qurihara/ai-fue/related_work_survey/NOVELTY_RECHECK.md

# 残った新規性の再点検　絞りすぎていないかを1件ずつ確かめる

2026年8月8日。栗原さんの指摘「サーベイにより残った新規性を絞りすぎているように見える。
論文がいびつになっている」を受けて、縮小をもたらした関連研究を1件ずつ再点検した。

## 結論を先に

**譲歩そのものは、6件中5件が正しい。撤回すべき譲歩は無い。**
一次資料に当たった判断はどれも妥当であり、ここを取り戻そうとすると論文が嘘になる。

**しかし、絞りすぎは確かに起きている。原因は譲歩の中身ではなく、譲歩の書き方である。**
3つの型に分かれ、**いちばん重いのは事実が古くなっていることである。**

| 型 | 何が起きたか | 重さ |
| --- | --- | --- |
| **1. 事実が古い** | スプール49本・128ビットの復号は2026年8月6日に**実機で通っている**のに、論文は「未実施」「設計上の値」と書き、表1の実証容量を**約13.8ビット**のままにしている | **最大** |
| **2. 自己反駁の持ち込み** | サーベイが自分の誤りを正した文を、そのまま論文の地の文にした。論文が主張していないことを論文自身が否定している | 大 |
| **3. 圧縮で生き残った主張だけが落ちた** | 投稿版を6ページに削る過程で、未反証の差分が3つ消え、自己反駁は太字で残った | 大 |

型2と型3が重なった結果、**投稿版は「我々は劣っている」とは書くが「ここは誰も埋めていない」
とは書かない文書になっている。** これが栗原さんの感じたいびつさの正体である。

---

## 第1部　縮小をもたらした関連研究を1件ずつ

### 1. AirCode / InfraredTags　（隠しながら読めること）

**元の主張**　隠蔽と可読性の両立は光学符号には原理的に得られない。

**一次資料の事実**　AirCodeは表面下1〜3mmの空気ポケット、InfraredTagsは厚さ1.08〜1.32mmの
殻の内側に符号を埋め、**どちらも外部に開口をいっさい持たない。** InfraredTagsは単一フレーム
から6〜14ミリ秒で復号し、最大250cmから読める。

**譲歩は正しいか　正しい。** 原理的不可能性の主張は成立しない。外部への露出という点では
窓と吸込口を要する本手法のほうが多く、読み出しの速さでも負ける。

**改めるべき主張**　「外観に符号が現れない」ではなく
**「符号の担い手が形状であるため、担体の材料と色を選ばない」。**
AirCodeは均質で半透明な材料を要求し、論文自身が熱溶解積層方式では均質にならず不透明な
塗装では失敗すると認めている。InfraredTagsは特定の黒い赤外透過フィラメントで**物体全体**を
印刷することを要求し、他の色は今後の課題、スプールごとの再較正まで勧めている。
**これは反証されない、はっきりした差である。**

**いま論文はどうなっているか　ここが型2の典型である。** 投稿版は
「**隠しながら読めること自体は既に実現されている**」を太字で書き、続けて
「外部への露出という点では本手法のほうが多い」と自分を下げている。
ところが**論文は原理的不可能性をどこにも主張していない。** 主張していないことを
否定するために、6ページのうちの数行を使っている。しかも交換で得られるはずの
「任意の家庭用フィラメントで作れる」は投稿版から**落ちている**（長尺版には有る）。

---

### 2. Smith と Senturia（1995）　（基準体による共通モード除去）

**元の主張**　既知の基準体を同居させて比で読む構成に前例がない。

**一次資料の事実**　検出用と基準用の2つの共鳴器を置いて比を取る構成を、
自分たちの新規性としてではなく前提となる **"conventional sensing setup"** として
記述している。2014年に表面弾性波共鳴器での実装例、2021年と2022年の総説でも既知の手法。

**譲歩は正しいか　正しい。** 一般的な形で「前例がない」とは書けない。

**改めるべき主張**　サーベイ自身が「否定されなかった点」を3つ挙げている。そのうち
**論文がまだ使っていないものが1つある。**
基準笛は**読み手に絶対音感を要求せず、復号に使う楽器が特定の調律である必要もなくす。**
センサの文献に対応物は無い（センサを耳で読む人間はいない）。
すなわち残る差分は「比を取ること」ではなく、**比を取ることが人間の読み出しを成立させる**
という一点である。

**いま論文はどうなっているか**　貢献の第三として「構成を受動的な共鳴管と離散符号の復号へ
移した」とだけ書いている。**移植は貢献として弱い。** 上の言い方に替えると、
第2と第3の経路（楽器・コーム）の存在理由と直結する。

---

### 3. DNA-of-things（Koch ら 2020）　（容量と日用品への偽装）

**一次資料の事実**　老眼鏡のアクリルレンズに1.4MB（約1120万ビット）を電源も電子部品も
なしに埋め、**著者自身が抄録で "to hide data in everyday objects (steganography)" と
書いている。**

**譲歩は正しいか　正しい。しかもこれが最も重い。** 容量という土俵では主張は残らない。

**改めるべき主張**　読み出しの経済がまったく違う。DNA-of-thingsの読み出しは
**物体から小片を切り出す破壊的な操作**を要し、次世代シーケンサと分子生物学の工程を要し、
一度読めばその部分は失われる。したがって
**「開けずに、専門の設備なしで、持ち主自身がその場で、繰り返し読み出せる」という条件を
保ったまま到達できる容量の上限**という形なら、どの反例とも矛盾しない。

**いま論文はどうなっているか　型3である。** この枠は長尺版にはあるが、
**投稿版からは完全に落ちている。** 落ちた結果、表1で本研究は
「容量が小さい方式」としてだけ並ぶことになった。

---

### 4. Whoosh の FluteCase（2016）　（半音格子の受動多管構造）

**一次資料の事実**　管長を $L = 14.956 \times 2^{i/12}$ と定め、
「8本の管は8つの異なる周波数で共鳴するよう設計されており、これにより特定の領域への
吹奏を見分けられる」と同じ節に書いている。**semitone という語は無いが、概念はある。**

**譲歩は正しいか　正しい。** 「半音格子で受動的な多管構造を作る」こと自体は先行例がある。

**改めるべき主張**　残るのは格子そのものではなく**格子の使い方**である。
第一に**情報の向き**。Whooshの管長は論文中の公開定数で、すべての複製が同一形状である。
情報は形状ではなく「どの穴を吹いたか」という利用者の選択に載る。
CipherFluteは格子上のどの位置に管を置くかが個体ごとに違い、**その違いが値である。**
第二に**読み方**。FluteCaseはメル周波数ケプストラム係数とサポートベクターマシンによる
利用者ごとの指紋照合であって音の高さを推定せず、**事前に知らない管長は読めない。**
CipherFluteは絶対的な音高を推定して格子上に量子化するので、**事前に知らない値を読める。**

**いま論文はどうなっているか**　2章で差分としては書けている。**ただし貢献には入っていない。**
「事前に知らない値を読める」は未反証の差分であり、貢献に上げてよい。

---

### 5. Lamello / Acoustic Barcodes　（離散周波数を字母とする符号化）

**一次資料の事実**　Lamelloは離散した基本周波数の集合をド・ブラン列の字母として扱う。
ただし格子は等差であり（本文が "linearly increasing tine lengths"、隣接間隔は306.6〜549.5
セントへ単調に広がる）、考察で「最適な周波数の配り方は今後の課題」と明言している。
Acoustic Barcodesは誤り訂正を実装しているが、実効データ量は12ビットにとどまる。

**譲歩は正しいか　正しい。** 記号の列を符号語として扱う設計自体には先行例がある。

**改めるべき主張**　Lamelloのド・ブラン列は**位置と向きを決めるためのもの**であって、
外部から与えた値を運ぶものではない。したがって
**「受動的な音響タグに、外部から与えた任意の値を、誤り訂正符号語として載せた例は、
今回調べた範囲では見当たらない」**は残る。

**いま論文はどうなっているか　型3である。** 長尺版の2.2節末尾にはあるが、
**投稿版からは落ちている。** 表1に「誤り訂正」の欄があるのに、本文がその欄の意味を
語らない状態になっている。

---

### 6. codex32　（機械を要しない復号）

**一次資料の事実**　GF(32)上のBCH符号と、対照表と紙の回転円板により、
Shamirの秘密分散の分割と復元を人手で実行できる。**復号に電子機器をいっさい要しない。**

**譲歩は正しいか　正しい。** 「機械が要らない」の徹底度では本研究より上である。

**改めるべき主張**　codex32の担体は**印刷された文字列**であり、日用品への偽装を扱わない。
2軸で置くと空白が見える。

| | 日用品に偽装できる | 符号として見えている |
| --- | --- | --- |
| **機械なしで人が読める** | **CipherFlute（空白）** | codex32、視覚暗号、SeedQRの手読み |
| **機械が必須** | AirCode、InfraredTags、DNA-of-things、Acoustic Barcodes | — |

**いま論文はどうなっているか**　貢献の第一として書けている。**ここは絞りすぎていない。**

---

## 第2部　いちばん重い問題　事実が古い

**論文はこう書いている。**

> 49本を通した復号は未実施であり，表1の128bitは設計上の値である。

**しかし2026年8月6日に、スプール49本・128ビットの復号は実機の録音から通っている。**
cosenseの記録によれば、5通りすべてで `CipherFlute-demo`（16バイト＝128ビット）が復元できた。

- 連結版　訂正0・消失0（設計49本と全一致）
- 2本ずつの組み合わせ4通り　うち2通りは訂正0・消失0、2通りは**1本が鳴らずパリティが訂正**

**したがって表1の実証容量「約13.8ビット」は、いま事実ではない。** 128ビットである。
この1つの数字が、codex32の128ビットやAirCodeの約500ビットと並ぶ表の中で、
本研究を9分の1に見せている。**査読者がまず比べるのはこの列である。**

画像タイルの2-of-9も実機で復号が通っている。

**これは修辞の問題ではなく、原稿が実測に追いついていないという事実の問題である。**
絞りすぎの最大の要因はここにある。

---

## 第3部　復活させるべき主張

未反証でありながら、投稿版に無いか、貢献に上がっていないもの。

1. **符号の担い手が形状なので、担体の材料と色を選ばない。**
   任意の家庭用フィラメントで作れる。AirCodeとInfraredTagsは材料を強く縛る。（投稿版から落ちている）
2. **「開けずに、専門の設備なしで、持ち主自身がその場で、繰り返し読み出せる」条件下での
   容量の上限を押し上げた。**（投稿版から落ちている）
3. **受動的な音響タグに、外部から与えた任意の値を誤り訂正符号語として載せた。**（投稿版から落ちている）
4. **事前に知らない値を読める。**（2章にはあるが貢献に無い）
5. **基準笛により、読み手に絶対音感も、楽器の特定の調律も要らない。**（3.3節にはあるが貢献に無い）

## 第4部　削るべき自己反駁

論文が主張していないことを否定している文。**削っても正直さは1ミリも減らない。**

- 「隠しながら読めること自体は既に実現されている」（太字）
- 「したがって光学的な符号は表面に露出していなければ読めないという主張は成り立たず、
  読み出しの速さでも本手法が優位に立つわけではない」
- 「外部への露出という点では、窓と吸込口を必要とする本手法のほうがむしろ多い」

**関連研究の節は、先行研究が何をしたかと、本研究がどこで違うかを書く場所である。**
自分が過去に考えて捨てた主張の墓碑を建てる場所ではない。

## 第5部　提案する貢献の並び

現状の4点を、未反証の差分だけで組み直す。

1. **読み出しに機械を要しない秘密の記録媒体。** 日用品に偽装できて、なお鍵盤楽器ひとつ、
   あるいは3Dプリントしたコーム1本で人間が読める。この2つを同時に満たすものは
   今回調べた範囲で見当たらなかった。（codex32は後者だけ、AirCodeらは前者だけ）
2. **事前に知らない値を、音の高さの格子から読む。** 先行する多管構造（FluteCase）は
   管長が公開定数で全複製が同一形状であり、情報は形状ではなく利用者の選択に載る。
3. **担体の材料と色を選ばない。** 符号の担い手が形状だからである。
4. **受動的な音響タグに誤り訂正符号語を載せ、実機で128ビットの往復を通した。**
5. どの層が秘密を守り、どの層は守らないのかを明示した。

**5番目は、栗原さんの別の指摘（脅威モデルという枠組みが要るのか）と関わる。**
「脅威モデルを提唱する」のではなく「この性質があるのでこう使えるが、この脅威は
想定しない」と6章で述べる形にすれば、貢献の1つではなく**限界の記述**になる。
そのほうが自然であり、章も1つ減る。

---

# 決定事項（2026年8月9日、栗原さんと1件ずつ確認して確定）

## 確定した貢献は4件

1. **日用品に偽装できて、なお機械を要さず人が読める。** 基準笛により、読み手に絶対音感も、
   復号に使う楽器が特定の調律であることも要らない。codex32は後者だけ、AirCodeらは前者だけ。
2. **事前に知らない値を、音の高さの推定と格子への量子化で読む。**
   FluteCase・Lamello・Blowhole・SoundOffは、いずれも識別先の集合が復号器に既知である。
3. **担体の材料と色を選ばない。** これは工作の都合ではなく**隠し先の自由**である。
   光学方式は担体を「均質で半透明な材料」または「特定の黒い赤外透過フィラメントで
   全体を印刷したもの」に限定するので、木の本立てにも白い枡箱にも仕込めない。
4. **受動音響タグで実効12bitの系譜を超え、実機で128bitを通した。**

**移植の主張も、立場の主張も、原理的不可能性の主張も、1つも残っていない。
すべて実物か一次資料で判定できる能力の主張である。**

## 件ごとの決定

| 件 | 決定 |
| --- | --- |
| 1 AirCode/InfraredTags（可読性） | (2)の軸では差を主張しない。2章の自己反駁の1文を削除する。**1章の文はスコープが限定されていて真なので直さない** |
| 1-b 同（発見のしにくさ） | 「担体の材料と色を選ばずに隠せる」＝隠し先の自由 |
| 1-c 同（読み出しの軸） | 「近接と、吹くという能動的な行為を要する」を新設。ただし透過撮影では読めるので「読めない」とは書かない |
| 2 同（材料） | 主張は維持し、根拠と結びつけて言い切る |
| 3 Smith と Senturia(1995) | **貢献から外す。**よく知られた手法として引用し、淡々と活用する立場で書く |
| 4 AirCode（既知セルの正規化） | 投稿版では触れない。3を貢献から外したので論じる相手がいなくなる |
| 5 DNA-of-things | 容量では主張しない。「開けずに、専門の設備なしで、持ち主自身がその場で、繰り返し読み出せる条件を保った上限」へ |
| 6・7・8 FluteCase / Lamello | **3件まとめて1つの段落に畳む**（下記） |
| 9 Acoustic Barcodes | 実効12bitの系譜を超え、実機で128bitを通した |
| 10・12・13・14 | 既に正しく書けている。変更なし |

## 6・7・8 の確定文

**議論の経過**　当初「先行研究は入力装置であり、物体の側に取り出すべき情報がない」と
書こうとしたが、**これは誤りである。** 栗原さんの指摘のとおり、Lamelloのド・ブラン列は
設計者が計算して歯の長さとして刻んだものであり、並びを変えれば復号結果が変わる。
**形状に情報が載っている。** FluteCaseも、どの管がどの周波数かという対応は幾何に載る。

**差は「情報が載っているか」ではなく、載っている情報の性質にある。**

| | FluteCase・Lamello | CipherFlute |
| --- | --- | --- |
| 何が載っているか | 位置やコマンドを指す**索引** | 運ぶべき**値そのもの** |
| 誰が決めるか | 部品の設計時、**全複製で同一** | 作るとき、**個体ごとに違う** |
| 復号器は知っているか | 対応を**事前に知っている** | **知らない。測って求める** |

情報量の差（実効2bitと128bit）はこの性質から出る。**索引は場所の数だけあれば足りる。**

**確定した文。**

> FluteCase\cite{whoosh} や Lamello\cite{lamello} のように、受動的な音響部品を吹いたり
> 弾いたりして読む先行研究とは物理機構を共有し、**形状に情報を載せる点も共通する**。
> ただしそこに載っているのは**位置やコマンドを指す索引**であり、部品の設計時に決まって
> 全複製で同一で、**復号器はその対応を事前に知っている**。本研究では**載っているのが
> 運ぶべき値そのもの**であって個体ごとに異なり、**読み取り側は事前にそれを知らない**。
> 音の高さを推定して格子上に量子化するので、知らない値が読める。

**副産物**　格子について何も主張しなくなるので、「半音の格子には先行例がある」という
譲歩の文が丸ごと消える。半音を選んだ理由（平均律の楽器が対照表になる）は3.2節に残る。

## この作業で分かった、書き方の原則

**譲歩を書くのではなく、主張しないことで解決する。** 主張しなければ、先行例を挙げて
反論する必要がなくなり、段落ごと消える。紙面も増える。**論文が自分を弱く見せる文は、
たいてい「主張していないことへの反論」である。**

---

# 議論の経緯（2026年8月9日）

**この節は、結論そのものより価値がある。** 同じ作業を将来もう一度やるとき、
**どこで間違えたか**を知っていることが効くからである。以下は時系列である。

## 進め方

栗原さんの指示は「**関連研究を一つずつ挙げ、我々のこの主張はこの関連研究とこのように
被っているので、このような主張にあらためなければいけない、という書式で**」であった。
そして「**サーベイに対する君の結論を疑っているので、一つずつ私とやっていく**」と続いた。

この2つの指示が効いた。**一括で判断していたら、下の誤り3件はどれも見つからなかった。**

## AIが犯した誤りと、栗原さんによる訂正

### 誤り1　「点検」ではなく「追認」をしていた

最初の報告でAIは「サーベイの譲歩は6件中5件が正しい」と要約した。**これは一次資料に
当たり直した点検ではなく、サーベイの結論をそのまま繰り返しただけであった。**
栗原さんに「一つずつやっていく」と言われて初めて、件ごとの検証が始まった。

### 誤り2　投稿版から落ちた主張の診断が不正確だった

AIは「材料と色を選ばないという主張が投稿版から落ちている」と報告した。実際には
**貢献の第二として残っており**、落ちていたのは「任意の家庭用フィラメントで作れる」という
具体の一句だけであった。正しい診断は「**根拠と切り離されたまま8文字で置かれている**」で
ある。数えれば分かることを、確かめずに報告していた。

### 誤り3　過剰な直しを提案した（自分が診断した病を自分でやった）

AIは「1章の問題設定（日用品に隠そうとすると読めなくなる）を、否定されない形に立て直す」
と提案した。**栗原さんはこれを保留した。** 読み直すと、1章の文は主語が
「紙・金属板・二次元コード」に限定されており、**光学符号一般については何も言っていない。
つまりそのままで真である。** 直すべきは2章の「隠しながら読めること自体は既に実現されて
いる」という1文だけであった。

**AIは「主張していないことへの反論を書くな」と診断しておきながら、提案の側で同じことを
していた。** 過剰な自己修正は、指摘したあとにも再発する。

### 誤り4　事実に反する切り分けを書こうとした（これが最も重い）

FluteCaseとLamelloとの差を、AIは当初こう書こうとした。

> 先行研究は入力装置であり、**物体の側に取り出すべき情報がない**。

**栗原さんの反論。** 「FluteCaseやLamelloは、複数の場所に低情報量のデータが埋め込まれて
おり、それを人間が意識的に選択することでデータを識別可能な音として発生させ、マイクが
拾ってデコードする。**情報が積載されているという点では同じ**ではないか」。

**これは正しい。** とくにLamelloのド・ブラン列は、設計者が計算して歯の長さとして刻んだ
ものであり、並びを変えれば復号結果が変わる。**形状に情報が載っているとしか言いようがない。**

差は「情報が載っているか」ではなく、**載っている情報の性質**にある。

| | FluteCase・Lamello | CipherFlute |
| --- | --- | --- |
| 何が載っているか | 位置やコマンドを指す**索引** | 運ぶべき**値そのもの** |
| 誰が決めるか | 部品の設計時、**全複製で同一** | 作るとき、**個体ごとに違う** |
| 復号器は知っているか | 対応を**事前に知っている** | **知らない。測って求める** |

情報量の差（実効2bitと128bit）はこの性質から出る。**索引は場所の数だけあれば足りる。**

## 栗原さんが持ち込んだ枠組み（サーベイには無かったもの）

### 2つの軸を分ける

> (1) 秘密がある場所を見つけやすいか
> (2) 場所を知っているとき、情報が見えるかどうか

**論文はこの2つを混ぜていた。** 分けると、AirCode/InfraredTagsとの関係が正確に書ける。
AIはここに第3の軸（読み出しに要するもの）を足した。InfraredTagsは**最大250cmから
単一フレームで受動的に読める**のに対し、CipherFluteは吹かなければ鳴らない。

| | (1) 場所の見つけにくさ | (2) 見えるか | (3) 読み出しに要するもの |
| --- | --- | --- | --- |
| 紙・二次元コード・金属板 | 低い（金庫が要り、金庫が秘密を告げる） | 見える | 目 |
| AirCode / InfraredTags | 高い。**ただし担体の材料が縛られる** | 見えない | 専用装置。非接触・遠隔・受動 |
| **CipherFlute** | 高い。**担体の材料も色も自由** | 見えない | **吹く行為と近接。装置は不要** |

### 細かすぎる分割を1文に畳む

AIは格子（6）と読み方（7）と符号化の枠組み（8）を別々に論じようとした。
栗原さんの指示は「**細かすぎる。1文で済ませられる**」であった。畳んだ結果、
**格子について何も主張しなくなり、「半音の格子には先行例がある」という譲歩の文が
段落ごと消えた。**

### 「原理は共通」と書いてはならない

栗原さんの草案には「笛による音響情報に**データを埋め込んで**吹くことによる復号を行う
**原理は共通している**」とあった。AIはここを押し戻した。**FluteCaseはデータを埋め込んで
いない**（管長は公開定数で全複製が同一）。共通しているのは
「受動的な多管構造を吹き、生じた音をマイクで読む」という物理機構までである。
**ここを譲ると、我々だけが持っているものを相手に渡すことになる。**

## この作業で得た原則

**譲歩を書くのではなく、主張しないことで解決する。** 主張しなければ、先行例を挙げて
反論する必要がなくなり、段落ごと消えて紙面も増える。基準笛（3・4）でも、格子（6）でも、
符号化の枠組み（8）でも、同じ解き方が効いた。

**論文が自分を弱く見せている文は、たいてい「主張していないことへの反論」である。**

**そして絞りすぎの最大の要因は、修辞ではなく事実が古いことであった。** スプール49本の
128bit復号は2026年8月6日に実機で通っていたのに、原稿は「未実施」「設計上の値」と書き、
表1の実証容量を約13.8bitのままにしていた。**査読者が最初に比べる列が、9分の1の値で
放置されていた。**
