qurihara/ai-fue/related_work_survey/REVIEW_AND_REPOSITIONING.md

# 外部評価と、研究の位置づけの再検討

2026年7月30日作成。`SURVEY.md` が示した新規性の再定義を外部の評価者（Codex CLI、モデルはgpt-5.6-sol、思考の深さはxhigh）にかけ、その指摘を検証したうえで、研究の位置づけを立て直した記録である。

**この文書は `SURVEY.md` の一部を訂正する。** 食い違いがある場合はこちらが新しい。

## 経緯

`SURVEY.md`、`PAPER_REVISION.md`、`REFERENCES_TO_ADD.md` と論文本体を外部の評価者に読ませ、次の5点を辛口で評価させた。新規性の再定義の妥当性、WISSに通るかどうか、サーベイの見落とし、改訂案の現実性、そして致命的な弱点である。評価者の総合判定は「どちらかといえば不採録」であった。

その指摘のうち、論文の中で検証できるものを栗原さんとClaudeで確かめ、外部の文献に関わるものは別に検証の工程を立てた。

そのうえで、栗原さんの指示により**「実装が追いついていない」「実証が済んでいない」「記載が未熟だ」という種類の指摘をすべて除外し、すべてうまくいったとして研究に価値があるかを問い直した。** その再検討が後半である。

## 第1部　外部評価の検証

### 論文の中で検証できた指摘は、4件すべてが当たっていた

**指摘1　概要が実証していないことを実証したと書いている。**
概要は「実験により温度差に対する頑健さ、および128bit暗号のエンコードとデコードを検証した」と述べる。しかし5.3節の通しの実証は4桁の数「2026」の5本だけである。6.3節のスプールは「先に印刷した24本の側を実測したところ、24本すべてが鳴り」とあるだけで、49本の往復復号は行っていない。

**指摘2　スロット数と本数が3通り混在している。**
概要と3.2節と3.4節が13スロット・約3.7ビット毎本・約40本。3.2節の注記が11スロット。2.3節と5.1節と6章の実装がすべて12スロット・隣接同音禁止・49本である。

**指摘3　基準笛は息の強さには原理的に効かない。**
3.3節は「息の強さの平均的な変化も同様に、全体を同じ向きに動かす」「比を取ると分子と分母で打ち消し合う」と書く。しかし笛を1本ずつ順に吹く方式では、基準笛とデータ笛が同じ息を共有しない。比で消えるのは分子と分母に同時に同じ係数が乗る場合だけである。しかも5.2節が自ら「残る±24セントは、温度そのものよりも2回の測定での息の強さの違いに由来すると見られる」と書いており、論文の中で矛盾している。

**指摘4　PDFは10ページある。** WISS 2026の制限は参考文献と謝辞と未来ビジョンを除いて6ページ以内である。

### サーベイ側の誤りを3件認める

**誤り1　「隠蔽と可読性の両立は光学符号には原理的に得られない」は成立しない。**

AirCodeは表面下の空隙に符号を埋めて外観を変えず、投影と撮影で読む。InfraredTagsは肉眼で見えない内部の二次元コードを近赤外カメラで最大250センチメートルから読む。**どちらも `SURVEY.md` に載っていた。** 個々の文献は正しく拾っていながら、統合の段階でそれが自分の中心命題への反例であることに気づけなかった。文献の見落としではなく論理の見落としである。

検証の結果（`raw3/c1-optical-hidden.md`）も「この反論は正しい。主張Aのうち『光学的な符号は表面に露出していなければ読めない』という前提は、一次資料に当たると成り立たない」と結論した。

**誤り2　「semitone が0件だから半音格子の発想は存在しない」は、単語の不在と概念の不在の混同である。**

Whooshは本文で管長を 2^(i/12) によって定めており、語がなくても概念として半音格子を使っている。**自分の原典確認でそれを見つけておきながら、集計では0件と書いた。**

**誤り3　「網羅的に探して存在しなかった」と書ける根拠がない。**

延べ38のエージェントと3,153回の道具呼び出しは再現率の根拠にならない。同じモデル群が似た検索語を使えば同じ死角を繰り返す。しかもサーベイ自身が2013年以前のWISS、日本音響学会講演論文集、電子情報通信学会技術研究報告、国際特許分類による走査を未実施と認めている。**「今回の検索範囲では確認できなかった」と書き直す必要がある。**

### 外部反例の検証

評価者が新たに持ち出した文献を、こちらで一次資料に当たって確かめている。2件が確定した。

**確定1　基準共鳴器による共通モード除去には明確な先行例がある（`raw3/c3-reference-resonator.md`）。**

判定は「反例は正しい」であった。SmithとSenturia（1995年）は、検出用と基準用の2つの共鳴器を置いて比を取る構成を、自分たちの新規性としてではなく前提となる **"conventional sensing setup"** として明示的に記述している。2014年には表面弾性波共鳴器での実装例があり、2021年と2022年の総説でも既知の手法として扱われている。**この着想を一般的な形で「前例がない」と述べることはできない。**

ただし否定されなかった点が3つある。第一に、CipherFluteの基準素子は電子回路も電源も持たない受動的な共鳴管であり、読み取りは呼気と携帯電話の内蔵マイクだけで行われる。挙げられた反例はいずれも発振回路と周波数カウンタを前提とする。第二に、CipherFluteの基準素子は「センサの環境補償」ではなく「離散符号の復号における基準」として働き、評価指標が測定確度ではなく記号誤り率になる。第三に、造形物への情報埋め込みという文脈での前例の有無は未確定である（参考として、Lamelloの本文には reference、calibration、temperature のいずれの語も出現しない）。

書き換えの案は `raw3/c3-reference-resonator.md` の第5節にある。

**確定2　光学符号の内部埋め込みは本物の反例である（`raw3/c1-optical-hidden.md`）。** 上の誤り1のとおり。

**残る4件も検証が終わり、6件すべてが「反例は正しい」であった。** 詳細は下の「検証の完了報告」の節にある。

### 検証の結果、残った差分の正確な形

「隠蔽と可読性の両立」は、2軸で整理すると空白が見える。

| | 素のスマートフォンだけで読める | 専用の装置が要る |
| --- | --- | --- |
| **外観に符号が出る** | 二次元コード、SeedQR、金属板 | AnisoTag（レーザーと光導電素子16個） |
| **外観に符号が出ない** | **ここが空白** | AirCode（プロジェクタとカメラと偏光板、撮像3から4分）、InfraredTags（近赤外撮像モジュール、20ドル、132グラム） |

**反例が示したのは右下のマスであって左下ではない。** CipherFluteは左下に入る唯一の方式である。主張は「原理的に不可能」から「**追加の装置なしに読める**」へ弱める。これは原理ではなく設計上の取引である。

## 検証の完了報告　6件すべてが「反例は正しい」であった

生の記録は `raw3/c1` から `raw3/c6` にある。第2部の再検討は、この結果を踏まえて後半で更新してある。

### c1　光学符号の内部埋め込み（既述のとおり反例は正しい）

追加で判明したことが4つある。**いずれも第2部の議論を変える。**

第一に、**AirCodeとInfraredTagsは外部に開口をいっさい持たない。** AirCodeは表面下1ミリメートルから3ミリメートルの空気ポケット、InfraredTagsは厚さ1.08ミリメートルから1.32ミリメートルの殻の内側である。どちらも人間のコントラスト感度閾値5パーセント以内に収まるよう寸法を設計している。**外観の露出という点ではCipherFluteのほうが多い**（窓と吸込口が要る）。「外部に必要なのは窓と吸込口という小さな開口だけである」という言い方は優位性の主張にならない。

第二に、**読み出しの速さでCipherFluteは優位ではない。** AirCodeは撮像に3分から4分かかるが、InfraredTagsは単一のフレームから4×4のマーカーで平均6ミリ秒、21×21の二次元コードで平均14ミリ秒で復号し、最大250センチメートル離れて読める。「光学方式は読み出しが遅い」という一般化は成立しない。

第三に、**AirCodeには弱い形の自己補正の前例がある。** 符号格子の中に既知の値のセル（青は常に1、オレンジは常に0）を散らし、それで復号器をその場で訓練し、特徴ベクトルを局所的な明るさの変化に合わせて正規化している。補正する物理量も演算も違うが、**同一の物体に既知の基準を同居させて変動を吸収するという構造そのものには前例がある。**

第四に、**これが最も重要な発見である。両方式は担体の材料を強く縛る。** AirCodeは均質で半透明な材料を要求し、論文自身が「多くの熱溶解積層方式のプリンタは太いフィラメントを積むので造形物が均質にならない」「完全に不透明な塗装では失敗する」と限界を認めている。造形はPolyJet方式である。InfraredTagsは特定の赤外透過フィラメント（黒）で物体全体を印刷することを要求し、他の色は今後の課題だと書き、フィラメントのスプールごとの再較正まで勧めている。

**CipherFluteは符号の担い手が形状なので、担体の光学的性質にまったく依存せず、任意の家庭用フィラメントで作れる。** 主張は「外観に符号が現れない」ではなく「**符号の担い手が形状であるため、担体の材料と色を選ばない**」と書き換えるべきである。こちらのほうが強く、かつ反証されない。

なお、**関連研究にInfraredTagsを追加すべきである。** 現行稿はAirCodeとInfraStructsしか挙げていないが、「安価な装置で速く読める隠された光学符号」という最も強い比較対象を挙げずに光学方式の限界を論じると、査読で必ず指摘される。

### c2　熱と視点で切り替わる光学符号（反例は正しい）

InfoPrintは実在する。予稿は arXiv:2112.00189、出版版は Proceedings of the ACM on Interactive, Mobile, Wearable and Ubiquitous Technologies 第7巻第3号、1ページから29ページ、2023年、DOI 10.1145/3610933 である。抄録が「目に見えない情報を三次元印刷物の内部に埋める」と明言している。**家庭用の熱溶解積層方式で、表面から1ミリメートルから3ミリメートルの内部に情報を埋め、利用者が手で温めるという能動的な操作を経て熱画像で読む。** つまり「隠れているが、利用者が操作すれば機械可読になる」という構図に、光学の側の直接の先例がある。

EckerとPretschの第二の設計は、黒い熱変色顔料の封止層の下に隠れた二次元コードが44度から62度の範囲で**普通のスマートフォンで読めるようになる**ものである。隠れている状態は「読めない」だけではなく「見えない」水準である。阪口らの手法も実在し、回転角度と赤外の波長の両方で表示情報を切り替える。Dual Modulated QR Codesは近接での秘匿を明示的に設計している。

### c3　基準共鳴器（既述のとおり反例は正しい）

### c4　DNAを混ぜた造形物（反例は正しい。これが最も重い）

Koch, J., Gantenbein, S., Masania, K., Stark, W. J., Erlich, Y. and Grass, R. N.: A DNA-of-things storage architecture to create materials with embedded memory, Nature Biotechnology, 第38巻第1号, pp. 39–43 (2020年1月号、オンライン先行公開は2019年12月9日). DOI 10.1038/s41587-019-0356-z.

**老眼鏡のアクリルレンズに1.4メガバイト（約1120万ビット）の動画を、電源も電子部品もなしに埋め込んでいる。** スタンフォードバニーには自身の設計図45キロバイトが入っている。数字はいずれも抄録に原文で書かれている。

そして**著者自身が抄録で "to hide data in everyday objects (steganography)" と書いている。** 図3の見出しは「A video is concealed in reading glasses.」である。チューリッヒ工科大学の公式発表では、Erlichが「このような眼鏡なら空港の保安検査を問題なく通せるので、情報を気づかれずに運べる」と述べている。

**したがって「100ビットを超える秘密の値を電源なしの物体に埋め、日用品に偽装した先行研究は存在しない」という主張は成り立たない。** 容量という土俵ではCipherFluteに主張は残らない。

ただし読み出しの経済がまったく違う。DNA-of-thingsの読み出しは、**物体から小片を切り出す破壊的な操作**を要し、次世代シーケンサ（イルミナ社のiSeq 100）と分子生物学の一連の工程を要し、書き込みだけで1件あたり約2000スイスフランかかり、**一度読めばその部分は失われる。**

**この対比から、空白の位置が変わる。既存の空白は「容量」ではなく「読み出しの敷居」の側にある。** CipherFluteは、受動音響タグの系譜（誤り訂正後で12ビットが上限）と、DNA-of-thingsの系譜（容量は桁違いだが読み出しの敷居が高い）のあいだの位置を占めている。**「開けずに、専門の設備なしで、持ち主自身がその場で、繰り返し機械可読に読み出せる」という一点**が、どちらの系譜にもない。

Hollow Nickel事件もアメリカ連邦捜査局の公式記録で確認できた。**ただし評価者の記述に不正確な点がある。** 中空硬貨の中身はマイクロフィルムではなく microphotograph（微小写真）である。マイクロフィルムが出てくるのはHayhanen宅の中空の鋼片と中空の懐中電灯用電池という別の物件である。また刑期について連邦捜査局の2つの公式ページが食い違っており、引用するなら内訳を書いているFamous Casesのページを採るべきである。

### c5　半音格子の概念（反例は正しい）

**Whooshは、管長の式 L = 14.956 × 2^(i/12) と、「8本の管は8つの異なる周波数で共鳴するよう設計されており、これにより時計面の特定の領域の近くへの吹奏を容易に見分けられる」という文を、同じ節に並べて書いている。** すなわち「公比が平均律の半音比である等比数列で共鳴管を並べること」と「その離散周波数の集合を識別の語彙として使うこと」の両方が、semitone という語を使わずに2016年の一次資料に書かれている。

Lamelloは "unique f0s to differentiate"、"a de Bruijn sequence D(k, n) ... given an alphabet size k" と書き、**離散した基本周波数の集合を字母として列で符号化している。** ただし格子は等比ではなく等差である（本文が "linearly increasing tine lengths" と明記し、報告された7本の周波数から隣接の間隔は306.6セントから549.5セントへ単調に広がる）。しかもLamelloは考察の節で「最適な周波数の配り方は今後の課題である」と明言している。

ほかにGoogleの特許（US9755764B2、US9882658B2、Communicating data with audible harmonies）が「Cのペンタトニック長音階を用いる」と記号写像を指定しており、中沢誠さんと山崎芳男さんの「1/12Nオクターブ分析を用いた音の符号化」（早稲田大学、2003年）が12音平均律に基づく対数等間隔の分割を符号化の格子とし、分割数を設計変数として扱っている。

**残るのは格子そのものではなく格子の使い方である。** 第一に情報の向き（Whooshの管長は公開された定数で全複製が同一形状、Lamelloの歯の長さも部品の設計に固定。CipherFluteは格子上のどの位置に管を置くかが個体ごとに違い、その違いが値である）。第二に読み方（Whooshは基本周波数を推定せず未知の管長を読めない。Lamelloの照合先は部品ごとの既知の周波数表であって格子ではない。CipherFluteは絶対的な音高を推定して格子上に量子化するので事前に知らない値を読める）。第三に刻みを何から決めたか（Lamelloは今後の課題として残し、中沢さんらは聴覚特性と符号量から決めており、造形誤差や吹奏の揺らぎからではない）。第四に符号列としての扱い（多ビットの容量、符号語への連結、誤り訂正の付与という組み立ては先行例のいずれにもない）。

**論文ではWhooshを「半音比の等比数列で受動的な多管構造を作った先行例」として、Lamelloを「離散周波数の集合を字母として列で符号化した先行例」として明示的に引くべきである。**

### c6　暗号的な健全性（指摘は技術的には正しいが、重大さの評価を誤っていた）

> **【重要な訂正】** 以下の3つの指摘は、**コードの記述としてはすべて正しい。** しかし**重大さの評価が誤っていた。** 指摘1と2はいずれも、公開しているデモページで既に明示されている設計上の割り切りか、用途に対して十分な強度であって、**実装の修正を要しない。** 詳細は下の「実装は変えなくてよい」の節にある。以下は技術的な事実の記録として残す。

**指摘1は正しく、しかも実装がさらに悪い。** 読み出しアプリ `docs/cipher/index.html` は、照合用のSHA-256を **`?sha256=` というURLのクエリ文字列から自動入力する設計**であり、検証値の公開を前提としている。4桁の秘密の候補は1万から2.9万通りにとどまるため、公開のSHA-256は秘密の公開と等価である。塩も反復もない素のSHA-256である。

**指摘2も正しく、実装がさらに悪い。** `fue/make_goto_enc.py` の鍵導出は素のSHA-256を1回かけるだけで、塩も反復回数も存在しない。NIST SP 800-133 Rev.2 の6.2.3節が「秘密から作った鍵の安全性は秘密のエントロピーを超えない」と明示しており、NIST SP 800-38D のGCM復号手順は認証タグが合わなければ失敗を返すので、**暗号文そのものが鍵候補の判定器として働き、1,771,561通りを完全にオフラインで尽くせる。** NIST SP 800-132 の付録A.2.2 が「反復回数はエントロピーを増やさず、費用を定数倍するだけである」と述べている。

**指摘3も正しい。しかも実務上の影響が大きい。** SLIP-0039の仕様表は128ビットの主秘密に対して断片1本を **200ビット（20語）** と定めている。内訳は前置き40ビット、断片値128ビット、詰め物2ビット、検査符号30ビットで、正味は168ビットである。SSKRも5バイトと16バイトで168ビットになり一致する。**論文の表5が書く「断片は各148 bit」はどの数え方とも一致しない。** その20ビット分を落とすとメンバー番号が失われ、ラグランジュ補間ができなくなる。

**論文自身の符号化器（`fue/cipher_codec.py`、12スロット・隣接同音禁止・ブロックあたり検査2記号）で計算すると、168ビットは笛64本、200ビットは笛75本になる。64本は6.4節の上限（円盤1枚あたり26本）で2枚に収まらず、円盤が3枚必要である。**

ただし6.4節の本文「12単語のシード相当の128 bit」自体は正しい（BIP-0039の12語はエントロピー128ビットである）。**誤っているのは表5の数字と、容量を終始128ビットで語ることで断片も同じ本数に収まると読ませてしまう構成のほうである。**

**この3件は、新規性の主張そのものは損なわない。** 物体の幾何と読み取りの物理に関する主張は、秘密の値の強さとは別の層にある。損なわれるのは次の3点で、いずれも書き方の修正で回復できる。第一に「復元した値の正しさは公開の検証値との照合で誰でも確かめられる」という汎用の主張は112ビット以上の秘密に限定する。第二に「2枚がそろったときにだけそのページが開く」という秘匿の主張には20.8ビットの強度しかないと明記する（2-of-2の分散が情報理論的に健全であることは変わらない）。第三に容量の主張を、生のシードは49本、秘密分散の断片は64本と書き分ける。

**むしろ、脅威モデルの表に「秘密のエントロピーが小さいときに何が守れなくなるか」という行を足せば、論文の売りである誠実さは一段強くなる。**

### Whoosh の付随動画を確認した　残っていた懸念は消えた

2026年7月30日、栗原さんがACM Digital Libraryから付随資料（`p120-reyes.zip`）を取得された。中身は203秒の動画1本である。4秒ごとのコンタクトシートにして全編を通しで確認した。**結論として、動画は本文を超えておらず、本文の分析がそのまま裏づけられた。**

認証の場面は実在する。字幕は「Unique sequence of Whoosh events unlocks the watch」であり、Watch Locked の状態から「Short blow」「Long blow」「Short blow」の順に吹くと Watch Unlocked になる。**ただしこれは無改造の腕時計での実演であり、FluteCaseは装着されていない。** そして鍵になっているのは**吹く長さの列**であって、音の高さではない。

FluteCaseが登場するのは別の区間で、字幕は「Demos with FluteCase」、内容は地図（時計回りに吹いて拡大、反時計回りに縮小）とアプリの近道の2つだけである。**FluteCaseを使った認証の実演は存在しない。**

すなわち、本文で確認した「認証の記述は無改造の時計の節にあり、8本の管とは無関係である」という読みが動画でも確認された。**この件は完全に解決したので、Whooshとの差分は安心して書ける。**

### 実装は変えなくてよい。直すのは論文の文章だけである

> **【更新】** 当初この3点を「実装の欠陥」として挙げたが、栗原さんの指摘により、**いずれも実装の修正を要しない**ことが分かった。印刷済みのものも1つも無駄にならず、笛を増やす必要もない。

**1. 検証値をURLのクエリ文字列で渡していること。実装の対応は不要である。**

公開しているデコードページには、既にこの弱点を明記した但し書きがある。原文は「照合用の値や遷移先といった設定を、URLに載せて渡しています。そのためURLを手に入れた人は、笛を持っていなくても、手元で秘密の候補を片端から試せます。暗証番号のような小さい秘密であれば、これだけで破られます」である。

**検証を担当したエージェントはコードだけを読み、この但し書きを読んでいなかった。** 既知の、意図された、明示された設計上の割り切りを、脆弱性として報告していたことになる。デモとして「URL一つでさまざまな状況を試せる」ことが目的なら、設定をURLに載せるのは正しい設計である。

**残るのは論文だけである。** 3.5節が「公開鍵をあらかじめ紙や物体、公開の台帳に控えておけば、復元した値から計算し直して一致を見るだけで、正しく復元できたかを誰でも確かめられる」と、用途を限定せずに書いている。**デモページが既に持っている正直さを論文にも持たせ、「秘密のエントロピーが小さい場合、検証値の公開は秘密の公開に近い」と1文添えれば足りる。**

**2. 素のSHA-256による鍵導出。実装の対応は不要である。**

カードが運ぶのは暗証番号や合言葉の水準の秘密であり、20.8bitで足りる用途に20.8bitを使っているにすぎない。**強度不足ではない。**

**残るのは論文だけである。** 6.5節の「2枚がそろったときにだけそのページが開く」「URLを手に入れただけの者には行き先が分からない」という書き方が実際より強く聞こえるので、強度を数字で添える。むしろ論文の売りである誠実さと一致する。

**3. 秘密分散の断片の長さ。案Bを採る（2026年7月30日決定）。印刷済みの円盤2枚はそのまま生きる。**

事実の整理から始める。Shamirの秘密分散では、**128bitの秘密を分けても断片の値は128bitのままである。** SLIP-39が200bit（20語、1語10bitの1024語リスト）になるのは、断片の値に付加情報を巻きつけているからである。内訳は、識別子15、拡張フラグ1、反復指数4、グループ番号4、グループ閾値4、グループ総数4、メンバー番号4、メンバー閾値4の計40bitの前置きと、断片の値128bit、詰め物2bit、検査符号30bit（RS1024、GF(1024)上のReed–Solomon）である。**この72bitは、紙に書いた20語を何の説明もなしに他人へ渡しても意味が通じるようにするための費用である。**

このうち数学的に落とせないのは**メンバー番号の4bitだけ**である。復元は点$(x_i, y_i)$からの補間であり、$x_i$を失うと計算が成立しない。識別子も検査符号も、CipherFluteでは不要である（検査符号はReed–Solomonの検査記号と重複する）。

**案Bを採る決め手は「機械が要らない」という主張との整合である。** SLIP-39はマスターシークレットを分割の前に4ラウンドのFeistelネットワーク（ラウンド関数はPBKDF2-HMAC-SHA256）で暗号化する。**準拠した瞬間に、復号へ計算機が必須になる。** Shamirの補間自体は対照表を用意すれば手でもできる（codex32が実際にやっている）が、この暗号化の層は手計算では回せない。

もう1つの材料がある。**既に2-of-3を3つの違う日用品（本立て、スプール、箱）に分けているため、「どの物体が何番目の断片か」を物体自身が語る。** 案Bの弱点である「番号の知識が要る」は実質的にほぼ消えており、残る知識は「排他的論理和で足す」という一点だけである。

**論文にはこう書く（栗原さん承認済みの文面）。**

> 秘密分散の断片を運ぶ場合、業界標準のSLIP-39に準拠すれば、断片1つが200bitとなり笛64本を要するが、標準の道具で復元でき、紙や金属板に保管した断片と混在できる。一方、物体の同一性がメンバー番号を担うことを利用して付加情報を省けば、断片の値128bitのみで足り笛49本に収まるが、復元には本手法の知識が必要になる。相互運用性と符号量のどちらを取るかは、運用の設計変数である。

そのうえで**実装したのは後者である**と明記する。表5の「断片は各148 bit」という数字は誤りなので、上の記述に置き換える。

**なお、SLIP-39には関連研究として触れる価値のある設計がもう1つある。** パスフレーズが正しいかを検証する方法を**意図的に持たない**ため、違うパスフレーズからは違う、しかし一見正当なシードが得られる。これは強要されたときに囮のパスフレーズを渡せるという、**もみ消し可能性（否認可能性）のための設計**である。CipherFluteが物理層の偽装で狙っているものを、**データ層で実現した既存の標準**にあたるので、脅威モデルか関連研究で1文触れておくとよい。

栗原さんの指示により、実装と実証と体裁に関する指摘をすべて除外して問い直す。49本の128ビット往復が通り、偽装の探索実験が期待どおりの結果を出し、記載の不整合が直り、6ページに収まったとする。

### 結論を先に

**価値はある。ただし論文がいま主張している場所にはない。**

現状の論文は「暗号資産のリカバリーシードの物理バックアップ」として自分を売っている。この土俵では、仮定を最善にしても勝てない。容量ではCompactSeedQR（128ビットが70ミリメートル角1枚）に負け、電源不要の徹底度ではcodex32（紙と鉛筆だけで復号でき、計算機すら不要）に負け、耐火性では金属板（29ユーロで市販、耐火試験済み）に負け、読み出し速度ではカメラ1回に対して26本で13.8秒と負ける。**これらは実装の未熟さではなく物理と経済の差なので、仮定では消えない。**

### 価値の軸を4つで評価する

**軸A　読み出しに機械が要らないこと。生き残る。ただし当初の理解は2回書き換わった。**

> **【1回目の更新】** 当初は「外観に符号が出ないこと」を軸Aの中身だと考えていたが、これは弱い。AirCodeとInfraredTagsは**外部の開口がゼロ**であり、外観の露出という点ではCipherFluteのほうが多い。読み出しの速さでも負ける（InfraredTagsは単一フレームから6ミリ秒から14ミリ秒）。
>
> **【2回目の更新。栗原さんの指摘による。これが最も重要である】** 「素のスマートフォンだけで読める」という置き方も、まだ弱かった。この置き方だとcodex32（紙と鉛筆だけで復号でき、計算機すら不要）に負ける。**しかしCipherFluteも機械を必要としない。笛の音階列を聞き取れば、人間の身体だけで情報を取り出せる。** 軸Aの中身はここに置くべきである。

**A-1　特別な装置を持たない人が、そのへんにある楽器ひとつで復号できること。これが最も強い。**

> **【3回目の更新。栗原さんの指摘による】** 当初これを「基準笛があるので相対音程を数えれば読める」と書いた。**これは訓練を要求するので弱い。** 正しくはこうである。「全然わからない人でも、何か手元に楽器があれば同じ音かどうかで識別できる」。

音程を推定することと、2つの音が同じ高さかどうかを判定することは、認知的にまったく別である。前者は訓練された技能だが、**後者はほぼ誰にでもできる。** ずれていればうなりが聞こえ、合えば消える。ギターの調弦と同じ原理である。しかも精度が高い。2キロヘルツ帯で1セントは約1.2ヘルツなので、うなりが数ヘルツで聞き取れれば数セントの精度が出る。**スロット幅100セントに対して桁違いに細かい。**

復号の手順はこうなる。基準笛を吹き、鍵盤の上で一致する鍵を探す。各データ笛も同じようにする。**あとは鍵をいくつ隔てているかを数える。** これは音楽の技能ではなく計数である。

**ここから、半音刻みにした本当の理由が出てくる。**

現行の論文は3.2節で、半音にした理由を「音楽的な意味が付与され、エンタテインメント価値を付与できる」と書き、続けて「音感に優れた人により認識・記憶されやすいという欠点にもなる」と打ち消している。**どちらも誤りである。** 正しい理由は次のとおりである。

> **半音刻みにしたのは、世の中に既にある鍵盤楽器がそのまま対照表になるからである。**

ピアノが復号表なのである。平均律の楽器であれば何でもよく、しかも基準笛があるので**A=440ヘルツに合っている必要すらない。** これが基準笛の3つ目の役割である。

**外部の楽器すら要らない道もある。** 較正用のコーム（12音を各3本、計36本）は既に印刷されており、**それ自体が物理的な対照表である。** データの笛を吹き、コームの笛を順に吹いて同じ音になるものを探せば記号が読める。**電子機器がどこにも登場せず、3Dプリントした物体だけで書き込みから読み出しまで閉じる。**

この性質を2軸で置くと、埋まっていない位置が見える。

| | 日用品に偽装できる | 符号として見えている |
| --- | --- | --- |
| **機械なしで人が読める** | **CipherFlute（ここが空白）** | codex32、視覚暗号、大川さんと栃窪さんの方式、SeedQRの手読み |
| **機械が必須** | AirCode、InfraredTags、DNA-of-things、Acoustic Barcodes、Blowhole、Lamello | — |

**「偽装されていて、かつ機械なしで人が読める」を埋めているものは、今回調べた範囲で1件もない。**

**この性質が効く理由が4つある。**

第一に、**機器の陳腐化に対する耐性である。** リカバリーシードは10年20年の話である。応用ソフトウェア、基本ソフトウェアの仕様、特定のカメラに依存する形式は、その期間で壊れる。半音という語彙は数百年もっている。これはcodex32が紙と鉛筆にこだわる理由とまったく同じ論法であり、その論法をCipherFluteも使える。

第二に、**災害と機器の喪失である。** リカバリーシードを使う場面そのものが「全部失った」状況である。スマートフォンが手元にないとき、SeedQRもInfraredTagsもDNA-of-thingsも読めない。

第三に、**立会人が独立に検証できることである。** 複数の人が同じ旋律を聞いて、それぞれ書き取れる。光学タグは1台の機械が読み、他の人はそれを信じるしかない。**論文の「儀式として実行できる」という主張が、修辞から実体になる。**

第四に、**段階的な冗長性である。** 機械の経路は速くて誤り訂正つき、人の経路は遅いが何も要らない。同じ物体が両方を担う。

**成立の条件を正直に書く。** カジュアルプロファイル（誤り訂正なし）なら、聞いて書き下すだけで完結する。**これは既に実装済みであり、今日から主張できる。** 誤り訂正つきの場合は、手でGF(13)またはGF(11)のReed–Solomon復号を行うことになり、これは重い。**ただしcodex32が同じ問題を解いている。** 有限体をGF(32)に選び、対照表と紙の回転円板で人手で回せるようにした。CipherFluteも同じことができ、GF(11)なら乗算表は11×11の1枚である。**「紙の対照表つきで手復号できる暗号笛」は、それ自体が発表できる設計の貢献になる。** なお相対音感の個人差と、聴覚に障害のある方の包摂は課題として残る。ただし機械の経路が併存するので排除にはならない。「読める」ことと「復元できる」ことの区別も保つ必要がある。

**そして、論文が自分で「欠点」と書いた部分が実は核心である。** 「音感に優れた人により認識・記憶されやすい」ことは、脅威ではない。論文自身が「物理層に秘匿の力はない、秘匿は秘密分散が担う」と宣言している以上、**人が聞き取れることによる損失はゼロである。** 音は最初から公開チャネルだと宣言しているのだから、これは**設計目標**として書き直せる。

**この置き方には、娯楽性の主張を避けられるという実務上の利点がある。** 半音を選んだ理由が可読性になるので、音楽性は主張ではなく副次的に生じた性質として1文触れるだけで済む。「楽しい楽器を作りました」と読まれる危険を構造的に避けられる。

**実験ではなく実演でよい。** WISS 2026の募集要項は「『評価（User StudyやEvaluation）』については、記述が無い場合でも減点対象とはしません」と明記しており、重視するのは「アイデアの斬新さ」と「デモや実装による有効性のアピール」である。したがって統計を伴うユーザスタディは不要であり、**鍵盤楽器または較正用コームで1回復号してみせる実演を、図1枚か短い記述で示せば足りる。** 存在証明として1回通ればよく、「音感のある人なら分かるのは自明ではないか」という批判も受けない。

**A-2　担体の材料と色を選ばないこと。** AirCodeは均質で半透明な材料を要求し、熱溶解積層方式では均質にならず不透明な塗装では失敗すると論文自身が認めている。InfraredTagsは特定の黒い赤外透過フィラメントで物体全体を印刷することを要求し、他の色は今後の課題で、スプールごとの再較正まで勧めている。**CipherFluteは符号の担い手が形状なので、担体の光学的性質にいっさい依存せず、任意の家庭用フィラメントで作れる。** これは反証されない、はっきりした差である。

**A-3　機械の経路を使う場合の、読み手の入手可能性。** AirCodeはプロジェクタと産業用カメラと交差偏光板からなる据え置きの光学ベンチ、InfraredTagsは132グラムの後付け撮像モジュールと画像処理サーバを要する。CipherFluteは利用者が既に持っているスマートフォンのマイクだけである。A-1があるので単独では弱いが、速く正確に読みたいときの経路として併記する価値はある。

**「外観に符号が現れない」という言い方は使わない。**

**軸B　読み出しが可聴で、身体的で、立ち会えること。条件つきで生きる。**

光学タグは無音で所有者の関与なく読める。CipherFluteは吹かないと読めない。相続、共同管理、鍵の開封式のような「人と人の間で秘密を扱う」場面では、読み出しが可視で可聴であることが監査可能性になる。

**ただし仮定では強くならない。** 「誰が、いつ、なぜそれを必要とするのか」の論証が現時点でゼロだからである。実装が完璧でも「それは誰の課題か」と必ず問われる。**相続や共同管理の実務者に1人でも話を聞けば、この軸は実装を増やすよりずっと安く強くなる。**

**軸C　秘密が音楽になること。副次的な性質として1文だけ触れる。主張には使わない。**

> **【更新】** 当初これを「最も独自な貢献」として前面に出すことを勧めたが、**取り下げる。** 理由は3つある。第一に、体験の質は評価軸が曖昧で、募集要項が挙げる「アイデアの斬新さ」と「デモや実装による有効性のアピール」に載せにくい。主張すればそれを支えるユーザスタディを自分から呼び込むことになり、必須でない実験を背負う。第二に、エンタテインメントコンピューティングの文脈に置かれると、本気の遊びの研究と競合することになって分が悪い。第三に、安全性と娯楽の同居は査読者に「どちらの研究なのか」と思わせる。栗原さんの懸念のとおりである。
>
> **軸A-1がこの問題を解決する。** 半音を選んだ理由が可読性になるので、音楽性は主張ではなく結果として生じる性質になる。以下は、そう位置づけ直したうえで残る記述である。

先行研究を全部並べても、**読み出しの瞬間に体験が生まれるものは1件もない。** Acoustic Barcodesは擦る音、codex32は紙の円板、InfraredTagsは撮影、SeedQRはカメラであり、どれも読み出しは作業である。CipherFluteだけが、読み出しそのものが演奏になる。スプールを回しながら外周を吹いていくこと、ハートが2枚でそろうこと、カードが1つの調に対応することは、いずれも体験の設計である。

ところが論文は3.2節でこれを1文だけ触れ、しかも「音感に優れた人により認識・記憶されやすいという欠点にもなる」と自分で打ち消している。**セキュリティの研究として書こうとした結果、いちばん独自な部分を自分で削っている。**

そして9章「未来ビジョン」には本来の主張が書かれている。「復元の手続きが音を伴い、立ち会えるという性質は、複数人での鍵の開封式、遺言やデジタル遺産の引き継ぎ、そして楽器としての演奏性を伴う体験型のセキュリティ教育といった、人と人との関係性のなかで秘密を扱う場面に自然に馴染む」。**論文でいちばん良い主張が最後のページに追いやられている。**

**軸D　自作可能性と容量。主張しないほうがよい。**

自作可能性はcodex32もSeedQRも紙とペンでできるので優位ではない。むしろ3Dプリンタという設備を要求する分だけ劣る。容量と物量は明確な負けである。**正直に限界として書けば、かえって他の主張が信用される。**

### 仮定を最善にしても消えない問題が3つある

これは「まだできていない」ではなく「そうはならない」ものなので、除外せずに扱う。

**問題1　基準笛は、笛を1本ずつ吹く限り息の強さを補正できない。**

比で消えるのは分子と分母に同時に同じ係数が乗るものだけである。温度は物体と空気の性質なので共通モードになるが、息の強さは1本ごとに違う。これは実装の問題ではなく構造である。

**ただし逃げ道がある。** 7.1節にある「複数の笛を同時に鳴らす」が実現すれば、同じ呼気を共有するので共通モードになる。**つまり同時吹鳴は、読み出しの手間を減らすための改良ではなく、息の補正を成立させるための本質的な要件である。** 今後の課題としての位置づけを格上げすべきである。

**問題2　偽装の価値には天井がある。**

封印の研究（Johnstonの120種類が平均5分未満・平均55ドル、Appelの錠が平均13秒）が、物理層の防護は分と数十ドルの単位で崩れると実証している。偽装の実験がどれだけ良い結果を出しても、**「探索コストをいくらか上げる」以上には主張を強められない。** これは外部の実証なので仮定では消えない。

**問題3　気軽な用途では暗号的な強度が原理的に出ない。**

カード1枚8本で20.8ビットであり、笛の本数に律速されるので実装がうまくいっても変わらない。「気軽な暗証番号から本格的な鍵管理まで同じしくみで」という主張はセキュリティの文脈では危ういままである。**体験の文脈なら何の問題もない。**

### 推奨　論文の重心を「読み出しに機械が要らないこと」へ移す

> **【更新。当初は「体験の側へ移す」を勧めたが取り下げた】** 体験を中心に据えると評価軸が曖昧になり、娯楽の研究として読まれる危険がある。中心に据えるべきは**能力の主張**である。できるかできないかで判定でき、しかも安全性の文脈で真面目な要件として通る。

現状は「秘密の物理バックアップの新方式」として書かれている。これを次のように移す。

> **「特別な装置を持たない人が、そのへんにある楽器ひとつで復号できる、電源も電子部品も持たない秘密の担体」を1章に置く。** 128ビットのリカバリーシードは「この方式がどこまで運べるか」の限界を示す実装として6章に降ろす。

この構成なら、上の3つの消えない問題がすべて無害になる。息の補正の限界は同時吹鳴という研究課題になり、偽装の天井は正直な限界の記述になり、20.8ビットのカードは「暗証番号にはこれで足りる」という用途の話になる。

**募集要項とも合う。** WISS 2026が重視するのは「アイデアの斬新さ」と「デモや実装による有効性のアピール」であり、評価実験は必須ではない。**鍵盤楽器で復号してみせる実演は、まさに「デモによる有効性のアピール」そのものである。** しかも実装済みという必須条件は既に満たしている。

鍵管理の実務と正面から殴り合う土俵を自分から選ぶ必要はない。容量でも耐火性でも読み出し速度でも負けるが、**「機械が要らない」という一点では誰も追いついていない。**

なお [暗号笛関連コンテンツ探し] の209件は、この構成では導入の飾りとして1件か2件使う程度でよい。中心に据えるものではない。

### 検証後に加わった、もう1つの立て方　「空白は容量ではなく読み出しの敷居の側にある」

DNA-of-thingsの検証から、当初は見えていなかった軸が出てきた。**日用品に秘密を埋める研究は、容量ではもう決着がついている。** 老眼鏡に1120万ビットが電源なしで入っており、著者自身がそれをステガノグラフィと呼んでいる。

しかしその読み出しは、物体を切り出す破壊的な操作と、次世代シーケンサと、約2000スイスフランの費用を要し、一度読めばその部分は失われる。**持ち主が自分の秘密を日常的に取り出す用途にはまったく向かない。**

そこで既存の研究を「読み出しの敷居」で並べ直すと、位置が明確になる。

| 系譜 | 容量 | 読み出しの敷居 |
| --- | --- | --- |
| 受動音響タグ（Acoustic Barcodes、Blowhole、SoundOff） | 12ビットが上限 | 低い（マイクだけ） |
| 隠された光学符号（AirCode、InfraredTags、InfoPrint） | 83ビットから500ビット | 中（専用の撮像装置、材料の制約） |
| **CipherFlute** | **128ビット** | **低い（素のスマートフォンだけ、非破壊、繰り返し可）** |
| DNAを混ぜた造形物（DNA-of-things） | 1120万ビット | きわめて高い（破壊的、シーケンサ、2000スイスフラン） |

**「開けずに、専門の設備なしで、持ち主自身がその場で、繰り返し機械可読に読み出せる」という条件を保ったまま到達できる容量の上限を押し上げた**、という立て方なら、どの反例とも矛盾しない。これは軸Aと軸Cを補強する第3の言い方であり、バックアップ媒体の土俵に戻ることなく容量の話ができる。

### ひとことで

**「もっと良い金庫」としては勝てない。「秘密を鳴らして取り出すという、まだ誰も作っていない体験」としては、先行研究がまったくない本物の空白である。** 後者で書くなら、実装は既に足りている。

容量に触れるなら、「最大」ではなく「**読み出しの敷居を上げずに到達できる上限**」として述べる。

## 第3部　改訂の優先順位（書き換え版）

`PAPER_REVISION.md` の優先順位を差し替える。引用の追加を最上位に置いていたが、**引用漏れは弱点であるのに対し、概要の過剰主張は正確性の失敗である。**

| 順位 | やること | 理由 |
| --- | --- | --- |
| 1 | **「特別な装置を持たない人が、そのへんにある楽器ひとつで復号できる」を第一の貢献に据える**（1章と6章の入れ替え）。3.2節の半音の理由を「エンタテインメント価値」から「既存の鍵盤楽器がそのまま対照表になるから」へ書き換え、「音感に優れた人に読まれる欠点」の記述を削る。較正用コーム自体が対照表になることを書く | 埋まっていない位置がここにあり、既存の実装で今日から言える。娯楽の研究として読まれる危険も構造的に避けられる |
| 1 | **鍵盤楽器または較正用コームでの復号の実演を1つ入れる**（図1枚か短い記述で足りる。ユーザスタディは不要） | 募集要項が重視する「デモや実装による有効性のアピール」に直接当たる。評価実験は必須ではないと明記されている |
| 2 | 概要の「128bit暗号のエンコードとデコードを検証した」を事実に合わせる | 正確性の失敗であり、他のどの改善よりも重い |
| 3 | 13スロットと12スロット、約40本と49本を統一する | 方式が読者に伝わらない |
| 4 | 基準笛の効果を温度に限定し、息の強さの主張を削る。同時吹鳴を「息の補正を成立させる要件」として格上げする | 原理的に成り立たない主張である |
| 5 | 第一の新規性から「原理的に」を削り、「追加の装置なしに」へ弱める。2軸の表を入れる | 反例が確定した |
| 6 | 基準笛について「共鳴型センサで確立した原理の移植である」と明示し、SmithとSenturiaを引く | 反例が確定した |
| 7 | 検証値とAES-GCM鍵の記述を暗号的に健全にする | 検証中だが、指摘の筋は通っている |
| 8 | 10ページを6ページへ削る | 形式要件である |
| 9 | Whoosh、Printone、AirCodeまたはInfraredTags、Acoustic Barcodesを簡潔に引用する | 見落としの中で最も重い4件 |
| 10 | codex32、SeedQR、国内研究を必要最小限だけ追加する | 網羅性の担保 |

**製造時の音響側チャネルは、限界の節に一文で足りる。** 6ページの制約下で未実施の攻撃を4本紹介するより、中心となる仕組みが本当に読めることを示すほうが重要である。`PAPER_REVISION.md` はここに紙面を使いすぎていた。

削る候補は `PAPER_REVISION.md` の案では足りない。次まで踏み込む必要がある。

- 通信方式の歴史（2.3節）を一段落から一文へ縮める
- 利用プロファイルの表（表3）を削る
- ユースケースをカードと128ビットのスプールの2つだけにし、本立てとChordikaとAES-GCMの説明を削る
- 印刷の向きの実験（5.4節）を結果2文だけ残す
- モスキート音の節（7.6節）を削る
- 素材の説明を一か所に統合する
- 未実施の評価の5つの小節を一段落にまとめる
- 脅威モデルの表4と表5を1つに統合する
- 比較表をWhoosh、Blowhole、Acoustic Barcodes、代表的な不可視の光学方式、本研究の5件程度に絞る

一方で、**差分符号化によって1つの音高の誤りが2記号へ波及するため、Reed–Solomon符号のブロックをインターリーブして分散させる**という設計は残すべきである。これはこの研究に固有の工学的内容であり、一般的な制約符号の理論を長く書くよりも価値がある。

## この文書が `SURVEY.md` を訂正する箇所

| `SURVEY.md` の記述 | 訂正 |
| --- | --- |
| 新規性の第一「隠蔽と可読性の両立は光学符号には原理的に得られない構造的な差である」 | 誤り。「追加の装置なしに読めることと隠蔽の両立」へ弱める。2軸の表で位置を示す |
| 新規性の第三「基準体による正規化を音響でやった例は存在しない」 | 不正確。共鳴型センサでは1995年に既に "conventional sensing setup" と呼ばれている。「受動的な共鳴管と離散符号の復号へ移した」に限定する |
| 「351件を横断して semitone が0件」 | 単語の不在であって概念の不在ではない。Whooshが 2^(i/12) を使っている |
| 「網羅的に探して存在しなかった」という言い回し全般 | 「今回の検索範囲では確認できなかった」へ改める |
| 新規性の4点を同格に並べていること | 同格ではない。軸Aが構造的な貢献、軸Cが最も独自、脅威モデルは信頼性の要件であって技術的新規性としては弱い |
