qurihara/ai-fue/related_work_survey/SURVEY.md

# CipherFluteの関連研究サーベイ　統合報告

2026年7月30日作成。栗原一貴さんの依頼により、CipherFlute（WISS 2026投稿予定）の位置づけと新規性を定めるために行った関連研究調査の統合報告である。

> **【重要　この文書は一部訂正されている】**
> 本文書が提示した「新規性の再定義」のうち、第一の主張（隠蔽と可読性の両立は光学符号には原理的に得られない）と第三の主張（基準体による正規化に前例がない）は、外部評価と追加の検証によって**成立しないことが確定した**。また「網羅的に探して存在しなかった」という言い回しは根拠を持たない。
> 訂正の内容と、そのうえでの研究の位置づけの立て直しは `REVIEW_AND_REPOSITIONING.md` にある。**食い違う場合はそちらが新しい。** 本文書は調査の記録として残してある。

## この調査の規模と方法

2段階で行った。第1段階では14の切り口を立て、切り口ごとに探索の担当と検証の担当を別に置いて、合計28のエージェントを並行して走らせた。第2段階では、第1段階で危険と判定された文献を原典に当たって主張の真偽を確定させる担当4名と、第1段階で残った穴を埋める担当6名を走らせた。合計38のエージェントが3,153回の道具呼び出しを行い、確認できた文献と事例は延べ700件を超えた。

第2段階の検証は「前段の報告が本当にその論文に書いてあるか」を敵対的に確かめる役として設計した。この工程で前段の報告に重要な誤りが4件見つかっており、検証を挟まずに論文へ取り込んでいたら誤った引用を書くところであった。

生の記録は次の場所にある。

- `raw/01` から `raw/14` に、14の切り口ごとの探索と検証の記録がある。
- `raw2/v1` から `raw2/v4` に、最重要文献の原典確認の記録がある。
- `raw2/f1` から `raw2/f6` に、穴埋めの記録がある。
- `00-digest.md` に、第1段階の結果を機械的に集約したものがある。

## サーベイの深さを測る「テスト」の結果

栗原さんが事前に仕掛けた4項目について、エージェントには名前をいっさい与えず、切り口だけを与えて自然に浮かび上がるかを見た。4項目すべてが浮かび上がった。

| テスト項目 | 結果 | 最初に出てきた切り口 |
| --- | --- | --- |
| 鳴海紘也さんの研究 | 浮かび上がった | 日本のファブリケーション系のHCI、造形物への情報埋め込み |
| 高橋治輝さんと松村耕平さんの立命館大学の3Dプリンタ関係の研究 | 浮かび上がった | 日本のファブリケーション系のHCI |
| 加藤邦拓さんの研究 | 浮かび上がった | 音響センシング、日本のファブリケーション系のHCI |
| MakerWorldの印刷可能な笛 | 浮かび上がった | 3Dプリント笛の計算設計、およびモデル共有基盤の実物調査 |

第2段階の深掘りで、この4項目のうち加藤邦拓さんと鳴海紘也さんの業績から、第1段階では見えていなかった危険度の高い文献が新たに2件出た。SheetKey（Graphics Interface 2020）とDuoTouch（CHI 2026）である。いずれも「電源も電子部品も持たない印刷物や造形物が符号を保持し、市販の端末がそれを読む」という構図でCipherFluteと同型であり、必ず引用しなければならない。

なお所属に訂正がある。鳴海紘也さんの現所属は慶應義塾大学理工学部情報工学科であり、東京大学は旧所属である。片倉翔平さん（ProtoHoleの著者）の現所属はドイツのハッソ・プラットナー研究所であり、明治大学は学生時代の所属である。

## 分野の地図

CipherFluteは7つの独立した系譜の交点に立っている。それぞれの系譜がどこまで到達しているかを整理する。

### 系譜1　造形物への情報埋め込み（光学・電波・熱・磁気で読む）

2013年のInfraStructsから十年以上積み上がっており、「消費者向けの熱溶解積層方式プリンタで日用品に情報を仕込み、電子部品も電源も使わずに読み出す」という枠組み自体はまったく新しくない。到達点を数字で示すと、AirCodeが5センチメートル角に約500ビット、StructCodeがレーザーカットの大きなヒンジに228ビット、InfraredTagsが21×21のQRコードで83ビット、AnisoTagがクレジットカードと同寸の面に51ビットである。読み出しの物理はテラヘルツ波、可視光、近赤外線、熱、磁界、X線に及ぶ。

この系譜の共通の空白は3つある。第一に、脅威モデルを明示した研究がほとんど存在しない。第二に、読み出しに所有者の身体的な行為を要する設計が存在せず、撮影だけで所有者の関与なく読める。第三に、秘密分散や暗号鍵の保管を目的に設計されたものが存在しない。

国内にはこの系譜が3つ独立に存在する。神奈川工科大学の上平員丈さんと鳥井秀幸さんらは2014年から30件を超える発表を積み、造形物内部の空洞や近赤外蛍光染料や強磁性セルに数百ビットを入れて非破壊に読んでいる。大阪大学の佐藤宏介研究室（宮武大和さん、Parinya Punpongsanonさんら）は3Dプリント食品の内部に外観を変えずに情報を埋め込んでおり、UIST 2022のinteriqrに至っている。日本電信電話株式会社の久保勇貴さんらはスライサの充填パターンで外観が同一の造形物に固有の音響応答を与えている。

### 系譜2　受動的な音響タグ（音で読む無電源の物体）

CipherFluteの直系の系譜である。Acoustic Barcodes（2012年）が刻み目をなぞる音に符号を載せ、Lamello（2015年）が櫛歯の長さを音高の記号にし、Acoustic Voxels（2016年）が内部空洞の音響応答に4ビットを埋め、Blowhole（2018年）が3Dプリント物の空洞に息を吹き込んで最大9個のタグを識別し、SoundOff（2025年）が受動的な超音波タグで15個を区別している。

この系譜の実証容量は、誤り訂正後の実効値で見るとAcoustic Barcodesの12ビットが最大であり、Acoustic Voxelsが4ビット、Blowholeが2.6ビットから3.2ビット相当、Lamelloが2ビット相当、SoundOffが3.9ビット相当である。**100ビットを超える秘密の値を電源なしの可聴音のタグで運んだ例は、この系譜に存在しない。**

### 系譜3　3Dプリントされた笛と気鳴楽器の計算設計

Printone（SIGGRAPH Asia 2016、梅谷信行さんら）が到達点である。任意の自由形状を中空化し、境界要素法で共鳴周波数を予測しながらフィップル吹き口と指孔を配置し、家庭用のプリンタで印刷して演奏させている。指孔5個の作例では1つの物体から9音を出している。設計道具としてはdemakein（査読論文の裏づけを持たない）とopenwind（Inriaが開発し3件の査読論文を持つ）が実在する。音高の精度をセント単位で報告した査読文献はDabinら（NIME 2016）がほぼ唯一で、印刷したリコーダーで初版が+6から+34セント、手修正版が-13から+14セントである。

この系譜に情報を符号として載せるという発想は存在しない。Printoneの本文を機械検索した結果、bit、code、encode、decode、secret、message、identification、tag、watermark、steganography、cryptography、key、storage、capacity、symbol、alphabetのすべてが0件であった。

### 系譜4　秘密情報の物理的バックアップの実務と標準

codex32（Bitcoin Improvement Proposal 93、2023年）が最も近い。有限体GF(32)上のBCH符号による誤り訂正とShamirの秘密分散の分割と復元を、紙と鉛筆と回転円板だけで人手で実行する。SeedQRとCompactSeedQR（SeedSignerプロジェクト）はBIP-39の語を索引番号に写して二次元コードに収め、128ビットを21×21の格子に載せて金属板に打刻する。QR SafeShare（2025年9月公開）は秘密をShamirの秘密分散で分割して各断片を3Dプリントできる二次元コードとして書き出す。

**この系譜は例外なく「符号が見えるから読める、見えるから危ない」という一本の交換関係に縛られている。** QR SafeShareの錠つき覆いは覆えば読めないという交換関係を明示的に認めており、SeedQRの仕様書は自分の二次元コードを絶対に写真に撮るなと警告している。担体を日用品に偽装する設計は、標準にも論文にも製品にも見つからなかった。

### 系譜5　符号理論と低容量の物理媒体

CipherFluteの隣接同音禁止に最も近い先例は、8B/10B符号ではなく2つある。第一に、Goldmanらの合成DNAへのデータ保存（Nature 2013）が、各桁を「直前に使った塩基とは異なる三塩基のいずれか」へ写すことで同一記号の連続を構造的に排除している。記号数を4から実効3へ落とす数え方までCipherFluteと一致する。第二に、Acoustic Barcodes（2012年）が固定物理長方式で「0が2つ続く列」を禁じており、その動機を「区切りの信号を復元できるようにするため」と明記している。**受動音響タグの文脈に14年前から前例があった。**

一方で、この調査は設計の正当性を裏づける情報理論も確定させた。記号の種類がq個で隣り合う記号が同じにならない制約のもとでの1記号あたりの容量は log₂(q−1) ビットであり、CipherFluteの差分の写像はこれを有限の長さでもちょうど達成する。**すなわち13から実効12へ落とす扱いは最適であり、余分な冗長は一切ない。** さらに「隣接同音を禁じたq種類は制約のないq−1種類とまったく同じ量を運ぶ」という等式から、音域を半音1つ広げれば制約が容量の代償なしに手に入ることが言える。

### 系譜6　物理暗号と感覚器による復号

NaorとShamirの視覚暗号（EUROCRYPT '94、Lecture Notes in Computer Science 第950巻）が原型である。2枚を重ねるだけで計算をまったく行わずに人間の視覚系が復号し、1枚だけでは乱雑な模様と区別がつかない。著者自身が閾値2の場合を原型と明言している。Desmedtらは1998年に音響版と光学版を出し、**シェアを検閲者に怪しまれない見た目や音にすることを設計目標として明示している。偽装の動機の先例である。**

国内では水木敬明さんらのカードベース暗号が大きな系譜を作っており、菓子のディスペンサ、ダイヤル錠、15パズル、硬貨、ボールと袋という日用品を電源不要の暗号装置に変える系列がある。2026年には情報処理学会誌が「情報セキュリティ教育にも応用可能な身近な道具を利用した暗号技術」という副題で前後編の特集を組んでいる。3Dプリンタでカードベース暗号の実行装置を作る研究（伊藤優樹さん、四方隼人さん、水木敬明さん、菅沼拓夫さん、コンピュータセキュリティシンポジウム2023）もある。

**とりわけ注意すべき文献が1件ある。** 大川直也さんと栃窪孝也さんが、視覚復号型秘密分散法をパスワードの分散管理に応用した論文を、情報処理学会論文誌デジタルプラクティス第7巻第2号（2026年4月15日発行）に出している。パスワードを2-of-2で分散し、片方を紙に印刷し、もう片方をOHPシートやスマートフォンで保管して重ねて復元する。用途がほぼ同じで、日本語の査読誌であり、発行が2026年4月である。引用しないという選択は取れない。

### 系譜7　音でデータを送る通信方式

Schenkerの二群音声周波数符号（Bell System Technical Journal 1960年、のちのITU-T勧告Q.23）が周波数スロット符号の原型である。音の符号を物理媒体に固定して保管し再生して読み出す枠組みは、1975年のKansas City標準によるカセットテープへのデータ記録が半世紀前に大量実用化している。楽音そのものを送信機に使う研究も2002年に存在する（Dominguesら、IEEE Workshop on Multimedia Signal Processing）。周波数の集合を記号の語彙としてReed–Solomon符号を載せる構成は、ggwaveという実装がすでに採っている。

## 新規性を脅かす文献　危険度順

### 危険度が最も高いもの

**1. Whoosh の FluteCase（ISWC 2016）**

Gabriel Reyesら、Proceedings of the 2016 ACM International Symposium on Wearable Computers、pp.120-127、DOI 10.1145/2971763.2971765。

原典を全文取得して検証した結果、次が確定した。節見出しがそのまま「FLUTECASE: A PASSIVE 3D-PRINTED WATCH CASE」であり、8本の閉管を持ち、電源も電子部品も持たず、3Dプリントであり、管長は式(2)の L = 14.956 × 2^(i/12) すなわち平均律の半音比を公比とする等比数列である。「2キロヘルツから10キロヘルツ」という文言も本文に存在する。認証への言及も実在する。

**しかし前段の報告には3つの過大表現があった。**

第一に、FluteCaseは音の高さを測っていない。認識は26次元のメル周波数ケプストラム係数とその差分、主成分分析、三次多項式カーネルのサポートベクターマシンによるスペクトル指紋の照合であり、基本周波数の推定を行わない。第二に、「2キロヘルツから10キロヘルツ」は帯域の言明にすぎず、設計式から出る8本の周波数は約3827ヘルツから5733ヘルツ、広がりは半音7個分にとどまる。実測共鳴周波数の報告は一切ない。第三に、認証の記述はFluteCaseの応用ではなく「無改造の時計での応用」の節にあり、8本の管とは無関係である。security の出現は全文で1回だけであり、threat、adversary、cryptography、encrypt、secret、entropy はすべて0回である。

**そして決定的な差分が見つかった。** FluteCaseの管長は「For replicability」として論文に定数として公開されており、すべての複製が同一形状になることを意図している。情報は形状ではなく「どの穴を吹いたか」という利用者の選択に載る。すなわちFluteCaseは8鍵の鍵盤であって記憶媒体ではない。CipherFluteは逆に、管長が物体ごとに違い、その違いが運ぶべき値であり、読み取り側は事前にその値を知らない。これは程度の差ではなく種類の差である。bit（情報量として）は0回、embed、conceal、hidden、disguise、steganography、calibrate、temperature、humidity はすべて0回である。

被引用44件を確認した結果、FluteCaseの路線を継いだのはBlowhole 1件だけであり、Blowhole自身も FluteCase の語を使わず Whoosh [16] として引用している。

**判断。** 「電源も電子部品も持たない3Dプリントの笛を複数本融合し、吹いた音の高さで情報を読む」という言明の新規性は消える。しかし「形状が秘密を運ぶ記憶媒体である」という一点に絞れば中核は残る。この論文は必ず引用し、管長式が半音比であることを自分から指摘したうえで、「同じ格子を使うが、あちらは全複製が同一形状になることを目的とし、こちらは形状の違いが値である」と書くのが最も強い。引用を避けることによる利益は無く、損失だけがある。ISWCという主要会議でAbowdとStarnerが著者に入った論文を、笛の研究をしていて見落としたという言い分は通りにくい。

**2. Printone（SIGGRAPH Asia 2016）**

Nobuyuki Umetani, Athina Panotopoulou, Ryan Schmidt, Emily Whiting、ACM Transactions on Graphics 第35巻第6号 論文番号184、DOI 10.1145/2980179.2980250。

原典を全文取得して検証した結果、前段の報告に**重大な数値の誤り**が見つかった。「56個の目標周波数のうち53個が実測範囲に入った」という文言は短縮版（International Symposium on Musical Acoustics 2017）にしか存在せず、本体は同じ段落で「104個の目標周波数のうち、目標を出せなかったのは4例だけであった」というまったく違う数を挙げている。本体の全14ページに「56」は現れない。論文に書くなら本体の「104個中4個」を使うべきである。

さらに重要な発見がある。この「実測範囲」は音高精度ではまったくない。本体は「吹く速さを徐々に上げながら、明瞭に鳴った最低周波数と最高周波数を記録した」と定義しており、主張は「奏者が吹き方を選べば目標音に当てられる」ことである。**本体と短縮版のいずれにも cent および cents は0件である。** Printoneは「吹く速さの変化は10ヘルツの誤差を容易に補償できる」と述べ、造形誤差も相対評価で片づけている。

**つまりPrintoneは吹奏による音高の可変性を長所として扱い、CipherFluteはそれを打ち消すべき雑音として扱う。同じ物理現象に対して一方が可変性を資源とみなし、他方が敵とみなしている。要求が正反対である。** これがCipherFluteの土台であり、関連研究に書くべき差分でもある。

あわせて、Printoneは空洞を作るために模型を手作業で半分に切り、別々に印刷してサポート材を除去し、接着している。CipherFluteのサポート材なし一体平置き印刷は、この妥協を解消するものである。前段はこの差を見落としていた。一方で、指孔5個の作例が1つの物体から9音を出しているため、「1つの印刷物から複数の音高を出す」ことを新規性に数えることはできない。

**判断。** 管の長さと音の高さの対応式にもとづく設計を新規性として掲げてはならない。掲げれば直ちに反証される。主張できるのは「既知の管長と周波数の関係を、離散スロットからなる符号の語彙として再定義し、基準笛による正規化と誤り訂正と隣接制約を伴う読み出し系として組み立てた」という後半だけである。設計計算の新規性を明示的に放棄したほうが、査読者に対してかえって強い立場になる。

**3. codex32（Bitcoin Improvement Proposal 93、2023年2月13日）**

有限体GF(32)上のBCH符号を紙と鉛筆で計算し、Shamirの秘密分散の分割と復元を人手で行う。検査符号13文字の場合、8文字以内に影響する任意の誤りを必ず検出し、置換4文字まで、消失8文字まで、連続消失13文字までを訂正する。**「電源不要の物理媒体に誤り訂正符号付きで秘密を格納する」という一般的な主張はこれに先取りされており、しかも復号に電子機器を一切要しない点でCipherFluteより徹底している。**

ただし検証で3つの留保が見つかった。第一に、「紙の回転円板」はBIP-93の本文に一度も現れず、参照実装リポジトリと公式サイトの側にある。BIP-93は手計算の具体的手順を標準の範囲外と明記している。第二に、作者自身が「この方式に対応する財布は存在しないので本物の金銭に使うな」と警告しており、BIP-93の状態は今もDraftである。第三に、担体の偽装や隠蔽への言及は皆無である（hide、hidden、conceal、disguise、steganography、plausible、deniable がすべて0件）。

**4. QR SafeShare（2025年9月11日公開）**

作者はJurgen（GitHubのアカウント名はcmd1982）。秘密をShamirの秘密分散で分割し、各断片を3Dプリントできる二次元コードとして書き出す道具である。GitHubの最初のコミットが2025年9月11日であり、**CipherFluteに約1年先行する。**

脅威モデルの立て方は報告どおりであった。説明文に「決意した攻撃者ならこじ開けられるが、この覆いは素早い走査や気づかれない走査を防ぎ、許可の無い読み出しに必要な労力を上げる」という一文があり、安全性はすべて秘密分散に負わせ、単一の二次元コードは超級計算機でも将来の量子計算機でも無価値だと述べている。

**ただし2つの訂正がある。** 第一に、日用品への偽装は謳っていない。MakerWorld、Printables、GitHubのREADME、help.html、disclaimer.html、index.html、split.htmlの全文を読んでも、偽装や迷彩や目立たない物に仕込むという記述はどこにもない。物理層の対策は錠つき覆いという露骨な物理障壁の一点だけである。第二に、攻撃者の能力を列挙して守らない範囲を宣言するという学術的な節は存在しない。**宣言の厳密さではCipherFluteのほうが高い。** なお普及はごく小さく、MakerWorldはいいね1件でダウンロード0件である。

**5. SeedQR と CompactSeedQR（SeedSignerプロジェクト、2022年1月22日以降）**

BIP-39の語を索引番号に写して二次元コードに収める。CompactSeedQRは索引を11ビットで連結して検査ビットを落とし、128ビットを16バイト・21×21の格子に載せる。仕様書自身が金属板への打刻を前提にしており、CompactSeedQRなら手作業の穴あけが35から40パーセント減ると書いて、穴を開けた金属板の写真を掲載している。3Dプリント用のひな型も実在する。**現行論文の参考文献にSLIP-39とSSKRはあるがSeedQRが無いのは明白な抜けである。**

ただし訂正が2つある。仕様書自身はReed–Solomonという語を一度も使っておらず、誤り訂正を自前で設計せず二次元コード規格の機能に依存しているだけである。また秘密分散は持たない（Shamir、split、share が全文で0件）。

**6. 特許　複数音の笛と、音で識別する笛**

第1段階では14の切り口すべてで特許が未調査であった。第2段階で調べた結果、危険度の高い特許が4件見つかった。

- **US4821670A（Whistle、Fortron Inc.、1989年登録）** 請求項1が「単一のホイッスル本体の中に少なくとも3個のフィップル型ホイッスル要素を持ち、少なくとも2つの気柱の長さが異なり、3要素に共通の吹き口を持つ」と請求している。**CipherFluteの物理構造そのものである。** 従属請求項9は最長室と最短室の差を最短室長の約5から10パーセントとしており、半音（比で約5.95パーセント）刻みとほぼ重なる。目的は3音を同時に鳴らしてうなりを作ることであり、情報の符号化はない。
- **US5113784（Multi-tone whistle、1992年登録）** 請求項1が「複数の共鳴室が吹き口に接続され、孔が塞がれた室だけが鳴るように寸法づけられている」と請求している。**CipherFluteが解いている「融合した多管笛から1本だけを選んで鳴らす」という課題と同一である。**
- **US10147410B2（Toot suite whistle pack、2018年登録）** 請求項1が「2本以上のホイッスルの集合であって、各ホイッスルは互いに異なる信号特性の値を持ち、吹いたときに放射される」、請求項2が「その信号特性が受信され、吹かれたホイッスルを識別するために用いられる」、請求項7が「音の特性は音高、音質、音量、持続時間のうち1つ以上を含む」と請求している。**読み出しの一次的な仕組みがそのまま書かれている。**
- **US11151848B2（Kali Care, Inc.、2021年登録）** 請求項1と2が「元データを符号化して閉鎖材における降伏強度の逐次的な不均一さとして表し、閉鎖材が破断したときの音がその符号化データを担う」と請求している。**電源も電子部品も持たない物理構造に設計者が選んだデータを幾何として刻み、人が物体に働きかけたときに生じる音として復号するという枠組みが、請求項の水準で成立している。**

なお、US5251569A（Multiple tone whistle、1993年登録）の明細書の背景に「通常の場合、長さの異なる2つ以上の音室が共通の吹き口に接続され、人が吹くとそれぞれの音室の長さに比例した2つ以上の異なる音高が生成される」と書かれている。**管長と音高の対応を使って複数音を出す設計は、1991年の時点で「通常の場合」と書かれる程度に自明であった。**

日本国特許では、学校法人幾徳学園（神奈川工科大学）の特許第6537049号（公開番号JP2015077775A）が「所望の情報を示す形状が3次元造形物に秘密裡に付加されるように3次元形状データを加工する」と要約されており、CipherFluteを包含しうる広さを持つ。請求項の日本語原文は未確認であり、栗原さんご自身の判断のためにも確認する価値がある。丸井智敬さんの特許第5620594号は、2つを組み合わせて初めて解読できる符号を造形物の接合部に作り込むもので、ハートのカードと発想が重なる。

**7. SheetKey（Graphics Interface 2020）と DuoTouch（CHI 2026）**

SheetKeyは山中翔太さん、Tung D. Taさん、坪内孝太さん、奥屋文紀さん、津志尾憲二さん、加藤邦拓さん、川原圭博さんによる研究で、導電性インクで印刷したパターンをタッチスクリーンに当てるとタッチイベントの列が生成され、それを利用者の認証に使う。DuoTouchは池松香さんと加藤邦拓さんによる研究で、無電源の受動アタッチメントが二進符号列を生成し、改変していない端末の標準のタッチ応答インタフェースで復号される。復号可能性を動作速度と導線幅と端末の標本化率の上限式として論じ、ハンドストラップやリングホルダーという日用品の形に埋め込んでいる。

**無電源物体への符号の固定、市販端末での復号、物理パラメータによる可読性の議論、日用品への埋め込みという四点がCipherFluteとそのまま重なる。** しかもどちらも日本の研究者による仕事であり、DuoTouchは2026年のCHIである。

### 危険度が中程度で、必ず引用して差分を述べるべきもの

- **大川直也さんと栃窪孝也さん（情報処理学会論文誌デジタルプラクティス 7(2)、2026年4月）** 視覚復号型秘密分散法によるパスワードの分散管理。用途がほぼ同じで日本語の査読誌である。CipherFluteはハートのカードで2-of-2をやっているが、復号にスマートフォンという計算装置を要するため、装置も計算も不要なこちらの方式にこの軸では明確に劣っている。
- **久保勇貴さんらのFabAuth（WISS 2019登壇、CHI EA 2019、CHI EA 2020）** スライサの充填パターンで外観が同一の造形物に固有の音響応答を与え、8個を平均99.3パーセントで識別する。一文要約と引用集合の両方がCipherFluteと重なる。ただし8クラス（3ビット相当）の識別であってデータ搬送ではなく、圧電素子と事前学習を必須とする。
- **髙倉礼さんらの能動的音響計測に基づくスタイラスの把持状態識別（WISS 2021）** 充填率25、50、75パーセントで6つの把持状態を95パーセント程度で識別する。FabAuthと並ぶ国内の直系先行研究であり、第1段階では拾えていなかった。
- **林吉経さんらの棒の引っかきによる音波（WISS 2025）** オルゴールの櫛歯を加工した爪が3Dプリントの突起列を引っかき、「爪は長さに固有の周波数で振動する」と明記している。**寸法が音の高さを決めるというCipherFluteの核心とまったく同じ物理を使う。** 第1段階では中と判定していたが、本文を読んで高に上げるべきである。
- **上平員丈さんと鳥井秀幸さんらの一連の研究（2014年から、30件超）** 国内における造形物への情報埋め込みの最も体系的な先行研究群である。
- **Near-infrared Imaging（ACM Transactions on Graphics 42(1)、2022年）** 応用として「チップを使わない情報の埋め込み、物理的な秘密分散、3Dプリントの評価、ステガノグラフィ」を明示的に挙げている。**「造形物への情報埋め込みの分野で秘密分散への言及が皆無である」と書くと誤りになる。**
- **Tubes Among Us（USENIX Security 2023）** 人が管を通して話すだけで話者識別の機械学習模型に対して他人になりすませることを示した。Printoneを引用している。管の音響が安全性の系を欺くほど制御可能であることを認めた形で書く必要がある。
- **Print-and-Play（CHI EA 2020）** Blowholeの著者本人が博士研究全体を「組み立ても較正も要らない3Dプリント対話物体」と位置づけ直したものである。CipherFluteの枠組みが2020年に一人の研究者の博士研究の主題として明文化されていたことになる。
- **Passive underwater acoustic barcodes using Rayleigh wave resonance（Journal of Applied Physics 131(12)、2022年）** アクリル球の半径がRayleigh波共鳴の周波数を決めるため、半径を変えて固有の音響的署名を作る。寸法が共鳴周波数を決める物理を使い、寸法の異なる素子の組み合わせで語彙を作る設計が正面から同型である。上海交通大学は同趣旨の中国特許3件（CN113009408B、CN113359137B、CN113359138B）も持つ。
- **須賀祐治さんのVirtual Vaults（情報処理学会研究報告CSEC 2026年5月）** 暗号資産の鍵管理における物理的隔離と仮想的隔離を同一の操作体系で記述するモデルである。物理的隔離の媒体として挙げているのは金庫と紙媒体であり、笛はまさに紙媒体の代替物にあたる。2026年5月という直近の発行であり、国内の共通語彙になる。
- **中尾美月さんらの尺八のCT画像に基づく内径補正（情報処理学会研究報告SLP 2026年2月）** X線CTが笛の内径を実用的な精度で復元できることを実証している。**CipherFluteの脅威モデルにおける「CTスキャンによる無音の読み出し」という攻撃手段の根拠になる。** ただし内径の復元になお差が残ると報告しているので、精度の限界も併記するのが正確である。
- **吉川茂さんの正倉院尺八吹奏時の歌口端補正長さの推定（情報処理学会研究報告MUS 2011年）** f = A/(L+e) の e が音響学の確立した概念であり、国内の情報処理学会研究報告に一次文献があることを示せる。
- **藤川真樹さんらのマルチモーダル人工物メトリクス（産業応用工学会論文誌ほか）** 合成樹脂製品を対象とし、カード形という形状までCipherFluteのカード実装と一致する。「管長は設計図そのものであって偶発的な微視的乱れではないから物理複製困難関数ではない」と説明する相手として、松本勉さんらのナノ人工物メトリクスより具体的で近い。
- **Johnston（Science & Global Security 9、2001年）と Appel（ACM TISSEC 14(2)、2011年）** 封印120種類すべてが平均5分未満・平均55ドルで破られ、投票機の錠が平均13秒で開く。**物理層の防護は「分」と「数十ドル」の単位で測られる。** CipherFluteはこの数字を引いて主張の大きさを自ら抑えるべきである。
- **Wolfeらの出現率効果（Nature 435、2005年）** 標的の出現率が低いほど見落としが劇的に増え、訓練でも消えない。偽装の効果を支える最良の外部証拠である。
- **CrawfordとIriberri（American Economic Review 97(5)、2007年）** 隠す側の選択が体系的に予測されうる。反証側の証拠として併記するのが誠実である。
- **Printablesの Flat Pocket Whistle と MakerWorldの Whistle Pan flute** 厚さ3ミリメートルで財布に入る平板型フィップル笛（いいね12,926件、ダウンロード97,000件、実作報告2,965件）と、長さの異なるフィップル笛を一列に融合したサポート材なしのモデル（両基盤で約10万ダウンロード）である。**薄く小さくサポートなしで鳴る平板型フィップル笛という工作技術自体はまったく新規ではない。**

## 「無かったこと」の一覧　新規性の足場

網羅的に探して存在しなかったことを列挙する。これがCipherFluteの新規性の輪郭である。

**受動音響タグの容量について。** 100ビットを超える秘密の値を電源なしの可聴音のタグで運んだ例は存在しない。8件の主要先行研究の被引用460件（異なる論文351件）を横断した結果、Acoustic Voxelsが実証した4ビットという音響埋め込み容量を超える数字を報告した後続は50件の被引用のうち1件も存在せず、Blowholeを引く17件のうち9件が著者本人の自己引用であり、第三者による情報符号化方向の発展は存在しない。

**半音の格子について。** 351件の異なる論文を横断して、whistle が0件、fipple が0件、semitone が0件であった。半音刻みの格子を符号の語彙とする発想は、この系譜の後続に一切現れない。

**基準体による正規化について。** 既知の音高を持つ基準素子を同じ物体に同居させ、他の素子をその比で読むという較正の構造を、造形物への情報埋め込みの文脈で採った研究は存在しない。最も近いOwlet（MobiSys 2021）は基準を物体側ではなく読み取り装置側に置いている。国内では川崎祐太さんらが2020年と2021年に同じ問題（環境温度による音響特性のずれ）を扱っているが、解法は特徴量と学習の側にある。

**脅威モデルについて。** 主要な造形タグ13件の本文を機械的に走査した結果、threat model、adversary、attack model、security analysis がすべて0件であり、**脅威モデルを持つ論文は1件もなかった。** InfraStructsの「Safety and Privacy」節はテラヘルツ波の生体安全性であり、SoundOffのprivacyはカメラを使わないという設計目標であり、StructCodeは対応表を暗号化しうるという一文だけである。

**投稿先について。** WISSの2014年から2025年までの12年分、延べ1197件の全題名を走査した結果、次が判明した。暗号を題名に含む発表が12年間で1件もない。秘密、秘匿、秘密分散を含む発表が1件もない。ステガノグラフィ、電子透かしを含む発表が1件もない。ブロックチェーン、暗号資産、ウォレット、リカバリーシードを扱った発表が1件もない。誤り訂正符号を含む発表が1件もない。笛、フィップル、リコーダ、ホイッスルを含む発表が1件もない。

**国内について。** 情報処理学会電子図書館の221,341件を66通りの検索式で走査し、インタラクションの2015年から2026年までの12年分（重複を除き6,705行）を走査した結果、造形物を吹いて鳴らしその音の高さを符号として多数ビットの情報を読み出す研究は国内の情報処理学会の刊行物にまったく存在しなかった。日本音響学会誌には笛を題名に含む論文が1件もない。誤り訂正符号や隣接同値禁止の制約を物理造形物の符号設計に持ち込んだ国内研究も見つからなかった。暗号資産の復元用情報を物理的な人工物に格納する国内研究は、須賀祐治さんの運用モデル以外に存在しない。

**国内の研究者について。** 近接する11名（高橋治輝さん、松村耕平さん、加藤邦拓さん、鳴海紘也さん、久保勇貴さん、上平員丈さん、鳥井秀幸さん、渡邊恵太さん、片倉翔平さん、伊藤雄一さん、水木敬明さん）の業績622件と1123件を走査した結果、3Dプリンタで笛や管楽器そのものを造形した研究は1件も存在しなかった。水木敬明さんの142件のレコードに secret sharing は0件であり、鍵共有の系列はすべてカードのランダム配布による鍵合意であって閾値秘密分散ではない。**日本において物理暗号の側とデジタルファブリケーションの側は接触していない。**

**特許について。** CipherFluteの構成、すなわち「複数の異なる長さの笛を1つの物体に融合し、吹いて生じる音の高さの列を符号語として少量の秘密情報を復号する」ことを請求している特許は1件も見つからなかった。基準となる発音体を同居させて比で読む構成、誤り訂正符号を付けた音高の列を幾何に刻む構成、秘密分散したシードを吹いて音で読む構成、隣接する発音体の同音を禁じる構成、いずれも0件である。3Dプリント造形物への情報埋め込みはディズニー、ヒューレット・パッカード、マイクロソフト、アドビ、ゼロックス、韓国電子技術研究院が特許を持つ成熟した領域であるが、読み出しの物理は例外なく光学、電波、または破壊的な分解であり、音響で読むものは1件も見つからなかった。

**モデル共有基盤について。** 笛の音高を符号として情報を運ぶモデルは、MakerWorld、Printables、Thingiverse、Cults3Dの4基盤に1件もない。多音の笛はすべて同時発音による音量の最大化を狙ったものである。

## 新規性の再定義

以上を踏まえ、CipherFluteの新規性は次の4点に絞るのが正確である。物理機構でも計算設計でも符号層の個々の要素でもない。

**第一に、隠蔽と可読性を両立させたことである。これが最も強く、他に代えがたい。**

既存の物理バックアップはすべて「符号が見えるから読める、見えるから危ない」という一本の交換関係に縛られている。QR SafeShareの錠つき覆いは、覆えば読めない・読むには外すという交換関係を明示的に認めている。SeedQRの滑り蓋つき容器も同じ構造であり、仕様書自身が「自分の二次元コードを絶対に写真に撮るな」と警告している。光学符号は表面に露出していなければ読めないので、日用品に埋めると読めなくなる。

音響符号はこの交換関係を切る。共鳴管は物体の内部空洞として存在でき、外から必要なのは窓と吸込口という小さな開口だけである。**この性質は光学符号には原理的に得られない構造的な差であり、検証した先行研究のいずれも持っていない。**

**第二に、受動音響タグの容量を識別番号級から128ビット級へ引き上げたことである。**

一次資料で確定した数字で言うと、既存の最大はAcoustic Barcodesの誤り訂正後12ビットであり、Acoustic Voxelsが4ビット、Blowholeが2.6ビットから3.2ビット相当、SoundOffが3.9ビット相当、Lamelloが2ビット相当である。128ビットは1桁から2桁の差である。ただし光学符号との比較では劣位であり（StructCodeが228ビット、AirCodeが約500ビット）、比較の対象を音響に限定して書く必要がある。

**第三に、既知の音高を持つ基準笛を同じ物体に同居させ、比で読んで気温と息の強さの変動を構造的に打ち消したことである。**

LayerCodeが層厚の比で撮影倍率を打ち消すのと同じ狙いだが、音響でこれをやった例は存在しない。この主張には温度の実測（25.2度と41.0度で残差が±24セント以内）という裏づけがあり、独立して立つ。

**第四に、造形物への情報埋め込みという分野に、暗号学的に誠実な脅威モデルを持ち込み、秘匿の責任を秘密分散へ一元化したことである。**

主要な造形タグ13件のいずれも脅威モデルを持たない。ただしQR SafeShareが2025年9月に同じ立場を実物として公開していることと、造形物への情報埋め込みに明示的な攻撃者モデルを置いた研究がSecure Information Embedding in Forensic 3D Fingerprinting（2024年）に存在することは注記する必要がある。

## 書いてはならない主張の一覧

次を新規性として書くと、直ちに反証される。

| 書いてはならない主張 | 反証する文献 |
| --- | --- |
| 電源も電子部品も持たない3Dプリントの笛を複数本融合し、吹いた音の高さで情報を読む | Whoosh の FluteCase（ISWC 2016）、US4821670A、US5113784、US10147410B2 |
| 管の長さと音の高さの対応式にもとづいて笛を設計し実機で検証した | Printone（SIGGRAPH Asia 2016）、demakein、openwind、US5251569A の明細書背景 |
| 1つの印刷物から複数の音高を出す | Printone（指孔5個で9音）、US4821670A、Whistle Pan flute |
| 薄く小さくサポート材なしで鳴る平板型のフィップル笛を作った | Flat Pocket Whistle（Printables、ダウンロード97,000件） |
| 隣り合う記号が同じにならない制約を導入した | Goldmanら（Nature 2013）、Acoustic Barcodes（UIST 2012、0の連続禁止を明記） |
| 素数個の記号数を選んで有限体をそろえた | PDF417（929個の符号語）、Intelligent Mail Barcode、codex32（GF(32)） |
| Reed–Solomon符号を物理媒体に載せた | AirCode（冗長度40パーセント）、SeedQR（規格経由）、ggwave、codex32（BCH符号） |
| 電源不要の物理媒体に誤り訂正符号付きで秘密を格納した | codex32（BIP-93、しかも復号に電子機器を要しない） |
| 音の高さを記号として情報を運ぶ | Schenker（1960年、のちのITU-T勧告Q.23）、Dominguesら（2002年）、ggwave |
| 音の層に暗号学的な秘匿を求めない立場を打ち出した | HaleviとSaxena（CCS 2010）、Acoustic Integrity Codes（WiSec 2020） |
| 2枚そろって初めて意味を持つ物理媒体を作った | NaorとShamirの視覚暗号（EUROCRYPT '94）、大川直也さんと栃窪孝也さん（2026年） |
| 造形物に情報を埋め込む分野で秘密分散に言及したのは初めてである | Near-infrared Imaging（ACM TOG 2022、応用に明記） |
| 3Dプリント造形物への情報埋め込みで脅威モデルを持つのは初めてである | Secure Information Embedding in Forensic 3D Fingerprinting（2024年） |
| 日用品を暗号鍵にする | US9912477B2（IBM、ただし機構は正反対なので区別を明示すればよい） |

一方で、次は情報理論の等式として主張してよい。**隣接同音禁止のもとで13スロットから実効12通りへ落とす扱いは最適であり、余分な冗長は一切ない。** 1本あたり約0.115ビット（率で3.12パーセント）の減りは符号化の下手さではなく制約そのものの値段である。「隣接同音を禁じたq種類は制約のないq−1種類とまったく同じ量を運ぶ」という等式から、音域を半音1つ広げれば制約が容量の代償なしに手に入ることも言える。

## 脅威モデルに書き足すべきこと

現行の脅威モデルには2つの穴がある。

**穴1　「ネットワークから切り離して印刷する」という推奨は放射の経路に効かない。**

Chhetriらは造形機の音だけから工具経路と形状を復元し、軸の推定精度86パーセント、長さの推定誤差11.11パーセントを報告した（ICCPS 2016、拡張版はACM Transactions on Cyber-Physical Systems 2(1)、2018）。Jamaraniらは2024年に、離れた場所の市販の携帯電話の音響と磁界から軸方向の平均精度98.80パーセント、平均傾向誤差4.47パーセントに到達した。**CipherFluteは半音1段で実効長が約5パーセント変わるので、この誤差はスロットの粒度に並びつつある。** さらに攻撃者が復元した音列の誤りを、CipherFlute自身のReed–Solomon符号で訂正できてしまう危険もある。

Yocamらは2026年6月に、**CipherFluteが実際に使っているBambu Lab社の造形機2台を対象に**能動的なモータ騒音打ち消し機構を評価し、音響は無作為の基準値と区別が付かない水準まで潰れるが振動は残り、時系列モデルで約61パーセントの分類精度が出ると結論している。

Chhetriらの「Tool of Spies」（IEEE Transactions on Dependable and Secure Computing 18、2021）は、スライサを密かに書き換えるだけで側チャネルからの復元成功率が最大39パーセント上がると示す。CipherFluteはBambu Studio系のスライサと自作スクリプトを通しているため、**切り離すだけでは足りず、スライサとファームウェアの真正性を確かめるまで推奨に含める必要がある。**

Gatlinらの論文は表題が「Encryption is Futile（暗号化は無意味である）」であり、消費電力の波形から造形物の形状を復元している（RAID 2021）。データ経路を守っても物理量が漏れると述べており、査読者が必ず思い出す種類の論文である。

**穴2　X線CTによる無音の読み出しには国内の一次文献がある。**

中尾美月さんら（情報処理学会研究報告SLP、2026年2月）は、X線CTで尺八の3次元モデルを作り、輝度値ヒストグラムによる二値化と閉領域抽出で管の内径を補正して3Dプリンタで復元している。**笛の内径がCTで実用的な精度で復元できることの実証であり、CipherFluteの「計測・CT・透過撮影での無音読み取り」という記述の根拠になる。** ただし内径の復元になお差が残ると報告しているので、半音1段（管長でおよそ2ミリメートル台）を確実に分離できるとまでは書けない。

**あわせて書き足すべきこと。** 正規の読み出しと盗聴が同じ物理量を共有するため、利用者が吹いた音を録音されれば秘密が漏れる。この攻撃面は、鍵の挿入音から刻みを推定するSpiKey（HotMobile 2020）とKeynergy（USENIX Security 2021）が先に定式化している。Keynergyは75本の鍵で音響だけで候補を平均約75パーセント削減している。

## 数値で正確に言えること　比較表の新版

一次資料で確定した数値である。すべて本文または著者公開版で確認した。

| 研究 | 年 | 読み出しに要する装置 | 動作 | 実証容量 | 誤り訂正 | 脅威モデル |
| --- | --- | --- | --- | --- | --- | --- |
| InfraStructs | 2013 | テラヘルツ時間領域分光装置（約2分） | 受動（走査） | 27ビット | 無し | 無し |
| Acoustic Voxels | 2016 | スマートフォン1台 | 白色雑音を当てる／叩く | 4ビット | 無し | 無し |
| AirCode | 2017 | プロジェクタと単色カメラと偏光板（撮像3から4分） | 受動（撮影） | 約106ビット（2センチメートル角）、約500ビット（5センチメートル角） | 有り（リードソロモン、冗長度40パーセント） | 無し |
| LayerCode | 2019 | 一般的なカメラ | 受動（撮影） | 24ビット（近赤外の変種は12ビット） | 無し（あえて付けないと明記） | 無し |
| G-ID | 2020 | スマートフォンのカメラと小型光源 | 受動（撮影） | 7.672ビット（204通り）、14.065ビット（17,136通り） | 訂正無し（36通りのうち2通りを誤り検査に予約） | 無し |
| Acoustic Barcodes | 2012 | 圧電接触マイクロホン | 刻み目をなぞる | 誤り訂正後12ビット（4096通り）。生の符号長は最大24ビット | 有り（拡張ゴレイ、短縮BCH、短縮ハミング） | 無し |
| Lamello | 2015 | 接触マイクロホン | 櫛歯を弾く | 2.0ビット相当（櫛歯4枚で適合率93パーセント） | 無し | 無し |
| Blowhole | 2018 | ノートパソコンの内蔵マイクロホン | 息を吹き込む | 2.585ビット相当（6個を98パーセント）、上限9個で3.170ビット相当 | 無し | 無し |
| Seedmarkers | 2021 | 一般的なカメラ | 受動（撮影） | 23.437ビット（11,358,880通り） | 無し（著者自身が欠点と明記） | 無し |
| InfraredTags | 2022 | 自作の近赤外撮像モジュール（20ドル） | 受動（撮影） | 83.05ビット相当（21×21のQRコード） | QRコード規格の機能に依拠 | 無し |
| AnisoTag | 2023 | 自作の検出装置（レーザーと光導電素子16個、約10ドル） | タグを滑らせる | 51ビット（クレジットカードと同寸）、画像処理併用で160ビット | 記述無し | 無し |
| StructCode | 2023 | 一般的なカラーカメラ | 受動（撮影） | 76.08ビット、133.14ビット、228.23ビット | 無し（対応表の暗号化に一言だけ言及） | 無し |
| SoundOff | 2025 | 超音波マイクロホン（384キロヘルツ） | 日用品を普通に動かす | 3.907ビット相当（15個を93.75パーセント） | 無し | 無し |
| Whoosh の FluteCase | 2016 | スマートウォッチのマイクロホン | 吹く | 情報量の概念が無い（8鍵の選択） | 無し | 無し |
| **CipherFlute** | 2026 | スマートフォンのマイクロホン | 吹く | 3.7ビット／本、128ビット（40本から49本）、カード1枚で20.8ビット | 有り（リードソロモン、検査0本から4本以上を選択） | 有り |

この表を書くときの注意が2点ある。

第一に、**AnisoTagが自ら三者比較を本文に書いている。** 「同寸のタグで AnisoTag は51ビット、LayerCode は25ビット、acoustic barcode は40ビットを符号化する」である。クレジットカードと同寸の面での比較になるので、CipherFluteのカード実装（8本で20.8ビット）はこの3つの数字と直接並べられる。査読者はまずこの一文を持ち出すと考えられるので、先に自分から書いて「カード1枚あたりの密度では劣り、その代わりに符号が外観に現れない」と述べるのが正しい。

第二に、Blowholeの予稿集のファイル名は `gi2018-18.pdf` である。`gi2018-16.pdf` はFittsの法則に関する無関係な論文であり、番号を誤ると存在しない引用になる。

## 残る穴と、投稿前にやるべきこと

**優先度が高いもの。**

1. Whoosh の論文に付随する動画を確認する。本文に安全性の分析が皆無であることは確定したが、動画で認証の実演が本文より踏み込んでいる可能性は排除できていない。
2. 学校法人幾徳学園の特許第6537049号と、丸井智敬さんの特許第5620594号の請求項の日本語原文を確認する。J-PlatPatはJavaScriptで動くため機械的に取得できず、人が操作して読む必要がある。前者は「所望の情報を示す形状を秘密裡に付加する」という広い書き方であるため、栗原さんご自身の判断のためにも価値がある。
3. 国際特許分類による網羅的な走査を行う。とくにG10K5/00（気流で駆動される発音装置）、G06K19/06（記録担体の標識の種類）、B33Y80/00（付加製造による製品）、H04L9/08（鍵の管理）である。今回はキーワード検索のみであり、請求項の言い回しが想定と違う特許は原理的に取りこぼしている。
4. 上海交通大学の水中音響バーコード3件の請求項の中国語原文を確認する。「幾何が共鳴位置を決め、位置の並びが二進符号になる」という点で原理的に最も近い。

**優先度が中程度のもの。**

5. WISSの2013年以前を走査する。トップページに2000年から2013年の予稿集へのリンクが並んでいる。綾塚祐二さんと暦本純一さんの「Active CyberCode」（WISS 2005）と、加藤邦拓さんと宮下芳明さんの「紙窓」（WISS 2013）は、物理的な符号設計という観点で近い可能性がある。
6. WISSの2016年と2018年の関連候補13件の本文を読む。この2年は高橋治輝さんと宮下芳明さんによる造形挙動の研究が集中しており、CipherFluteの造形上の主張を支える国内先行研究が埋もれている可能性がある。
7. 日本音響学会の研究発表会講演論文集（春季・秋季）と音楽音響研究会の資料を走査する。J-STAGEにも情報処理学会電子図書館にも収録されておらず、笛の音響と3Dプリントを扱う発表が最も出やすい場所のひとつである。
8. 電子情報通信学会の技術研究報告を走査する。今回はCiNii Research経由のみで、抄録に該当語を持つ発表を取りこぼしている可能性がある。今井政敬さんと茂出木敏雄さんらのX線CTによる造形物内部の二次元コード検出（2013年11月）は本文に到達できていない。
9. 音響の秘密分散の国内の系譜3件（野口洲さんら2019年、藤田倫弘さんら2004年）の本文を確認する。とくに「ステガノグラフィック音響秘密分散法」はCipherFluteの偽装の主張と重なる可能性がある。
10. 新たに見つかった4件（Near-infrared Imaging、Tubes Among Us、Keynergy、Break-Resilient Codes）の被引用をたどる。いずれも新規性の核心に触れる。
11. 「音響で認証する」系譜の3名（雨坂宇宙さんと志築文太郎さん、村尾和哉さん、渡邉拓貴さん）を深掘りする。第2段階の途中で浮かんだが着手できていない。

**方法上の知見として記録しておくべきこと。**

情報処理学会電子図書館は、検索画面の裏にあるWEKO3のREST API（`https://ipsj.ixsq.nii.ac.jp/api/records/?q=キーワード&size=100`）が認証なしでJSONを返すため、機械的に走査できる。収録件数は221,341件で、題名だけでなく抄録も検索の対象になる。第1段階の複数の担当が「JavaScriptで動くため走査できない」と報告していたが、これは誤りであった。

インタラクションの予稿集は `http://www.interaction-ipsj.org/proceedings/年/` の形式で年を直接URLに入れる必要がある。トップページは最新年の開催ページへ転送するだけで過去の年へのリンクを持たない。

WISSの予稿集は `https://www.wiss.org/WISS年Proceedings/` の統一形式で2014年から2025年まですべて取得できる。
