qurihara/ai-fue/related_work_survey/raw4/check-claims.md

# 草稿の過大主張の検証

対象は `/paper/cipherflute_wiss2026_v2_draft.md`（2026年7月30日の白紙書き直し版）である。
検証日は2026年7月30日である。
根拠として `related_work_survey/PAPER_REVISION.md`、`REVIEW_AND_REPOSITIONING.md`、`raw2/`、`raw3/`、
および `fue/` の実装コードを使った。行番号は草稿のものである。

## 総合の判定

論旨の重心を「読み出しに機械が要らないこと」へ移した書き直しは成功しており、
先行研究に対する態度も旧版より格段に正直になった。とくに2.1節でAirCodeとInfraredTagsの
外部開口ゼロを自分から書き、2.3節で管長と音高の設計に新規性がないと明言し、
2.5節でcodex32を「明確な先例」と認めたところは、査読で崩れない書き方である。

ただし**投稿前に必ず直すべき箇所が9件残っている**。内訳は次のとおりである。
第一に、`PAPER_REVISION.md` の「書いてはならないこと」の第1行にあたる文が、
2.5節にそのままの形で残っている。第二に、2.2節の締めくくりの一文が、
草稿自身の表1と正面から食い違っている。第三に、本稿の中心主張である
「鍵盤楽器とコームで読める」ことの実証が5.4節で空欄のまま「実機で確かめた」と
断言されている。第四に、128ビットについて未実施だと5.3節が書いているのに、
概要と表1と2.1節が実証済みと読める書き方をしている。第五に、
旧稿で否定された「息の強さは基準笛との比で打ち消される」という主張が
3.2節と6.1節に生き残っており、3.3節・5.2節・6.3節と矛盾している。

---

## 第1部　「書いてはならないこと」13件の逐一の点検

`PAPER_REVISION.md` の112行目から130行目の表にある13行を、1件ずつ草稿に当てた。

### 1　「隠蔽と可読性の両立は光学符号には原理的に得られない」　→　**抵触している**

2.1節（73行目）では正しく撤回できている。

> AirCodeもInfraredTagsも**外部に開口をいっさい持たない**。したがって「光学的な符号は表面に露出していなければ読めない」という主張は成り立たず、読み出しの速さでも本手法が優位に立つわけではない。

ところが2.5節（123行目）で、同じ文が肯定形で復活している。

> **そしてこれらに共通する制約が、本研究の位置づけを定める。** 光学的な符号は表面に露出していなければ読めない。

これは `PAPER_REVISION.md` 118行目の禁止事項そのものである。
`raw3/c1-optical-hidden.md` の294行目から298行目が「反論は正しい。主張Aは成立しない」と結論し、
`raw3/c2-thermal-and-viewangle.md` の252行目も「『光学的な符号は表面に露出していなければ読めない』——誤りである。
InfoPrintとAirCodeが反証している」と書いている。
2.1節と2.5節が同じ論文の中で正反対のことを言っているので、査読者は必ずここを突く。

**直し方。** 2.5節の当該文の主語を、秘密の物理保管に使われている担体に限定する。
たとえば「秘密の物理保管に使われてきた担体では、符号が表面に露出していなければ読めない」と書き、
続けて「ただし2.1節で述べたとおり、造形物への情報埋め込みの分野では、
外部に開口を持たないまま読める光学的な符号が実現している」と一文を足す。

### 2　「光学方式は読み出しが遅い」　→　抵触していない

2.1節（73行目、75行目）が、AirCodeの3分から4分を装置の性質として書き分け、
InfraredTagsの6ミリ秒から14ミリ秒を明記し、
「読み出しの速さでも本手法が優位に立つわけではない」と自分から書いている。
6.3節（351行目）でも読み出しの速さで劣ると認めている。問題はない。

### 3　「基準体との比による正規化に前例がない」　→　抵触していない（ただし穴が1つある）

1.3節の第三の貢献（61行目）と3.3節（175行目）が、
`raw3/c3-reference-resonator.md` の156行目が示した書き換え案とほぼ同じ文になっている。
共鳴型センサの分野で確立した原理の移植であると明示できている。

ただし `raw3/c1-optical-hidden.md` の304行目から314行目が見つけた反例、すなわち
**AirCodeが符号格子の中に既知の値のセルを散らして復号器をその場で訓練し、
特徴ベクトルを局所的な明るさに合わせて正規化している**ことに、草稿は一言も触れていない。
これは草稿の第三の貢献の言い方（同じ物体に既知の基準を同居させ、離散した記号の復号に使う）に、
共鳴型センサの反例よりもはるかに近い。同じ造形物への情報埋め込みの分野の中にある反例である。
`raw3/c1` の383行目も「基準笛の自己補正について『前例がない』とは書かない。
AirCodeが既知ビットによる現場訓練という形で同種の仕組みを持っている」と指示している。
草稿は「前例がない」とは書いていないので禁止事項には抵触しないが、
最も近い反例を挙げないまま貢献を主張しているので、査読で持ち出されると弱い。

**直し方。** 3.3節に「造形物への情報埋め込みでも、AirCodeが符号格子に既知の値のセルを混ぜて
復号器をその場で較正している。本研究が違うのは、補正する物理量が担体の外にある気温であり、
演算が学習ではなく周波数の比である点である」という趣旨の2文を足す。

### 4　「100ビットを超える秘密を電源なしの日用品に埋めた先行研究がない」　→　抵触していない

2.1節（81行目）がDNA-of-thingsを挙げ、老眼鏡のレンズに1.4メガバイトを電源なしで埋めたこと、
著者自身が用途としてステガノグラフィを挙げていることを書いている。
`raw3/c4-dna-of-things.md` の47行目から57行目の抄録原文と一致する。問題はない。

### 5　「半音格子を符号語彙にした例がない」　→　抵触していない

2.2節（89行目）が「半音の格子で受動的な多管構造を作るという設計は、2016年に既に示されている」と
自分から書き、管長の式 L = 14.956 × 2^(i/12) を引用している。
`raw2/v1-whoosh-flutecase.md` の97行目の原文と一致する。問題はない。

### 6　「電源も電子部品も持たない3Dプリントの笛を複数本融合し吹いて読む」　→　抵触していない

2.2節がFluteCaseを最も近い物理機構として明示し、差分を「情報の向き」に絞っている。
`raw2/v1` の190行目の判断と一致する。問題はない。

### 7　「管長と音高の対応式にもとづいて設計し実機で検証した」　→　抵触していない

2.3節（103行目）と3.1節（161行目）の両方で、対応式も端の補正も本研究の寄与ではないと明記している。
`raw2/v2-printone.md` の263行目の指示と一致する。問題はない。

### 8　「1つの印刷物から複数の音高を出す」　→　抵触していない

2.3節（101行目）がPrintoneの指孔5個で9音の作例を挙げている。
`raw2/v2` の89行目のDOUGHNUTの記述と一致する。問題はない。

### 9　「薄くサポート材なしで鳴る平板型のフィップル笛を作った」　→　抵触していない（むしろ弱めすぎている）

2.3節（107行目）が「平板型のフィップル笛を融合するという造形上の工夫も、本研究の新規性ではない」と
書いている。禁止事項には抵触していない。ただしこれは第3部で述べるとおり弱めすぎである。

### 10　「隣り合う記号が同じにならない制約を導入した」　→　抵触していない

3.4節（183行目）がAcoustic BarcodesとDNA保存の両方を先例として挙げ、
「記号数を4から実効3へ落とす数え方まで一致する」と書いている。
`raw2/f6-key-numbers.md` の381行目から385行目の指摘と一致する。問題はない。
そのうえで最適性を主張しているが、これは `raw2/v4-constraint-codes-visual-crypto.md` の
58行目と131行目が一次資料で確定した内容であり、`PAPER_REVISION.md` 84行目も許している。
log₂12 − log₂11 = 0.1255 という数値も自分で計算して確かめた。

### 11　「電源不要の物理媒体に誤り訂正符号付きで秘密を格納した」　→　抵触していない

2.5節（119行目）が「明確な先例がある」と書き、codex32の検査符号の能力まで正確に引いている。
`raw2/v3-codex32-seedqr.md` の54行目から66行目の表と一致する。
「復号に電子機器をいっさい要しない点で、本研究より徹底している」と自分から書いているのは強い。問題はない。

### 12　「この分野で脅威モデルを持つのは初めてである」　→　**実質的に抵触する恐れがある**

1.3節の第四の貢献（63行目）は次のとおりである。

> 造形物への情報埋め込みの分野で、攻撃者の能力を列挙して守れない範囲を宣言した研究は数少ない。

「初めて」とは書いていないので字面では禁止事項を避けている。
しかし `PAPER_REVISION.md` 110行目は、
**Secure Information Embedding in Forensic 3D Fingerprinting（2024年）が明示的な攻撃者モデルを置いていることを注記せよ**と
指示しており、草稿はこの文献を本文でも参考文献でも一度も挙げていない。
2.5節でQR SafeShareの立場に触れているのは良いが、それだけでは指示を満たしていない。
「数少ない」と書いたうえで例外を1件も示さないと、査読者は「調べていない」と読む。

**直し方。** 4章の冒頭か1.3節の第四の貢献に、
「明示的な攻撃者モデルを置いた先例としてSecure Information Embedding in Forensic 3D Fingerprintingがあり、
物理層の役割を労力の引き上げに限定する立場はQR SafeShareが先に公開している」と1文で書く。

### 13　「網羅的に探して存在しなかった」　→　**部分的に抵触している**

1.3節（57行目）は正しく「この2つの性質を同時に満たす担体は、今回の調査の範囲では見つからなかった」と
書けている。ここは合格である。

しかし次の3か所は、範囲を限定しないまま断定している。

- 2.2節（97行目）の「**これらのいずれも、記号の列を符号語として読む設計、誤り訂正、
  基準となる音による正規化、秘密情報を扱う議論を持たない。**」（第2部で詳述する。事実としても誤りである）
- 2.1節（83行目）の「本研究は、**開けずに、専門の設備なしで、持ち主自身がその場で、
  繰り返し読み出せるという条件を保ったまま**、128ビットに到達する位置にある。」（第2部で詳述する）
- 1.3節（57行目）の前段「日用品に隠せる既存の担体はいずれも専用の読み取り装置を要し、
  機械なしで人が読める既存の担体はいずれも符号が見えている」（「いずれも」という全称）

---

## 第2部　投稿前に必ず直すべきもの

### A　2.2節の締めくくりが、草稿自身の表1と矛盾している（97行目）

> **これらのいずれも、記号の列を符号語として読む設計、誤り訂正、基準となる音による正規化、秘密情報を扱う議論を持たない。**

2.2節はAcoustic Barcodes、Lamello、Acoustruments、Acoustic Voxels、SoundOff、FluteCase、Blowholeを
列挙した節であるから、「これらのいずれも」はこの7件を指すと読まれる。
ところが**Acoustic Barcodesは誤り訂正を実際に実装している**。
草稿自身が87行目で「6ビットから24ビットの符号長に対して拡張ゴレイ符号や短縮BCH符号を掛け」と書き、
表1（142行目）でも誤り訂正の欄に「拡張Golay等」と書いている。
`raw2/f6-key-numbers.md` の354行目も「24ビットに拡張ゴレイ符号、12ビットに短縮(15,7)BCH符号、
6ビットに短縮(7,4)ハミング符号」と一次資料で確定している。
さらにLamelloは、草稿自身が87行目で書いているとおり
「離散した基本周波数の集合をド・ブラン列の字母として扱う」ので、
「記号の列を符号語として読む設計」を持っている。

同じ節の中で数行前に書いたことを、締めの一文で否定している。ここは最も安く突かれる誤りである。

**直し方。** この一文を次のように書き分ける。
「これらのうち誤り訂正を実装しているのはAcoustic Barcodesだけであり、
その実効データ量は12ビットにとどまる。記号の列を符号語として扱う設計はLamelloのド・ブラン列にあるが、
これは位置と向きを決めるためのものであって、外部から与えた値を運ぶものではない。
基準となる音による正規化と、秘密情報を扱う議論は、いずれの研究にも見当たらなかった。」

### B　中心主張の実証が空欄のまま「実機で確かめた」と書いてある（305行目から307行目）

5.4節は次のように始まる。

> **3.5節で述べた経路2と経路3を実機で確かめた。**
>
> 【要記入：ここに実演の記述を入れる。（後略）】

断言の文が先に置かれ、中身が【要記入】である。
本稿は1.2節（43行目から45行目）で「本質は、鍵盤楽器がひとつあれば人間が読めることにある」と宣言し、
1.3節の第一の貢献も、3.5節も、6.2節も、7章も、8章も、すべてこの一点に乗っている。
その唯一の証拠となる節が空である。
リポジトリの `git log` を40件さかのぼって確認したが、
鍵盤楽器または較正用コームによる復号の実演を行った記録は見つからなかった。

なお6.4節（369行目）は「本稿では実演を1回示すにとどめた」と書いており、
実演が済んでいることを前提にしている。ここも同時に直す必要がある。

**直し方。** 実演を実際に1回行って書くのが本筋である。
`REVIEW_AND_REPOSITIONING.md` の252行目が述べるとおり、
WISS 2026は統計を伴う評価を求めていないので、図1枚と短い記述で足りる。
どうしても間に合わない場合は、5.4節の見出しごと削り、
1.3節の第一の貢献と3.5節の経路2と経路3を「設計上そうなる」という記述に落とし、
6.4節に未実施であると書く。断言だけを残して中身を空にすることだけは避ける。

### C　128ビットについて、5.3節と概要・表1・2.1節が食い違っている

5.3節（301行目）は正直に書けている。

> **128ビットの構成については、片側24本の発音と、仮の基準に対する相対の位置が設計どおりであることを確認した段階である。49本を通した復号は未実施である。**

ところが次の3か所が、実証済みと読める。

- 概要（19行目）「フィラメントのスプール2枚に49本で128ビットを**載せた**」
- 表1（149行目）本研究の行の「**実証容量**」の欄に「3.5 bit/本、**計128 bit**」
  （表の見出しは133行目で「実証容量は原典の記載による」と定義されている）
- 2.1節（83行目）「本研究は、（中略）**128ビットに到達する位置にある**」

`PAPER_REVISION.md` の28行目が「実証していないことを実証したと書くのは、
引用漏れよりも重い正確性の失敗である」と書いているとおりで、
これは旧稿で指摘された過ちの再発である。とくに表1は、
先行研究の欄をすべて一次資料の実証値でそろえておきながら、
本研究の欄にだけ未実証の値を入れているので、表の定義に反している。

**直し方。** 表1の本研究の欄を「3.5 bit/本、実証は5本（誤り訂正なし）。
49本で128ビットを載せた物体は製造済みで、49本を通した復号は未実施」と書く。
概要は「載せた」を「載せた物体を製造した」に変え、
「49本を通した復号は未実施である」と1文を足す。
2.1節の位置づけの文は「128ビットを載せられる位置にある」と、能力の記述に変える。

### D　2.1節の位置づけが、草稿自身の表1にあるStructCodeに反証される（83行目）

> 本研究は、**開けずに、専門の設備なしで、持ち主自身がその場で、繰り返し読み出せるという条件を保ったまま**、128ビットに到達する位置にある。

草稿の表1（141行目）は、StructCodeの読出装置を「カメラ」、動作を「受動」、
実証容量を「最大228 bit」と書いている。
`raw2/f6-key-numbers.md` の360行目も「一般的なカラーカメラ（Pixel 2 の1220万画素、45センチメートル離して撮影）」
「リビングヒンジで21文字＝133.14ビット、大きなヒンジで36文字＝228.23ビット」と一次資料で確定している。
StructCodeは開けずに読め、専門の設備を要さず、持ち主がその場で繰り返し読め、
しかも228ビットに到達している。したがってこの4条件だけでは本研究の位置は空かない。

**直し方。** 条件に「符号を外観に現さないまま」を加える。すなわち
「符号を外観に現さないまま、開けずに、専門の設備なしで、持ち主自身がその場で、
繰り返し読み出せるという条件を同時に満たす範囲では、今回調べたかぎり本研究が最も大きい」と書く。
ただしこの書き方をすると、窓と吸込口が露出することとの整合を問われるので、
2.1節の73行目で既に書いてある「外観の露出という点では本手法のほうが多い」との関係を1文で結んでおく。

### E　「息の強さは基準笛との比で打ち消される」が3.2節に残っている（167行目）

> 印刷のばらつき（実測でおよそ11セント）、**息の強さによる音の動き（基準笛との比でほとんど打ち消される）**、測定自体の誤差がある。

これは `REVIEW_AND_REPOSITIONING.md` の25行目の指摘3、および
`PAPER_REVISION.md` の優先順位4（349行目）が「原理的に成り立たない主張である」として
削除を求めた記述そのものである。
しかも草稿は3.3節（179行目）で「**したがって息の強さの違いは、比を取っても消えない**」と、
5.2節（293行目）で「残る±24セントは、温度そのものよりも2回の測定での息の強さの違いに由来する」と、
6.3節（355行目）で「笛を1本ずつ吹く方式では、息の強さの違いを補正できない」と、
3回にわたって正反対のことを書いている。旧稿の内部矛盾がそのまま持ち越されている。

**直し方。** 括弧の中を「（比では消えないため、そのまま誤差に残る。3.3節を参照）」に変える。
そのうえで、刻み幅の設計の目安を残る誤差から計算し直す。
5.2節が実測した±24セントを使うと、100セントは4倍にわずかに届かないので、
「およそ4倍」という書き方も「残る誤差のおよそ4倍を目安とすると、
実測の±24セントに対して100セントはその境目にある」といった正確な記述に改める。

### F　6.1節の「速く吹いても音の高さは変わらない」も同じ矛盾である（339行目）

> 情報が音の高さに載っているため、こする速さや動かす速さに依存する方式よりも人間の操作のばらつきに強い。**音の高さは、ゆっくり吹いても速く吹いても変わらない。**

「速く吹く」は息の速さとも、笛から笛へ移る速さとも読める。
息の速さと読むと、`raw2/v2-printone.md` の68行目が引用したPrintoneの原文
「the sound is influenced by the speed of blowing (higher speed produces higher frequencies)」に反し、
草稿自身の2.3節（105行目）・3.3節・5.2節にも反する。

**直し方。** 「音の高さは、読み取る速さ、すなわち笛から笛へ移る速さには依存しない。
息の強さには依存するが、その量は3.3節と5.2節で扱う」と書き分ける。

### G　秘密分散の断片の本数が実装と合わない（221行目）

> 業界標準のSLIP-39 [12] に準拠すれば、断片1つが200ビットとなり**笛64本**を要するが（後略）

この文は `PAPER_REVISION.md` 187行目の承認済み文面をそのまま写したものだが、
その文面の数字自体が誤っている。
`REVIEW_AND_REPOSITIONING.md` の139行目は
「168ビットは笛64本、200ビットは笛75本になる」と書いており、200ビットに対応するのは75本である。
実装で確かめた。`fue/cipher_codec.py` を12スロット・隣接同音禁止・ブロックあたり検査2記号で回すと、
64ビットで26本、128ビットで49本、**168ビットで64本、200ビットで75本**になる。
128ビットで49本という草稿の数字は実装と一致するので、200ビットの64本だけが誤りである。

あわせて、`REVIEW_AND_REPOSITIONING.md` の139行目が指摘した
「円盤1枚あたり26本という上限に対して2枚に収まらず、円盤が3枚必要である」という帰結も、
草稿は書いていない。5.6節（323行目）が1枚26本の上限を書いているので、
読者は自分で割り算をして食い違いに気づく。

**直し方。** 「断片1つが200ビットとなり笛75本を要し、5.6節の円盤1枚26本の上限では
円盤が3枚必要になるが、標準の道具で復元でき（後略）」と書き換える。

### H　4.3節の側チャネルの数値が、量として結びついていない（255行目）

> 2024年には離れた場所の市販の携帯電話の音響と磁界から**軸方向の平均精度98.80パーセント**に達している [61]。本手法では半音1段が実効長の約5パーセントに対応するため、**この精度はスロットの粒度に迫っている。**

98.80パーセントは軸方向を当てる分類の正解率であり、寸法を何ミリメートルの誤差で復元できるかという量ではない。
分類の正解率と寸法の復元精度は次元が違うので、
「この精度はスロットの粒度に迫っている」という結論は導けない。
なお半音1段が実効長の約5パーセントという数字自体は正しい（2^(1/12) − 1 = 5.95パーセント）。

**直し方。** 「この水準の復元が管の長さの推定にまで及ぶかどうかは、本稿では確かめていない。
ただし半音1段が実効長の約6パーセントにすぎないため、脅威として見積もっておく必要がある」と、
未確認であることを明示した書き方にする。

### I　1.3節の第一の貢献の前半が全称になっている（57行目）

> 日用品に隠せる既存の担体は**いずれも**専用の読み取り装置を要し、機械なしで人が読める既存の担体は**いずれも**符号が見えている。

直後に「今回の調査の範囲では見つからなかった」と書いてあるので、
著者の意図としては調査範囲に限った主張だと分かる。
しかし2つの「いずれも」は範囲を限定していないので、字面としては
`PAPER_REVISION.md` 130行目の禁止事項に触れる。
`REVIEW_AND_REPOSITIONING.md` の44行目が
「延べ38のエージェントと3,153回の道具呼び出しは再現率の根拠にならない」と書いているとおり、
ここは形式的にも直しておくべきである。

**直し方。** 「今回調べた範囲では、日用品に隠せる担体はどれも専用の読み取り装置を要しており、
機械なしで人が読める担体はどれも符号が見えていた」と、範囲を先に置く。

---

## 第3部　過度に弱めて取りこぼしているもの

第2部とは逆に、一次資料の裏づけがあるのに書いていない、あるいは自分から否定してしまっている主張がある。
WISSは「デモや実装による有効性のアピール」を重視するので、
実装上の前進を捨てるのはもったいない。

### 1　Blowholeが捨てた道を復活させたことを書いていない

`raw2/v1-whoosh-flutecase.md` の234行目から238行目が、Blowholeの本文を引用している。

> 単純な管（たとえばWhoosh[16]で使われているもの）はどの向きでもよく印刷できたが、周波数の範囲を確保しようとするとすぐに、より小さな物体に埋め込むには大きすぎるものになった。

Blowholeはこの理由で直管を捨て、ヘルムホルツ共鳴の球状空洞に移った。
本研究の厚さ4ミリメートル・幅7ミリメートルという半割り断面は、
まさにこの問題への別の答えである。
`raw2/v1` の284行目も「数字で示せる工学的な前進である」と評価している。
草稿の3.1節は断面の寸法を書いているだけで、この対比をどこにも書いていない。

### 2　Printoneが分割と接着を要したことを書いていない

`raw2/v2-printone.md` の127行目が、Printoneの原文を引用している。
Printoneは空洞を作るために模型を手作業で半分に割り、別々に印刷し、
内部のサポート材を取り除いてから接着している。
本研究はサポート材なしの平置き一体印刷である。
`raw2/v2` の131行目が「Printoneが明示的に妥協した点をまさに解消するものであり、
CipherFluteの実装上の貢献としてはっきり主張できる」と書いている。
草稿の2.3節はPrintoneを引きながらこの差に触れていない。

### 3　フィップル笛を情報の担体に使った先例が見つかっていないことを書いていない

`raw/02-passive-acoustic-tags.md` の287行目は、
受動音響タグの励起方式を列挙したうえで
「フィップル笛は音量が大きく音高が安定するという利点があるが、
これを識別タグに使った先行研究は見つからなかった」と書いている。
草稿の2.3節（107行目）は「平板型のフィップル笛を融合するという造形上の工夫も、本研究の新規性ではない」と、
造形と用途を区別せずに全部を否定している。
造形としての新規性がないことは正しいが、
「情報の担体としての採用」までは否定されていない。

### 4　100セント刻みを外から裏づける数値を使っていない

`raw2/v2-printone.md` の166行目が、Ritzらの短報の一文を確定している。
既存の数理モデルによる指孔位置の解は、目標周波数に対して通常30セント程度の精度である。
これは本研究が100セント刻みを選んだ判断を、他人の言葉で裏づける材料になる。
`raw2/v2` の265行目も「100セント刻みという粗い量子化は妥協ではなく必然として読める」と書いている。
草稿の3.2節は自分の実測だけで刻み幅を正当化している。

### 5　Whooshの利用者依存性との対比を書いていない

草稿の2.2節（91行目）は、FluteCaseが利用者非依存で79.7パーセントに落ちることを書いている。
その原因が、周波数を測らずにメル周波数ケプストラム係数とサポートベクターマシンで
利用者ごとのスペクトル指紋を照合していることにある、という因果を書いていない。
`raw2/v1` の278行目が「Whooshはこの問題を利用者ごとの学習で回避しており、
物理で閉じる設計は前例が見つからない」と書いている。
基準笛を「機械学習ではなく物理で閉じる手段」として位置づけると、
第三の貢献が一段はっきりする。

### 6　音から管の内径を復元できることを、脅威モデルに結びつけていない

草稿の2.3節（101行目）は「測定した音響応答から内径の分布を復元する逆問題も解かれている」と書いている。
4.1節（235行目）は「吹かなければ読めない」を主張しない根拠として
尺八の計算機トモグラフィの研究だけを挙げている。
`raw2/v2-printone.md` の212行目が
「音を録るだけでも管の形状が推定できる技術が公開ライブラリとして存在するのだから、
『音を録られたら読まれる』という前提は誇張ではなく実在の技術に裏づけられている」と書いている。
2.3節と4.1節を結ぶ1文を足せば、脅威モデルの誠実さが具体的な技術に接地する。

### 7　隣接同音禁止が記号3種類以上でしか成立しないことを書いていない

`raw2/v4-constraint-codes-visual-crypto.md` の52行目は、
二進では隣接する記号を必ず変えると記号列が交互に並ぶだけになって容量が0になるので、
この制約が実用になるのは記号の種類が3以上のときだけであり、
音高を語彙にして種類を広げているからこそ払える代償だと書いている。
そして「この点は論文で述べる価値がある」と明記している。
草稿の3.4節は上限の式と最適性を書いているが、この観点を落としている。

---

## 第4部　WISSの査読者として最初に攻める3点

### 攻める点1　中心主張に証拠が1つもない

**攻め方。** 「本稿は概要と1章で、読み出しに特別な装置が要らないこと、
とくに鍵盤楽器ひとつで人間が読めることを唯一の中心主張として掲げている。
ところが5.4節はその実演の記述が空欄であり、本文のどこにも実演の結果がない。
中心主張が未検証のまま提出されている。
しかも著者自身が5.5節で、窓が真上を向かない向きでは音がやや濁り、
第3のピークが50セントから70セント高い側へずれると報告している。
うなりによる同音判定は基音どうしの干渉に依存するので、
倍音が濁る条件でこの判定が成立するかは自明ではない。
機械の経路では基音だけを見ればよいと著者は書いているが、
人間の耳は基音だけを取り出して聴くわけではない。
1回の実演すら示せないのであれば、第一の貢献は取り下げるべきである。」

**なぜ効くか。** 著者は「1回通ればよい」と自分で設計方針に書いているのに、
その1回が示されていない。反論の余地が最も小さい。

### 攻める点2　実証していない容量を、実証容量の表に書いている

**攻め方。** 「表1の見出しは『実証容量は原典の記載による』と定義されている。
先行研究13件はすべて一次資料の実証値で埋まっているのに、
本研究の行だけ『計128 bit』となっている。
一方で5.3節は『49本を通した復号は未実施である』と明記している。
同じ論文の中で、表と本文が違うことを言っている。
概要の『128ビットを載せた』も、2.1節の『128ビットに到達する位置にある』も同じである。
実証したのは4桁の数を5本の笛で往復させたところまでであり、
その構成には誤り訂正が付いていない（3.6節の表2によれば128ビット級はブロックあたり2記号の検査を要する）。
すなわち本稿は、49本という規模で誤り訂正付きの符号語が実際に読み切れるかを、
一度も示していない。
しかも著者は6.3節で、笛を1本ずつ吹く方式では息の強さを補正できないと構造的な限界として認めており、
5.2節の実測でも±24セントの残差が出ている。
半音の境界は±50セントであるから、49本のうち1本でも境界を越えれば記号の誤りになる。
本数が増えるほど、少なくとも1本が誤る確率は上がる。
その確率とパリティ2記号の訂正能力との収支が示されていない。」

**なぜ効くか。** 数字の突き合わせだけで成立し、著者の善意と無関係に指摘できる。
しかも「規模が上がると誤り率がどうなるか」という問いは、
この方式にとって本質的でありながら本稿がまったく答えていない。

### 攻める点3　空白のセルが、比較軸の選び方に依存している

**攻め方。** 「本稿の位置づけは『日用品に偽装でき、かつ機械なしで人が読める』という
2軸の空白セルに立っている。しかしこの空白は軸の選び方で作られている。
第一に、著者自身の表1にあるStructCodeは、普通のカメラだけで最大228ビットを読み、
開けることも専門の設備も要らない。本研究の128ビットを上回っている。
第二に、SeedQRは仕様書に手で転写するための印刷用ひな型を24点そろえており、
人間が桝目を数えて読むことができる。金属板に打刻して日用品と一緒に保管することもできる。
第三に、本研究は窓と吸込口という2つの開口を外気に露出させる必要があり、
AirCodeとInfraredTagsが開口ゼロであることを著者自身が2.1節で認めている。
したがって『日用品に偽装できる』の側でも本研究は最も優れているわけではない。
残るのは『符号が外観に現れず、かつ読み出しに電子機器が要らない』という、
2つの条件を同時に課したときの空白だけである。
その空白がなぜ研究として価値があるのかは、
機器の陳腐化に対する耐性という論拠に依存しているが、
本稿はその耐性を示す証拠を何も持っていない。」

**なぜ効くか。** 位置づけの表は本稿の骨格であり、
そこを崩されると貢献の4点が同時に弱くなる。
また `REVIEW_AND_REPOSITIONING.md` の264行目が
「『誰が、いつ、なぜそれを必要とするのか』の論証が現時点でゼロだからである」と
自認しているとおり、著者側に用意がない論点でもある。

---

## 第5部　確かめて問題がなかったこと

以下は根拠に当たって確かめ、誤りが見つからなかった箇所である。

**物理と数値の計算。** 自分で計算して一致を確認した。
気温が10度変わったときの音速の変化は1.69パーセント、セントに直すと29セントであり、
草稿3.3節の「約1.7パーセント、半音の約3割」と一致した。
5.2節の25.2度から41.0度への予測値は44.7セントであり、草稿の「約45セント」と一致した。
半音1段の管長の比は5.95パーセントであり、4.3節の「約5パーセント」とおおむね一致した。
log₂11 = 3.459、log₂12 − log₂11 = 0.1255 であり、
3.6節の「3.46ビット」と3.4節の「約0.13ビット」に一致した。
2キロヘルツ帯で1セントが約1.2ヘルツであることも計算で確かめた。

**符号化の本数。** `fue/cipher_codec.py` を12スロット・隣接同音禁止・ブロックあたり検査2記号で実行し、
128ビットが基準笛込みで49本になることを確認した。
本立ての64ビットは、`fue/bookstand_flutes.py` の既定である検査4記号で計算すると36本になり、
5.6節の記述と一致した。
カードの20.8ビットは、`fue/cipher_cardpair.py` の21行目から24行目にある
「パリティ1 … 記号6個・20.8ビット」と一致し、6 × log₂11 = 20.76 も計算で確かめた。

**較正定数。** 3.1節の A = 91891.5、e = 14.23 は、
`fue/cipher_codec.py` の34行目と35行目の既定値と一致した。
厚壁ヘッドの A = 86718、e = −11.81 も `PAPER_REVISION.md` 178行目と一致した。
草稿が【要確認】を付けているのは適切である。

**スロット体系の食い違いの注記。** 3.2節の【要確認】が指摘する
「復号ページの既定はG#6からF#7の11スロット」は、
`docs/cipher/cipher_config.json` の内容（`lo_note: G#6`、`hi_note: F#7`、`ecc_parity: 0`）と一致した。
符号化側の12スロットは `fue/cipher_card.py` の31行目、`fue/spool_128bit.py` の41行目、
`fue/bookstand_flutes.py` の49行目のいずれも `SLOT12 = dict(lo_note="G#6", hi_note="G7")` であり、
草稿の記述と一致した。注記の内容は正確である。

**先行研究の数値。** 表1の各行を `raw2/f6-key-numbers.md` の347行目からの一覧表と突き合わせ、
InfraStructsの27ビット、AirCodeの約500ビット（5センチメートル角）、LayerCodeの24ビット、
InfraredTagsの約83ビット、StructCodeの最大228ビット、Acoustic Barcodesの訂正後12ビット、
Acoustic Voxelsの4ビット、Blowholeの約2.6ビット相当、SoundOffの約3.9ビット相当が
すべて一致することを確認した。
Lamelloの「約2ビット相当」も同記録の355行目と一致した。
AnisoTagの三者比較（51ビット、25ビット、40ビット）も同記録の227行目と一致した。
SoundOffの「1277通りの候補から選んだ15個」も同記録の242行目から250行目と一致した。
Blowholeの予稿集のファイル名が `gi2018-18.pdf` であることも、
`PAPER_REVISION.md` 157行目の警告どおりに正しく書かれている。

**国内研究の記述。** 久保らの「8個を平均99.3パーセント」は
`REFERENCES_TO_ADD.md` の101行目と一致した。
上平らの「2014年から」は、`raw2/f4-jp-researchers-deep.md` の324行目にある
2014年6月と2014年9月の和文発表と一致した。
「数百ビット」も `SURVEY.md` 47行目と一致した。
宮武らの記述も `SURVEY.md` 47行目と一致した。
大川と栃窪の書誌（情報処理学会論文誌デジタルプラクティス第7巻第2号、2026年）は
`REFERENCES_TO_ADD.md` の180行目と一致した。

**codex32の記述。** 2.5節の「13文字の検査符号は8文字以内に影響する任意の誤りを検出し、
置換4文字までと消失8文字までを訂正する」は、
`raw2/v3-codex32-seedqr.md` の58行目からの表と一致した。
「作者自身が、対応する財布が存在しないので本物の金銭に使わないよう警告している」も
同記録の46行目と一致した。

**QR SafeShareの記述。** 2.5節の引用「素早い走査や気づかれない走査を防ぎ、
許可の無い読み出しに必要な労力を上げる」は、
`raw2/v3` の167行目にある原文の訳と一致した。
「日用品への偽装は謳っておらず、物理層の対策は錠つきの覆いという露骨な障壁の一点である」も
同記録の195行目と一致した。

**Whooshの記述。** 2.2節の管長の式、利用者非依存の79.7パーセント、
管長が定数として公開され全複製が同一形状になることは、
`raw2/v1-whoosh-flutecase.md` の97行目、163行目、190行目とそれぞれ一致した。
また `REVIEW_AND_REPOSITIONING.md` の147行目から155行目が、
付随動画を全編確認して「FluteCaseを使った認証の実演は存在しない」と結論しているので、
草稿がFluteCaseを記憶媒体ではなく鍵盤だと位置づけていることに問題はない。

**隣接同音禁止の最適性。** 3.4節の log₂(q−1) という上限と、
差分の写像が有限長でもこれを達成するという主張は、
`raw2/v4-constraint-codes-visual-crypto.md` の58行目と131行目が
一次資料で確定した内容と一致した。
「音域を半音1つ広げれば容量の代償なしに手に入る」も、
13スロットで log₂12 = 3.585 となって12スロットの無制約の容量に等しくなることを計算で確かめた。

**脅威モデルの4つの「主張しないこと」。** 4.1節の4項目は、
いずれも `SURVEY.md` と `REVIEW_AND_REPOSITIONING.md` の記述より弱い形で書かれており、
過大主張は見当たらなかった。
とくに尺八の計算機トモグラフィについて
「内径の復元になお差が残ると報告しているため、半音1段の差を確実に分離できるとまでは言えない」と
括弧書きで留保しているのは、この草稿で最も誠実な記述の1つである。
偽装について「探索コストをいくらか引き上げる」までに限定し、
反証側の証拠（隠す側の選択が体系的に予測されうるという実験）まで自分から挙げているのも良い。

**4.2節のエントロピーの議論。** 20.8ビットの秘密を鍵にしても強度は20.8ビットのままであること、
鍵導出関数の強化は費用を定数倍するだけであることは、
`REVIEW_AND_REPOSITIONING.md` の135行目にあるNIST SP 800-132 付録A.2.2 の記述と一致した。
SLIP-39が検証手段を意図的に持たないことによる否認可能性の記述も、同191行目と一致した。

---

## 第6部　致命的ではないが直したほうがよいもの

1. **2.1節（73行目）のInfraredTagsの250センチメートル。**
   `raw3/c1-optical-hidden.md` の240行目から247行目によれば、
   250センチメートルは4×4のArUcoマーカーについて幅10ミリメートルから80ミリメートルまで振って
   測った最大値であり、21×21の二次元コードの復号精度は15センチメートルから80センチメートルの範囲で
   79.03パーセントである。草稿はこれを二次元コードの数値のように書いている。
   先行研究を実際より強く書いているので、本研究の主張を弱める向きの不正確さだが、直しておくとよい。

2. **2.1節（77行目）のInfoPrintの材料。**
   `raw3/c2-thermal-and-viewangle.md` の47行目によれば、
   InfoPrintは2ヘッドの熱溶解積層機を使い、情報の層に白いポリ乳酸、
   母材に黒または青のポリ乳酸を使い分けている。
   充填率20パーセント以下、深さ1ミリメートルまで、平らな面に限るという制約もある。
   「一般的なフィラメントだけで」という書き方は、1.3節の第二の貢献
   （担体の材料と色を選ばない）と衝突しかねないので、制約を1つ添えるとよい。

3. **1.1節（35行目）の「既存の担体には共通の制約がある」。**
   概要（13行目）では紙、金属板、二次元コードの3つに限定できているが、
   1.1節では範囲が示されていない。「秘密の保管に使われてきた担体には」と限定を足すとよい。

4. **4.2節の112ビットという境目。**
   根拠が示されていない。安全性強度の慣行に由来する数字であれば出典を添える。

5. **3.2節の「印刷のばらつき（実測でおよそ11セント）」。**
   5.1節（283行目）の本文は、同じ音の3本の散らばりが11.0セント、
   同じ笛を繰り返し吹いたときのばらつきが15.2セントであり、
   「造形そのもののばらつきは多くとも11セント程度」と上限として書いている。
   3.2節はこの上限を推定値のように使っている。安全側なので害はないが、
   「多くとも11セント」と書き方をそろえるとよい。

6. **5.5節の印刷の向きの結果に、層の厚さの条件が書かれていない。**
   本文は0度から±135度までが鳴ると書いているが、
   この結果が層の厚さに依存しないのかどうかが示されていない。
   実験に使った層の厚さを1文で添えるとよい。

7. **5.6節のハート形のカードの乱数。**
   `fue/cipher_cardpair.py` の162行目は `rnd = (7 ** n) % span` であり、
   コメントに「記録のため決め打ちのデモ値」と書かれている。
   すなわち印刷済みの2枚組では、乱数ではなく固定値が使われている。
   リポジトリは公開なので、この2枚組は片方だけで秘密が求まる。
   草稿の「片方だけでは一様な乱数にしか見えず、秘密については何も分からない」は
   方式の説明としては正しいが、実物には当てはまらない。
   「実装のデモでは再現のために固定値を使っている」と1文添えるか、
   方式の説明であることを明示するとよい。

8. **5.6節のカードの容量。**
   20.8ビットは検査1記号のときの値である。
   2-of-3で使う `fue/cipher_card.py` の既定は検査2記号なので、
   そのカードは5記号すなわち17.3ビットになる。
   どちらの設定の話かを明示するとよい。

9. **8章（391行目）の「1台の機械が読んで他の人はそれを信じるしかない」。**
   二次元コードは、立ち会う人がそれぞれ自分の端末で独立に読める。
   したがって独立検証の可否そのものは差にならない。
   差は「装置を持たない人も検証に加われる」という点にあるので、そう書き直すとよい。

10. **6.1節の「マイクはすべてのスマートフォンに載っており」。**
    全称の断定である。「ほぼすべての」にとどめるとよい。

11. **参考文献[48]の書誌が未確定である。**
    `raw3/c3-reference-resonator.md` の15行目から18行目に完全な書誌がある。
    James H. Smith と Stephen D. Senturia、
    "Self-Consistent Temperature Compensation for Resonant Sensors with Application to
    Quartz Bulk Acoustic Wave Chemical Sensors"、TRANSDUCERS '95、724ページから727ページ、
    DOI 10.1109/SENSOR.1995.721934 である。

12. **5.6節の本立ての寸法と印刷実績（105×70×163.5ミリメートル、13時間09分、117グラム）。**
    リポジトリの中にこれらを裏づける記録を見つけられなかった。
    誤りだと判断する根拠はないので、疑いがあるという水準の指摘にとどめる。
    著者の手元の記録で確認していただきたい。

13. **3.4節の隣接同音禁止の動機。**
    `raw2/v4` の48行目は、Goldmanらが同一塩基の連続を避ける動機は誤り率の低減であり、
    本研究の動機は区切りの検出であって違うと指摘し、
    「機構はDNA保存の側、目的は自己同期の側」と書き分けるよう勧めている。
    草稿は動機の違いに触れていない。1文で足りる。
