qurihara/ai-fue/related_work_survey/raw4/check-completeness.md

# 草稿 v2 の充足性検査（WISS 2026 の査読者の立場から）

2026年7月30日作成。対象は `paper/cipherflute_wiss2026_v2_draft.md` である。行番号はこのファイルのものを指す。

## 検査の方法

草稿を全文読んだうえで、次を突き合わせた。`related_work_survey/` の4つの方針文書（`SURVEY.md`、`REVIEW_AND_REPOSITIONING.md`、`PAPER_REVISION.md`、`REFERENCES_TO_ADD.md`）と、生の調査記録（`raw/`、`raw2/`、`raw3/`）と、実装のコード（`fue/cipher_codec.py`、`fue/mini10.py`、`fue/cipher_card.py`、`fue/cipher_cardpair.py`、`fue/spool_128bit.py`、`fue/bookstand_flutes.py`、`fue/threshold.py`）と、設定（`docs/cipher/cipher_config.json`）と、復号ページ（`docs/cipher/index.html`）と、**実測の生記録（`out/` 以下の測定ファイル）** と、旧版（`paper/cipherflute_wiss2026_v1.2.docx` を展開したもの、および `paper/v11_text_dump.txt`）である。数値は手で検算した。

## 全体の判定

論の立て方は良い。旧版が抱えていた過大主張（実証していないことを実証したと書く、前例のある着想を前例がないと書く）は、ほぼすべて解消されている。`PAPER_REVISION.md` の「書いてはならないこと」13項目を本文と突き合わせたが、いずれも書かれていない。関連研究は旧版の3小節から6小節へ厚くなり、先行例を自分から認める書き方になっている。この点は査読者として高く評価する。

しかし現状では採録を推せない。理由は3つある。第一に、**論文が中心に据えた主張（読み出しに特別な装置が要らないこと）を支える実証が、1件も存在しない**。5.4節（303行目から307行目）が【要記入】のまま空いており、そこが論文の中心そのものである。第二に、**実機で起きた失敗と歩留まりが1つも書かれていない**。36本のコームのうち6本が鳴らず、26本のスプールは実機で復号に失敗している。誠実さを売りにする論文がこれを伏せるのは一貫しない。第三に、**国内の直系先行研究、とりわけWISSの直近の発表が複数落ちている**。

以下、依頼の5点に沿って述べる。

---

# 第一　中心の主張がどこまで裏づけられているか、5.4節に何を書くか

## 1-1　現状の裏づけの度合い

草稿は「読み出しに特別な装置が要らない」を中心に置き（43行目）、その本質を「鍵盤楽器がひとつあれば人間が読める」ことに置いている（45行目）。貢献の第一（57行目）も「読み出しに機械を必要としない秘密の担体を示した」である。

これを支える実証は、現状では**ゼロ**である。

- 5.3節の通し実証（297行目）は、スマートフォンの復号ページで読んだ記録であり、経路1の実証である。
- 5.4節（305行目から307行目）は【要記入】であり、経路2と経路3の記録は無い。
- 5.6節の担体（319行目から327行目）も、読み出しはすべて機械の経路である。ハート2枚の確認（325行目）も復号ページを使っている。

つまり、論文の中心の主張を支えるものは、いまのところ**理屈だけ**である。しかも305行目は「3.5節で述べた経路2と経路3を実機で確かめた。」と断定形で書いてあり、その直後が空欄である。この1文は、実演を行わない限り削らなければならない。書いたまま出すと虚偽の記述になる。

一方で、**材料はすべて揃っている**。12音（G#6からG7）の較正コームは既に印刷済みである（`out/calib_comb36_report_2026-07-28.txt`）。カード、本立て、スプール2枚、ハート2枚も印刷済みである。使う音域 G#6 から G7 は MIDI番号で92から103、周波数で1661ヘルツから3136ヘルツであり、88鍵のピアノ（最高音は C8 の4186ヘルツ）の上端の1オクターブに収まる。したがって実演は1日でできる。

## 1-2　5.4節に書くべきこと（具体案）

### 何を読ませるか

**カード1枚（笛8本）を使う。** 128ビットのスプールは使わない。6.2節（343行目）が自分で「128ビット級では人手のリードソロモン復号は現実的でない」と書いているので、そこで実演すると論旨がねじれる。カードは誤り訂正を1記号しか使わず、記号列がほぼそのまま秘密になるので、人の経路だけで完結する。

### 経路2（鍵盤楽器）に書く手順

1. 使った楽器の**機種と種別**を書く。電子鍵盤なのか、調律済みのアコースティックピアノなのかで話がまったく変わる（理由は1-3に述べる）。
2. 基準笛を吹き、鍵盤の C7（MIDI 96、平均律で2093ヘルツ）と重ねて、同じ高さになることを確認する。
3. 各データ笛について、隣り合う2つの鍵と順に重ね、どちらのうなりが遅いかで近い方を選ぶ。選んだ鍵を記録する。
4. 基準笛の鍵からの隔たりを符号つきの整数として数える。C7を基準にすると、G#6 から G7 までは −4 から +7 の範囲になる。
5. **隣接同音禁止の符号化を使っているので、この整数の列は記号の列そのものではない。** 直前の音を引き、さらに1を引いて11で割った余りを取るという逆写像を、1本ごとに行う必要がある（`fue/cipher_codec.py` の差分写像の逆である）。草稿の3.5節197行目は「得られた数の列がそのまま記号の列である」と書いているが、実装した担体（カード、本立て、スプール）はすべて `no_repeat=True` なので、この記述は正しくない。**5.4節では、この引き算1回を含めて手順を書く。** 引き算1回は誰にでもできるので、主張は弱まらない。
6. 得られた記号列を、あらかじめ控えた値と突き合わせて一致を示す。
7. **所要時間を1つ書く。** 8本を何分で読み終えたかである。

### 経路3（較正コーム）に書く手順

1. データ笛を1本吹き、コームを端から順に吹いて、うなりが消える位置を探す。
2. コーム上の位置がそのままスロット番号になる。基準笛の位置を0として数える。あとは経路2と同じである。
3. **注意点がある。** 既に印刷済みの較正コーム36本は、36本中6本が造形不良で鳴っていない（`out/calib_comb36_report_2026-07-28.txt` 68行目から69行目、鳴らなかったのは1番の G#6、2番の A6、3番の A#6、34番の C#7、35番の D7、36番の D#7）。実演にそのまま使うと、対照表に穴がある状態になる。**12音が1本ずつ並び、12本すべてが鳴ることを確認した「対照表コーム」を1本だけ刷り直してから実演するのが安全である。** これは半日でできる。
4. この経路の要点は「電子機器がどこにも登場しない」ことなので、写真にスマートフォンや計算機を写さない。

### 正直に書くべき制約（書かないと突かれる）

- **精度の根拠を、自分の実測に合わせる。** 1.2節49行目と3.5節199行目は「うなりが数ヘルツで聞き取れれば数セントの精度が出る」と書く。しかし5.1節283行目が報告する同じ笛を吹き直したときのばらつきは15.2セントであり、2キロヘルツ帯では約18ヘルツにあたる（`out/calib_comb36_report_2026-07-28.txt` 72行目）。**うなりの分解能ではなく吹奏の安定性が精度を決める。** 「数セント」は自分の測定と矛盾する。「同じ笛を吹き直したときのばらつきが15セント程度であり、スロットの刻み100セントに対して十分に小さい」と書き換えれば、実測に裏づけられたうえで主張の強さは変わらない。
- **ピアノは上の音域で厳密な平均律ではない。** 実用の調律では高音域が伸ばされるので、G#6 から G7 という最上部では数セントから十数セントのずれが乗る。基準笛からの隔たりが大きい音ほど差が開く。電子鍵盤ならこのずれは無い。**どちらを使ったかを書き、ピアノを使う場合は伸張の分を誤差の収支に足す。**
- **人が読めるのは記号列までである。** 誤り訂正の復号は含まない。これは6.2節に既にあるので、5.4節では繰り返さずに参照する。
- **耳と測定は食い違うことがある。** 旧版が印刷の向きの実験で「耳では高い音がよく鳴り低い音はかすれて聞こえたが、測定では低い音の方が安定していた。復号器が読むのは基音ひとつであるから、鳴っているかどうかを聴感で判断してはならない」と書いていた（`paper/v11_text_dump.txt` の縦置きの段落、v1.2 では5.4節の末尾）。**耳で読むことを中心に据えた新稿こそ、この観測を落としてはならない。** 5.4節の但し書きか6.3節の限界に置く。

### 図に何を写すか

1枚の図を3つの区画に分けるのが最も効率がよい。

- **左の区画。** 鍵盤の上にカードを置き、片手で鍵を押さえ、もう片方の手でカードを口へ運んでいる写真である。押さえている鍵に印を付け、基準笛が一致した鍵と、いま読んでいる笛が一致した鍵を色分けする。楽器の機種が分かる角度にする。
- **中の区画。** 較正コームとデータカードを並べた写真である。コームの何番目の笛と一致したかを、番号の対応で示す。**机の上に電子機器を1つも置かない。** これがこの区画の唯一の要点である。
- **右の区画。** 4行の表を置く。1行目に一致した鍵（またはコームの位置）の列、2行目に基準からの隔たりの列、3行目に逆写像を掛けた記号の列、4行目に控えてあった秘密の値を書く。音から数字が出て、それが秘密と一致したことが1枚で読み取れる。
- **図の説明文**に、使った楽器の名前、部屋の温度、8本を読み終えるまでの時間を書く。

### 実演を1回で足りるものにするための最小の補強

募集要項が評価実験を求めていないので統計は不要である。ただし著者1人だけだと「著者だから読めた」という疑いが残る。**著者以外の1人に同じ手順を行ってもらい、同じ記号列が出たと1文だけ書けば、この疑いは消える。** これ以上は不要である。

---

# 第二　査読者が当然あると期待するのに草稿に無いもの

## 2-1　実機の失敗と歩留まりが1件も書かれていない（最も重い）

**36本のコームのうち6本が鳴らなかった。** `out/calib_comb36_report_2026-07-28.txt` の68行目から69行目に「6本／36本」と記録されている。草稿の5.1節（283行目）は、この事実に一言も触れずにばらつきの数字だけを書いている。笛49本の担体を主張する論文が、16.7パーセントの不発率を伏せるのは通らない。

**26本のスプールは実機で復号に失敗している。** `out/spool_pass26_measured_2026-07-28.txt` の7行目に「消失1つと誤り1つは、パリティ2本では訂正できない（2\*1+1=3 > 2）。実際に復号は失敗した。」とある。原因は、10本目が鳴らなかったこと（消失1つ）と、G#6 のボアが設計より1.57ミリメートル短く1スロット高く読まれたこと（誤り1つ）である。同じ原因は `fue/mini10.py` の109行目から110行目にも記録されている。草稿の5.3節（301行目）は「49本を通した復号は未実施である」とだけ書き、**26本で実際に試して失敗した事実を書いていない。**

この2つを書かないことは、査読者が本文と公開リポジトリを突き合わせたときに最も心証を悪くする種類の欠落である。**逆に書けば強くなる。** 失敗から原因を2つ特定し、外形に余白を足して最低音のボアを設計どおりにする対策（5.1節285行目に既に書いてある内容がこれである）を打ち、対策後の再測で24本すべてが鳴って相対スロットまで一致した（`out/spool128_plate2_measured_2026-07-29.txt`）という流れは、そのまま工学の物語になる。あわせて、パリティ2記号では消失1と誤り1に耐えられないという設計上の教訓（3.4節187行目の「検査用の笛の本数は求める確実さに応じて調整できる」に実測の裏づけを与える）も書ける。

## 2-2　図と写真がほとんど無い

本文が触れる図は図1（39行目）、図2（159行目）、図3（173行目）の3枚だけである。**実装した4つの担体（カード、本立て、スプール2枚、ハート2枚）の写真が1枚も無い。** 復号ページの画面も無い（旧版には図4としてあった）。募集要項が重視するのは「デモや実装による有効性のアピール」であるから、物と画面が見えないのは致命的である。`paper/figs/` にあるのは旧版の図（`fig1_overview.png` から `fig5_decoder.png`）であり、新しい担体の写真ではない。

## 2-3　復号ソフトの説明が薄く、しかも1点は実装と食い違う

3.5節の経路1（195行目）は5行しかない。次が書かれていない。

- 音高推定の方式。実装は pitchy（McLeod法）である（`docs/cipher/index.html` 267行目）。
- 区切りの3方式。拍に合わせる方式、無音で切る方式、音が変わったところで切る方式がある（`docs/cipher/index.html` 110行目から137行目）。**このうち「音が変わったところで切る」方式は、3.4節183行目の隣接同音禁止と直結した実装であり、設計と実装が噛み合っていることを示す良い材料である。**
- 公開しているURL。
- 1本あたり、あるいは全体の所要時間。6.3節（351行目）は「読み出しにも時間がかかる」と書くだけで、数字が無い。

**そして「ネットワークがなくても動作する」（195行目）は、現在の実装と食い違う。** `docs/cipher/index.html` の267行目は pitchy を `https://esm.sh/pitchy@4` から読み込んでおり、`docs/cipher/` に vendor ディレクトリは存在しない。初回の読み込みにはネットワークが要る。一方 `docs/dapp/` は同じライブラリを vendor に同梱している。復号ページも同梱するか、本文の記述を弱めるかのどちらかが要る。1.1節33行目が「担体そのものが無傷でも、それを読む道具が失われれば、秘密は失われたのと同じである」と書いている論文なので、ここは実装で直すのが筋である。

## 2-4　較正定数の記述が実装と合っていない

3.1節（161行目）は「日用品への埋め込みに用いた外形統一版では A = 91891.5、e = 14.23 である」と書き、根拠として `fue/cipher_codec.py` の既定値を挙げている。しかし**外形統一版の較正は `out/cipher_mini10_calib.txt` にあり、A = 87985.1、e = −10.010 である**（同ファイルは「旧: A=88811.7 e=−8.612」とも注記している）。`fue/cipher_codec.py` の34行目から35行目の 91891.5 と 14.23 は別の笛の定数であり、`fue/compact.py` 30行目、`fue/fold.py` 26行目、`fue/plenum.py` 128行目が同じ値を共有している。

【要確認】の書き方が「挙げた2つのうちどちらを代表にするか」になっているが、**実際には挙げた2つのどちらも現行の外形統一版の値ではない。** 3つ目の値が正しい。

## 2-5　スロット体系の食い違いが2か所に残っている

- 3.2節（165行目）は12スロット（G#6 から G7）と書き、復号ページの既定が11スロットだと注記する。`docs/cipher/cipher_config.json` は `lo_note` が G#6、`hi_note` が F#7 なので、確かに11スロットである。設定をURLで渡しているので実害は無いという注記のとおりだが、**投稿版に【要確認】は残せない。** 既定をそろえるのが安全である。
- **より重いのは5.3節である。** 通し実証で使った5本は C7、G#6、F#6、G#6、C7 である（`out/cipher_roundtrip_demo_info.txt`）。F#6 は G#6 より低いので、**12スロット体系の外にある。** つまり唯一の通し実証は、3.2節が説明した体系ではなく13スロット体系（F#6 から F#7、`fue/mini10.py` 214行目の `CALIB13`）で行われている。このまま出すと、査読者が「実証したのは提案した符号ではない」と読む。対処は2つある。12スロットの担体（カードやハート2枚）で実証を取り直すか、5.3節に「これは13スロット体系で行った初期の実証である」と明記して、12スロットの実証はハート2枚（325行目）が担うと整理するかである。**後者なら追加の実験は要らない。**

## 2-6　秘密分散の記述と実装が合っていない

3.7節（221行目から223行目）は「断片の値128ビットのみで足り笛49本に収まる」と書いたうえで、「本研究の実装は後者である。2-of-3を3つの異なる日用品に分けている」と続ける。読者は128ビットの断片を3つの日用品に載せたと受け取る。しかし実装は次のとおりである。

- 2-of-3 の実装は `out/threshold_2of3_carriers.txt` にあり、秘密は124816（11進5桁、およそ17ビット）で、箱とカードと本立てに笛8本ずつ載せている。しかも復元の確認は同ファイル末尾のとおり「理想周波数で往復」、すなわち計算機上の模擬である。**実機で3つの担体から復元した記録は無い。**
- 128ビットのスプール2枚は秘密分散ではなく、1つの符号語を2枚に割ったものである（`fue/spool_128bit.py` の3行目から5行目）。
- `fue/threshold.py` の18行目は「断片1つは秘密と同じ大きさ」と書いており、17ビットの秘密の断片は17ビットである。

この3つを混ぜずに書き分ける必要がある。現状の書き方は、旧版で指摘されたのと同じ種類の過大主張になっている。

## 2-7　脅威モデルから攻撃者が2つ消えた

旧版の表4には「復元の場の盗聴者：録音1回で断片を複製」と「所有者への強要：守れない」があった（`paper/v11_text_dump.txt` の表3、v1.2 では表4）。**新稿の4章にはどちらも無い。**

新稿は「人間が耳で読める」ことを中心に据えたのだから、その裏返しとして「聞こえた人も、録音した人も読める」ことは、査読者が最初に思いつく反論である。しかも**公開している復号ページ自身が「吹いた音は聞こえるので、その場にいる人や録音した人には秘密が伝わります」と明記している**（`docs/cipher/index.html` 88行目）。4.4節の主張4（264行目）は同じ性質を長所としてだけ述べており、片面しか書いていない。1文で両面を書けば、むしろ論文の誠実さが増す。

## 2-8　偽装の主張と、実際に刷った素材が食い違う

5.6節（321行目）は本立てを「透明グレーのPETGで印刷して」と書き、5.3節（299行目）も透明なPETGを挙げる。透明なら内部の管の長さが外から見えるので、1.2節39行目と6.3節351行目が置いている「符号が外観に現れない」という前提が崩れる。**旧版はこれを自覚しており、「透明な素材は印刷品質の確認には便利だが、管が透けて見えるため偽装の観点では不利である」と書いていた**（`paper/v11_text_dump.txt` の3.6節）。新稿はこの1文を落としたまま透明の実装を並べている。1文で戻す。

## 2-9　聴覚に関する包摂の議論が無い

中心の主張を「人間が耳で読める」に移した以上、聴覚に障害のある利用者にとってその経路が使えないことを1文で述べ、機械の経路が併存するので排除にはならないと書く必要がある。`REVIEW_AND_REPOSITIONING.md` の246行目が同じことを指摘している。6.4節（363行目から373行目）の今後の課題にも無い。

## 2-10　参考文献が完成していない

本文は [1] から [62] まで番号を使うが、末尾の一覧（399行目から426行目）は約25件しかなく、しかも【整理中】と明記されている。投稿版では全件が解決している必要がある。とくに**[48] は「Smith, J. and Senturia, S.:（基準共鳴器との比による共通モード除去、1995年）」という書誌未確定の形である**（423行目）。貢献の第三（61行目）と3.3節（175行目）がこの1件に全面的に依存しているので、書誌が確定しないと貢献の記述が宙に浮く。正しい書誌は `raw3/c3-reference-resonator.md` の15行目から18行目にある。Smith, J. H. and Senturia, S. D.、Proceedings of TRANSDUCERS '95、724ページから727ページ、IEEE、1995年、DOI は 10.1109/SENSOR.1995.721934 である。なお同記録の88行目は「この論文が取っているのは周波数の比ではなく差である」と注意しており、草稿175行目の「比で読む」という書き方は「比あるいは差で読む」に直すほうが正確である。

## 2-11　書誌の細かい誤り

- 2.5節121行目は「SeedQR [40] は……128ビットを21×21の格子に載せて金属板に打刻する仕様である」と書く。**21×21で128ビットになるのは CompactSeedQR であり、標準の SeedQR は4桁零詰めの48桁で25×25である**（`REFERENCES_TO_ADD.md` 43行目）。
- 6.3節351行目の「二次元コードを使う仕様なら70ミリメートル角の板1枚に収まり」という数字は、`REFERENCES_TO_ADD.md` にも `raw2/v3-codex32-seedqr.md` にも一次資料での確認記録が見当たらない。**出典を示せないなら寸法を落とす。**（疑いがあると明記する。取得できた資料の範囲で確認できなかったという意味である。）
- 2.2節87行目は本文で Acoustruments を [9] として挙げるが、末尾の一覧に [9] が無い。番号を振り直すときに拾う。

## 2-12　形式

本文6ページ以内という制限に対し、現状は明らかに超える。2.1節から2.5節までで1ページ半以上を使い、4.3節（251行目から255行目）は未実施の攻撃を3件紹介するために1段落を使っている。`REVIEW_AND_REPOSITIONING.md` の357行目が「限界の節に一文で足りる」と書いているとおりである。また、冒頭の「この原稿について」（7行目）と、本文中の【要確認】【要記入】は投稿版から消す。

---

# 第三　関連研究として当然引かれるべきなのに草稿に無いもの

`SURVEY.md`、`raw/`、`raw2/` を読んで確かめた。**国内について、とくに重い落としが複数ある。**

## 3-1　国内（WISSの読者が最初に想起するもの）

| 落としているもの | 根拠 | なぜ重いか |
| --- | --- | --- |
| **SheetKey（Graphics Interface 2020）と DuoTouch（CHI 2026）** | `SURVEY.md` 152行目から156行目 | サーベイ自身が「無電源物体への符号の固定、市販端末での復号、物理パラメータによる可読性の議論、日用品への埋め込みという四点がCipherFluteとそのまま重なる」「必ず引用しなければならない」と書いている。**草稿に1件も出てこない。** どちらも加藤邦拓さんが著者に入り、DuoTouch は2026年のCHIである |
| **林吉経ら「棒の引っかきによる音波を用いたインタラクション取得手法の検討」（WISS 2025）** | `raw2/f1-wiss-nenji.md` 424行目から428行目、495行目 | 爪の長さが固有振動周波数を決める受動発音体を使う。**寸法が音高を決めるという核心の物理が同一であり、直前のWISSの発表である。** サーベイ自身が危険度を「中から高へ上げるべきである」と判定している |
| **髙倉礼ら「能動的音響計測に基づくスタイラスの把持状態識別手法の検討」（WISS 2021）** | `REFERENCES_TO_ADD.md` 105行目から108行目 | 久保らと並ぶ国内の直系である。草稿は久保ら [28] しか引いていない |
| **片倉翔平と渡邊恵太の ProtoHole（WISS 2017）、奥山瑞希らのM系列円筒バーコード（WISS 2017）** | `raw2/f1-wiss-nenji.md` 497行目から498行目 | 前者は中空造形物の共鳴で状態を読む研究である。後者は符号語彙を数学的性質で設計した国内の先例であり、3.4節の符号設計に1行で効く |
| **瀬崎夕陽ら「溝間隔の違いによる筆圧変化を活用したシート埋め込み型ID認識手法」（WISS 2025）** | `raw2/f1-wiss-nenji.md` 418行目、494行目 | 物理的な周期構造を識別番号に写す系統の直近例である |
| **WISS 2025 の金彩回路オカリナ** | `raw2/f1-wiss-nenji.md` 436行目 | 調査記録自身が「同じ会議の同じ年に『笛に電子回路を付ける研究』と『笛の音そのものを符号にする研究』が並ぶことになるので、引用して立場の違いを述べるとよい」と書いている。1行で効く対比である |
| **中沢誠と山崎芳男「1/12Nオクターブ分析を用いた音の符号化」（早稲田大学、2003年）** | `raw3/c5-semitone-concept.md` 209行目から215行目、271行目 | **12音平均律に基づく対数等間隔の分割を符号化の格子として使い、分割数を設計変数として扱っている。** 3.2節（163行目から169行目）が「半音刻みを選んだ理由」を論の中心に据える以上、日本語の直接の先行例を落とすのは危ない |
| **徳重佑樹ら「物理的復元が容易な音響秘密分散法」（電子情報通信学会技術研究報告、2015年）** | `REFERENCES_TO_ADD.md` 188行目から194行目 | 国内の音響秘密分散である。情報理論的な安全性を捨てて実空間での復元を得たという取引が、本研究とちょうど逆である。2.5節の視覚暗号の段落に1文で入る |
| **須賀祐治「Virtual Vaults」（情報処理学会研究報告CSEC、2026年5月）** | `REFERENCES_TO_ADD.md` 294行目 | 暗号資産の鍵管理における物理的隔離の国内の共通語彙を提供する直近の発表である |
| **藤川真樹らのマルチモーダル人工物メトリクス** | `REFERENCES_TO_ADD.md` 298行目から301行目 | 合成樹脂のカード形という形状まで一致する。「これは人工物メトリクスか」という当然の質問に、「管長は設計図そのものであって偶発的な微視的乱れではない」と1文で答えられる |
| **吉川茂「正倉院尺八吹奏時の歌口端補正長さの推定」（情報処理学会研究報告MUS、2011年）** | `REFERENCES_TO_ADD.md` 288行目 | 3.1節161行目が [47] として「管楽器の音響学で確立した知識」と書くが、末尾の一覧に [47] が無い。**国内の情報処理学会に一次文献があるので、ここを埋めるのが最も自然である** |
| **Picognizer（WISS 2017、栗原一貴ほか）** | `REFERENCES_TO_ADD.md` 344行目から346行目 | 自己引用である。復号ページがブラウザで音を読む設計はこの延長にある。WISSの読者に対して自分の系譜を示せる |

## 3-2　国際

| 落としているもの | 根拠 | なぜ重いか |
| --- | --- | --- |
| **Secure Information Embedding in Forensic 3D Fingerprinting（2024年）** | `PAPER_REVISION.md` 110行目、129行目、`REFERENCES_TO_ADD.md` 248行目から252行目 | 貢献の第四（63行目）が「攻撃者の能力を列挙して守れない範囲を宣言した研究は数少ない」と書いている。**方針文書が、この1件を注記しないとその書き方は成立しないと明記している。** 草稿に無い |
| **Jiang らの Near-infrared Imaging for Information Embedding and Extraction with Layered Structures（ACM Transactions on Graphics 42巻1号）** | `REFERENCES_TO_ADD.md` 241行目から244行目 | 造形物への情報埋め込みで**物理的な秘密分散に言及した唯一の例**である。草稿の [26] は同じ著者の別論文（InfoPrint）であって、これではない。3.7節と5.6節が秘密分散を扱う以上、1行引く価値がある |
| **Yocam ら（arXiv:2606.13952、2026年）** | `REFERENCES_TO_ADD.md` 79行目から83行目 | **本研究が実際に使っている Bambu Lab の造形機2台を対象とした側チャネル評価である。** 4.3節が側チャネルを論じるなら、最も近い1件である。ただし査読の有無が未確認なので、入れるかどうかは判断による |
| **特許 US4821670A と US10147410B2** | `SURVEY.md` 143行目から148行目 | 前者は「単一のホイッスル本体に3個以上のフィップル要素を持ち、少なくとも2つの気柱の長さが異なり、共通の吹き口を持つ」ことを請求している。後者は「吹かれたホイッスルを音高で識別する」ことを請求している。学術論文で特許を引く義務は無いが、2.3節が造形上の新規性を放棄する断りを置くなら、根拠として1行触れると強い。**入れるかどうかは判断による** |

---

# 第四　旧版から落としてしまったもののうち、残すべきだったもの

`paper/cipherflute_wiss2026_v1.2.docx` を展開して全文を突き合わせた。

1. **2枚のカードがそろったときだけ目的のページへ遷移する実演。** 旧版6.4節は「合成した秘密を鍵として遷移先URLをAES-GCMで暗号化しておくと、2枚がそろったときにだけそのページが開く。これも実機で確かめ、2枚を吹き終えた時点で目的のページへ遷移した」と書いていた。新稿の5.6節（325行目）はこの部分を落とし、記号を足し合わせて秘密が戻ったところで止めている。**物を吹いた結果が画面の遷移という目に見える形で終わるのは、募集要項が重視する「デモによる有効性のアピール」そのものである。** 4.2節247行目の「20.8ビットのままである」という但し書きを添えれば誠実さも保てる。落としたのは惜しい。
2. **復号ソフトの画面の図。** 旧版の図4である（`paper/figs/fig5_decoder.png`）。2-2および2-3と同じ理由である。
3. **印刷の向きの実験の方法と数値。** 旧版は、同一の土台の3面に同じ音の笛を1本ずつ付けた試験片を1回で印刷し、上面の1本を対照とするという切り分けの設計を書き、対照との差が −2.4セントと0セント、対照自身の吹鳴ばらつきが9.5セントであったと数値で示していた。新稿の5.5節（311行目から315行目）は結論だけを残して方法と数値を落としている。**この切り分けの設計は、結果を信じてよい理由そのものである。** 2文で戻る。
4. **縦置きの結果と、そこから得た教訓。** 1-2の末尾に書いたとおり、「鳴っているかどうかを聴感で判断してはならない」という観測は、耳で読むことを中心に据えた新稿でこそ必要である。
5. **素材の選択の理由。** 旧版は、吹き込み口が口に触れるので食品接触に適合する材料を標準にしたと書いていた。新稿の5.3節（297行目）は「食品接触に適合するフィラメント」とだけ書き、なぜそれが要るのかを落としている。1文で戻る。
6. **透明な素材が偽装に不利であるという記述。** 2-8のとおりである。
7. **脅威モデルの攻撃者2件（復元の場の盗聴者、所有者への強要）。** 2-7のとおりである。
8. **Chordika（1枚が1つの調に対応するカード）。** 旧版6.1節にあった。娯楽性を主張しない方針なので落としてよいが、**「8本を吹くと調が聞き分けられる」ことは、人間が耳で読めるという新しい中心の主張の傍証になる。** 5.4節か6.1節に1文だけ残す選択はありうる。

**なお、旧版にも新稿にも無いが、投稿までに使える材料が1つある。** 暗号笛ウォレット（`docs/dapp/`、コミット 38d7bc6、2026年7月29日）である。笛を吹いて得た秘密から鍵と口座アドレスを導き、残高まで表示する。コミットの記録には「カード2枚の音列から秘密260729、口座までブラウザ上で通した」とある。**「物を吹いたら口座が開く」という筋は、実装による有効性のアピールとして最も分かりやすい。** 1段落と図1枚で入る。ただし4.2節の20.8ビットの但し書きと、本物の資産に使わないという注意を必ず添える。

---

# 第五　採録のために、いま最も足りないもの1つ

**「読み出しに特別な装置が要らない」という中心の主張について、実際に装置を使わずに秘密を取り出して見せた記録である。**

5.4節が空欄のままであることが、そのまま論文の中心が空欄であることを意味している。募集要項が重視するのは「アイデアの斬新さ」と「デモや実装による有効性のアピール」であり、評価実験は求められていない。**したがって必要なのは統計ではなく、1回通った実演の記録と、その図1枚だけである。** 物も実装も既にあるので、対照表コームを1本刷り直したうえで、1日あれば埋まる。

埋めなければ、査読者は「中心の主張は言葉だけである」と判断する。関連研究の追加、実物の写真、歩留まりの開示は、いずれもこれより後でよい。

---

# 確かめて問題がなかったところ

「問題なし」と判断した箇所と、その確かめ方を記す。

- **数値の検算。** 1本あたり log₂11 = 3.459 ビット、12スロットから実効11へ落ちる減りが 3.585 − 3.459 = 0.126 ビット（草稿185行目の「約0.13ビット」と一致）、カード8本で 11⁶ = 1,771,561 通りすなわち20.8ビット（草稿319行目と一致）、2キロヘルツ帯で1セントが 2000 × (2^(1/1200) − 1) = 1.16ヘルツ（草稿49行目の「約1.2ヘルツ」と一致）、気温が10度上がると音速が √(303/293) = 1.0169 倍すなわち1.7パーセントで29セント（草稿173行目の「約1.7パーセント、半音の約3割」と一致）、25.2度から41.0度で √(314.15/298.35) から45セント（草稿289行目の予測値と一致）、半音1段が長さの 2^(1/12) − 1 = 5.6パーセント（草稿255行目の「約5パーセント」とおおむね一致）。**いずれも合っている。**
- **5.1節の較正コームの数値。** 吹鳴ばらつき15.2セント、同じ音の3本の散らばり11.0セント、実測長で再フィットした残差11.3セント、最高音 G7 の3本が±20セント以内という記述は、`out/calib_comb36_report_2026-07-28.txt` の72行目から78行目、および `out/cipher_mini10_calib.txt` の記載と一致する。**数値そのものは正しい。**（触れていない事実がある点は2-1に書いた。）
- **5.1節末尾の外形長の注意。** 「外形の長さを最長管ちょうどにしてはならない」という記述は、`fue/mini10.py` の105行目から110行目の `BODY_MARGIN` の注記と一致する。
- **5.5節の印刷の向きの結論。** 0度、±45度、±90度、±135度が鳴り、180度だけが鳴らないという結論は、旧版の記述と一致する。
- **2.2節の Whoosh の記述。** 管長式が半音比の等比数列であること、認識がメル周波数ケプストラム係数とサポートベクターマシンによる分類であること、利用者非依存で79.7パーセントに落ちること、管長が再現性のために定数として公開されていることは、`REFERENCES_TO_ADD.md` 16行目の確定事実とすべて一致する。**差分の書き方（情報の向きの違い）も、`raw3/c5-semitone-concept.md` 271行目から279行目の判断と整合している。**
- **2.3節の Printone の数値。** 「104個の目標周波数のうち、出せなかったのは4例だけ」は、`REFERENCES_TO_ADD.md` 25行目の注意（短縮版にしかない56個ではなく本体の104個を使う）に正しく従っている。
- **2.5節の codex32 の訂正能力。** 「8文字以内に影響する任意の誤りを検出し、置換4文字までと消失8文字までを訂正する」は `REFERENCES_TO_ADD.md` 36行目と一致する。
- **3.4節の符号理論。** 隣接同音禁止のもとでの1記号あたりの容量の上限が log₂(q−1) であり、差分写像が有限長でもこれを達成するという記述は、`REFERENCES_TO_ADD.md` 157行目の結論と一致する。
- **`PAPER_REVISION.md` の「書いてはならないこと」13項目（116行目から130行目）。** 全項目を本文と突き合わせたが、**いずれも書かれていない。** むしろ2.1節73行目の「隠しながら読めること自体は、既に実現されている」、2.3節103行目の「本研究の新規性はない」、2.3節107行目の「本研究の新規性ではない」のように、先行例を自分から認める書き方になっている。**この点は旧版からの明確な改善であり、査読者として評価する。**
- **4.2節（秘密のエントロピーが小さいときに守れなくなること）。** `REVIEW_AND_REPOSITIONING.md` 143行目の指示（112ビット以上に限定する、20.8ビットの強度を数字で明記する）どおりに書かれている。
- **貢献の書き方。** 4点（57行目から63行目）はいずれも「移した」「示した」という限定つきの表現になっており、`REVIEW_AND_REPOSITIONING.md` が求めた弱め方に従っている。第三の貢献だけは、参考文献 [48] の書誌が未確定であるという別の問題を抱えている（2-10に書いた）。
