qurihara/ai-fue/related_work_survey/raw4/check-numbers.md

# 草稿v2に現れるすべての数値の検算

対象は `paper/cipherflute_wiss2026_v2_draft.md`（2026年7月30日の白紙書き直し版）である。
本文に現れる数値を1つずつ洗い出し、先行研究の数値は `related_work_survey/PAPER_REVISION.md` の
「使う数値」の表と `raw2/f6-key-numbers.md` と `raw3/` に照らし、本研究自身の数値は
`fue/` の実装コードと `docs/cipher/cipher_config.json` と旧版 `paper/cipherflute_wiss2026_v1.2.docx`
に照らした。符号化器は実際に動かして本数とビット数を確かめた。

判定は「正しい」「誤り」「確認できない」の3つである。誤りには正しい値を書いた。

---

## 0. 結論

**投稿前に必ず直すべき誤りが7件ある。** うち3件は本研究自身の数値であり、
実装を読めば誰でも確かめられるものである。とくに較正定数（3.1節）は、
論文に書かれた値で管長を計算すると実際に印刷した笛より20ミリメートル以上短くなる。

一方、5章の実測値は15項目すべてが旧版と一致した。log₂11 ≈ 3.46ビット、
1本あたりの減り0.13ビット、カード8本20.8ビット、本立て36本64ビット、
スプール49本128ビットは、いずれも符号化器を実際に走らせて再現できた。
2キロヘルツ帯で1セント約1.2ヘルツも正しい。

---

## 1. 必ず直すべき誤り

### 誤り1（3.1節・161行目）　較正定数 A = 91891.5、e = 14.23 は外形統一版のものではない

草稿の記述は次のとおりである。

> 日用品への埋め込みに用いた外形統一版では *A* = 91891.5、*e* = 14.23 である
> 【要確認：`fue/cipher_codec.py` の既定値。…】

**判定は誤りである。** この値は外形統一版の較正ではない。

根拠は3つある。

第一に、実際に印刷する管の長さを決めているのは `fue/mini10.py` の `length_for_note` であり
（`fue/cipher_card.py` 61-62行目、`fue/spool_128bit.py` 96-97行目、`fue/cipher_cardpair.py` が
いずれもこれを呼ぶ）、その較正は `fue/mini10.py` 27-45行目の `_load_calib` が
`out/cipher_mini10_calib.txt` から読み込む。その中身は

```
A=87985.1
e=-10.010
```

であり、ファイル冒頭の注記に「CipherFlute mini10 外見統一版(uniform_flute)の較正。
2026-07-28 の較正コーム36本からフィット」「実測長で当てはめると12音すべてが1つの式に乗る
（残差 11.3 cent, 30本）」と書いてある。**これは草稿5.1節が述べている当てはめそのものである。**

第二に、`fue/cipher_codec.py` の `calib_k = 91891.5`、`calib_delta = 14.23`（34-35行目）は
`freq_to_length`（129行目）でしか使われず、その戻り値は `EncodeResult.lengths` として
表示に出るだけである。形状生成には一切使われていない。

第三に、91891.5 と 14.23 の出どころは `README.md` の83行目と108行目にある。
「2026/7/1にH2Dで管長40/70/100/130mmの…4本測定、RMS 0.28mm」と書かれており、
mini10ヘッドではなく初期の直管の較正である。同じ値は `fue/compact.py`、`fue/fold.py`、
`fue/revolver.py`、`fue/plenum.py` にも定数として散らばっている。

数字で確かめると差は決定的である。C7（2093.0ヘルツ）に対して、

| 式 | 得られる管長 |
| --- | --- |
| f = 91891.5/(L+14.23)（草稿の値） | 29.67 mm |
| f = 87985.1/(L−10.010)（実装が使う値） | 52.05 mm |

実際に `fue/mini10.py` で生成した笛のC7の外形長は52.05ミリメートルである
（trimeshで境界箱を測って確認した）。草稿の値では22ミリメートル短い。

**直し方。** 3.1節を「外形統一版では *A* = 87985.1、*e* = −10.010 である
（`out/cipher_mini10_calib.txt`。5.1節の当てはめで得た値である）」と書き換える。
式の向き（f = A/(L+e)）は実装と一致しているので変えなくてよい
（`freq_to_length` は L = A/f − e を返し、これは f = A/(L+e) と同値である）。
厚壁ヘッドの A = 86718、e = −11.81 は旧版5.1節の記述と一致しており、そのままでよい。

なお `PAPER_REVISION.md` の179行目が同じ誤りを含んでいるので、そちらも直したほうがよい。

### 誤り2（3.7節・221行目）　SLIP-39の200ビットは笛64本ではなく75本である

草稿の記述は次のとおりである。

> 業界標準のSLIP-39 [12] に準拠すれば、断片1つが200ビットとなり笛64本を要するが、…

**判定は誤りである。正しくは75本である。**

`REVIEW_AND_REPOSITIONING.md` の139行目は
「論文自身の符号化器で計算すると、**168ビットは笛64本、200ビットは笛75本**になる」と
書いている。すなわち64本に対応するのは正味の168ビット（前置き40ビット＋断片値128ビット＋
詰め物2ビットから検査符号30ビットを除いた分）であって、200ビットではない。
`PAPER_REVISION.md` の187行目にある「承認済みの文面」の時点でこの取り違えが混入しており、
草稿はそれをそのまま引き継いでいる。

符号化器で再計算して確かめた。12スロット・隣接同音禁止では素数体は GF(11) であり
（`fue/cipher_codec.py` 291-305行目の `_wire_params` が `p = _prime_below(m-1) = 11` を返す）、
ブロックあたりの検査2記号でブロック長は8記号である。

- 200ビット＝25バイト → データ58記号 → 8ブロック → 符号語74記号 → 基準笛込み**75本**
- 168ビット＝21バイト → データ49記号 → 7ブロック → 符号語63記号 → 基準笛込み**64本**

**直し方。** 「断片1つが200ビットとなり笛75本を要する」に直すか、
「正味168ビットで笛64本、検査符号まで含めた200ビットなら笛75本」と書き分ける。
どちらにしても円盤1枚26本の上限（5.6節）では2枚に収まらず3枚を要する点は変わらない。

### 誤り3（表1・149行目、および2.1節83行目）　本研究の128ビットを「実証容量」として並べている

表1の見出しは「先行研究との比較（実証容量は原典の記載による）」であり、
本研究の行に「**3.5 bit/本、計128 bit**」と書いてある。しかし5.3節（301行目）は
自ら次のように書いている。

> **128ビットの構成については、片側24本の発音と、仮の基準に対する相対の位置が
> 設計どおりであることを確認した段階である。49本を通した復号は未実施である。**

**同じ論文の中で矛盾している。** 2.1節の83行目「本研究は…128ビットに到達する位置にある」も
同じ問題を抱えている。`PAPER_REVISION.md` の28行目は
「実証していないことを実証したと書くのは、引用漏れよりも重い正確性の失敗である」と
明記しており、旧版で外部評価に指摘された当の失敗をそのまま繰り返す形になっている。

**直し方。** 表1の本研究の行を「3.5 bit/本。実証は20.8 bit（カード）、設計は128 bit（未通し）」の
ように書き分けるか、「実証容量」の列名を本研究の行だけ注で断る。
2.1節の「128ビットに到達する位置にある」も同様に弱める。

### 誤り4（表3・271行目、および3.7節223行目）　実装した2-of-3は各128ビットではない

表3は次のように書いている。

| 層 | 量 | 守る力 |
| --- | --- | --- |
| 秘密分散（2-of-3） | 断片は各128 bit | 128 bit |

3.7節（223行目）も「**本研究の実装は後者である。** 2-of-3を3つの異なる日用品に分けているため、
どの物体が何番目の断片であるかは物体自身が語る」と書いている。

**判定は誤りである。** 実際に作った2-of-3は `out/bookstand_v3_shares.txt` に記録されている。

```
# 秘密 260729（11進6桁 = 1,6,8,9,8,7）を、3台のうち2台で復元できるように分けた。
#   1台目 断片 10,8,1,6,10,7
# 台の番号は、正面の底板の左端に彫った数字（1/2/3）で見分ける。
```

すなわち、

1. 断片は記号6個＝**20.8ビット**であって128ビットではない（`fue/threshold.py` 107行目の
   既定も `--width 6`＝20.8ビットである）。
2. 担体は「3つの異なる日用品」ではなく、**同じ設計の本立て3台**である。
3. メンバー番号は物体の形ではなく、**底板に彫った数字**で見分けている。

3.7節の「日用品は互いに見た目が違うので、形そのものが番号を担える」という論証は、
実装した物が実際にやっていることと逆になっている。

**直し方。** 表3の「断片は各128 bit」を「断片は秘密と同じ大きさ（実装では20.8 bit）」に直す。
3.7節は「実装では2-of-3を本立て3台に分け、番号は刻印で示した。担体の見た目を変えれば
形そのものに番号を担わせられる」と、実装と将来の設計思想を分けて書く。

### 誤り5（3.4節・187行目）　「スロット数を素数にとれば」は12スロットの実装と合わない

草稿の記述は次のとおりである。

> 誤り訂正にはリードソロモン符号を用いる。**スロット数を素数にとれば**、その素数を位数とする
> 有限体の演算をそのまま組むことができ、笛1本が計算上の1記号に対応する。

**判定は誤りである。** 3.2節が述べる実装のスロット数は12であり、12は素数ではない。
隣接同音禁止のもとで記号として使えるのは差分値の個数 m−1 = 11 であり、
素数体の位数はこちらの11である（`fue/cipher_codec.py` 291-305行目、
`p = _prime_below(m - 1)`）。旧版は13スロット（素数）だったのでこの文は正しかったが、
12スロットへ移した時点で成り立たなくなっている。

**直し方。** 「隣接同音を禁じたときの記号数（スロット数から1を引いた値）を素数にとれば」と
書き換える。12スロットなら11が素数なので条件を満たす、と続けるのが実装どおりである。

### 誤り6（2.5節・121行目）　128ビットを21×21に載せるのはCompactSeedQRである

草稿の記述は次のとおりである。

> SeedQR [40] はBIP-39の語を索引番号に写して二次元コードに収め、128ビットを21×21の格子に
> 載せて金属板に打刻する仕様である。

**判定は誤りである。** `raw2/v3-codex32-seedqr.md` の94行目と96行目に一次資料の内容がある。

- 標準のSeedQR：索引を4桁の十進数に零詰めして連結し、数値モードで符号化する。
  12語では48桁になり、**21×21には入らず25×25に収まる**。
- CompactSeedQR：索引を11ビットで連結して検査ビットを落とし、バイナリモードで符号化する。
  12語では**128ビット＝16バイトで21×21に収まる**。

草稿は前半（索引番号に写す）を標準SeedQRから、後半（128ビット・21×21）を
CompactSeedQRから取って1文にまとめてしまっている。

**直し方。** 「SeedQRは索引番号を十進で写して25×25に収め、その圧縮版であるCompactSeedQRは
索引を11ビットで連結して128ビットを21×21に収める」と分けて書く。
6.3節（351行目）の「70ミリメートル角の板1枚」もCompactSeedQRの数字なので、
そこでも版を明示したほうがよい（`raw2/v3` 218行目、`REVIEW_AND_REPOSITIONING.md` 199行目）。

### 誤り7（4.3節・255行目）　98.80パーセントと「実効長の約5パーセント」は比べられない

草稿の記述は次のとおりである。

> 2024年には離れた場所の市販の携帯電話の音響と磁界から軸方向の平均精度98.80パーセントに
> 達している [61]。本手法では半音1段が実効長の約5パーセントに対応するため、
> **この精度はスロットの粒度に迫っている。**

**判定は誤りである。** 98.80パーセントは「軸方向の移動・ステッピングモータの動作・
ノズル速度・ロータ速度の推定」の分類精度であって、長さの推定誤差ではない
（`REFERENCES_TO_ADD.md` 75行目、`raw/14-fab-security-privacy.md` 33行目）。
分類精度のパーセントと長さのパーセントを並べても比較にならない。

比較すべき数値は同じ調査記録の中にある。

- 2024年のJamaraniら：**平面的な設計で平均傾向誤差4.47パーセント**
- 2018年のChhetriら：軸推定精度86パーセントと並んで、**平均の長さ推定誤差11.11パーセント**

`raw/14-fab-security-privacy.md` の7行目は、まさにこの4.47パーセントを引いて
「CipherFluteは半音1段ごとに管の実効長を5パーセントから6パーセント変えるので、
この誤差は半音1段の差にほぼ並ぶ水準まで来ている」と書いている。

**直し方。** 「軸方向の平均精度98.80パーセント」を残すのはよいが、粒度の比較には
「平面的な設計で平均傾向誤差4.47パーセント」を使う。2018年の側は
「軸の推定精度86パーセント、長さの推定誤差11.11パーセント」と両方書くのが正確である。

---

## 2. 直したほうがよいが致命的でない点

### 2.1　「半音1段が実効長の約5パーセント」（4.3節・255行目）は5.6パーセントである

「実効長」を音響的な実効長（L + e）と読むなら、半音1段の比は 1 − 2^(−1/12) = **5.61パーセント**で
あり、較正定数によらず一定である。調査記録も「5パーセントから6パーセント」と書いている
（`raw/14-fab-security-privacy.md` 7行目）。

一方、側チャネルが実際に測るのは印刷される物理的な管長のほうである。実装の較正
（A = 87985.1、e = −10.010）で12スロット分を計算すると、隣り合う音の管長差は
1.67ミリメートルから2.97ミリメートル、割合では**4.2パーセントから4.7パーセント**である。

どちらに読んでも桁は合っているが、「約5パーセント」より「5から6パーセント」と書くか、
物理長で言うなら「半音1段で管長が約2ミリメートル、割合で約4.5パーセント」と書くほうが正確である。
`REFERENCES_TO_ADD.md` 141行目の「半音1段（管長でおよそ2ミリメートル台）」とも整合する。

### 2.2　「音域を半音1つ広げれば代償なしに手に入る」（3.4節・185行目）は現実装では成り立たない

符号理論としては正しい（13スロットで隣接同音を禁じた容量 log₂12 は、12スロットの
制約なしの容量と等しい）。しかし現在の実装は素数体を使うため、
`p = _prime_below(m − 1)` で m = 13 なら `_prime_below(12) = 11` となり、
1本あたりは log₂11 のままで増えない（`fue/cipher_codec.py` 291-305行目）。

**直し方。** 「符号理論の上ではそうなる。ただし本実装は素数体を使うため、
実際に代償ゼロにするには記号数が素数になる音域幅を選ぶ必要がある」と1文添える。

### 2.3　「記号数で割った余りを取る」（3.4節・185行目）は「スロット数で割った余り」である

`_diff_encode`（`fue/cipher_codec.py` 308-316行目）は `prev = (prev + 1 + d) % m` であり、
法は記号数 11 ではなくスロット数 m = 12 である。差分値 d の範囲が 0 から m−2 なので
記号数が11になる、という関係である。1語の直しで足りる。

### 2.4　Dabinらの数値の組み合わせ（2.3節・103行目）が原典の対応と違う

草稿は「印刷したリコーダーの**初版**が目標に対して+6から+34セント、
**やすりで手修正した版**が−13から+14セントであった」と書いており、
同じ楽器の改良前後のように読める。

原典の表1（`raw2/v2-printone.md` 139-155行目）では、+6から+34セントは**リコーダー1**、
−13から+14セントは**リコーダー2を手修正した版**であり、そのリコーダー2の手修正前は
−40から+1セントである。別々の楽器の数値を前後のように並べている。

**直し方。** 「印刷した2本のリコーダーが目標に対して+6から+34セントおよび−40から+1セントで
あり、指孔をやすりで手修正した版が−13から+14セントであった」と書く。

### 2.5　FluteCaseの79.7パーセント（2.2節・91行目）の帰属に注意が要る

79.7パーセントは原典に実在する数値である（`raw2/v1-whoosh-flutecase.md` 163行目）。
ただし原文は「8人の参加者と**14イベント**にわたる、一人を除いて学習する予備的な解析」であり、
この14イベントがFluteCaseの8本の管を含むかどうかは調査記録からは確定できていない
（記録自身は204行目でFluteCaseに帰属させているが、原文の根拠は示していない）。

**直し方。** 「Whooshの認識系は…利用者非依存では14イベントの精度が79.7パーセントに落ちる」と、
Whoosh全体の数値として書けば安全である。

### 2.6　「印刷のばらつき（実測でおよそ11セント）」（3.2節・167行目）は上界であって実測値ではない

5.1節（283行目）自身が「後者は吹き方のばらつきだけで説明がつく大きさであり、
造形そのもののばらつきは**多くとも**11セント程度と言える」と書いている。
3.2節で「実測で」と書くと、造形のばらつきを直接測ったように読める。
「多くとも11セント程度」と揃えるのがよい。

なお旧版3.2節は「標準偏差およそ10セント」であった。値を11に更新したこと自体は
5.1節と整合しており問題ない。

### 2.7　「刻み幅を残る誤差のおよそ4倍」（3.2節・167行目）の根拠が示されていない

旧版から引き継いだ設計の目安であるが、出典が本文にも調査記録にもない。
**確認できない。** 「設計の目安」と書いてある以上そのままでもよいが、
5.2節の残差±24セントを当てはめると 24×4 = 96 となり100セントに対する余裕はほとんどない。
どの誤差に対して4倍なのか（11.3セントの当てはめ残差なのか、15.2セントの吹奏ばらつきなのか、
±24セントの温度差条件なのか）を1文で特定したほうが安全である。

### 2.8　表記のゆれ

- 概要（19行目）と表1（149行目）は「3.5ビット」、3.6節（207行目）は「log₂11 ≈ 3.46ビット」である。
  正しい値は3.4594…なので両方とも誤りではないが、どちらかに寄せたほうがよい。
- 参考文献[48]（423行目）が「Smith, J. and Senturia, S.:（基準共鳴器との比による共通モード除去、
  1995年）」のままである。`raw3/c3-reference-resonator.md` に完全な書誌がある
  （James H. Smith and Stephen D. Senturia, "Self-Consistent Temperature Compensation for
  Resonant Sensors with Application to Quartz Bulk Acoustic Wave Chemical Sensors",
  TRANSDUCERS '95, pp. 724–727, DOI 10.1109/SENSOR.1995.721934）。

### 2.9　論文には影響しないが、実装側の注記が1つずれている

`fue/spool_128bit.py` の8行目は「128bit（16バイト）は**37記号**になり」と書いているが、
実際に符号化器を走らせると**38記号**である（11^37 は 2^128 をわずかに下回るため、
`_payload_width(16, 11)` は38を返す）。同じ行の「48記号」と「笛49本」は正しい。
論文の数値は49本で正しいので本文の修正は要らないが、コードの注記は直したほうがよい。

---

## 3. 確かめて問題がなかった数値

### 3.1　符号化の中核（実際に符号化器を走らせて確認）

`docs/cipher/cipher_config.json` を読み、`lo_note="G#6"`、`hi_note="G7"` で上書きした設定
（`fue/cipher_card.py` 31行目、`fue/spool_128bit.py` 41行目、`fue/bookstand_flutes.py` 49行目と
同じもの）で `fue/cipher_codec.py` を実行した結果である。

| 草稿の記述 | 実行結果 | 判定 |
| --- | --- | --- |
| 12個のスロット（G#6からG7） | `len(slots(cfg)) == 12` | 正しい |
| log₂11 ≈ 3.46ビット／本 | `symbol_bits(cfg) == 3.4594316186372973` | 正しい |
| 1本あたりの減りは約0.13ビット | log₂12 − log₂11 = 3.584962… − 3.459431… = **0.125531** | 正しい |
| 隣接同音禁止の容量上限は log₂(q−1) | 制約グラフの最大固有値が q−1 なので正しい。`_diff_encode` は差分値を 0..m−2 の m−1 通り取るので上限をちょうど達成する | 正しい |
| カード8本で20.8ビット | 検査1記号でデータ6記号、6×log₂11 = **20.757ビット**、笛8本。`fue/cipher_cardpair.py` 23行目の「パリティ1 … 記号6個・20.8ビット（0〜1,771,560）」と一致（11^6 = 1,771,561） | 正しい |
| 本立て36本で64ビット | 8バイトを検査4記号／ブロックで符号化すると笛**36本**（データ19記号、4ブロック、符号語35記号＋基準笛1本）。`fue/bookstand_flutes.py` 48行目の `DEMO_PAYLOAD = b"pass_#26"`（64bit）と325行目の `--parity` 既定4と一致 | 正しい |
| スプール49本で128ビット | 16バイトを検査2記号／ブロックで符号化すると笛**49本**（データ38記号、5ブロック、符号語48記号＋基準笛1本） | 正しい |
| 1枚の円盤に置ける本数は26本が上限 | `fue/spool_128bit.py` 44行目「26本で隣どうしの隙間が1.25mm、27本で0.95mm」 | 正しい |
| 25本と24本に分けた | `split_notes(49, 2)` → 25本と24本 | 正しい |
| 復号ページの既定は11スロット（G#6からF#7） | `docs/cipher/cipher_config.json` が `lo_note="G#6"`, `hi_note="F#7"` → 12半音差ではなく11なのでスロット11個 | 正しい（【要確認】の指摘どおり） |
| 有限体の位数を11にとれば乗算表は11×11（6.4節） | `_wire_params` が返す p は11 | 正しい |
| 表2の「暗証番号20ビット程度＝基準笛込みで8本、検査1記号」 | 上記カードと同一 | 正しい |
| 表2の「数バイトの秘密＝20本前後、検査2記号」 | 4バイトで15本、6バイトで19本、8バイトで26本。目安として妥当 | 正しい |
| 表2の「128ビット＝基準笛込みで49本、ブロックあたり2記号」 | 上記スプールと同一 | 正しい |

### 3.2　笛の寸法と較正の式の向き

- 「厚さ4ミリメートル、幅7ミリメートル」（3.1節）：`mini10/recorder-mini-c-v3-half-2-v2.stl` の
  境界箱を trimesh で測ると (60.0, 7.0, 4.0) ミリメートルであり、**正しい**。旧版3.1節とも一致する。
- 式の向き：`fue/cipher_codec.py` 129行目の `freq_to_length` は `A/f − e` を返す。
  これは f = A/(L+e) と同値であり、草稿の書き方（f = A/(L+e)）と**一致する**。
  `fue/mini10.py` 59行目の `est_freq` も `A/(L+E)` である。
- 厚壁ヘッドの A = 86718、e = −11.81：旧版5.1節（180段落）の
  「f = A/(L+e) に対して A = 86718，e = −11.81 を得た」と**一致する**。
- 「最長管に数ミリメートルの余白を足した長さを外形とした」（5.1節）：
  最長管G#6が62.97ミリメートル、外形が65.97ミリメートルで差は3.00ミリメートルであり、**正しい**。

### 3.3　物理の計算

- **2キロヘルツ帯で1セントは約1.2ヘルツ**（1.2節49行目、3.5節199行目）：
  2000ヘルツで 2000×(2^(1/1200)−1) = **1.156ヘルツ**、基準笛C7の2093.0ヘルツでは**1.210ヘルツ**。
  「約1.2ヘルツ」は正しい。刻み100セントに対して桁違いに細かいという評価も正しい。
- **気温10度で約1.7パーセント、半音の約3割**（3.3節）：
  20度から30度で √(303.15/293.15) = 1.0169 → **1.69パーセント**、セントに直すと**29.0セント**＝
  半音の0.29。正しい。
- **25.2度と41.0度の予測が約45セント**（5.2節）：
  √(314.15/298.35) = 1.02614 → **44.7セント**。正しい。
- **16度近い温度差**（5.2節）：41.0 − 25.2 = 15.8度。正しい。
- **360度のうち270度**（5.5節）：−135度から+135度は270度。正しい。
- **毎秒10ビットに満たない**（2.4節）：26本を13.8秒で吹くという既存の計測から
  26×3.46/13.8 = 6.5ビット毎秒であり、正しい。

### 3.4　5章の実測値（旧版 `cipherflute_wiss2026_v1.2.docx` と1つずつ照合）

旧版のdocxからテキストを抽出して照合した。**15項目すべて一致した。**

| 草稿の数値 | 旧版の該当箇所 | 判定 |
| --- | --- | --- |
| 較正用13本が±6セント（RMS 5.9セント） | 5.1節「±6セント（二乗平均平方根で5.9セント）以内で鳴り」 | 一致 |
| 12音（G#6からG7）を各3本、計36本のコーム、3回通し | 5.1節「12音（G#6からG7）を各3本，計36本並べた較正用のコームを印刷し，3回通して吹いて」 | 一致 |
| 繰り返しのばらつき15.2セント | 5.1節「15.2セント」 | 一致 |
| 3本のあいだの散らばり11.0セント | 5.1節「11.0セント」 | 一致 |
| 造形のばらつきは多くとも11セント程度 | 5.1節「多くとも11セント程度と言える」 | 一致 |
| 当てはめ残差 RMS 11.3セント | 5.1節「残差は二乗平均平方根で11.3セント」 | 一致 |
| 最も高いG7も3本とも±20セント以内 | 5.1節「±20セント以内」 | 一致 |
| 厚壁ヘッドの笛5本 | 5.2節「厚壁ヘッドの笛5本（F#6，A6，C7，E7，F#7）」 | 一致 |
| 25.2度と41.0度、各6回、中央値 | 5.2節「25.2 ℃と41.0 ℃…各笛を6回ずつ吹き，中央値で比べた」 | 一致 |
| C7で約39セント高い | 5.2節「約39セント高くなった」 | 一致 |
| 予測は約45セント | 5.2節「予測（約45セント）」 | 一致 |
| 残差±24セント以内、半音の境界±50セント | 5.2節「±24セント以内」「±50セント」 | 一致 |
| 4桁の数「2026」、基準笛C7を先頭に5本 | 5.3節「4桁の数「2026」…基準笛C7を先頭に置いた5本の笛」 | 一致 |
| 片側24本が鳴り相対位置が設計どおり | 6.4節「先に印刷した24本の側を実測したところ，24本すべてが鳴り」 | 一致 |
| 0度／±45度／±90度／±135度は鳴り180度だけ鳴らない | 5.4節に同文 | 一致 |
| 第3のピークが50セントから70セント高い側へ | 5.4節「50セントから70セント高い側へずれていた」 | 一致 |
| カード 85.6×54×4ミリメートル、8本、0.3ミリメートル重ね、20.8ビット | 6.1節に同文 | 一致 |
| 本立て 105×70×163.5ミリメートル、36本、64ビット、13時間09分、117グラム | 6.2節に同文 | 一致 |
| スプール 49本、26本上限、25本と24本 | 6.4節に同文 | 一致 |
| 2枚組カードで20.8ビット | 6.5節「2枚で20.8 bitを運ぶ」 | 一致 |

### 3.5　先行研究の数値（`raw2/f6-key-numbers.md` と `raw3/` に照合）

| 草稿の記述 | 照合先 | 判定 |
| --- | --- | --- |
| InfraStructs 27ビット | f6「27ビット（行列型タグ）」 | 正しい |
| AirCode 5センチメートル角に約500ビット、リードソロモン符号 | f6「約500ビット（5センチメートル角）」「冗長度40パーセント」 | 正しい |
| AirCode 撮像に3分から4分 | f6「撮像には3分から4分」 | 正しい |
| LayerCode 24ビット | f6「24ビット」 | 正しい |
| StructCode 最大228ビット | f6「36文字＝228.23ビット」 | 正しい |
| Seedmarkers 約23ビット | f6「11,358,880通り＝23.437ビット」 | 正しい |
| AnisoTag クレジットカード同寸で51ビット | f6「51ビット（53.98×85.6ミリメートル）」 | 正しい |
| AnisoTagの三者比較（51／25／40ビット） | f6「AnisoTag encodes 51 bits, LayerCode encodes 25 bits, and acoustic barcode encodes 40 bits」 | 正しい |
| InfraredTags 約83ビット、21×21、250センチメートル、6ミリ秒と14ミリ秒、132グラム | f6の該当行すべて | 正しい |
| Acoustic Barcodes 6から24ビットの符号長、訂正後12ビット（4096通り） | f6「24ビット符号で12ビット（4096通り）」 | 正しい |
| Acoustic Voxels 4ビット | f6「4ビット」 | 正しい |
| Lamello 約2ビット相当 | f6「2.0ビット相当」 | 正しい |
| Blowhole 6種類で98パーセント、上限9個、約2.6ビット相当 | f6「6個…98パーセント＝2.585ビット」「9個＝3.170ビット」 | 正しい |
| SoundOff 1277通りから15個、約3.9ビット相当 | f6「1277」「15個＝3.907ビット」 | 正しい |
| FluteCase 8本の閉管、L = 14.956 × 2^(i/12) | `raw2/v1` 57行目・97行目 | 正しい |
| Printone 104個の目標周波数のうち4例が出せず | `raw2/v2` 60行目 | 正しい |
| Printone 指孔5個で9音 | `raw2/v2` 89行目（DOUGHNUT） | 正しい |
| Printone「吹く速さの変化は10ヘルツの誤差を容易に補償できる」 | `raw2/v2` 83行目に原文 | 正しい |
| 平板型フィップル笛が10万回規模のダウンロード | `PAPER_REVISION.md` 126行目「97,000件」 | 正しい（丸め） |
| 久保ら 8個を平均99.3パーセント | `REFERENCES_TO_ADD.md` 101行目 | 正しい |
| 上平ら 2014年から数百ビット | `SURVEY.md` 47行目 | 正しい |
| DNA-of-things 老眼鏡に1.4メガバイト | `REVIEW_AND_REPOSITIONING.md` 105行目 | 正しい |
| 受動音響タグは訂正後12ビットが上限、隠された光学符号は83から500ビット | 上の各行から従う | 正しい |
| codex32 32文字、検査符号13文字、8文字以内の誤りを検出、置換4文字・消失8文字を訂正 | `raw2/v3` 58-63行目 | 正しい |
| 封印120種類が平均5分未満・平均55ドル | `REFERENCES_TO_ADD.md` 270行目 | 正しい |
| 投票機の錠が平均13秒 | `REFERENCES_TO_ADD.md` 271行目 | 正しい |
| 造形機の音響側チャネル 2016年に軸推定精度86パーセント | `REFERENCES_TO_ADD.md` 68行目 | 正しい（ただし比較の使い方は誤り1の7を参照） |
| スライサ改変で成功率が最大39パーセント上昇 | `REFERENCES_TO_ADD.md` 90行目 | 正しい |
| Smith and Senturia 1995年が「従来の構成」と呼んでいる | `raw3/c3` 全体 | 正しい |
| 視覚暗号1994年、Desmedtら1998年 | `REFERENCES_TO_ADD.md` 161行目・170行目 | 正しい（LNCS巻は1995年刊なので、会議年で書くなら本文のままでよい） |
| 4桁の暗証番号の候補は1万通り程度、112ビット以上 | `REVIEW_AND_REPOSITIONING.md` 133行目・143行目 | 正しい |
| CompactSeedQRの128ビットが70ミリメートル角1枚 | `raw2/v3` 218行目 | 正しい（版名は誤り6を参照） |

---

## 4. 確認できなかったもの

1. **「刻み幅を残る誤差のおよそ4倍にとるのが設計の目安」（3.2節）** の出典。
   旧版から引き継いだ記述で、調査記録にも根拠が見当たらない。
2. **FluteCaseの79.7パーセントが8本の管の識別に対する数値かどうか**（2.2節）。
   原典の文言は「14イベント」であり、その内訳は `raw2/v1` からは確定できない。**疑いがある。**
3. **「大阪大学の宮武らは食品用の3Dプリンタで内部構造を制御し、外観を変えずに
   食べられるタグを埋め込んでいる」（2.1節）**。`SURVEY.md` 47行目は
   「3Dプリント食品の内部に外観を変えずに情報を埋め込んでおり、UIST 2022のinteriqrに至っている」と
   書いているが、`raw/` にも `raw2/` にもこの研究の一次資料確認の記録がない。
   数値は書いていないので害は小さいが、引用する前に原典を1度当たったほうがよい。**疑いがある。**
4. **5.1節が旧版の但し書き「低い4音は1本ずつ吹き直して位置を確定させている」を落としている。**
   数値ではないが、11.3セントという残差を出した測り方の条件なので、
   落とすと測定条件が実際より良く見える。`out/cipher_mini10_calib.txt` の注記は
   「低音側8本は1本ずつ測り直した」であり、旧版の「低い4音」と本数が食い違っている。
   どちらが正しいかは記録からは決められない。
