qurihara/ai-fue/related_work_survey/raw4/check-style.md

# 草稿の日本語と構成の検査

対象は `paper/cipherflute_wiss2026_v2_draft.md`（2026年7月30日の草稿、全426行）である。行番号はすべてこのファイルのものである。

## 0. 何をどう確かめたか

1. 草稿を先頭から末尾まで全文読んだ。
2. きまりの4項目（体言止め、略語、造語、矢印）については、目視に加えて `grep` で機械的にも検査した。矢印は `→`、`←`、`⇒` の3種類を検索した。
3. 数値と用語の整合は、`fue/cipher_codec.py`、`fue/cipher_card.py`、`fue/spool_128bit.py`、`fue/bookstand_flutes.py`、`docs/cipher/cipher_config.json` を実際に読んで突き合わせた。
4. 主張の範囲は `related_work_survey/PAPER_REVISION.md` の「書いてはならないこと」「主張と証拠を1対1に対応させる」と突き合わせた。

以下、**必ず直すもの**を1章から4章に、**直したほうがよいもの**を5章から9章に、**確かめて問題がなかったもの**を10章に置く。

---

## 1. きまりに反する箇所（体言止め）

草稿には体言止めが19箇所ある。すべて、本文の流れのなかに置かれた太字の見出し語である。見出し（`###` で始まる行）は名詞句でよいと判断して数に入れていない。

### 1.1 3.5節の経路の見出し語（3箇所）

| 行 | 元の文 | 直した文の案 |
| --- | --- | --- |
| 195 | **経路1　スマートフォン。** マイク入力の周波数分析を行う… | 第1の経路は、スマートフォンによる読み出しである。マイク入力の周波数分析を行う… |
| 197 | **経路2　鍵盤楽器。** 基準笛を吹き、鍵盤の上で… | 第2の経路は、鍵盤楽器による読み出しである。基準笛を吹き、鍵盤の上で… |
| 201 | **経路3　較正用コーム。** 12個のスロットに対応する笛を並べた… | 第3の経路は、較正用コームによる読み出しである。12個のスロットに対応する笛を並べた… |

なお、どうしても見出しとして立てたいのであれば、`#### 経路1　スマートフォン` のように節の見出しへ格上げすればよい。見出しなら名詞句でも読者は見出しとして読むので、体言止めにはあたらない。本文中に太字と句点で置くと、文として読まれてしまう。

### 1.2 4.4節の主張の一覧（4箇所）

| 行 | 元の文 | 直した文の案 |
| --- | --- | --- |
| 261 | 1. **読み出しの敷居が低いこと。** 正当な利用者は… | 1. 読み出しに要する装置が少ないことである。正当な利用者は… |
| 262 | 2. **存在の分かりにくさ。** この方式を知らない侵入者に対して… | 2. 秘密がそこにあると気づかれにくいことである。この方式を知らない侵入者に対して… |
| 263 | 3. **持ち物としての単純さ。** 物体側に電子部品がないため… | 3. 持ち物として単純であることである。物体側に電子部品がないため… |
| 264 | 4. **正規の読み出しが目立つこと。** 正当な復元の手続きは音を伴うので… | 4. 正規の読み出しが人に聞こえる形で行われることである。正当な復元の手続きは音を伴うので… |

3の「である。〜ことである。」が重いのであれば、「第三に、持ち物として単純である。」のように、1.3節の貢献と同じ「第一に〜第四に」の形へそろえるのがよい。

### 1.3 5.6節の実装の見出し語（4箇所）

| 行 | 元の文 | 直した文の案 |
| --- | --- | --- |
| 319 | **カード（実装済み）。** クレジットカード大の板… | 1つめはカードであり、すでに実装してある。クレジットカード大の板… |
| 321 | **本立て（実装済み）。** 底板とその両端に立つ壁からなる… | 2つめは本立てであり、これも実装してある。底板とその両端に立つ壁からなる… |
| 323 | **スプール2枚（実装済み）。** 128ビットは笛49本… | 3つめはフィラメントのスプール2枚であり、これも実装してある。128ビットは笛49本… |
| 325 | **2枚そろって初めて開くカード（実装済み）。** 同じ作りのカードを2枚… | 4つめは、2枚そろって初めて開くカードである。同じ作りのカードを2枚… |

### 1.4 6.4節の今後の課題の見出し語（5箇所）

| 行 | 元の文 | 直した文の案 |
| --- | --- | --- |
| 365 | **複数の笛を同時に鳴らすこと。** 上に述べたとおり… | 第一に、複数の笛を同時に鳴らせるようにする。上に述べたとおり… |
| 367 | **紙の対照表による人手の誤り訂正。** 小さい有限体を選び… | 第二に、紙の対照表を用意して誤り訂正を人手で回せるようにする。小さい有限体を選び… |
| 369 | **訓練を受けていない利用者による読み取りの評価。** 本稿では実演を1回… | 第三に、訓練を受けていない利用者が読み取れるかを評価する。本稿では実演を1回… |
| 371 | **時間が経っても読めるか。** 常温での保管… | 第四に、時間が経っても読めるかを確かめる。常温での保管… |
| 373 | **偽装の効果の定量化。** 本手法を埋め込んだ日用品と… | 第五に、偽装の効果を定量化する。本手法を埋め込んだ日用品と… |

### 1.5 表の中の体言止めのうち、直したほうがよいもの（3箇所）

表のセルは名詞句が普通なので原則として問題としない。ただし次の3つは意味が取りにくいので直したい。

- 139行「なし（明記）」は、何を明記したのかが読めない。「あえて付けないと原典が明記」に直す。
- 145行「情報量の概念なし」は、実証容量の欄に入る値としては座りが悪い。「該当しない（8つの穴から1つを選ぶ方式）」に直す。
- 148行「部分的」は、脅威モデルの欄で何が部分的なのかが読めない。「一部あり」に直したうえで、表の下に一文で補うのがよい。

---

## 2. きまりに反する箇所（略語）

### 2.1 「スマホ」（2箇所、表1）

- 144行「| Acoustic Voxels [2] | スマホ | 白色雑音 | 4 bit | なし | なし |」
- 149行「| **本研究** | **不要（楽器1つ）／スマホ** | **吹く** | …」

本文は一貫して「スマートフォン」と書いている（15行、17行、87行、195行など）。表だけが「スマホ」であり、これは略語である。**「スマートフォン」に直す。**

### 2.2 「アプリ」（3箇所）

- 195行「マイク入力の周波数分析を行うWebアプリで復号する」
- 297行「スマートフォンのWebアプリだけで録音と周波数分析と復号を行い」
- 361行「読み出しアプリと端末は信頼せざるを得ない部分であり」
- 307行（要記入の指示のなか）「スマートフォンの鍵盤アプリではなく実物の楽器」

「アプリ」は「アプリケーション」の略語である。しかも本稿は33行と389行で、わざわざ「応用ソフトウェア」「基本ソフトウェア」と略さずに書いている。同じ文書のなかで方針が割れている。

直した文の案は次のとおりである。

- 195行「マイク入力の周波数分析を行うウェブ上の復号ページで復号する。」
- 297行「スマートフォンの復号ページだけで録音と周波数分析と復号を行い」
- 361行「読み出しに使うソフトウェアと端末は信頼せざるを得ない部分であり」
- 307行「スマートフォンの鍵盤ソフトウェアではなく実物の楽器」

なお、45行では同じものを「復号ページ」と呼んでいる。**「復号ページ」に統一するのがよい。**

### 2.3 単位と符号名の略記（表1と表3）

本文はすべて「ビット」「グラム」「センチメートル」「リードソロモン符号」「拡張ゴレイ符号」とかなと漢字で書いているのに、表だけがラテン文字の略記である。

- 表1と表3の「bit」は「ビット」に直す。
- 138行「約500 bit（5cm角）」は「約500ビット（5センチメートル角）」に直す。
- 140行「近赤外モジュール（132 g）」は「近赤外撮像モジュール（132グラム）」に直す。
- 138行と149行の「Reed–Solomon」は「リードソロモン符号」に直す。
- 142行の「拡張Golay等」は「拡張ゴレイ符号など」に直す。
- 135行の表頭「読出装置」は、送り仮名を落とした圧縮表記である。「読み出しに要する装置」に直す。

---

## 3. きまりに反する箇所（造語と、存在があやしい用語）

矢印は0件であった（`grep` で確認済み）。造語の疑いがあるものは次のとおりである。

| 行 | 元の語と文 | 問題 | 直した案 |
| --- | --- | --- | --- |
| 167、169 | 「スロットの刻み幅を決めるのは**誤差の収支**である」 | 「収支」は収入と支出の語であり、error budget の訳語として定着していない。読者は用語なのか比喩なのか判断できない。 | 「スロットの刻み幅は、どれだけの誤差を見込むかで決まる」 |
| 87 | 「同研究は**固定物理長方式**で「0が2つ続く列」を禁じ」 | 原典の fixed physical length の直訳と思われるが、日本語の定訳がない。 | 「同研究は、符号全体の物理的な長さを一定にする方式のもとで「0が2つ続く列」を禁じ」 |
| 107 | 「**モデル共有基盤**にも、薄く小さくサポート材なしで印刷できる…」 | 「基盤」は自作の語である。この分野では「共有サイト」が普通である。 | 「三次元モデルの共有サイトにも、薄く小さくサポート材なしで印刷できる…」 |
| 161 | 「日用品への埋め込みに用いた**外形統一版**では」 | 初出で説明せずに使っており、しかもこの版が何かを説明しているのは283行（5.1節）である。 | 「外形を最長管の長さに揃え、内部の仕切り壁で管の長さを決める形（以下、外形統一版）では」 |
| 355 | 「すなわち**同時吹鳴**は、読み出しの手間を減らすための改良ではなく」 | 「吹鳴」は存在する語だが「同時吹鳴」という複合語は定着していない。しかも365行では同じことを「複数の笛を同時に鳴らすこと」と平易に書いており、不統一である。 | 「すなわち複数の笛を同時に鳴らすことは、読み出しの手間を減らすための改良ではなく」 |
| 89 | 「半音の格子で受動的な**多管構造**を作るという設計は」 | 「多管」は熱交換器の語であり、この文脈では自作の語に見える。 | 「半音の刻みに合わせて複数の管を並べるという設計は」 |
| 87 | 「離散した基本周波数の集合をド・ブラン列の**字母**として扱う」 | 「字母」は印刷と文字学の語であり、符号理論の alphabet の訳としては使われない。 | 「離散した基本周波数の集合を、ド・ブラン列を作るための記号の集合として扱う」 |
| 35、123 | 「この**交換関係**は、…そのまま表れている」「覆えば読めず読むには外すという**交換関係**を認めている」 | 「交換関係」は量子力学の commutation relation の定訳であり、trade-off の意味では衝突する。 | 「この二律背反は」「覆えば読めず、読むには外さねばならないという二律背反を認めている」 |
| 235 | 「開口部の計測や透過撮影や**計算機トモグラフィ**により」 | 一般の呼称は「コンピュータ断層撮影」である。 | 「開口部の計測や透過撮影やコンピュータ断層撮影により」 |
| 91 | 「利用者ごとの**スペクトル指紋**の照合であり」 | 原典由来の語かどうかが読者に分からない。 | 「利用者ごとのスペクトルの特徴の照合であり」 |
| 83、261 | 「「読み出しの**敷居**」という軸で並べると」「読み出しの敷居が低いこと」 | 「敷居が高い／低い」は本来「気後れする」の意味であり、参入障壁の意味で使うのは口語の転用である。学術論文には向かない。 | 「「読み出しに何が要るか」という軸で並べると」「読み出しに要する装置が少ないこと」 |
| 183 | 「記号数を4から**実効3**へ落とす数え方まで」 | 「実効3」「実効11」は数値に接頭語を付けた自作の表記である。 | 「記号数を4から実効的に3へ落とす数え方まで」 |
| 295、297、301、383 | 節見出し「印刷から復元までの**通し**」、「一連が実機で**通る**」、「49本を**通した**復号」、「**通し**の実証」 | 「通し」を名詞として使うのは現場の口語であり、意味が取りにくい。 | 節見出しは「印刷から復元までの一連の手順」、本文は「一連の手順が実機で成立する」「49本を用いた復号は未実施である」「端から端までの実証」 |

---

## 4. 内容の矛盾と、証拠のない主張（投稿前に必ず直す）

きまりの検査とは別に、このまま出すと査読で確実に突かれる矛盾が5つある。

### 4.1 5.4節が空のまま、5.4節の結果を断定している（最重要）

- 305行「**3.5節で述べた経路2と経路3を実機で確かめた。**」
- 307行「【要記入：ここに実演の記述を入れる。…】」

本稿の中心の主張は17行と45行と381行の「鍵盤楽器がひとつあれば人間が読める」であり、その唯一の証拠になるはずの節が空である。にもかかわらず305行は「確かめた」と完了形で書いている。**中心の主張に証拠が1つも付いていない状態である。** `PAPER_REVISION.md` の95行も、この節を新設することを改訂の要点に挙げている。実演を行って書き足すまでは、305行を「これから確かめる」と書き換えるか、この節ごと外すかのどちらかにしないと、主張と証拠が対応しない。

### 4.2 「光学的な符号は表面に露出していなければ読めない」を、2.1節が否定して2.5節が肯定している

- 73行「**AirCodeもInfraredTagsも外部に開口をいっさい持たない。** したがって「光学的な符号は表面に露出していなければ読めない」という主張は成り立たず」
- 123行「**そしてこれらに共通する制約が、本研究の位置づけを定める。** 光学的な符号は表面に露出していなければ読めない。」

同じ命題を、2.1節が反証と名指しで否定し、2.5節が地の文で肯定している。`PAPER_REVISION.md` の118行は、これを「書いてはならないこと」の筆頭に挙げている。

123行の意図は、2.5節で挙げた秘密保管用の実装（SeedQR、QR SafeShare）に限った話だと思われる。**主語を限定して直す。**

> 直した文の案：「そしてこれらの秘密保管用の実装に共通する制約が、本研究の位置づけを定める。いずれも符号が表面に露出していなければ読めない設計であり、QR SafeShareの錠つきの覆いも、SeedQRの滑り蓋つきの容器も、覆えば読めず、読むには外さねばならないという二律背反を認めている。」

### 4.3 128ビットを「実証容量」として表1に載せている

- 149行「| **本研究** | … | **3.5 bit/本、計128 bit** | …」
- 133行「**表1　先行研究との比較（実証容量は原典の記載による）**」
- 301行「**49本を通した復号は未実施である。**」

表1の欄名は「実証容量」であり、他の行はすべて原典が実証した値である。そこに、本研究だけが未実証の128ビットを並べている。`PAPER_REVISION.md` の28行は、これを「引用漏れよりも重い正確性の失敗」と書いている。

**直した案：** 表1の本研究の行を「実証容量」欄では「3.5ビット／本。通しで実証したのは4桁の記号列（約13.8ビット）」とし、設計上の到達点である128ビットは欄外の注に回す。あわせて次の2箇所も同じ扱いにそろえる。

- 19行「フィラメントのスプール2枚に49本で128ビットを載せた」は、「載せた」が実証を含意して読める。「フィラメントのスプール2枚に49本を並べて128ビットを載せる物体を作製した」とし、その直後に「ただし、吹いてから照合するまでを通して確かめたのは4桁の記号列までである」を足す。
- 83行「128ビットに到達する位置にある」も、設計上の値であることを一言添える。

### 4.4 「スロット数を素数にとれば」が、実装（12スロット）と合わない

- 187行「誤り訂正にはリードソロモン符号を用いる。**スロット数を素数にとれば**、その素数を位数とする有限体の演算をそのまま組むことができ、笛1本が計算上の1記号に対応する。」
- 165行「実装では…**12個のスロット**を用いる」
- 367行「有限体の位数を11に**とれば**乗算表は11×11の1枚である」

12は素数ではない。実装を読むと、素数にとっているのはスロット数ではなく、隣接同音の禁止によって残る実効の記号数のほうである。`fue/cipher_codec.py` の291行から305行の `_wire_params` が、`no_repeat=True` のとき `p = _prime_below(m - 1)` としている。実装が使うのは `SLOT12`（`fue/cipher_card.py` 31行、`fue/spool_128bit.py` 41行、`fue/bookstand_flutes.py` 49行がいずれも `lo_note="G#6", hi_note="G7"`）であり、m=12、m−1=11、11は素数なので p=11、すなわち GF(11) である。

したがって、

> 直した文の案：「誤り訂正にはリードソロモン符号を用いる。隣り合う笛が同じ音にならない制約のもとでは、記号は実効でスロット数から1を引いた数になる。この実効の記号数が素数であれば、それを位数とする有限体の演算をそのまま組むことができ、笛1本が計算上の1記号に対応する。実装ではスロット数を12にとってあり、実効の記号数11は素数であるから、位数11の有限体上のリードソロモン符号をそのまま用いている。」

これに合わせて367行も、仮定形をやめて事実として書ける。

> 直した文の案：「本研究の実装はすでに位数11の有限体を用いているので、乗算表は11×11の1枚で足りる。回転円板を添えれば、リードソロモン符号の復号も人手で回せる。」

### 4.5 側チャネルの節で、種類の違う数字を並べている

255行「2024年には離れた場所の市販の携帯電話の音響と磁界から軸方向の平均精度98.80パーセントに達している [61]。本手法では半音1段が実効長の約5パーセントに対応するため、**この精度はスロットの粒度に迫っている。**」

98.80パーセントは軸方向の識別が当たった割合であり、寸法をどれだけ細かく測れるかを表す量ではない。約5パーセントは長さの比である。**当たった割合と長さの比を「迫っている」で結ぶのは、単位の異なる量の比較である。**

> 直した文の案：「本手法では半音1段が管の実効長の約5パーセントに対応する。造形機の動きをここまで細かく復元できるかは報告された指標からは直接には言えないが、工具経路の復元がこの水準に近づいていることは、脅威として見積もっておくべきである。」

---

## 5. 同じことを2箇所以上で繰り返している箇所

白紙から書いたためか、同じ議論が最大4回現れる。削れる量は本文でおよそ1ページ分ある。

| 内容 | 現れる箇所 | 判断 |
| --- | --- | --- |
| うなりによる同音の判定と、2キロヘルツ帯で1セントが約1.2ヘルツという説明 | 49行（1.2節）と199行（3.5節）がほぼ同文。加えて17行（概要）と381行（おわりに）にも短い形がある | **49行を3文ほどに縮め、詳しい説明は199行に一本化する。** 同じ数値の説明を2回読ませる必要はない |
| 「較正用のコームを1本持てば外部の楽器すら要らず、3Dプリントした物体だけで書き込みから読み出しまでが閉じる」 | 17行、51行、201行、381行の4箇所がほぼ同文 | 概要（17行）と3.5節（201行）に残し、**51行と381行は「較正用コームによる経路も用意した」の一言に縮める** |
| 共鳴型センサの原理を受動的な共鳴管へ移したという位置づけ | 61行（1.3節の貢献第三）と175行（3.3節）がほぼ同文 | **61行を一文に縮める。** 貢献の一覧は宣言だけでよく、根拠と出典は3.3節に置く |
| 「機械が要らない」の適用範囲の書き分け | 203行（3.5節末尾）と343行から347行（6.2節）がほぼ同文。203行自身が「この線引きは6章で改めて述べる」と重複を認めている | **203行を削り、「適用範囲は6.2節で述べる」の一文だけ残す。** 6.2節に一本化する |
| 「紙の対照表を用意すれば人手の誤り訂正も可能で、codex32が実現している」 | 203行の末尾と367行（6.4節） | **203行の側を削る** |
| クレジットカード寸法での容量比較（20.8ビット対51ビット対25ビット） | 151行（2.6節）と351行（6.3節） | **どちらかに寄せる。** 位置づけを述べる2.6節に残し、6.3節は「2.6節に示したとおり密度で劣る」と参照するのがよい |
| 偽装の効果には天井があるという議論 | 241行（4.1節第四）と353行（6.3節）と359行（6.3節） | 353行は4.1節を参照しているので許容できるが、**359行は353行とほぼ同じことを別の言い方で述べており、削れる** |
| 息の強さは比を取っても消えないという議論 | 179行（3.3節）、293行（5.2節）、355行（6.3節）、365行（6.4節）の4箇所 | 179行が原理、293行が実測、355行が限界、365行が課題なので役割は分かれている。ただし**355行と365行は隣接しており、365行の「上に述べたとおり」以下は削れる** |
| 秘密分散に秘匿を一元化するという宣言 | 19行、219行、272行（表3）、327行、383行の5箇所 | 概要と結論は残す。**327行の「秘匿の力は秘密分散にのみ負わせている」は、219行と表3で既に述べているので削れる** |
| 視覚暗号とDesmedtらの偽装の動機 | 125行（2.5節）と327行（5.6節） | **327行を「2.5節で述べた視覚暗号の系譜にあたる」の一文に縮める** |
| SeedQRの仕様書が撮影を禁じているという事実 | 35行（1.1節）と123行（2.5節） | 1.1節は問題提起として必要である。**123行の側は「前述のとおり」で足りる** |

---

## 6. 主語と述語が対応していない文、係り先が曖昧な文

| 行 | 元の文 | 何が問題か | 直した文の案 |
| --- | --- | --- | --- |
| 335 | 「第一に、読み出しの手段が**偏在**している。」 | **漢字の誤りである。** 「偏在」は「ひとところに偏って存在する」の意味であり、続く「マイクはすべてのスマートフォンに載っており、平均律の鍵盤楽器は世界中にある」と正反対である。正しくは「遍在」である | 「第一に、読み出しの手段がどこにでもある。」（「遍在」は読み違えられやすいので、平易に開くほうがよい） |
| 49 | 「本手法の置き場の刻みは100セントであるから、**桁違いに細かい**。」 | 「細かい」の主語が刻みだと読める。しかし言いたいのは「聞き取れる精度のほうが刻みより桁違いに細かい」である。**意味が逆に読める** | 「本手法の置き場の刻みは100セントであるから、要求される精度に対して大きな余裕がある。」（199行が既にこの形で書いている） |
| 179 | 「**気温は物体と空気の性質なので**共通に効くが」 | 気温は物体と空気の「性質」ではない。主語と述語が対応していない | 「気温は物体と周囲の空気に一様に働くので共通に効くが」 |
| 193 | 「**本手法の中核はこの節である。**」 | 手法の中核が「節」であることはない | 「本手法の中核をなすのは、この節で述べる3つの読み出しの経路である。」 |
| 253 | 「ただしこれはデータの経路を守るだけであり、**造形機が発する物理量は守れない**。」 | 「物理量を守る」は目的語が合わない。守るのは秘密であって物理量ではない | 「ただしこれはデータの経路を守るだけであり、造形機が発する音や振動といった物理的な信号からの漏洩は防げない。」 |
| 185 | 「同じ等式から、**音域を半音1つ広げれば、この制約は容量の代償なしに手に入る**ことも従う。」 | 制約は「手に入る」ものではない。また「等式」は式のこと | 「同じ式から、音域を半音1つ広げれば、この制約を容量の代償なしに導入できることも導かれる。」 |
| 185 | 「すなわち**余分な冗長は生じていない**。」 | 「冗長」は形容動詞であり、名詞として使えない | 「すなわち余分な冗長性は生じていない。」 |
| 283 | 「**100セント刻みに対して十分に小さい。**」 | 主語が落ちている。何が小さいのか（残差か、ばらつきか）が読めない | 「これらの残差は、100セント刻みに対して十分に小さい。」 |
| 297 | 「秘密を符号化し、印刷し、吹いて、スマートフォンだけで取り出して照合するという**一連が**実機で通ることを確かめた。」 | 「一連」を単独の名詞として使っている | 「…という一連の手順が実機で成立することを確かめた。」 |
| 159 | 「発音体には、**小型の円筒を軸方向に半分に割った断面の**フィップル笛（厚さ4ミリメートル、幅7ミリメートル）を用いる。」 | 「断面の」が笛に係るのか円筒に係るのかが読めない | 「発音体には、断面が半円形（円筒を軸方向に半分に割った形）のフィップル笛（厚さ4ミリメートル、幅7ミリメートル）を用いる。」 |
| 235 | 「…研究 [51] で実証されている（**ただし同研究は内径の復元になお差が残ると報告しているため、半音1段の差を確実に分離できるとまでは言えない**）。」 | 一文のなかで主張とその打ち消しが同居していて、結局どちらなのかが読めない | 2文に割る。「…研究 [51] で実証されている。ただし同研究は内径の復元になお差が残ると報告しているので、半音1段の差を確実に分離できるとまでは言えない。」 |
| 79 | 「**外観が同一の造形物に固有の音響応答を割り当て**、」 | 「固有の」が造形物に係るとも読める | 「外観が同一の造形物のそれぞれに、異なる音響応答を割り当て」 |
| 111 | 「隣り合う笛が同じ音にならないようにする制約は、8B/10B [22] のように**必ず遷移を起こして受信側が区切りを自力で見つけられるようにする符号**と狙いが同じである。」 | 「符号」の前に修飾が3段積まれていて、読み下すのに息が続かない | 2文に割る。「8B/10B [22] は、必ず信号の遷移を起こすことで、受信側が区切りを自力で見つけられるようにしている。隣り合う笛が同じ音にならないようにする制約は、これと狙いが同じである。」 |
| 35 | 「この交換関係は、二次元コードによる秘密の保管を扱う実装が、覆いを外さなければ読めないことを認めていたり、仕様書が「…」と警告していたりすることに、そのまま表れている。」 | 「〜たり」の主語が実装と仕様書で入れ替わり、一文が長すぎる | 2文に割る。「この二律背反は、既存の実装にそのまま表れている。二次元コードによる秘密の保管を扱う実装は覆いを外さなければ読めないことを認めており、その仕様書は「自分の二次元コードを絶対に撮影するな」と警告している。」 |
| 131 | 「表1に、実証された容量と読み出しに要する装置を**一次資料で確認した値で示す**。」 | 「〜を〜値で示す」の係りがねじれている。また表には誤り訂正と脅威モデルの欄もあり、文が表の中身を言い尽くしていない | 「表1に、読み出しに要する装置、実証された容量、誤り訂正の有無、脅威モデルの有無を、一次資料で確認した値とともに示す。」 |
| 393 | 「音として鳴らし、物として手渡せる**秘密は**、冷たいデータであった鍵管理を、日常の道具のなかへ**溶け込ませていく**。」 | 秘密が鍵管理を溶け込ませる、という主語と目的語の関係が成り立たない | 「秘密を音として鳴らし、物として手渡せるようにすることは、冷たいデータであった鍵管理を、日常の道具のなかへ溶け込ませることにつながる。」 |
| 365 | 「発生する音が**単独での音**と異なる可能性がある。」 | 「単独での音」が何を指すか曖昧である | 「発生する音が、1本ずつ吹いたときの音と異なる可能性がある。」 |
| 315 | 「**復号が読むのは基音だけである**ため読み取りには影響しない。」 | 「復号」が読む、という主語の立て方が不自然である。また「第3のピーク」「第2のピーク」は倍音のことなので、用語をそろえたい | 「復号の処理が用いるのは基音だけであるため、読み取りには影響しない。」あわせて「第3のピーク」は「第3倍音」、「第2のピーク」は「第2倍音」に直す |
| 241 | 「…知見 [57] は**偽装を支える側の証拠**であり、逆に…実験 [58] は**反証側の証拠**である。」 | 「〜側の証拠」という言い方が2回続き、何を支持し何を否定するのかが読み取りにくい | 「…知見 [57] は偽装が有効であることを支持し、逆に…実験 [58] はそれを否定する。」 |
| 283 | 「後者は吹き方のばらつきだけで説明がつく大きさであり、**造形そのもののばらつきは多くとも11セント程度と言える**。」 | 前半で「吹き方だけで説明がつく」と言いながら、後半で造形のばらつきに11セントを割り当てており、論理がつながらない | 「後者は前者より小さく、吹き方のばらつきだけで説明がつく大きさである。したがって造形そのもののばらつきは、多く見積もっても11セントを超えない。」 |

---

## 7. 専門用語を初出で説明せずに使っている箇所

| 用語 | 初出 | 説明がある箇所 | 対処の案 |
| --- | --- | --- | --- |
| コーム | 17行（概要） | 201行（3.5節） | 概要の初出で「較正用の笛を12本並べた櫛状の部品（以下、較正用コーム）」と一言添える |
| セント | 49行（1.2節） | 165行で「半音（100セント）」と間接的にのみ | 49行の初出で「半音の100分の1を1セントとする音程の単位」と添える |
| フィップル | 101行（2.3節）と159行（3.1節） | **どこにもない** | 159行で「リコーダーと同じしくみの吹き口（フィップル）を持つ笛」と説明する |
| スライサ | 71行（2.1節） | なし。253行と255行でも説明なしに使う | 71行で「三次元形状を印刷経路に変換するソフトウェア（スライサ）」と添える |
| シード | 119行（2.5節） | なし | 「復元用の秘密（シード）」と添える。29行の「復元用の秘密」と同じものだと分かるようにする |
| BIP-39 | 121行（2.5節） | なし | 「復元用の秘密を単語列で表す業界標準であるBIP-39」と添える |
| 2-of-2、2-of-3 | 125行（2.5節） | なし | 125行で「2つのうち2つをそろえて初めて復元できる方式（2-of-2）」と添える |
| インターリーブ | 189行（3.4節） | なし | 「符号のブロックをインターリーブして分散させ（記号を複数のブロックへ交互に振り分け）」と添える |
| 有限体、位数 | 119行（GF(32)）、187行、367行 | なし | 187行で「素数個の要素からなる有限体（その要素数を位数と呼ぶ）」と一言添える |
| 音名の表記（G#6、C7、G7） | 165行（3.2節） | なし | 3.2節で「中央のドをC4とする表記による」と一言添える。オクターブ番号の規約は複数あるので、明示しないと管長が検算できない |
| PETG | 299行（5.3節） | なし | 「長期保管に向く樹脂であるPETG」と添える |
| エントロピー | 243行（4.2節の見出し） | なし | 4.2節の冒頭で「秘密の取りうる場合の数を対数で表した量（エントロピー）」と添える |

---

## 8. 章と節の分量の釣り合い

### 8.1 いちばん重い不均衡

**5.4節（装置を用いない復号）が空である一方、5.5節（印刷の向きの自由度）が3段落ある。** 本稿の中心の主張を支える節が0段落で、周辺の造形上の知見が3段落というのは、読者に「この論文が何を大事にしているか」を取り違えさせる。`PAPER_REVISION.md` の207行も、5.5節を削る候補の筆頭に挙げている。**5.5節を結果2文に縮め、その分を5.4節に回す。**

### 8.2 そのほか

- **2章が長すぎる。** 2.1節が7段落、2.5節が6段落あるのに対し、2.4節は2段落しかない。2.4節は本稿の主張に直接は効かないので、`PAPER_REVISION.md` の207行が言うとおり一文へ縮めてよい。
- **3.6節が1文と表だけで、前後（3.5節は7段落、3.7節は4段落）と釣り合わない。** しかも表2は、実装済みの本立て（36本で64ビット）を載せずに、未実装の「20本前後」を載せている。**表2の中身を、実際に作った3つの物体（カード8本、本立て36本、スプール49本）にそろえるほうが、5.6節ともつながって読みやすい。**
- **表2の列名と値が食い違っている。** 列名は「検査用の笛」なのに、値は「1記号」「2記号」「ブロックあたり2記号」である。列名を「検査用の記号数」に直す。なお、本立ての実装は `fue/bookstand_flutes.py` の325行で `--parity` の既定値が4であり、カードやスプールの2とは異なる。表に載せるなら、この違いも書く。
- **6.1節は3段落がいずれも1文から3文で、箇条書きのように見える。** 1段落にまとめてよい。
- **1.3節の第三の貢献（61行）だけが、他の3つの倍近い。** 5章で述べた重複の解消と同時に縮まる。
- **図の参照が図1から図3で止まっている。** 5章には図の参照が1つもない（307行の要記入のなかにだけ「図を1枚添える」とある）。5.4節、5.5節、5.6節に図が入るはずなので、番号の設計をやり直す必要がある。

---

## 9. 口語的な箇所と、硬すぎる箇所

### 9.1 学術論文として口語的にすぎる箇所

| 行 | 元の文 | 直した文の案 |
| --- | --- | --- |
| 169 | 「**ピアノが復号表なのである。**」 | 「言い換えれば、ピアノがそのまま復号のための対照表になる。」（あわせて、直前の文が「対照表」、この文が「復号表」と言葉を変えている点も統一する） |
| 203 | 「経路2と経路3の適用範囲について、**正直に述べておく**。」 | 「経路2と経路3が適用できる範囲を、あらかじめ区別しておく。」 |
| 343 | 「**正直に書き分ける必要がある。**」 | 「適用できる範囲を明確に区別する必要がある。」（「正直に」は、そう書かない箇所では不正直だと読まれかねない） |
| 105 | 「同じ物理現象に対して、一方が可変性を資源とみなし、他方が**敵とみなしている**。」 | 「同じ物理現象を、一方は利点とみなし、他方は誤りの原因とみなしている。」 |
| 173、179 | 「**全部の笛**の音が同じ向きに」「**全部の笛**に同じ割合で掛かる変動だけである」 | 「すべての笛」 |
| 241 | 「標的の出現率が低いほど見落としが**劇的に**増える」 | 「標的の出現率が低いほど見落としが著しく増える」 |
| 51、201 | 「そこには**電子機器がどこにも登場しない**」 | 「そこでは電子機器をいっさい用いない」 |
| 391 | 「人と人との関係のなかで秘密を扱う場面に**馴染む**。」 | 「馴」は常用漢字表にない。「場面になじむ」と開く |
| 105 | 「**ただし要求が正反対である。**」 | 主語が落ちている。「ただし、Printoneと本研究とでは要求が正反対である。」 |

### 9.2 硬すぎて読み下しにくい箇所

- 61行の貢献の第三は、名詞を4つ重ねた一文（「基準体を同じ物体に同居させ、比で読んで環境の変動を打ち消す構成を、受動的な共鳴管と離散符号の復号へ移したことである」）で、1文では処理しきれない。5章で述べたとおり縮めれば解消する。
- 91行「認識はメル周波数ケプストラム係数とサポートベクターマシンによる利用者ごとのスペクトルの特徴の照合であり」も名詞が続く。「認識は、メル周波数ケプストラム係数を特徴量とし、サポートベクターマシンで利用者ごとのスペクトルの特徴を照合することで行う。」と動詞で受けるほうが読みやすい。
- 167行「読み間違いを十分に減らすには刻み幅を残る誤差のおよそ4倍にとるのが設計の目安であり」は読点がなく、係りが取りにくい。「読み間違いを十分に減らすには、刻み幅を、残る誤差のおよそ4倍にとるのが設計の目安である。」と読点を足す。

### 9.3 語の不統一（読むたびに別の概念かと考えさせる）

| 同じものを指しているのに | 揺れている箇所 | 統一の案 |
| --- | --- | --- |
| 基準笛と基準体 | 61行が「基準体」、173行以降が「基準笛」 | 「基準笛」に統一する |
| 断片とシェア | 117行、121行、221行、235行が「断片」、125行と327行が「シェア」 | 「断片」に統一し、125行で一度だけ「断片（シェア）」と併記する |
| ウォレットと財布 | 29行が「暗号資産のウォレット」、119行が「対応する財布が存在しない」 | 「ウォレット」に統一する |
| 担体、媒体、記憶媒体、物理媒体 | 13行ほかが「担体」、91行が「記憶媒体」、119行が「物理媒体」、327行が「媒体」 | 「担体」に統一する。91行の「記憶媒体ではない」だけは対比として効いているので残してよい |
| 3Dプリンタと造形機 | 15行ほかが「3Dプリンタ」、253行と255行が「造形機」 | 「3Dプリンタ」に統一する |
| 対照表と復号表 | 169行に両方が並ぶ | 「対照表」に統一する |
| スロット、置き場、格子 | 165行が「置き場（以下スロット）」、19行と49行が「置き場」、89行が「半音の格子」 | 概要では「音の高さの置き場」でよいが、49行は本文なので「スロット」の定義より前である。3.2節の定義を1.2節へ前倒しするか、49行を「置き場（後述するスロット）」とする。89行は「半音の刻み」にそろえる |
| 記号と数字 | 165行が「笛1本が1つの数字を表す」、以降は一貫して「記号」 | 165行を「笛1本が1つの記号を表す」に直す |
| 語彙と字母 | 111行と165行が「語彙」、87行が「字母」 | 「記号の集合」に統一する |
| 復号ページ、Webアプリ、読み出しアプリ | 45行、195行、297行、361行 | 「復号ページ」に統一する（2.2節を参照） |
| LayerCodeの容量 | 139行の表が24ビット、151行の引用が25ビット、351行が25ビット | 151行はAnisoTagの本文からの引用なので25でよい。**351行は地の文なので、原典の24ビットに直すか、「AnisoTagの本文の記載では25ビット」と出典を明示する** |

### 9.4 文体の混在

117行「Casascius物理ビットコイン [14] は鍵を封入したコインを製品化したが、製造者が鍵を知り得る**構造だった**。」だけが「だ」体である。本稿はそれ以外「である」体で通っている。**「構造であった」に直す。**

### 9.5 「鍵」という語が2つの意味で使われている

- 暗号の鍵として：21行「鍵管理」、117行「鍵を封入したコイン」、391行「複数人での鍵の開封」
- 鍵盤の鍵として：47行「鍵盤の上で一致する鍵を探す」「鍵をいくつ隔てているか」、91行「8個の鍵を持つ鍵盤」、197行、307行

同じ論文のなかで、しかも「鍵管理」と「鍵盤の鍵」がどちらも中心語として出てくる。読者は毎回どちらか判断しなければならない。**鍵盤のほうを「鍵盤の音」または「鍵盤上の位置」に言い換えると、この負荷が消える。** たとえば197行は「基準笛を吹き、鍵盤の上で同じ高さになる音を探す。各データ笛についても同じことをして、基準笛の音からいくつ隔てているかを数える。」となる。

### 9.6 同じ数字が別のものを指していて紛らわしい

283行の較正用コームが「計36本」、321行の本立てが「笛36本」である。別の物体なのに同じ本数なので、読者は取り違える。**321行に「5.1節の較正用コームとは別の物体である」と一言添えるか、5.1節の側を「12音を各3本ずつ」とだけ書いて合計を書かないほうがよい。**

---

## 10. 確かめて問題がなかったこと

1. **矢印による接続は0件であった。** `→`、`←`、`⇒` の3種類を `grep` で全文検索したが、1件も現れなかった。
2. **単位のかな書きは本文で一貫していた。** 「ミリメートル」「ヘルツ」「キロヘルツ」「パーセント」「セント」「ビット」「グラム」「メガバイト」「ミリ秒」はすべてかなで書かれており、ラテン文字の略記が混ざるのは表1と表3だけであった（2.3節で指摘済み）。
3. **「基本ソフトウェア」「応用ソフトウェア」「二乗平均平方根」「メル周波数ケプストラム係数」「サポートベクターマシン」は、いずれも略さずに書かれていた。** 略語を作らないという方針は、本文ではおおむね守られている。
4. **章と節の番号は1章から8章まで飛びも重複もなかった。** 2.1から2.6、3.1から3.7、4.1から4.4、5.1から5.6、6.1から6.4のいずれも連番である。
5. **式 f = A/(L+e) の較正定数は実装と一致していた。** 161行の A = 91891.5、e = 14.23 は `fue/cipher_codec.py` の `CodecConfig` の既定値（`calib_k=91891.5`、`calib_delta=14.23`）と一致する。また `fue/cipher_card.py` の48行、`fue/spool_128bit.py` の55行、`fue/bookstand_flutes.py` の340行は、いずれも `docs/cipher/cipher_config.json` を読み込んだうえで `SLOT12` を上書きしているが、この設定ファイルに較正定数は入っていないので、埋め込んだ物体は確かに既定値を使っている。161行の【要確認】のうち「実装の既定値であること」は正しい。
6. **165行の【要確認】は実在の食い違いであった。** `docs/cipher/cipher_config.json` は `"lo_note": "G#6"`、`"hi_note": "F#7"` であり、これは11スロットである。一方 `fue/cipher_card.py` の31行ほかの `SLOT12` は `lo_note="G#6", hi_note="G7"` で12スロットである。草稿が書いているとおり、符号化側が12、復号ページの既定が11で食い違っている。ただし物体を作る側は毎回 `SLOT12` で上書きしているので、印刷済みの物体はすべて12スロットである。**草稿の記述（12スロットで書く）は実装と合っており、注意書きの内容も正確である。**
7. **1本あたり3.46ビットという数値は実装から導ける。** `_wire_params`（`fue/cipher_codec.py` の291行）は `no_repeat=True` のとき `p = _prime_below(m-1)` とする。m=12 なら p=11 であり、笛1本が11通りを表すので log₂11 ≈ 3.459 ビットになる。185行の「1本あたりの減りは約0.13ビット」も、log₂12 − log₂11 = 3.585 − 3.459 = 0.126 で合っている。
8. **差分の写像が上限 log₂(q−1) を達成するという185行の主張は正しい。** `_diff_encode`（308行）は `prev = (prev + 1 + d) % m`、`d` は 0 から m−2 の範囲であり、直前と等しくならない値を m−1 通りから選べる。有限長でも1記号あたり log₂(m−1) をちょうど達成する。
9. **「音域を半音1つ広げれば制約は容量の代償なしに手に入る」も正しい。** スロットを13にすれば実効12通りとなり、制約のない12スロットと同じ log₂12 になる。
10. **物体ごとの本数は実装と整合していた。** スプールの「1枚に26本が上限」は `fue/spool_128bit.py` の `MAX_PER_PLATE = 26` と一致し、49本を2枚へ25本と24本に分けるのも `split_notes` の挙動（`per = ceil(49/2) = 25`）と一致する。本立ての36本は、16バイトではなく8バイト（`DEMO_PAYLOAD = b"pass_#26"` で64ビット）を、既定のパリティ4で符号化した結果として説明がつく。
11. **温度の議論の数値は物理と合っていた。** 173行の「気温が10度変わると約1.7パーセント」は音速の温度係数（1度あたり約0.17パーセント）と一致し、セントに直すと約29セントで「半音の約3割」も正しい。289行の「絶対温度の平方根に比例することからの予測（約45セント）」も、25.2度と41.0度から計算すると約44.7セントで一致する。ただし実測39セントと予測45セントを「よく一致する」と書くのは、差が13パーセントあるので「おおむね一致する」のほうが穏当である。
12. **5.3節で実証したと書いてある範囲は、`PAPER_REVISION.md` の指示どおりに限定されていた。** 297行が4桁の数「2026」に限っており、301行が「49本を通した復号は未実施である」と明記している。**この2文は正確である。** 問題は、概要（19行）と表1（149行）がこの限定に追随していないことである（4.3節を参照）。
13. **57行の「今回の調査の範囲では見つからなかった」は、`PAPER_REVISION.md` の130行が求める書き方（「網羅的に探して存在しなかった」と書かない）に従っていた。**
14. **参考文献[1]のBlowholeの記載は、`PAPER_REVISION.md` の157行が警告する取り違え（`gi2018-16.pdf` との混同）を避けていた。** 403行が「予稿集のファイル名は gi2018-18.pdf である」と明記している。
15. **`PAPER_REVISION.md` が「書いてはならない」とした13項目のうち、12項目は守られていた。** 破っているのは「隠蔽と可読性の両立は光学符号には原理的に得られない」の1項目だけである（4.2節を参照）。娯楽性を主張に使っていないこと、統計を伴う評価実験を入れていないこと、半音刻みの理由を「既存の鍵盤楽器が対照表になるから」としていること（169行）も、いずれも指示どおりである。

---

## 11. 直す順序の提案

1. **4章の5つ（とくに4.1の空節、4.2の自己矛盾、4.3の未実証の128ビット）を先に直す。** 内容の正しさに関わり、直すと本文の量も変わるためである。
2. **5章の重複を削る。** ここでおよそ1ページ分が空く。
3. **1章と2章のきまり違反（体言止め19箇所、「スマホ」2箇所、「アプリ」4箇所）を機械的に直す。**
4. **3章の造語と6章の主述のねじれを直す。**
5. **7章の用語の説明と9章の語の統一を、最後に一括で当てる。**
