qurihara/ai-fue/related_work_survey/raw3/c2-thermal-and-viewangle.md

# 反例の検証 — 熱で読む符号、視線角度で切り替わる符号、近距離でだけ読める符号

対象は、CipherFluteの新規性主張のうち次のものである。

> 符号を担体の外観にまったく現さずに機械可読に保てる。光学的な符号は表面に露出していなければ読めないため日用品に埋めると読めなくなるが、共鳴管は物体の内部空洞として存在でき、外部に必要なのは窓と吸込口という小さな開口だけである。この隠蔽と可読性の両立は光学符号には原理的に得られない構造的な差である。

これに対して評価者が挙げた4件について、一次資料に当たって実在と内容を確かめた。

**結論を先に書く。反例は正しい。** 4件はいずれも実在し、内容も評価者の記述とおおむね一致する。したがって「光学的な符号は表面に露出していなければ読めない」という前提は成り立たず、「隠蔽と可読性の両立は光学符号には原理的に得られない」という主張は、現在の書き方のままでは維持できない。さらに、評価者が挙げていない先行研究のなかに、CipherFluteの主張の核心である「内部の空洞そのものを符号にする」ことを光学的に実現した例（AirCode、2017年）が存在する。詳細と、この反例のもとで何が残るかを以下に書く。

---

## 1. InfoPrint

### 書誌（確認済み）

| 項目 | 内容 |
| --- | --- |
| 予稿版の題名 | InfoPrint: Embedding Information into 3D Printed Objects |
| 予稿版の著者 | Weiwei Jiang, Chaofan Wang, Zhanna Sarsenbayeva, Andrew Irlitti, Jarrod Knibbe, Tilman Dingler, Jorge Goncalves, Vassilis Kostakos（いずれもメルボルン大学） |
| 予稿の識別子 | arXiv:2112.00189（2021年12月1日投稿） |
| 出版版の題名 | InfoPrint: Embedding Interactive Information in 3D Prints Using Low-Cost Readily-Available Printers and Materials |
| 出版版の掲載誌 | Proceedings of the ACM on Interactive, Mobile, Wearable and Ubiquitous Technologies 第7巻第3号、1〜29ページ、2023年9月27日 |
| 出版版の識別子 | 10.1145/3610933 |

確認先は次のとおりである。

- https://arxiv.org/abs/2112.00189 （予稿の書誌と抄録）
- https://arxiv.org/pdf/2112.00189 （予稿の本文全文。文字を抽出して読んだ）
- https://api.crossref.org/works/10.1145/3610933 （出版版の書誌）

なお、出版版は題名が変わっており、著者に Jing Wei が加わって9名になっている。評価者が示した掲載誌と巻号と年はいずれも正しい。

### 内容（一次資料で確認したこと）

抄録の冒頭にこう書かれている。「We present a technique to embed information invisible to the eye inside 3D printed objects.」つまり、目に見えない情報を三次元印刷物の内部に埋めると明言している。

読み出しの経路は2つある。

第一は熱伝導を使う経路である。熱溶解積層方式の造形物は内部の大半が空気の充填模様であるため、埋めた情報の層と空気の層とで熱の伝わる速さが違う。そこで表面を温めると、情報の形が表面温度の分布として浮かび、熱画像カメラで読める。論文は温める手段として「hand-warming」つまり手で温めることを本文と図の両方で明示している。評価者の「手で温めた後に熱画像で読む」という記述は正確である。

第二は近赤外を使う経路である。多くのプラスチックが近赤外を透過または反射することを利用し、外側と内側で光学特性の違う材料を使い分けて、近赤外走査で読む。こちらは加熱を必要としない。

さらに重要なのは、利用者の操作による選択的な読み出しまで実演していることである。物体の左半分と右半分に別々の情報を埋め、左半分だけを手で温めると、熱画像には左の情報だけが現れて右の情報は隠れたままになる、という応用を示している。

使った器材と造形機は次のとおりである。

- 造形機は FlashForge Creator Pro 2 という低価格の2ヘッド熱溶解積層機である。情報の層は白いポリ乳酸、母材は熱画像用が黒いポリ乳酸、近赤外用が青いポリ乳酸である。
- 熱画像カメラは Optris Xi 400 で、波長は8から14マイクロメートルである。
- 近赤外分光器は DLP NIRscan Nano で、これを平面走査機に載せて走査する。

### この手法の制約（同じ論文に明記されている）

| 項目 | 熱画像による読み出し | 近赤外による読み出し |
| --- | --- | --- |
| 読み出し速度 | 即時 | 数十分 |
| 1画素の大きさ | 5ミリメートル以上 | 3ミリメートル以上 |
| 表面からの深さ | 1ミリメートル | 3ミリメートル |
| 充填率 | 20パーセント以下 | 任意 |
| 色の制約 | 任意の色でよい | 外側は黒以外、内側は白 |

情報密度を上げたり深さを増やしたりすると読み取りに失敗すると本文に書かれている。加えて、限界と今後の課題の節に「情報埋め込みの設計は平らな面に限られる。実際には平らな面を持たない設計も多いので、曲面の下への埋め込みは今後の課題である」と明記されている。

### 判定

**評価者の記述は正確であり、これはCipherFluteの主張に対する本物の反例である。** 情報は外観にまったく現れず、利用者が手で温めるという能動的な操作を経て、光学的（赤外）に機械可読になる。したがって「光学的な符号は表面に露出していなければ読めない」は誤りである。

---

## 2. Ecker と Pretsch の熱変色の二次元コード

### 書誌（確認済み）

| 項目 | 内容 |
| --- | --- |
| 題名 | Novel design approaches for multifunctional information carriers |
| 著者 | Melanie Ecker, Thorsten Pretsch（いずれもベルリンの連邦材料試験研究所） |
| 掲載誌 | RSC Advances 第4巻第87号、46680〜46688ページ、2014年 |
| 識別子 | 10.1039/C4RA08977D |

出版社のページ（https://pubs.rsc.org/en/content/articlelanding/2014/ra/c4ra08977d ）は取得が拒否されたため、次の3つで確かめた。

- https://api.crossref.org/works/10.1039/c4ra08977d （書誌）
- https://api.semanticscholar.org/graph/v1/paper/DOI:10.1039/c4ra08977d （抄録）
- https://refubium.fu-berlin.de/bitstream/handle/fub188/8339/Melanie_Ecker_Diss.pdf （第一著者 Melanie Ecker の博士論文。第6章がこの論文の再録であり、RSCの許諾を得て転載した旨と原典の識別子が明記されている）

### 内容（一次資料で確認したこと）

論文は2つの設計を示している。

**第一の設計（type 1）** は、色替え温度の異なる熱変色顔料を混ぜた層に二次元コードを彫るものである。室温で読めて、顔料の色替え温度を超えると対比が失われて読めなくなる。これは評価者の言うのとは逆向きの挙動である。

**第二の設計（type 2）** が、評価者の言う「室温では隠れており、加熱すると読める」ものである。作り方と挙動は次のとおりである。

- 厚さ2ミリメートルのポリエステルウレタン板の上に、色替え温度65度の緑の熱変色顔料を20重量パーセント含む厚さ119±6マイクロメートルの層を溶媒キャストする。
- そこに二次元コード（版1、誤り訂正水準L、符号内容は http://www.bam.de 、一辺14ミリメートル）を30ワットの二酸化炭素レーザーで彫る。
- その上を、色替え温度43度の黒い熱変色顔料を含む層で封止する。封止層の厚さは彫った部分の上で211±6マイクロメートル、それ以外の部分で152±6マイクロメートルである。

挙動は次のとおりである。23度では黒い封止層に隠れて二次元コードは見えない。70度まで加熱していくと、44度で機械可読な二次元コードが現れ、62度で下の緑の層も脱色して再び消える。冷却の途中では58度から32度の間で読める。28度より下では完全に隠れる。

読み取りには普通のスマートフォン（Samsung Galaxy S I9300）に ZXing の Barcode Scanner 4.7.0 を入れたものを使っている。専用の装置は要らない。100回の加熱冷却を繰り返しても熱変色の挙動に有意な変化はなかった。

### 「肉眼で見えない」のか「読み取れない」だけなのか

依頼で区別を求められた点について、一次資料に即して答える。

**隠れている状態は、読み取り失敗ではなく、視覚的な隠蔽である。** 博士論文の本文は「the QR code was hidden at 23 °C by the dark sealing layer」「completely hidden at temperatures below 28 °C」「temporarily concealed information」と書いており、黒い封止層が符号の模様そのものを覆い隠している。つまり符号の内容は肉眼で見えない。

ただし次の点は正確に押さえておく必要がある。**符号の内容は見えないが、符号が置かれていること自体は完全に見えている。** これは厚さ2ミリメートルほどの積層板の札であり、その最も外側の0.15から0.2ミリメートルの層が問題の黒い封止層である。したがって物体の表面には黒い正方形の区画が明らかに存在する。隠れているのは中身であって、存在ではない。この点は、表面に何の痕跡も残さないInfoPrintやAirCodeとは性質が違う。

もうひとつ、現れたときの品質にも限界がある。二次元コードが現れているときのミケルソン比は最大でも0.2程度と低い。黒い熱変色顔料の層は色替え温度を超えても完全には透明にならず、微小カプセルによる光の散乱がその原因だと論文は説明している。

### 判定

**「室温では隠れており、加熱すると読める二次元コードが2014年に実証されている」という評価者の記述は正しい。** かつ、隠れている状態は「読めない」だけではなく「見えない」水準である。ただし隠れているのは符号の内容だけであり、符号が物体の外面に存在すること自体は隠されていない。

---

## 3. 阪口らの、赤外の影による選択的な可視化

### 書誌（確認済み）

| 項目 | 内容 |
| --- | --- |
| 和文題名 | 実物体と影の変形を用いた情報の秘匿と選択的視覚化 |
| 英文題名 | Selective Visualization of Complex Information Using Physical Objects and Shadow Shapes |
| 著者 | 阪口 紗季（関西大学大学院総合情報学研究科）、東納 ひかり（関西大学総合情報学部）、松下 光範（関西大学総合情報学部） |
| 掲載誌 | 芸術科学会論文誌 第15巻第4号、157〜166ページ、2016年 |
| 識別子 | 10.3756/artsci.15.157 |
| 日付 | 受付2016年6月28日、採録2016年9月24日、公開2016年11月5日 |

確認先は次のとおりである。

- https://www.jstage.jst.go.jp/article/artsci/15/4/15_157/_article/-char/en （英文の書誌と抄録）
- https://www.jstage.jst.go.jp/article/artsci/15/4/15_157/_article/-char/ja/ （和文の題名、著者、抄録）
- https://www.jstage.jst.go.jp/article/artsci/15/4/15_157/_pdf （本文。文字を抽出して読んだ）

評価者は著者を「阪口ら」とだけ書いていたが、実在する。著者名、題名、掲載誌、年、いずれも評価者の記述と矛盾しない。

### 内容（一次資料で確認したこと）

和文抄録は次のように書いている。「本研究では……実物体への情報の秘匿と、秘匿された情報の選択的視覚化を可能にする手法を提案する。提案手法では、物体に秘匿された情報を視覚化する媒体として、影を利用する。赤外光を透過するフィルタと偏光板の性質を利用し、物体を赤外光にかざした上で、物体の回転角度に応じて光の透過／遮蔽を制御することによって、物体から生成される影の形状を変化させる。これにより、物体に秘匿された2種類の形状情報を、物体の回転角度を変える・照射する光の種類を変更する、といった条件の変化に応じて、影の形状として選択的に視覚化する。」

仕組みの核心は2つある。第一に、2分の1波長板は回転角の2倍だけ偏光面を回すので、物体を45度回すと偏光面が90度回り、後段の偏光板を通るか通らないかが反転する。これによって影の形が切り替わる。第二に、赤外を透過するフィルタは遮断波長が決まっているので、照射する赤外の波長を変えると、透過する部分と遮蔽される部分の組み合わせが変わり、別の情報が現れる。

使った器材は次のとおりである。波長770、810、870、940ナノメートルの赤外発光ダイオード（LN-1804P）、赤外透過フィルタ（富士フイルムのSC-74は遮断740ナノメートル、IR-80は遮断800ナノメートル）、赤外に感度のある白黒カメラ（Watec WAT-902H ULTIMATE）と対応レンズ（TAMRON 12VM412ASIR）、影を結ぶための投影スクリーン（きもとのDILAD）である。著者らは先行して SIGGRAPH Asia 2014 の Emerging Technologies で Slanting Shadow を発表している。

### 判定

**「物体内部の情報を赤外線による影として選択的に可視化し、物体の回転によって表示情報を切り替えることまで扱っている」という評価者の記述は正しい。** 加えて、切り替えの軸は回転角度だけでなく照射する赤外の波長にもあり、評価者が述べたより広い。

ただし読み出しの構成は重い。物体を赤外光源とスクリーンの間の光路に置く透過配置が必要であり、赤外光源と拡散スクリーンと赤外カメラが要る。手に持ったまま普通のスマートフォンで読める種類のものではない。また、この手法が対象にするのは光を通す物体であって、任意の不透明な日用品ではない。

---

## 4. Dual Modulated QR Codes

### 書誌（確認済み）

評価者が示したPDFは次の論文である。

| 項目 | 内容 |
| --- | --- |
| 題名 | Optimized Modulation and Coding for Dual Modulated QR Codes |
| 著者 | Irving R. Barron, Gaurav Sharma（ロチェスター大学） |
| 掲載誌 | IEEE Transactions on Image Processing 第32巻、2800〜2810ページ、2023年 |
| 識別子 | 10.1109/TIP.2023.3272468 |

そして、「近距離でだけ副情報を読める」という性質を主題にしているのは、その前の論文である。

| 項目 | 内容 |
| --- | --- |
| 題名 | Dual Modulated QR Codes for Proximal Privacy and Security |
| 著者 | Irving Barron, Hsin Jui Yeh, Karthik Dinesh, Gaurav Sharma |
| 掲載誌 | IEEE Transactions on Image Processing 第30巻、657〜669ページ、2021年 |
| 識別子 | 10.1109/TIP.2020.3037524 |

確認先は次のとおりである。

- https://hajim.rochester.edu/ece/sites/gsharma/papers/BarronOptimDMQRCodesTIP2023.pdf （2023年の論文の全文。文字を抽出して読んだ）
- https://api.crossref.org/works/10.1109/TIP.2023.3272468 （2023年の論文の書誌）
- https://hajim.rochester.edu/ece/sites/gsharma/papers/BarronDMQRCodesTIP2021.pdf （2021年の論文の全文。文字を抽出して読んだ）
- https://hajim.rochester.edu/ece/sites/gsharma/papers/index.html （著者の公開文献一覧。2021年の論文の項目番号と識別子を確認した）

### 内容（一次資料で確認したこと）

方式は次のとおりである。通常の二次元コードの黒い正方形の区画を、楕円形の黒い点に置き換える。区画が白か黒かで主情報を運び（これは通常の読み取り機でそのまま読める）、楕円の向きで副情報を運ぶ。楕円の向きは近距離から撮らないと確実に判別できないので、副情報には距離の制限がかかる。

2021年の論文の抄録に次のように明記されている。副情報は6インチ（約15センチメートル）の近距離では正確に復号できるが、12インチ（約30センチメートル）を超える距離から撮った画像からは復元できない。著者らはこれを proximal privacy と呼んでいる。楕円の離心率を変えることで、この距離の閾値を用途に合わせて調節できる。動機は監視カメラの普及であって、公共の場でパスワードのような私的な情報を安全にやりとりすることを狙っている。

2023年の論文はこの方式の変調と誤り訂正符号を最適化したものである。捕捉距離12、15、18、21インチでの復号成功率を測っており、距離が伸びるほど副情報の復号成功率が下がることは変わらない。

### 評価者の記述との差

ひとつ、正確でない点がある。**2023年の論文の本文には、hidden、invisible、naked eye、covert のいずれの語も一度も現れない。** 文字列を機械的に検索して確認した。この論文の主題は、中央に図案を入れる美化と副情報の両立であって、秘匿ではない。秘匿を主題にしているのは2021年の論文のほうである。

さらに、この方式は視覚的な不可視性を持たない。二次元コードそのものは物体の表面に完全に見えている。隠れているのは副情報の中身だけである。

### 判定

**「近距離でだけ副情報を読める二次元コード」という評価者の記述は正しい。** ただしその根拠は評価者が示した2023年の論文ではなく、その前の2021年の論文にある。また、この例が支えるのは「読み出し距離の制限を設計できる」という点だけであり、「不可視性」の点は支えない。

---

## 5. 評価者が挙げていないが、より直接的な反例

これらを調べる過程で、評価者が挙げていない先行研究に行き当たった。CipherFluteの主張にとってはこちらのほうが重い。

### AirCode（2017年）

| 項目 | 内容 |
| --- | --- |
| 題名 | AirCode: Unobtrusive Physical Tags for Digital Fabrication |
| 著者 | Dingzeyu Li, Avinash S. Nair, Shree K. Nayar, Changxi Zheng |
| 発表 | 第30回 ACM Symposium on User Interface Software and Technology（UIST 2017）、449〜460ページ |
| 識別子 | 10.1145/3126594.3126635 |

確認先は https://dblp.org/search/publ/api?q=AirCode+Unobtrusive+Physical+Tags+for+Digital+Fabrication&format=json および https://api.semanticscholar.org/graph/v1/paper/DOI:10.1145/3126594.3126635 である。

抄録によれば、**符号は物体表面の下に配置された空気のポケットの群れそのものである。** 空気のポケットは表面下の散乱光の輸送だけに影響するため肉眼では気づきにくく、計算撮像の手法によって検出できるようになる。読み取りには投影機とカメラを組み合わせた計算撮像を使う。

これは「物体の内部空洞そのものを符号にして、光学的に読む」ことを2017年に実現している。CipherFluteの主張のうち「共鳴管は物体の内部空洞として存在できるが、光学符号にはそれができない」という部分は、この時点ですでに成り立たない。

ただし制約はある。InfoPrintの関連研究の節によれば、AirCodeは高価なPolyJet方式の造形機を要し、その方式では物体の内部に空洞を印刷できないため印刷後に組み立てが必要であり、埋められるのは二値の情報だけである。この記述はInfoPrintの著者による要約であり、AirCodeの原典本文では確かめていない。

### InfraStructs（2013年）

| 項目 | 内容 |
| --- | --- |
| 題名 | InfraStructs: fabricating information inside physical objects for imaging in the terahertz region |
| 著者 | Karl D. D. Willis, Andrew D. Wilson |
| 掲載誌 | ACM Transactions on Graphics 第32巻第4号、2013年 |
| 識別子 | 10.1145/2461912.2461936 |

これはInfoPrintの参考文献一覧で見つけたものであり、書誌はそこでのみ確認した。原典本文には当たっていない。物体の内部に情報を造形し、テラヘルツ帯の撮像で読む手法である。テラヘルツ波は可視光ではないが、電磁波による撮像という点では同じ系列に属する。

---

## 6. 総合判定

評価者の反論、すなわち「光学符号でも不可視性と利用者の能動的な操作と読み出し距離の制限を設計できる」は、一次資料に照らして**支持される**。3つの要素それぞれに実在の先行研究がある。

| 要素 | 支える先行研究 | 内容 |
| --- | --- | --- |
| 不可視性 | InfoPrint（2021年、2023年）、AirCode（2017年） | 外観にまったく現れない。前者は深さ1から3ミリメートル、後者は表面下の空気のポケット |
| 不可視性 | Ecker と Pretsch（2014年） | 符号の内容は黒い封止層に隠れて見えない。ただし符号の存在自体は外面に見えている |
| 利用者の能動的な操作 | InfoPrint、Ecker と Pretsch、阪口ら | 手で温める、加熱する、物体を回す |
| 読み出し距離の制限 | Barron ら（2021年） | 6インチで復号でき、12インチを超えると復元できない |

したがって、CipherFluteの主張のうち次の3つの文は、そのままでは書けない。

1. 「光学的な符号は表面に露出していなければ読めない」——誤りである。InfoPrintとAirCodeが反証している。
2. 「共鳴管は物体の内部空洞として存在できる（が光学符号にはできない）」——誤りである。AirCodeの符号は内部の空洞そのものである。
3. 「この隠蔽と可読性の両立は光学符号には原理的に得られない構造的な差である」——「原理的に」は成り立たない。程度の差であって、原理の差ではない。

一点だけ、評価者の側にも不正確さがある。Dual Modulated QR Codes について評価者が示した2023年の論文は、不可視性にも秘匿にも言及していない。近距離でだけ読めるという性質を主題にしているのは2021年の別の論文であり、引用先を差し替える必要がある。ただしこれは引用の当て先の誤りであって、主張そのものは成り立っている。

---

## 7. この反例のもとで、CipherFluteに残る主張

「原理的な差」は消えるが、実測できる差はいくつも残る。誇張せずに書くなら次のようになる。

### 残るもの

**第一に、読み取り装置が日用品であることである。** InfoPrintは熱画像カメラ（Optris Xi 400）か近赤外分光器（DLP NIRscan Nano を平面走査機に載せたもの）を要する。AirCodeは投影機とカメラを組み合わせた計算撮像を要する。阪口らの手法は赤外光源と拡散スクリーンと赤外カメラを透過配置で要する。普通のスマートフォンだけで読めるのは Ecker と Pretsch の例だけであり、そこでは符号は物体の最も外側の層（厚さ0.15から0.2ミリメートル程度）にあって内部にはない。共鳴管の音はどのスマートフォンにも付いているマイクロホンで拾える。**外観に痕跡が残らないことと、装置がどこにでもあることを同時に満たしている点は、確認した範囲では前例がない。**

**第二に、埋め込める深さと形の自由度である。** InfoPrintは表面から1ミリメートル（熱画像）または3ミリメートル（近赤外）までに限られ、しかも論文自身が「平らな面の下に限られる。曲面は今後の課題である」と書いている。AirCodeも表面下の散乱に依存するので浅い層に限られる。共鳴管は物体の厚みの中を曲げて通すことができ、深さの制限が違う種類の制約になる。

**第三に、視線を必要としないことである。** ここまでのどの光学的な手法も、符号のある面に光路を通す必要がある。共鳴管が必要とするのは空気の道であって、光の道ではない。

**第四に、読み出しが物体の姿勢や置き方に依存しにくいことである。** 阪口らの手法は回転角度に依存するように設計されており、InfoPrintは平らな面を露出させて撮る必要がある。音は物体全体から出る。

### 残らないもの、および正直に認めるべきこと

**「外観にまったく現れない」ことそのものは、CipherFluteの独自性ではない。** InfoPrintとAirCodeが先にやっている。しかも、CipherFluteには窓と吸込口という2つの開口が表面に必要であり、InfoPrintには開口がひとつも要らない。表面に残る痕跡の少なさという点だけを見れば、InfoPrintのほうが上である。ここを新規性の主柱に据えるのは無理がある。

**「利用者の能動的な操作を経て読める」ことも独自ではない。** 吹くことは能動的な操作だが、手で温めることも、加熱することも、物体を回すことも同じく能動的な操作である。

したがって主張の書き方としては、「光学符号には原理的にできない」という形をやめて、「外観に痕跡を残さないこと、任意の深さと曲がった経路に置けること、読み取りにどこにでもある装置しか要らないこと、この3つを同時に満たした例は確認した範囲では他にない」という形にするのが、一次資料に照らして守れる線である。

---

## 8. 補足：基準素子による自己補正の主張について

これは今回の反例の対象ではないが、上記の資料を読むなかで関連する記述に触れたので記録しておく。

InfoPrintの復号処理は、既知の値を持つ物理的な基準素子を比の分母に使うのではなく、撮った画像そのものから大津の方法で閾値を適応的に決めることで環境の変動を吸収している。加えて、評価用の基準行列には値を1に固定した anchor bit があるが、これは標本点の空間的な位置合わせに使うものであって、環境変動を打ち消す基準としては使われていない。したがって「既知の値を持つ基準素子を同じ物体に同居させ、比で読んで環境変動を打ち消す」という構造そのものは、今回見た4件と2件の追加文献のなかには見当たらなかった。ただしこれは網羅的な調査ではなく、この主張を確かめるための調査は別に行う必要がある。

---

## 9. 確認できなかったこと

- RSC Advances の出版社ページ本体は、出版社の側で取得が拒否された（HTTP 403）ため直接には読めなかった。書誌は Crossref で、抄録は Semantic Scholar で、本文の詳細は第一著者 Melanie Ecker の博士論文（RSCの許諾を得た再録である旨と原典の識別子が明記されている）で確かめた。原典そのものの版面は見ていない。
- IEEE Transactions on Image Processing の2件は、出版社のページが有料であるため、著者がロチェスター大学のサイトで公開している版で本文を読んだ。この版には掲載号と識別子が刷り込まれており、Crossref の書誌とも一致する。
- 芸術科学会論文誌の本文PDFは、日本語の字形情報が抽出できない形式であったため、和文の本文そのものは読めていない。和文の抄録はJ-STAGEの記事ページから取得し、本文中の英数字部分（英文抄録、器材の型番、波長の数値、参考文献）は抽出して読んだ。
- AirCode の原典本文は読んでいない。書誌はDBLPで、抄録はSemantic Scholarで確かめた。造形機や組み立ての制約についての記述は、InfoPrint の関連研究の節による要約であって、AirCode の原典で確かめたものではない。
- InfraStructs は、InfoPrint の参考文献一覧に載っている書誌だけを確認した。原典には当たっていない。
