qurihara/ai-fue/related_work_survey/raw3/c6-security-soundness.md

# CipherFlute論文への暗号的健全性の指摘に対する検証

この文書は2026年7月30日に作成した。検証対象は `paper/cipherflute_wiss2026_v1.2.docx`（2026年7月29日版）と、そこで参照されている実装である。

## 0. 結論

三つの指摘はいずれも成り立つ。判定は「反例は正しい」である。

- 指摘1は正しい。4桁の秘密に対する公開のSHA-256は、秘密をそのまま公開することと変わらない。しかも実装は塩も反復もない素のSHA-256であり、検証値をURLのクエリ文字列で受け取る作りになっているため、公開を前提とした設計になっている。
- 指摘2は正しい。しかも論文の記述より実装のほうが弱い。鍵導出は素のSHA-256の1回だけであり、反復回数も塩も存在しない。AES-GCMの認証タグは、鍵の候補が当たったかどうかを外部の情報なしに判定させてしまうので、攻撃者は完全にオフラインで1,771,561通りを尽くせる。
- 指摘3は正しい。SLIP-0039の断片は128ビットの主秘密に対して200ビット（20語）であり、そのうち情報を担うのは168ビットである。論文の表5が書いている「断片は各148 bit」は仕様と合わない。CipherFlute自身の符号化器で計算すると、生の128ビットは笛49本で済むが、実際の断片1本には笛64本が必要であり、円盤2枚には収まらない。

ただし、この三つはいずれも暗号の書き方と数字の問題であって、依頼文にある二つの新規性の主張（外観に符号を現さずに機械可読を保つこと、既知の基準素子を同居させて比で読むこと）を否定するものではない。詳しくは6章に書く。

---

## 1. 検証に使った一次資料

すべて実際に取得して本文を読んだ。取得日は2026年7月30日である。

| 資料 | 版と日付 | 取得先 |
|---|---|---|
| SLIP-0039, Shamir's Secret-Sharing for Mnemonic Codes | SatoshiLabs、随時更新 | https://github.com/satoshilabs/slips/blob/master/slip-0039.md （生ファイルは https://raw.githubusercontent.com/satoshilabs/slips/master/slip-0039.md ） |
| NIST SP 800-63B-4, Digital Identity Guidelines: Authentication and Authenticator Management | 第4版、2025年7月31日確定 | https://csrc.nist.gov/pubs/sp/800/63/b/4/final 、本文は https://pages.nist.gov/800-63-4/sp800-63b.html 、識別子は https://doi.org/10.6028/NIST.SP.800-63b-4 |
| NIST SP 800-132, Recommendation for Password-Based Key Derivation, Part 1: Storage Applications | 2010年12月 | https://csrc.nist.gov/pubs/sp/800/132/final 、本文は https://nvlpubs.nist.gov/nistpubs/Legacy/SP/nistspecialpublication800-132.pdf 、識別子は https://doi.org/10.6028/NIST.SP.800-132 |
| NIST SP 800-133 Rev. 2, Recommendation for Cryptographic Key Generation | 第2改訂、2020年6月 | https://nvlpubs.nist.gov/nistpubs/SpecialPublications/NIST.SP.800-133r2.pdf 、識別子は https://doi.org/10.6028/NIST.SP.800-133r2 |
| NIST SP 800-131A Rev. 2, Transitioning the Use of Cryptographic Algorithms and Key Lengths | 第2改訂、2019年3月 | https://nvlpubs.nist.gov/nistpubs/SpecialPublications/NIST.SP.800-131Ar2.pdf |
| NIST SP 800-38D, Recommendation for Block Cipher Modes of Operation: Galois/Counter Mode (GCM) and GMAC | 2007年11月 | https://nvlpubs.nist.gov/nistpubs/Legacy/SP/nistspecialpublication800-38d.pdf |
| RFC 9106, Argon2 Memory-Hard Function for Password Hashing and Proof-of-Work Applications | 2021年9月、IRTFのInformational | https://www.rfc-editor.org/rfc/rfc9106.html |
| BIP-0039, Mnemonic code for generating deterministic keys | Bitcoin Improvement Proposals | https://raw.githubusercontent.com/bitcoin/bips/master/bip-0039.mediawiki |
| BCR-2020-011, Sharded Secret Key Reconstruction (SSKR) | Blockchain Commons | https://raw.githubusercontent.com/BlockchainCommons/Research/master/papers/bcr-2020-011-sskr.md |
| OWASP Password Storage Cheat Sheet | 随時更新 | https://cheatsheetseries.owasp.org/cheatsheets/Password_Storage_Cheat_Sheet.html |

OWASPの資料だけは標準そのものではなく実務の指針であるから、数値の根拠としては補助的に使い、規範としてはNISTの文書を引く。

---

## 2. 指摘1（4桁値の公開SHA-256）の判定

### 2.1 論文と実装が実際にどうなっているか

論文5.3節の本文は次のとおりである。

> 4桁の数「2026」を記号の列としてそのまま符号化し、基準笛C7を先頭に置いた5本の笛を、厚壁ヘッドと食品接触安全のPLA Pureで印刷した。これを先頭から順に吹き、スマートフォンのWebアプリだけで録音・周波数分析・復号を行い、あらかじめ控えておいた検証値（秘密のSHA-256ハッシュ）と一致することを確認した。

論文3.5節の本文は次のとおりである。

> 復元した値の正しさは、秘密と対になる公開の検証値（公開鍵）との照合で確かめられる。公開鍵をあらかじめ紙や物体、公開の台帳に控えておけば、復元した値から計算し直して一致を見るだけで、正しく復元できたかを誰でも確かめられる。

実装を確認したところ、読み出しアプリ `docs/cipher/index.html` は照合値を `?sha256=` というURLのクエリ文字列から自動入力する作りになっており、照合そのものは `crypto.subtle.digest("SHA-256", canonical)` の1回の呼び出しである。塩も反復もない。つまり、この検証値は公開の経路に載せる前提で設計されている。指摘が「公開の検証値として使うと」と仮定した状況は、仮定ではなく実装の既定の使い方である。

### 2.2 数の確認

4桁の秘密の候補の数を三通りに数えた。いずれも小さい。

- 4桁の十進数として数えると10,000通りである。
- 13スロットの記号4個として数えると13の4乗で28,561通りである。
- 12スロットで隣接同音を禁じた記号4個として数えると12かける11の3乗で15,972通りである。

もっとも多い28,561通りでも2の15乗に満たない。毎秒100万回しかSHA-256を計算できない貧弱な計算機を仮定しても、全候補を尽くすのに0.03秒しかかからない。したがって、この検証値を公開することは秘密を公開することと実質的に同じである。指摘は正しい。

### 2.3 一次資料が言っていること

NIST SP 800-132のAppendix A.1は、鍵導出に使われる秘密について次のように書いている。

> When passwords are used to generate cryptographic keys, it is assumed that an attacker is able to perform an offline search attack on the key derivation process using a system of his own choosing, which may be much more powerful than the system used by the authorized user to generate the key from the password. Moreover, such attacks are parallelizable. Therefore, the amount of entropy ... in the password is critical.

同じ文書のAppendix A.2.1は、塩の役目を次のように限定している。

> The purpose of the salt is to allow the generation of a large set of keys corresponding to each password, for a fixed iteration count. ... Therefore, using a salt makes it difficult for the attacker to generate a table of resulting keys, for even a small subset of the most-likely passwords.

つまり塩が防ぐのは事前計算した表の使い回しであって、一つの標的への総当たりではない。ここを取り違えると「塩を足したから安全になった」という誤りに陥る。

NIST SP 800-63B-4の3.1.1.2節（パスワードの検証者に関する規定）は、検証値の保管について次のように定めている。

> Verifiers SHALL store passwords in a form that is resistant to offline attacks. Passwords SHALL be salted and hashed using a suitable password hashing scheme. ... The salt SHALL be at least 32 bits in length ...
> In addition, verifiers SHOULD perform an additional iteration of a keyed hashing or encryption operation using a secret key known only to the verifier. ... The secret key value SHALL be stored separately from the hashed passwords. ... With this additional iteration, brute-force attacks on the hashed passwords are impractical as long as the secret key value remains secret.

そして、CipherFluteの立場にもっとも近いのが同文書の3.1.2.2節である。ここでいうルックアップ秘密とは、物理または電子の記録に秘密の一覧を保管しておき、必要なときに引いて使う認証手段のことであり、カードや紙片に印刷された値がその代表である。CipherFluteの笛はこの類型にそのまま当てはまる。

> Look-up secrets that are shorter than the minimum security strength specified in the latest revision of [SP800-131A] (i.e., 112 bits as of the date of this publication) SHALL be stored in a salted and hashed form using a suitable password hashing scheme, as described in Sec. 3.1.1.2. ... The verifier SHALL implement a rate-limiting mechanism that effectively limits the number of failed authentication attempts that can be made on the subscriber account.

112ビットという下限はNIST SP 800-131A Rev. 2に由来する。同文書は「a security strength of at least 112 bits is required at this time for applying cryptographic protection」と書いている。

ここから読み取れる規範は明快である。112ビットに満たない秘密について、標準は「塩付きのパスワードハッシュ関数で保管すること」と「回数制限を設けること」の両方を要求している。回数制限は、照合者がオンラインで存在し、試行を数えて止められることを前提にする。公開の台帳に検証値を置いて誰でも照合できるようにするという設計は、この回数制限を最初から放棄している。したがって、低エントロピーの秘密に対する公開の検証値は、標準の枠組みでは選べない選択肢である。

さらに直接に効く一次資料が、論文自身が引いているSLIP-0039にある。同仕様のAppendix（Digestの設計理由）は次のように書いている。

> Let m denote the entropy of the shared secret in bits. A disadvantage of encoding the digest of the shared secret is that an attacker who has knowledge of T − 1 share values can reduce the entropy of the shared secret to m − 32 bits by performing a brute-force search over the 2^m possible values of the shared secret and eliminating the ones which give an invalid digest. The entropy of the shared secret must be sufficiently large to make such attacks impractical, which is why this specification requires that m ≥ 128.

わずか32ビットの要約値を持たせるだけでエントロピーが32ビット減るので主秘密は128ビット以上でなければならない、と業界標準そのものが述べている。256ビットの要約値を4桁の秘密に付けたらどうなるかは、この文の帰結をたどればよい。

### 2.4 判定

指摘1は正しい。しかも論文の書き方は二重に問題がある。第一に、5.3節の実験そのものは手元に控えた期待値との照合であって公開はしていないのに、「検証値」という語が3.5節の「公開の検証値」と地続きに読める。第二に、3.5節が検証値とハッシュと公開鍵を同じものとして括弧でつないでいる。128ビットのリカバリーシードから公開アドレスを導いて照合するのは実務として正しいが、4桁の暗証番号から同じことをしてよいわけではない。両者を一つの文で並べたために、後者まで正当化されているように読める。

### 2.5 低エントロピーの秘密に対する検証値の正しい作り方

情報の量から先に整理する。候補が N 通りの秘密に対して、誰でも計算できる t ビットの検証値を公開すると、候補は概ね N を2のt乗で割った数に減る。N が10,000で t が256なら候補は1通りになる。t を4ビットに縮めても候補は625通りにしかならない。つまり、低エントロピーの秘密については「公開してよい検証値」は原理的に存在しない。t を0にする以外に候補を減らさない方法はない。この一点を認めたうえで、実務の選択肢は次の五つである。

**（あ）検証値を公開しないで手元に置く。** 5.3節の実験が実際にやったのはこれである。「あらかじめ控えておいた」と書いてあるとおり、照合値は著者の手元にあった。この場合、検証値は公開の台帳に載る性質のものではなく、秘密と同じ扱いで保管すべき値になる。もっとも素直な修正であり、実験の記述を変える必要はなく、語を正しくするだけで済む。

**（い）鍵付きの検証値にする。** NIST SP 800-63B-4の3.1.1.2節が「SHOULD」として求めている追加の鍵付きハッシュがこれである。検証者だけが知る鍵で計算するので、鍵が漏れないかぎり総当たりは効かない。ただし鍵をどこかに保管しなければならず、笛とスマートフォンだけで完結するというCipherFluteの利点と正面からぶつかる。

**（う）塩付きのパスワードハッシュ関数で計算量を上げる。** NIST SP 800-132が承認する方式はPBKDF2であり、同文書の5.1節は「The length of the randomly-generated portion of the salt shall be at least 128 bits」、5.2節は「A minimum iteration count of 1,000 is recommended」と定める。より新しい実務ではRFC 9106のArgon2idが推奨され、その第1の推奨設定は「Argon2id with t=1 iteration, p=4 lanes, m=2^21 (2 GiB of RAM), 128-bit salt, and 256-bit tag size」である。OWASPの指針はArgon2idについてm=19456（19メビバイト）、t=2、p=1を最低線とし、PBKDF2-HMAC-SHA256を使う場合は600,000回の反復を挙げている。

ただし、これは低エントロピーの秘密に対する解にはならない。NIST SP 800-132のAppendix A.2.2が費用の増え方を明示している。

> Using a PBKDF that requires C iterations to derive a key increases the computational cost of performing a dictionary attack on a password with t bits of entropy from 2^t operations to C·2^t operations

エントロピーの t は変わらず、定数倍の C が掛かるだけである。仮に1回の導出に1秒かかる設定にしても、候補10,000通りなら1台で約2.8時間で尽きる。4桁の秘密を守るには到底足りない。したがって（う）は、（あ）や（え）と併せて使う補強手段としてのみ意味を持つ。

**（え）回数制限のあるオンラインの照合に任せる。** NIST SP 800-63B-4の3.1.2.2節が112ビット未満のルックアップ秘密に対して要求しているのはこれである。暗証番号が現実に安全に使えているのは、鍵導出関数の強さではなく、試行回数を数えて止める側が存在するからである。CipherFluteで4桁の秘密を扱う用途（銀行の暗証番号、扉の合言葉など）は、まさにこの前提の上にある。

**（お）秘密のエントロピーを上げる。** 112ビット以上、実務としては128ビット以上あれば、検証値を公開しても総当たりは成立しない。暗号資産の公開アドレスがそのまま検証値になる、というのは本来この場合の話である。

**参考として、誤読の検出と秘密の隠蔽を分けること。** 復号が正しく行われたかを確かめるだけなら、短い検査符号で足りる。BIP-0039は「A checksum is generated by taking the first ENT / 32 bits of its SHA256 hash」と定め、128ビットのエントロピーに対して4ビットの検査だけを付ける。CipherFluteはすでにリード・ソロモン符号の検査記号を笛として持っているので、吹き間違いや読み違いの検出は外部の検証値なしにできる。5.3節が本当に示したかったのが「符号化から復号までが通った」ことであるなら、外部のSHA-256は本来不要である。

### 2.6 書き直し案

3.5節の該当箇所を次のように差し替えることを提案する。

> 復元した値の正しさをどう確かめるかは、秘密のエントロピーによって答えが変わる。128ビット級の秘密であれば、秘密から一方向に導かれる公開の値（たとえば暗号資産の公開アドレス）をあらかじめ紙や物体、公開の台帳に控えておき、復元した値から計算し直して一致を見ればよい。候補の数が2の128乗あるので、公開の値から秘密を逆算することはできない。一方、暗証番号や合言葉のようにエントロピーの小さい秘密については、この方法を使ってはならない。候補が数万通りしかないため、公開された検証値に対して全候補を試せば秘密が特定できてしまう。実際、SLIP-0039の仕様書は、断片に32ビットの要約値を持たせるだけで秘密のエントロピーが32ビット減ることを理由に、主秘密が128ビット以上であることを要件としている[12]。小さな秘密については、検証値を公開せずに手元に置くか、検証者だけが知る鍵を用いた鍵付きの検証値にするか、試行回数を制限できるオンラインの照合に委ねるかのいずれかを採る。NIST SP 800-63B-4は、112ビットに満たない秘密を物理の記録に持たせる場合について、塩を付けたパスワードハッシュ関数での保管と、失敗回数の制限との両方を要求している。なお、吹き間違いや読み違いの検出だけであれば、本手法が備えるリード・ソロモン符号の検査記号で足りるので、外部の検証値は必要ではない。

5.3節の該当箇所は次のように直せばよい。

> これを先頭から順に吹き、スマートフォンのWebアプリだけで録音・周波数分析・復号を行い、手元に控えておいた期待値と一致することを確認した。ここで用いた照合値は秘密そのものと同じ扱いで保管するものであり、公開してよい値ではない。4桁の秘密の候補は1万通りから3万通りに満たないため、その一方向の要約値を公開すれば総当たりで秘密が特定できてしまうからである。この実証で確かめたのは方式が通ることであって、検証値を公開できることではない。

---

## 3. 指摘2（20.8ビットの秘密によるAES-GCM）の判定

### 3.1 論文と実装が実際にどうなっているか

論文6.5節の本文は次のとおりである。

> 2枚で20.8 bitを運ぶ。（中略）さらに、合成した秘密を鍵として遷移先URLをAES-GCMで暗号化しておくと、2枚がそろったときにだけそのページが開く。これも実機で確かめ、2枚を吹き終えた時点で目的のページへ遷移した。URLを手に入れただけの者には行き先が分からない。

実装 `fue/make_goto_enc.py` の冒頭は、鍵の作り方を次のように書いている。

```
鍵    = SHA-256(canonical)                 canonical = symbolsのバイト列 or payloadのバイト列
暗号  = AES-GCM 256bit, IV 12バイト
出力  = base64url( IV(12) + 暗号文+タグ )   ← これを ?goto_enc= に載せる
```

塩はなく、反復もない。素のSHA-256を1回である。読み出しアプリ側も `crypto.subtle.digest("SHA-256", canonical)` を1回呼んで鍵にしている。

### 3.2 数の確認

論文の記述どおり、12スロットで隣接同音を禁じた6記号の空間は11の6乗で1,771,561通りである。2を底とする対数は20.757であり、20.8ビットという表記は正しい。指摘が挙げた「約177万候補」も正しい。

### 3.3 一次資料が言っていること

NIST SP 800-133 Rev. 2の6.2.3節は、秘密から鍵を作る場合の上限を明示している。

> When a key is generated from a password, the entropy provided (and thus, the maximum security strength that can be supported by the generated key) shall be considered to be zero unless the password is generated using an approved RBG. In this case, the security strength that can be supported by the password (password_strength) is no greater than the minimum of the security strength supported by the RBG (RBG_strength) and the actual number of bits of RBG output (RBG_outlen) used in the password.

乱数生成器で作った20.8ビットの秘密から作った鍵の安全性は、20.8ビットを超えない。SHA-256で256ビットに伸ばしても、AES-256で暗号化しても、この上限は動かない。指摘の「AES-GCMを使ったという事実は元の鍵のエントロピーを増やさない」はそのとおりである。

同じくNIST SP 800-132のAppendix A.2.2が示すとおり、反復回数 C を入れても費用は C かける2のt乗になるだけである。いまの実装は C が1に等しいので、その定数倍の恩恵すらない。

そして、この場合の攻撃が完全にオフラインで完結する理由がAES-GCM自身にある。NIST SP 800-38Dの認証付き復号の手順は、最後の段で次のように振る舞う。

> 8. If T = T', then return P; else return FAIL.

すなわち、鍵の候補が正しいかどうかは、その鍵で復号を試みてタグが合うかを見れば判定できる。攻撃者は正解を教えてくれる相手を必要としない。暗号文そのものが判定器として働く。1,771,561通りの候補それぞれについてSHA-256を1回とAES-GCMの復号を1回試すだけで、正解が一意に定まる。手元の計算機で数秒の作業である。

さらにNIST SP 800-131A Rev. 2が定める下限は112ビットであるから、20.8ビットは暗号による保護と呼べる水準の5分の1にも届かない。

### 3.4 判定

指摘2は正しい。しかも指摘は控えめですらある。指摘は「20.8ビットの値をSHA-256で伸ばしてAES-GCM鍵にしても安全性は20.8ビットのままである」と述べているが、実装には鍵導出関数も塩もないので、鍵導出の側から時間を稼ぐ余地さえない。

なお、6.5節の他の部分は正しい。2枚のカードによる2-of-2の分散そのものは、片方に一様乱数を置き、もう片方に秘密から乱数を引いた値を置く加法的な分散であり、片方だけからは何も分からないという情報理論的な性質を持つ。この性質は秘密のエントロピーとは独立に成立する。問題は、2枚がそろって合成された値が20.8ビットしかないことと、その値を暗号鍵と呼んでいることである。

### 3.5 書き直し案

6.5節の該当箇所を次のように差し替えることを提案する。

> さらに、合成した秘密から鍵を導き、遷移先URLをAES-GCMで暗号化しておくと、2枚がそろったときにだけそのページが開く。これも実機で確かめ、2枚を吹き終えた時点で目的のページへ遷移した。ただしこの暗号化が与える強度は、鍵の材料である秘密のエントロピーを超えない。本構成では2枚あわせて20.8ビットであり、候補は1,771,561通りにとどまる。AES-GCMの復号は認証タグが合うかどうかで鍵の当たり外れを判定できるため、暗号文を手に入れた者はオフラインで全候補を試せる。したがってこの暗号化は、URLを見ただけの通りすがりに行き先を隠す程度の役割にとどまり、暗号学的な秘匿ではない。NISTが暗号による保護に求める最低の強度は112ビットである。この構成で本当に秘匿したい情報を守ることは意図していない。より強い秘匿が必要な場合は、笛の本数を増やして秘密のエントロピー自体を112ビット以上に引き上げるか、遷移先を試行回数の制限されたオンラインの照合の背後に置く必要がある。

もし、実装の側でできる範囲の補強を併記したいのであれば、次の一文を足せる。ただしこれは強度を上げるものではなく、攻撃の費用を定数倍だけ上げるものであることを明示すべきである。

> 実装上は、鍵の導出をパスワードハッシュ関数（たとえばRFC 9106のArgon2idや、NIST SP 800-132が承認するPBKDF2）に置き換え、少なくとも128ビットの塩と実用上許せる限りの計算量を与えることで、総当たりの費用を定数倍だけ引き上げられる。ただしNIST SP 800-132が述べるとおり、この操作は候補の数を減らさず、費用を反復回数の倍数だけ増やすにすぎない。

なお、6.5節が「20.8 bit」と正直に数字を書いていること自体は評価できる。直すべきは、その数字と「暗号化しておけば分からない」という主張が両立しないまま並んでいる点である。

---

## 4. 指摘3（SLIP-39の断片の長さ）の判定

### 4.1 仕様にもとづく計算

SLIP-0039の「Format of the share mnemonic」節が定める断片の構造は次のとおりである。

| 項目 | 記号 | ビット数 | 役割 |
|---|---|---|---|
| 識別子 | id | 15 | 断片が同じ組に属することの確認に使う。ext=0のとき主秘密の暗号化の塩にもなる |
| 拡張バックアップ標識 | ext | 1 | idを塩に使うかどうかを示す |
| 反復指数 | e | 4 | PBKDF2の反復回数を10000かける2のe乗として与える |
| グループ番号 | GI | 4 | グループ断片のx座標 |
| グループ閾値 | Gt | 4 | 復元に必要なグループ断片の数 |
| グループ総数 | g | 4 | グループの総数 |
| メンバー番号 | I | 4 | グループ内の断片のx座標 |
| メンバー閾値 | t | 4 | グループ断片の復元に必要な断片の数 |
| 詰め物付き断片値 | ps | 詰め物 + 8n | nは主秘密のバイト数 |
| 検査符号 | C | 30 | RS1024の検査符号 |

仕様の本文には、128ビットと256ビットの主秘密について総長の表がそのまま載っている。

| Security | Padded share value length | Total share length |
|---|---|---|
| 128 bits | 130 bits | 200 bits = 20 words |
| 256 bits | 260 bits | 330 bits = 33 words |

128ビットの主秘密の場合を分解すると次のようになる。前置きの項目は15足す1足す4足す4足す4足す4足す4足す4で40ビットである。断片値は主秘密と同じ16バイトなので128ビットである。40足す128は168ビットであり、これを10の倍数にそろえるため2ビットの零詰めを入れて170ビットにする。ここに30ビットの検査符号を足して200ビットになり、10ビットずつ区切って20語の合言葉になる。仕様は「This structure is then converted into a mnemonic code by splitting it up into 10-bit segments with each becoming an index into a word list containing exactly 1024 words」と書いている。

したがって、断片1本が含む情報は次の三通りの数え方ができる。

- 実際に書き取る必要のある長さは200ビット（20語）である。
- 常に零である詰め物2ビットを除いた、正味の情報は168ビットである。
- 検査符号30ビットも冗長であるから捨てられるが、捨てると書き間違いの検出ができなくなる。捨てた場合の下限が168ビットである。

同じ計算を、論文が併記しているSSKR（BCR-2020-011）についても行った。SSKRは「pack the id, group and member data into 5 bytes」と定め、断片値は「Same length as the master secret」である。128ビットの主秘密なら5バイト足す16バイトで21バイト、すなわち168ビットである。SLIP-0039から詰め物と検査符号を除いた値とちょうど一致する。

いずれにせよ、断片1本は128ビットではない。128ビットの1.31倍の168ビットが必要である。

### 4.2 論文の記述との突き合わせ

論文の表5は次の行を含む。

| 層 | 量 | 秘密を守る力 |
|---|---|---|
| 秘密分散（3分の2で復元） | 断片は各148 bit | 128 bit（規定数未満では何も分からない） |

この「148 bit」は仕様のどの数え方とも一致しない。40ビットの前置きのうち20ビット分（id、ext、e）だけを数えれば148になるが、グループ番号、グループ閾値、グループ総数、メンバー番号、メンバー閾値の20ビットを落とすと、断片の x 座標が分からなくなってラグランジュ補間ができない。つまり復元不能な断片になる。148という数字は成り立たない。

一方、論文6.4節の本文は「12単語のシード相当の128 bit」と書いており、これはBIP-0039の12語（エントロピー128ビットと検査4ビット）を指しているのだから、記述としては正しい。6.4節は「秘密分散の断片を載せた」とは書いていない。したがって、指摘3が言う「49本の生128ビット実装をそのまま秘密分散シェアの実証とは呼べない」という文言のうち、「シェアの実証と呼んでいる」という部分は6.4節の本文には当てはまらない。当てはまるのは表5の148ビットという数字と、3.5節が「断片を別々の日用品に符号化して離れた場所に置けば」と述べたうえで、容量の見積もりが一貫して128ビットで語られているという構成の側である。読者は当然、断片1本も49本前後の笛に収まると受け取る。この読み取りは仕様に照らして誤りであるから、指摘の実質は正しい。

### 4.3 実際に必要な笛の本数

論文自身の符号化器（`fue/cipher_codec.py`、12スロット・隣接同音禁止・ブロックあたり検査2記号・基準笛あり）に、それぞれの長さを入れて数えた。円盤1枚に置ける上限は論文6.4節が述べる26本を用いた。

| 載せるもの | ビット数 | 記号数 | 笛の本数（基準笛込み） | 必要な円盤の枚数 |
|---|---|---|---|---|
| 生の128ビットのシード | 128 | 48 | 49 | 2 |
| 共通の32ビットを別に控えた場合の断片 | 136 | 50 | 51 | 2 |
| SLIP-0039またはSSKRの断片の正味 | 168 | 63 | 64 | 3 |
| SLIP-0039の20語をそのまま | 200 | 74 | 75 | 3 |

論文6.4節が実装したスプール2枚の構成（25本と24本で合計49本）に収まるのは、生の128ビットまでである。実際の断片1本を載せると64本になり、2枚には入らない。3枚目が要る。

なお、断片を複数の物体に分ける運用であれば、id、ext、e、グループ閾値、グループ総数の32ビットはすべての断片で共通であるから、別の場所に一度だけ控えておくことができる。そうすると物体に載せるのはメンバー番号などの8ビットと断片値128ビットで136ビットとなり、笛51本に収まって円盤2枚に載る。ただしこの場合、その物体は標準のSLIP-0039の道具にそのまま入力できる20語の合言葉ではなくなるので、共通部分をどこに控えるかを含めて運用として書かなければならない。

### 4.4 判定

指摘3は正しい。断片の長さの計算は仕様のとおりであり、論文の表5の数字は誤りである。ただし6.4節の本文自体は「シードの128ビットを載せた」と書いているだけなので、その部分に虚偽はない。直すべきは表5の数字と、断片と主秘密を同じ容量で語ってしまう構成である。

### 4.5 書き直し案

表5の該当行を次のように直す。

| 層 | 量 | 秘密を守る力 |
|---|---|---|
| 秘密分散（3分の2で復元） | 断片は各168 bit（SLIP-0039の20語＝200 bitのうち、常に零の詰め物2 bitと検査30 bitを除いた正味。SSKRでは21バイト＝168 bit） | 128 bit（規定数未満では何も分からない） |

3.5節に次の一文を足す。

> 断片1本の長さは主秘密の長さと同じではない。SLIP-0039では、128ビットの主秘密に対して断片1本が200ビット（20語）になり、識別子15ビット、拡張標識1ビット、反復指数4ビット、グループ番号とグループ閾値とグループ総数とメンバー番号とメンバー閾値の各4ビット、断片値128ビット、検査符号30ビットから構成される[12]。SSKRでも前置き5バイトと断片値16バイトで21バイトになる[13]。したがって、断片を物体に載せる場合に必要な笛の本数は、同じ長さの主秘密をそのまま載せる場合の1.3倍になる。

6.4節の末尾に次の一文を足す。

> なお、ここで載せたのは生の128ビットのシードである。3.5節で述べた秘密分散の断片1本を載せる場合は正味168ビットとなり、同じ符号化で笛64本になるので、円盤は3枚必要である。識別子や反復指数など全断片に共通の32ビットを別に控えておく運用にすれば136ビットとなり、笛51本で円盤2枚に収まるが、その場合の物体は標準の20語の合言葉そのものではなくなる。

---

## 5. 三つの指摘に共通する根っこ

三つはばらばらの誤りではなく、同じ一つの取り違えから出ている。すなわち、暗号の道具（SHA-256、AES-GCM、SLIP-0039）を使ったという事実を、その道具が普段与えている強度と取り違えている。実際には次のとおりである。

- SHA-256は逆算を防ぐが、候補が数万しかない入力については逆算を防がない。総当たりが逆算の代わりになるからである。
- AES-GCMは256ビットの鍵を要求するが、その鍵の材料が20.8ビットなら、守れるのは20.8ビットである。NIST SP 800-133 Rev. 2の6.2.3節が明示している。
- SLIP-0039は128ビットの主秘密を扱うが、断片1本はその1.31倍の長さになる。仕様の表に直接書いてある。

論文には「方式は公開でも秘密さえ守れば安全であるべき、という暗号設計の基本原則に従う」という良い一文があり、脅威モデルの表も丁寧である。今回の三点は、その誠実さがまだ届いていない箇所であり、直せば論文全体の信頼性はむしろ上がる。数字を正しく書くこと自体が、この論文の売りである「守れないことを明示する」という姿勢の延長線上にある。

---

## 6. この指摘のもとでCipherFluteに残る主張

依頼文に挙げられた二つの新規性の主張は、三つの指摘のいずれによっても損なわれない。理由を分けて書く。

第一の主張（符号を担体の外観に現さずに機械可読に保てること、共鳴管は内部空洞として存在でき外部に必要なのは窓と吸込口だけであること）は、物体の幾何と読み取りの物理に関する主張である。今回の三つの指摘は、秘密の値がどれだけ強いか、検証値をどう作るか、断片が何ビットかという話であり、担体の外観と可読性の両立にはまったく触れていない。指摘3が本数を49本から64本へ増やすので、埋め込みに必要な体積は約1.3倍になるが、これは主張の成否ではなく規模の話である。円盤2枚が3枚になっても、外観に符号が現れないという性質は変わらない。

第二の主張（既知の値を持つ基準素子を同じ物体に同居させ、比で読んで環境変動を打ち消す自己補正が、造形物への情報埋め込みの文脈で前例がないこと）も、三つの指摘とは無関係である。基準笛は温度と息の強さによる読み取り誤差を打ち消す仕組みであって、秘密の強度とは別の層にある。

損なわれるのは次の三つである。いずれも書き方の修正で回復できる。

- 「復元した値の正しさは公開の検証値との照合で誰でも確かめられる」という汎用の主張は、112ビット以上の秘密に限定しなければならない。暗証番号を含む全プロファイルに適用できるという書き方は撤回すべきである。
- 「2枚がそろったときにだけそのページが開く」「URLを手に入れただけの者には行き先が分からない」という秘匿の主張は、20.8ビットの強度しか持たないと明記しなければならない。2-of-2の分散が情報理論的に健全であるという主張は、そのまま残る。
- 「128ビットの復元用情報を約40本から49本で運べる」という容量の主張は、生のシードについては正しいが、秘密分散の断片については64本と書き直さなければならない。運べる量の上限を実用の形で示したという6.4節の位置づけ自体は残る。

三つとも、論文の中心にある「音の高さを符号として使う担体の設計」と「どの層が秘密を守り、どの層は守らないかを明示する脅威モデル」を否定しない。むしろ、脅威モデルの表に「秘密のエントロピーが小さいときに何が守れなくなるか」の行を足すことで、論文の売りである誠実さが一段強くなる。

---

## 7. 確認できなかったこと

- 論文の表5にある「148 bit」という数字が、どの計算にもとづくのかは特定できなかった。生成器 `paper/make_paper_wiss_v12.py` の503行目に直接書かれた文字列であり、根拠となる計算はコードにも文書にも残っていない。
- 現在の実装のうち、5.3節の実験で実際に検証値を公開の場に置いたかどうかは確かめられなかった。読み出しアプリが `?sha256=` を受け取る作りになっていることは確認したが、公開の台帳に載せた記録は見つからなかった。実験の記述としては「手元に控えた」であるから、公開はしていないと読むのが自然である。
- 具体的な計算機の性能値（毎秒何回のSHA-256を計算できるかなど）については、一次資料で確認できる公表値を見つけられなかったため、本文では性能を仮定した計算だけを示し、仮定を明記した。
