qurihara/ai-fue/related_work_survey/raw/09-data-over-sound.md

# 音でデータを送る通信方式の歴史と現在

調査担当の切り口は「空気中の音や電話回線の音声帯域を使ってデータを送る技術の系譜」である。電話回線のモデム、ファクシミリの手順、押しボタン信号、音響カプラ、カセットテープへの記録、放送による配布、超音波ビーコン、可聴音による端末間通信、音による機器設定、船舶と航空の音響信号までを対象とした。書誌情報はITUの勧告ページ、Crossrefのdoi登録レコード、J-STAGE、CiNii Research、著者本人の業績ページ、学会の予稿集PDF、公的機関の一次文書に当たって確認した。この文書は2026年7月30日に別の担当者が独立に検証し、9件を訂正した。訂正の内容は末尾の「検証の記録」の節にまとめてある。

## この切り口の要約

音でデータを送る技術は1960年前後に電話網のなかで体系化された。Schenkerが1960年に示した二群の音声周波数による押しボタン発信の符号は、可聴域に離散的な周波数の集合を定めて記号を割り当て、受信側は周波数の同定だけで復号する。この符号は低群と高群から1つずつ選んだ2音を同時に鳴らす「四かける四」の16通りであって、1回に1音しか出さないCipherFluteとは記号の作り方が異なる。ただし群のなかの隣り合う周波数を21対19という一定の比で並べており、対数の目盛の上で等間隔に周波数を配置する考え方はここで既に確立している。この方式はのちにITU-T勧告Q.23になった。同じ時期に周波数偏移変調のモデムがV.21として、ファクシミリの手順がT.30として整い、音声帯域は汎用の搬送路になった。1970年代には音響カプラが普及し、1975年にはカセットテープに音として計算機のデータを固定するKansas City標準が定まり、1984年にはイギリスの放送局が番組の電波でプログラムを音として配った。音の波形を物理媒体や放送に固定して配る発想はこの時期に出そろっている。

2000年代からは空気中の可聴音そのものを通信路として扱う研究が始まった。LopesとAguiarは空中音響通信を正面から扱い、符号化した信号が機械の音ではなく鳥や虫の声、映画のロボットの声、あるいは音階に沿った疑似的な旋律に聞こえるようにする設計を複数示している。2002年の共著論文は、ピアノとクラリネットと鐘の音を単純な物理モデルで合成した音片を用い、それらを音楽の和声の規則に従って組み合わせて記号を作る方式である。実物の楽器を送信機にしたのではない。その後は音響OFDM、チャープ信号、音響電子透かしが加わり、2010年代には超音波ビーコンが商用化された。この系譜のなかでCipherFluteは、送信機が形状として固定され書き換えができず、電源を持たず、人間の息だけで駆動するという極端な特殊例に位置づく。周波数スロットへの記号割り当てと誤り訂正という符号の組み合わせはggwaveなどが既に採っており、音階の音に記号を割り当てるという発想もLopesとAguiar、およびMadhavapeddyらが2000年代半ばまでに実装しているため、新規性はそこに置かないほうがよい。

## 新規性への脅威が大きい文献

2026年7月30日の検証の結果として一言添える。この節に「高」と判定した文献は1件も残らなかった。当初「高」とされていたDominguesらの2002年の論文は、要旨に当たって内容を確かめた結果「中」に下がった。ただしこれは安心してよいという意味ではない。符号の語彙の作り方という面では、下記の第11項のMadhavapeddyらの旋律によるデータ伝送がCipherFluteの設計をほぼ先取りしており、この切り口で最も注意して差分を述べるべき文献は第11項である。当初の調査担当者はこの点を見落としていたので、判定の理由を書き換えた。

### 1. Aerial communications using piano, clarinet, and bells

- 著者: Natacha Domingues, João Lacerda, Pedro M. Q. Aguiar, Cristina Videira Lopes
- 発表: 2002 IEEE Workshop on Multimedia Signal Processing (MMSP), pp. 460-463, 2002年12月
- 確認先: https://doi.org/10.1109/MMSP.2002.1203345 （Crossrefのdoi登録レコードで題名、4名の著者、会議名、ページを確認した）
- 著者本人の業績ページでも確認した: https://ics.uci.edu/~lopes/publications.html （著者名の綴りを Natacha Domingues, João Lacerda, Pedro M. Q. Aguiar, Cristina Lopes と確認し、発表が2002年12月であることも確認した）
- 要旨の全文はOpenAlexの登録レコードから取得した: https://api.openalex.org/works/doi:10.1109/MMSP.2002.1203345

内容の要約を述べる。ここは2026年7月30日の検証で大きく書き換えた箇所である。要旨の全文に当たった結果、この論文は実物のピアノやクラリネットや鐘を送信機に使ったものではないことが判明した。要旨は、機械と機械のあいだの空中音響通信の新しい仕組みを探る研究であり、ピアノ、クラリネット、鐘の音についての単純なモデルから音の素片を作り、その素片を音楽の和声に従って組み合わせることで記号列を符号化すると述べている。すなわち送信側はスピーカーから合成音を出す装置であり、出てくる音が楽器のように聞こえるという点が主眼である。Crossrefが登録している参考文献の一覧にChowningの周波数変調による複雑な音色の合成の論文が含まれていることも、合成による音作りであることを裏づける。要旨は伝送速度について「ごく低いビットレートを要求する応用に向く」とだけ述べ、具体的な数値を挙げていない。同じ著者らはWASPAA 2001で空中音響通信の基本方式を、IEEE Pervasive Computing 2003で音響モデムの全体像を発表しており、この論文はその中間に位置する。

CipherFluteとの関係を述べる。CipherFluteは笛という実際の発音体が出す楽音の高さを記号として使う。この論文が示したのは、合成音の音色と和声を人の耳に自然に聞こえるように設計するという方向であって、実体のある発音体を符号の担体にする話ではない。したがってCipherFluteが「実物の発音体の音高で符号を運ぶ」と述べるかぎり、この論文と正面から衝突することはない。ただし「楽音を通信の記号にする」という水準の着想はこの論文と、同じ著者らのWASPAA 2001およびIEEE Pervasive Computing 2003が先行している。

脅威の度合いは、当初の調査担当者の判定「高」を「中」に引き下げる。理由を述べる。要旨に当たったところ、送信機が受動的な物体ではなく合成音を鳴らす能動的な装置であり、CipherFluteの中核の主張である「電源も可動部もない造形物が符号を保持する」とは別の対象を扱っていることが確認できたからである。それでも音階や和声を符号の語彙にするという着想の先行例であることは変わらないため、引用して差分を明示する必要は残る。

### 2. ggwave（データ・オーバー・サウンドの実装）

- 著者: Georgi Gerganov（オープンソース実装、継続的に開発）
- 発表: ソフトウェアリポジトリ（学術発表ではない）
- 確認先: https://github.com/ggerganov/ggwave （説明文の全文を https://raw.githubusercontent.com/ggerganov/ggwave/master/README.md で取得し、以下の数値がすべて原文どおりであることを確認した）

内容の要約を述べる。ggwaveは音でデータを送るための小さなライブラリであり、多周波の周波数偏移変調を用いる。周波数間隔は46.875ヘルツで、可聴用のプロトコルは1875.000ヘルツ、超音波用のプロトコルは15000.000ヘルツを基準周波数とし、4.5キロヘルツの帯域に96個の等間隔の周波数を並べる。データは4ビットずつに分割され、各片が特定の周波数に割り当てられ、6つの音を同時に鳴らして1回あたり3バイトを送る。全体の伝送速度は毎秒8バイトから16バイトであるとリポジトリの説明文に書かれている。復調の頑健性を上げるためにReed–Solomon符号を用い、訂正符号の長さは元データの長さに応じて決める。伝送の始まりと終わりは特別な音の目印で示し、受信側は目印にはさまれた区間を録音してフーリエ変換で周波数を求める。用途としては一対多の同報、機器組み込み、音のQRコード、機器のペアリングと連絡先の交換、認可の受け渡しなどが挙げられている。2025年2月に話題になったGibberLinkという、会話する人工知能どうしが音の通信に切り替える実演も、このライブラリを使っている。GibberLinkはAnton PidkuikoとBoris Starkovによるもので、リポジトリの説明文に「ggwaveライブラリに基づく」と明記されている。https://github.com/PennyroyalTea/gibberlink

CipherFluteとの関係を述べる。CipherFluteの符号層、すなわち周波数のスロットに記号を割り当て、Reed–Solomon符号で訂正するという設計は、ggwaveの設計とほぼ同一である。異なるのは、ggwaveがスピーカーから任意の音列を出すのに対し、CipherFluteは造形された笛の並びが音列を固定している点である。

脅威の度合いは「中」と判定する。理由を述べる。符号の構成そのものに新規性がないことを明確に示す資料であり、論文が符号設計を新規性として書いていると弱くなる。ただしCipherFluteの主張の中心が物理層と運用にある限り、位置づけを整理するための引用で足りる。

### 3. HAPADEP: Human-Assisted Pure Audio Device Pairing

- 著者: Claudio Soriente, Gene Tsudik, Ersin Uzun
- 発表: Information Security, 11th International Conference, ISC 2008, Taipei, Taiwan, September 15-18, 2008, Proceedings, Lecture Notes in Computer Science 5222, pp. 385-400, 2008年
- 確認先: https://doi.org/10.1007/978-3-540-85886-7_27 （Crossrefのdoi登録レコードで題名、著者、書名、ページを確認した）
- 予稿集の巻号は https://dblp.org/rec/conf/isw/2008.xml で確認した（Lecture Notes in Computer Science 第5222巻、ISBN 978-3-540-85884-3、開催地は台北、会期は2008年9月15日から18日）
- 要旨の全文は著者版の公開原稿で確認した: https://eprint.iacr.org/2007/093

内容の要約を述べる。この論文は、共通の鍵も既存の無線路も持たない二台の機器が、音だけを使って鍵素材を交換し、人間が聞いて確認することで中間者攻撃を排除する方式を提案している。要旨は「HAPADEPは音の通路を使って、データと検証用の情報の双方を機器のあいだで交換する」と述べており、鍵の転送そのものを音で行い、その正しさの検証も人間の聴覚に委ねるという要約は原文どおりである。従来の安全なペアリング手法が赤外線や802.11やBluetoothといった人間には知覚できない共通のディジタル通路の存在を前提にしていた点を、要旨は明示的に批判している。前段の研究として同じグループのLoud and Clearがあり、そちらは音声化した検証文を人間に読ませて認証する。

CipherFluteとの関係を述べる。CipherFluteは暗号資産の復元用情報という鍵素材を音で運ぶ。鍵素材を音の通路で運ぶこと自体はこの研究がすでに行っている。ただしHAPADEPは二台の電子機器のあいだの一時的な通路であり、秘密が物体の形として保管されるわけではない。

脅威の度合いは「中」と判定する。理由を述べる。「鍵を音で運ぶ」という応用が先行しているため、CipherFluteはその応用ではなく「鍵を形として保管し、必要なときだけ音として取り出す」という保管の側面に主張を寄せる必要がある。

### 4. On the Privacy and Security of the Ultrasound Ecosystem

- 著者: Vasilios Mavroudis, Shuang Hao, Yanick Fratantonio, Federico Maggi, Christopher Kruegel, Giovanni Vigna
- 発表: Proceedings on Privacy Enhancing Technologies, vol. 2017, no. 2, pp. 95-112, 2017年
- 確認先: https://doi.org/10.1515/popets-2017-0018 （Crossrefのdoi登録レコードで題名、著者、巻号ページ、年を確認した）
- 本文の全文は出版元の公開版で確認した: https://petsymposium.org/popets/2017/popets-2017-0018.pdf

内容の要約を述べる。この論文は、超音波を使って端末どうしや広告と端末を結びつける商用の生態系を体系的に調べ、その設計上の弱点を示している。本文で確認できた最も重要な指摘は、攻撃者がビーコンを記録して再生するだけで攻撃が成立するという点である。論文は「再生されたビーコンは改変されておらず、認証の仕組みが何も置かれていないため、正当性の検査は必ず成功する」と述べている。実際に買い物のアプリで、来店を示す音を利用者どうしが録音して共有し、計算機のスピーカーから再生して報酬点を得た事例が観測されていたことも報告している。あわせて、利用者の同意なしに視聴履歴を追跡できてしまうというプライバシーの問題を扱い、マイクへの全面的な許可を要求せざるを得ないという最小権限の原則の破れも指摘している。

CipherFluteとの関係を述べる。CipherFluteは「音や物体の層には暗号学的な秘匿の力はまったく無い」と宣言している。その宣言を裏づける先行研究として、この論文は最も的確である。音響の通路には秘匿も認証も期待できないという結論が独立に得られている。

脅威の度合いは「中」と判定する。理由を述べる。脅威モデルの主張が独自のものではなく先行研究に沿ったものであることを示すため、引用しないと「既知の事実を発見として書いている」と見られる危険がある。逆に引用すれば主張の裏づけとして機能する。

### 5. Pushbutton Calling with a Two-Group Voice-Frequency Code

- 著者: L. Schenker
- 発表: Bell System Technical Journal, vol. 39, no. 1, pp. 235-255, 1960年1月
- 確認先: https://archive.org/details/bstj39-1-235 （原誌の走査版で題名、著者、巻号ページ、年を確認した。本文の翻刻は https://archive.org/download/bstj39-1-235/bstj39-1-235_djvu.txt で読める）
- 関連する標準: ITU-T勧告 Q.23 "Technical features of push-button telephone sets"（現行版は1988年11月版）https://www.itu.int/rec/T-REC-Q.23/en

内容の要約を述べる。本文に当たって確認した。この論文は、電話機の押しボタンから信号を送るために、低群と高群それぞれから1つずつ周波数を選んで同時に鳴らす符号を提案しており、著者はこれを「四かける四」の符号と呼んでいる。8つの周波数を2群に分け、群Aは697、770、852、941サイクル毎秒、群Bは1094、1209、1336、1477サイクル毎秒であって、群のなかの隣り合う周波数の比は21対19に固定されている。群と群のあいだはこの比の1.5倍の間隔を置く。全体は700サイクル毎秒から1700サイクル毎秒の範囲に収まり、有効な信号は16組である。音声による誤動作、すなわち著者が「トークオフ」と呼ぶ現象を避けるために、16組の比が低次の整数比にならないよう周波数が選ばれている。この方式は後に世界中の電話網に採用され、ITU-T勧告Q.23として標準化された。なお本文の周波数値は現行の押しボタン信号の高群の値（1209、1336、1477、1633）とは一部異なり、1960年時点の提案であることに注意が必要である。

CipherFluteとの関係を述べる。CipherFluteは1480ヘルツから2960ヘルツまでを半音刻みで13のスロットに区切り、笛1本に1つの記号を割り当てる。周波数の離散集合を語彙とし、周波数の同定だけで復号するという構成は、この符号と本質的に同じである。しかも周波数を一定の比で並べる、つまり対数の目盛の上で等間隔に置くという設計まで共通している。相違は、CipherFluteが1回に1つの周波数だけを出す点と、比が21対19ではなく半音すなわち100セントである点である。

脅威の度合いは「中」と判定する。理由を述べる。周波数スロットによる符号化の原型として必ず引用すべき文献であり、これを引かずに「周波数を語彙にする」ことを新しく述べると、電話技術の常識を知らないと受け取られる。現在の論文はQ.23を挙げているが、その技術的な出典であるこの論文まで遡ると位置づけが明確になる。
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
