qurihara/ai-fue/assets/PXL_20260703_055728416.jpg

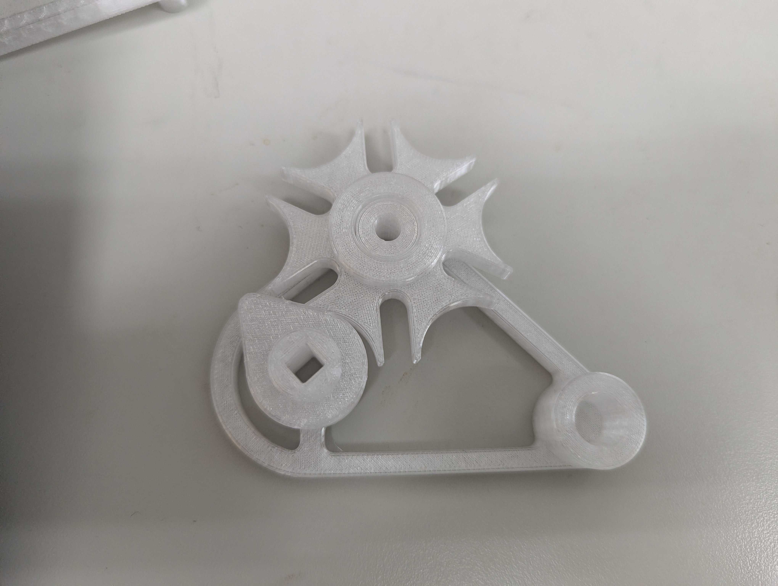
assets/PXL_20260703_055728416.jpg
