qurihara/ai-fue/harmonica_deck/branding/_emboss_section_v1.png

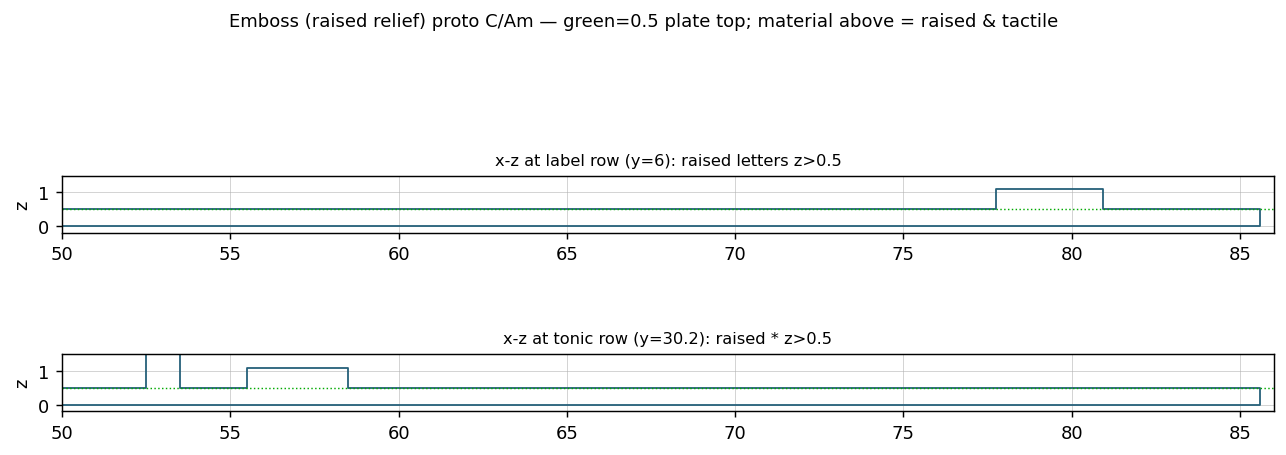
harmonica_deck/branding/_emboss_section_v1.png
