qurihara/ai-fue/harmonica_deck/branding/chordika_card_branded_v1.png

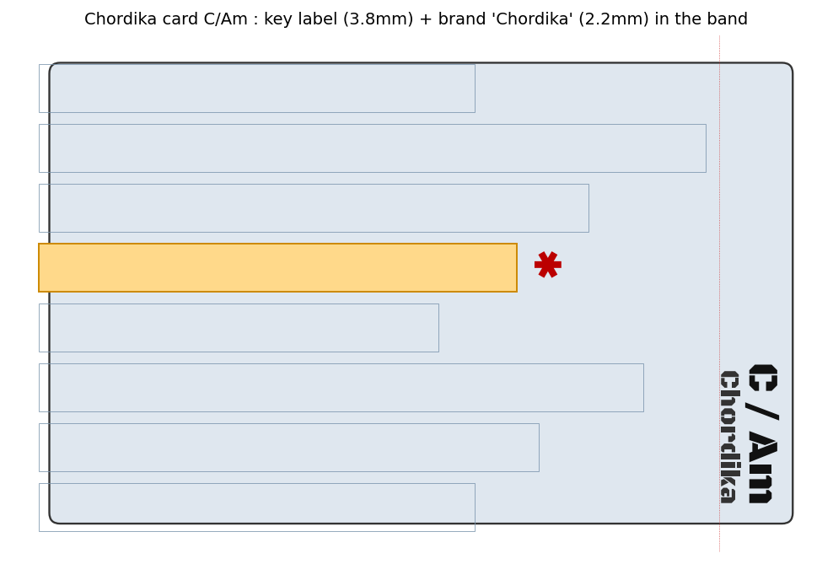
harmonica_deck/branding/chordika_card_branded_v1.png
