qurihara/ai-fue/harmonica_deck/branding/chordika_wordmark_v1.png

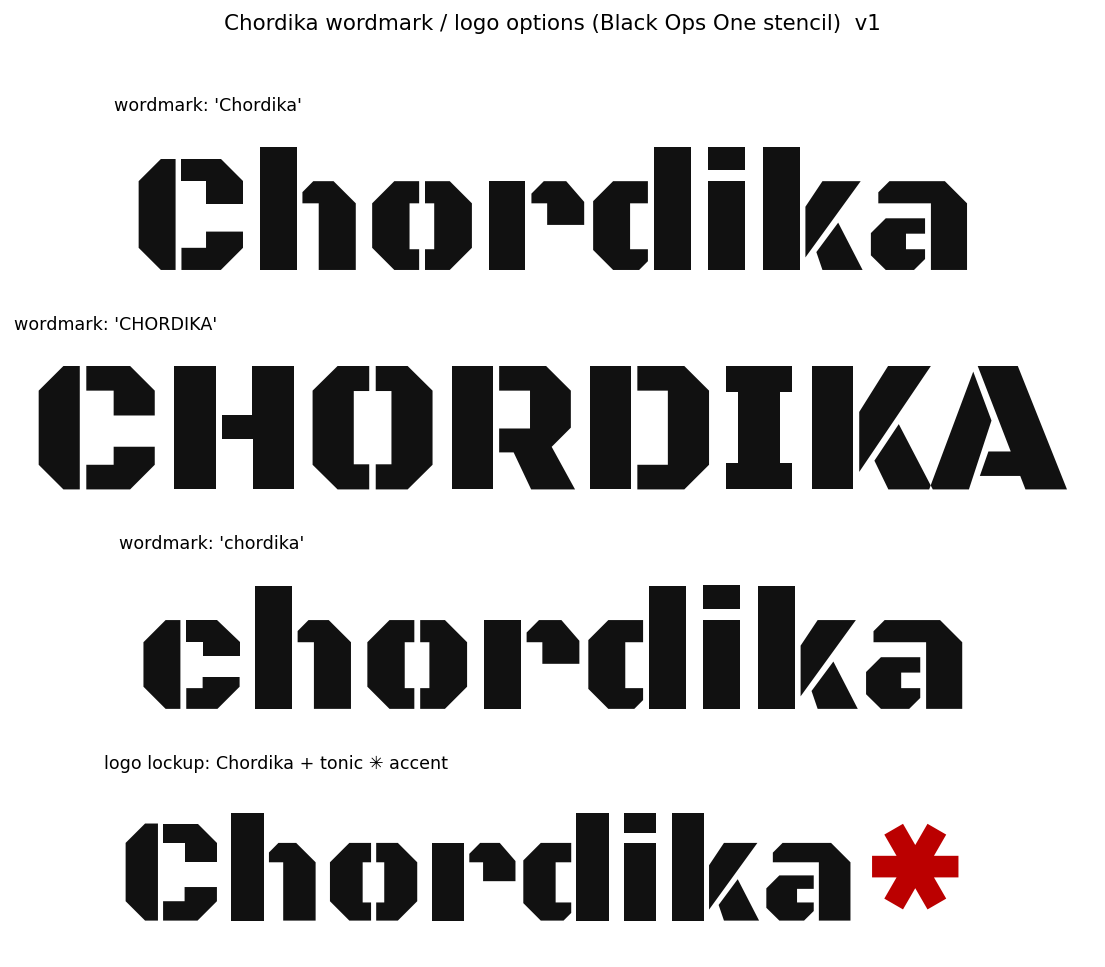
harmonica_deck/branding/chordika_wordmark_v1.png
