qurihara/ai-fue/harmonica_deck/deck_preview.png

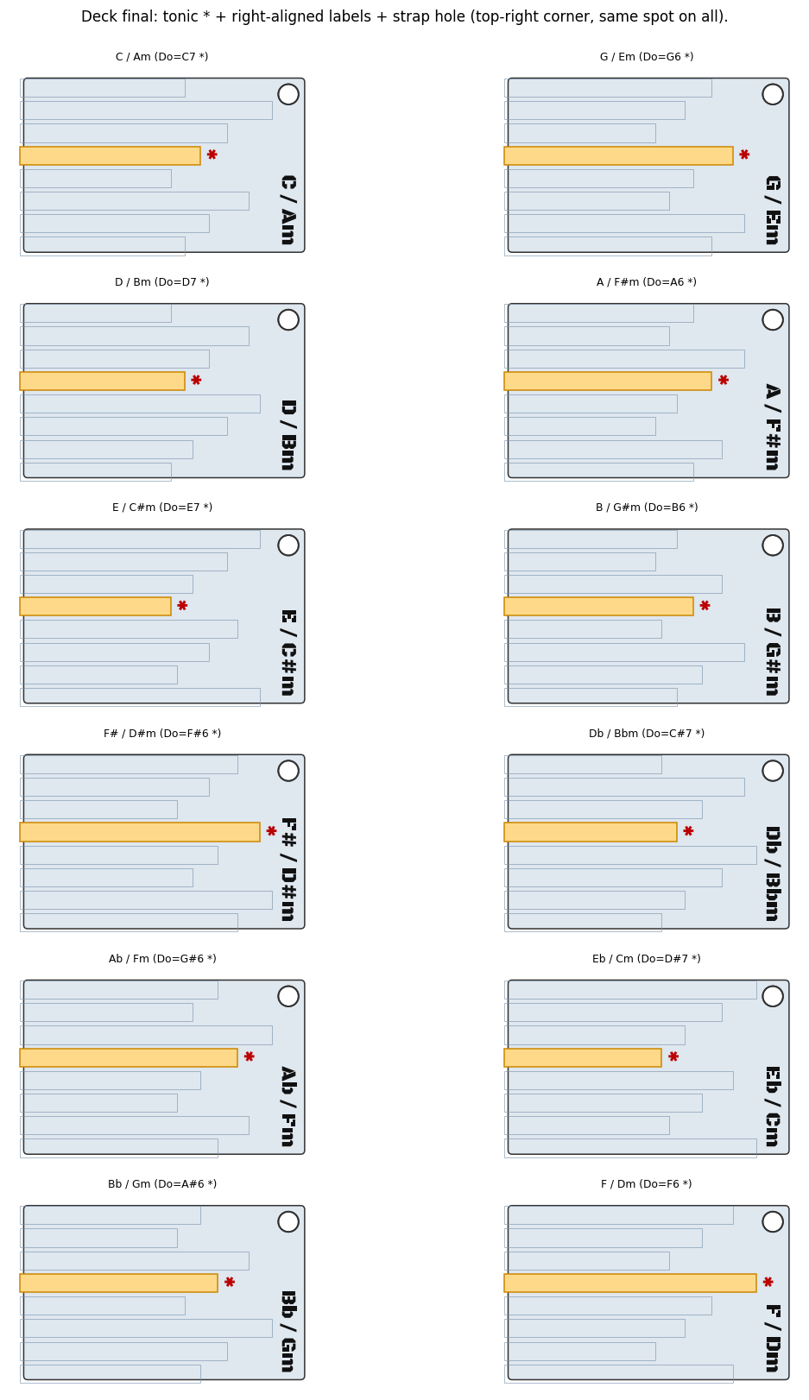
harmonica_deck/deck_preview.png
