qurihara/ai-fue/harmonica_deck/deck_star_closeup.png

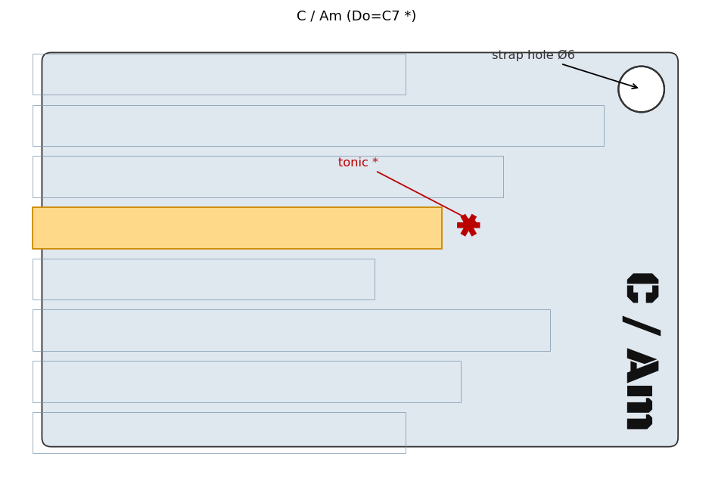
harmonica_deck/deck_star_closeup.png
