qurihara/ai-fue/harmonica_deck/strap_boss_section.png

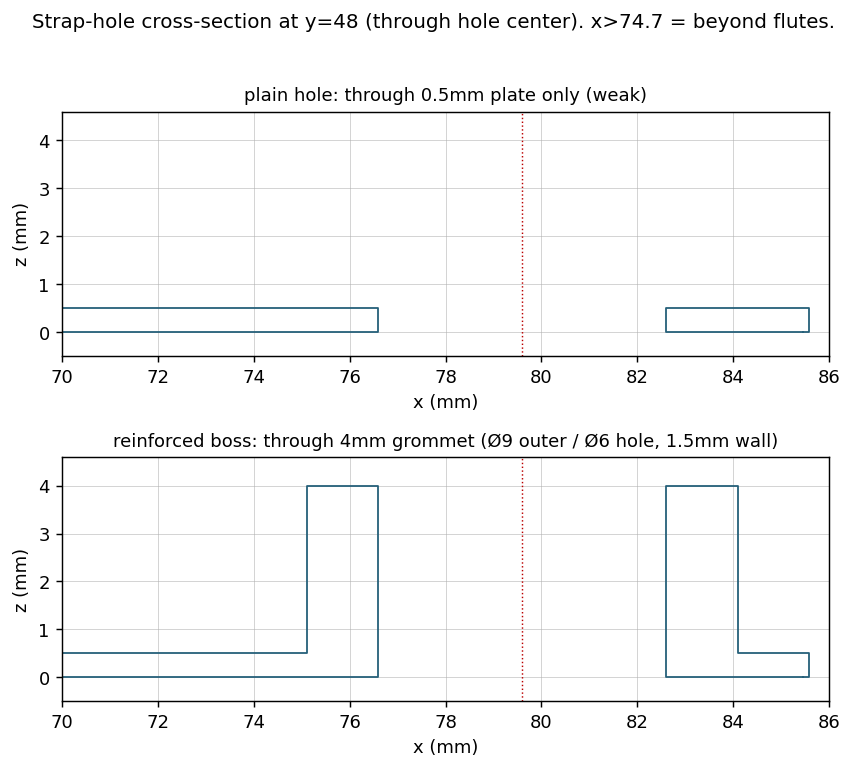
harmonica_deck/strap_boss_section.png
