qurihara/ai-fue/out/frames/frame_ichimatsu.png

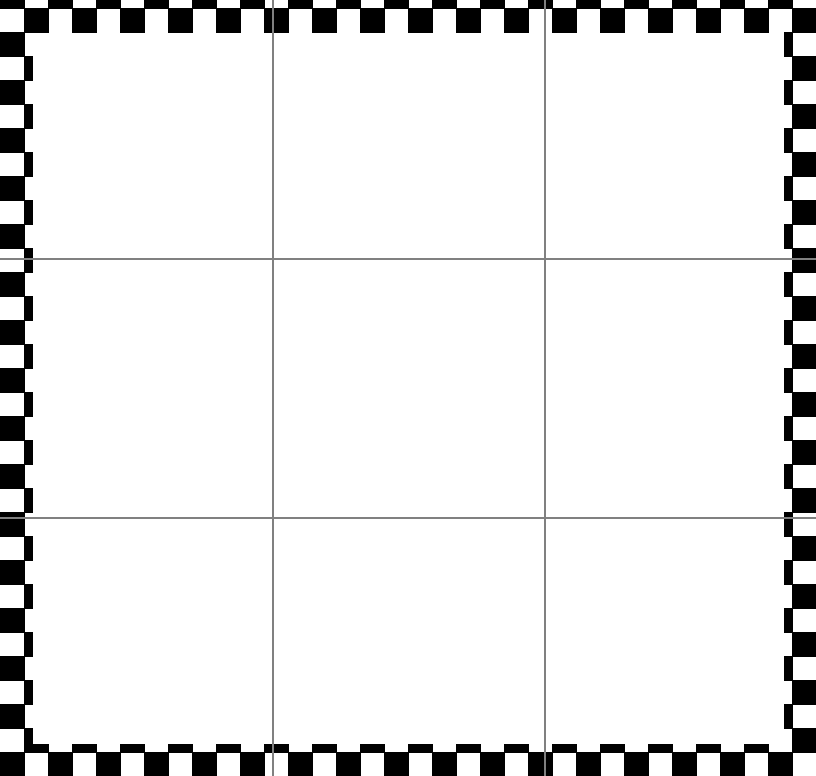
out/frames/frame_ichimatsu.png
