qurihara/ai-fue/out/hokusai_tiles/tile_01_r0c0_preview.png

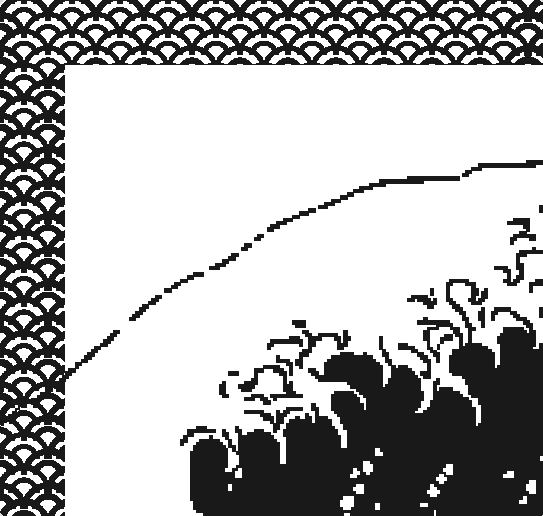
out/hokusai_tiles/tile_01_r0c0_preview.png
