qurihara/ai-fue/out/hokusai_tiles/tile_02_r0c1_preview.png

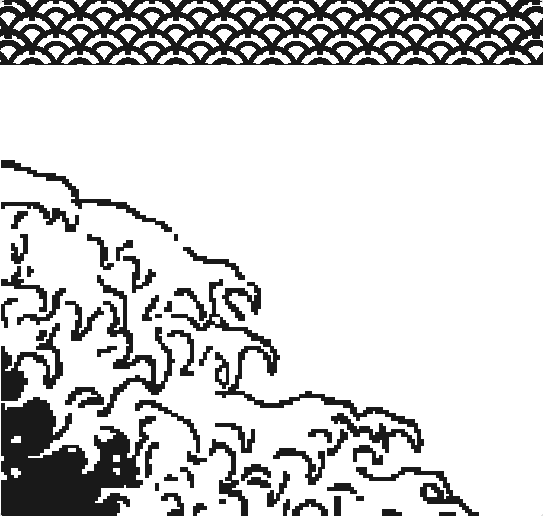
out/hokusai_tiles/tile_02_r0c1_preview.png
