qurihara/ai-fue/out/hokusai_tiles/tile_03_r0c2_preview.png

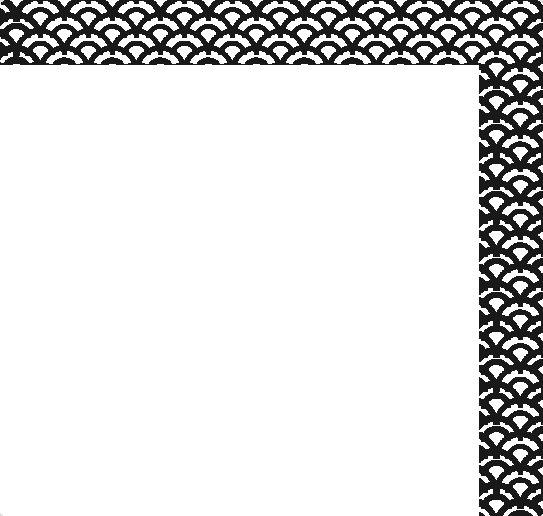
out/hokusai_tiles/tile_03_r0c2_preview.png
