qurihara/ai-fue/out/hokusai_tiles/tile_04_r1c0_preview.png

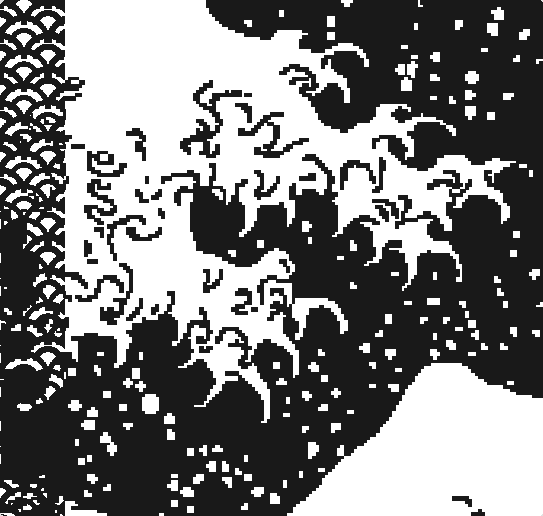
out/hokusai_tiles/tile_04_r1c0_preview.png
