qurihara/ai-fue/out/hokusai_tiles/tile_05_r1c1_preview.png

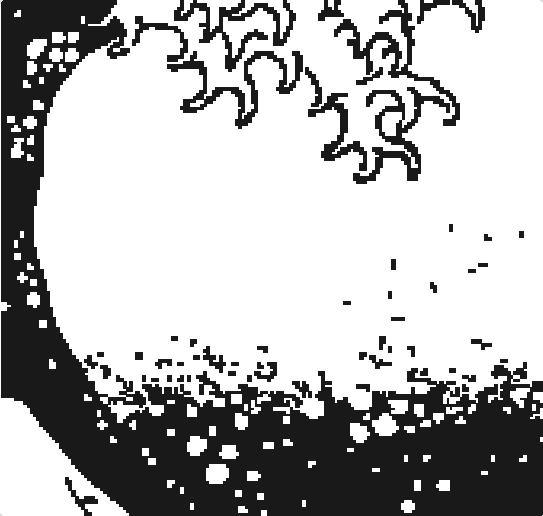
out/hokusai_tiles/tile_05_r1c1_preview.png
