qurihara/ai-fue/out/hokusai_tiles/tile_06_r1c2_preview.png

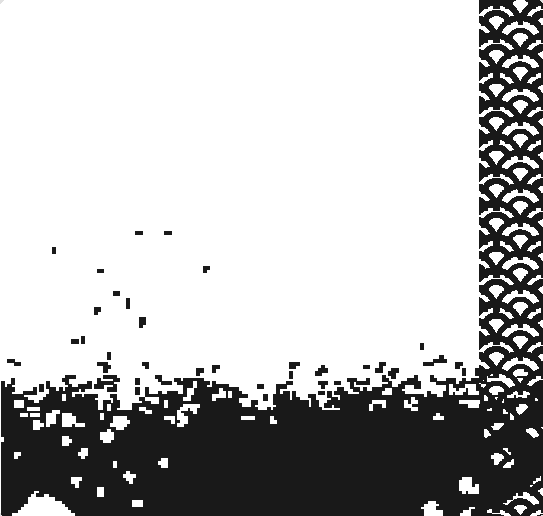
out/hokusai_tiles/tile_06_r1c2_preview.png
