qurihara/ai-fue/out/hokusai_tiles/tile_07_r2c0_preview.png

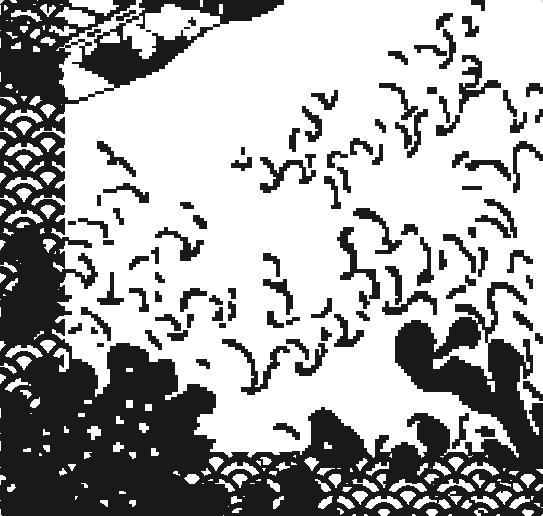
out/hokusai_tiles/tile_07_r2c0_preview.png
