qurihara/ai-fue/out/hokusai_tiles/tile_08_r2c1_preview.png

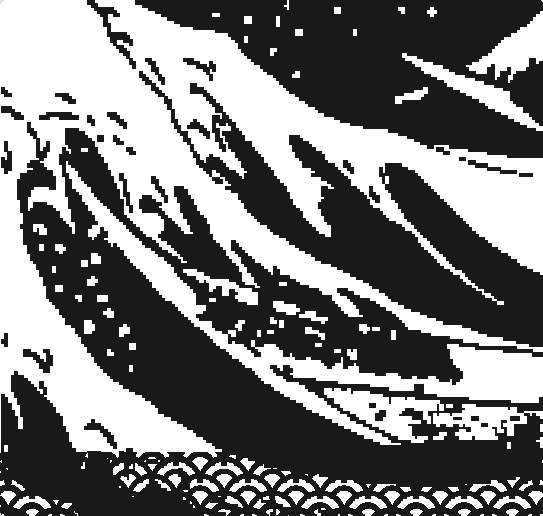
out/hokusai_tiles/tile_08_r2c1_preview.png
