qurihara/ai-fue/out/hokusai_tiles/tile_09_r2c2_preview.png

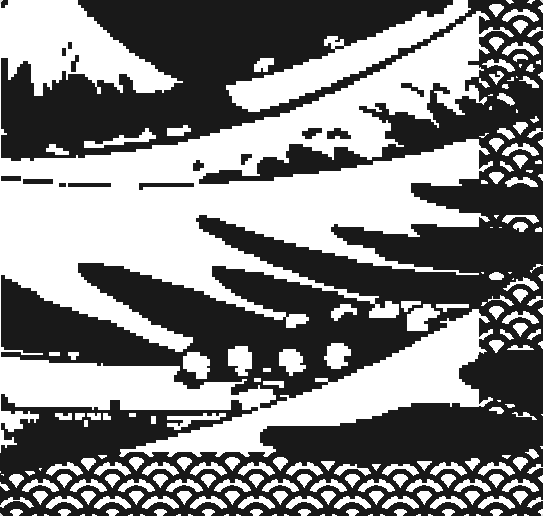
out/hokusai_tiles/tile_09_r2c2_preview.png
