qurihara/ai-fue/out/karuta/araz_kugiri_lower.png

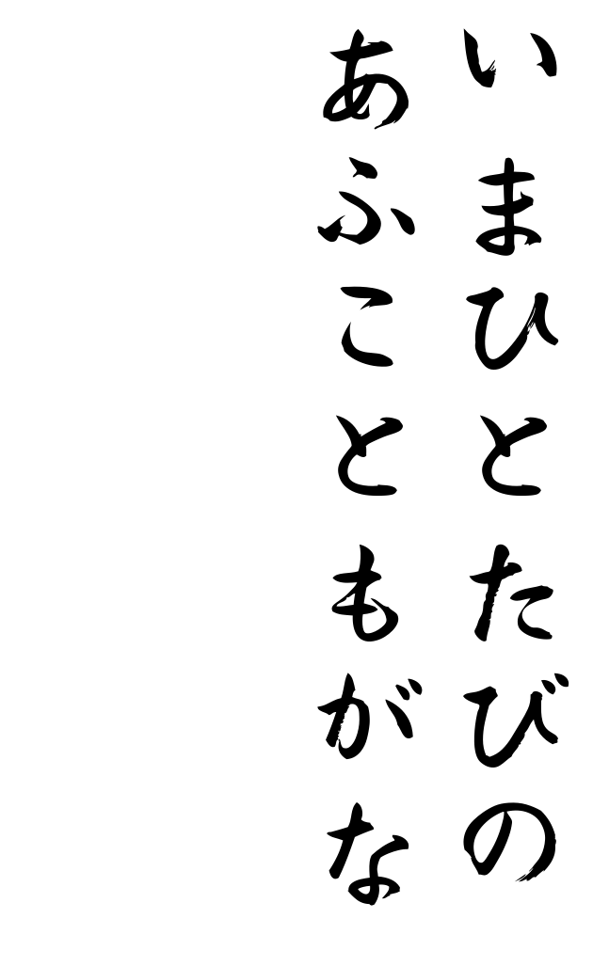
out/karuta/araz_kugiri_lower.png
