qurihara/ai-fue/out/karuta/araz_kugiri_upper.png

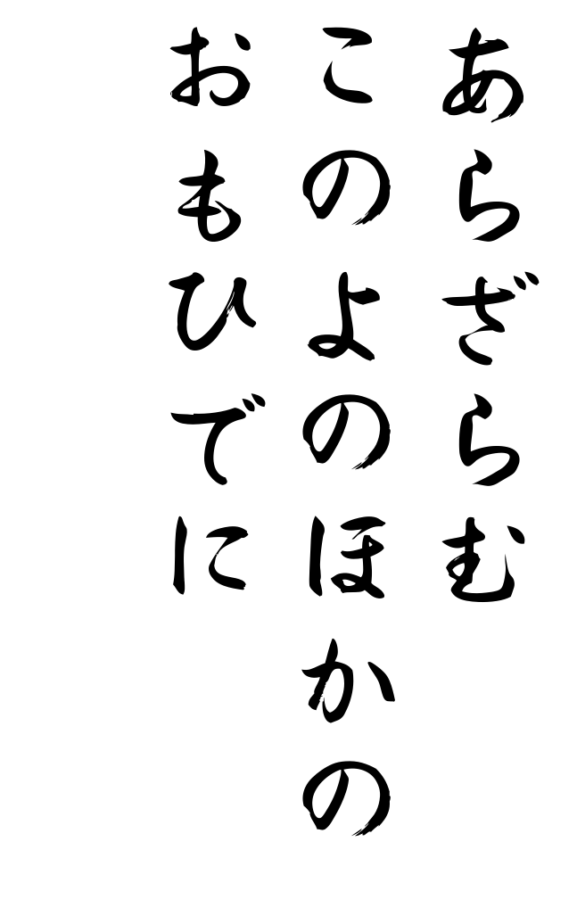
out/karuta/araz_kugiri_upper.png
