qurihara/ai-fue/out/karuta/arazaramu_edge_lower_preview.png

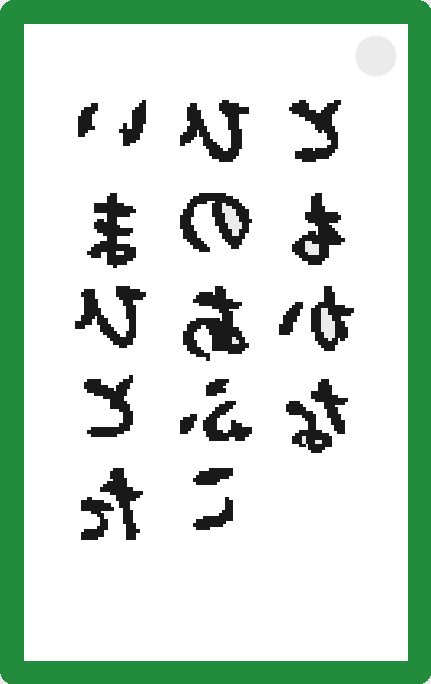
out/karuta/arazaramu_edge_lower_preview.png
