qurihara/ai-fue/out/karuta/arazaramu_lower.png

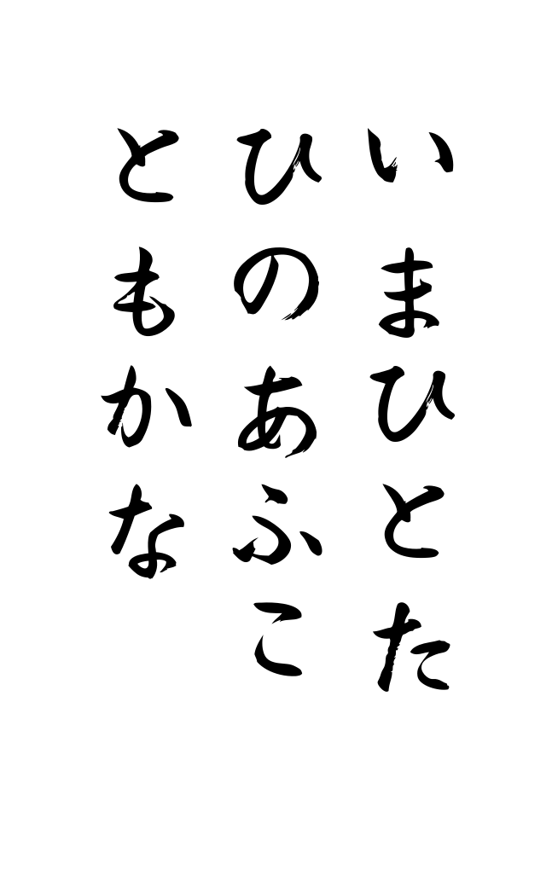
out/karuta/arazaramu_lower.png
