qurihara/ai-fue/out/karuta/arazaramu_upper.png

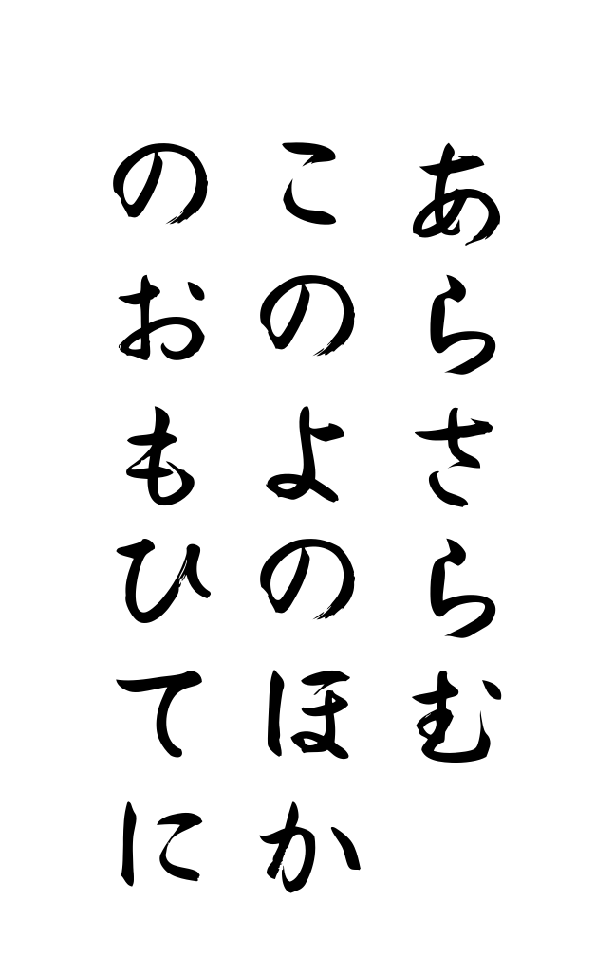
out/karuta/arazaramu_upper.png
