qurihara/ai-fue/out/karuta/fuda_lower.png

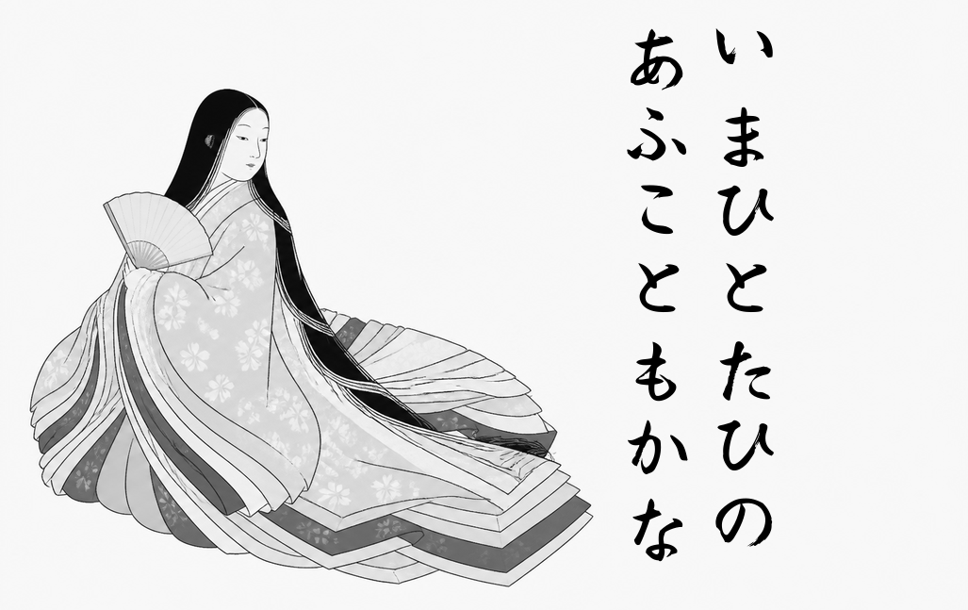
out/karuta/fuda_lower.png
