qurihara/ai-fue/out/karuta/fuda_upper.png

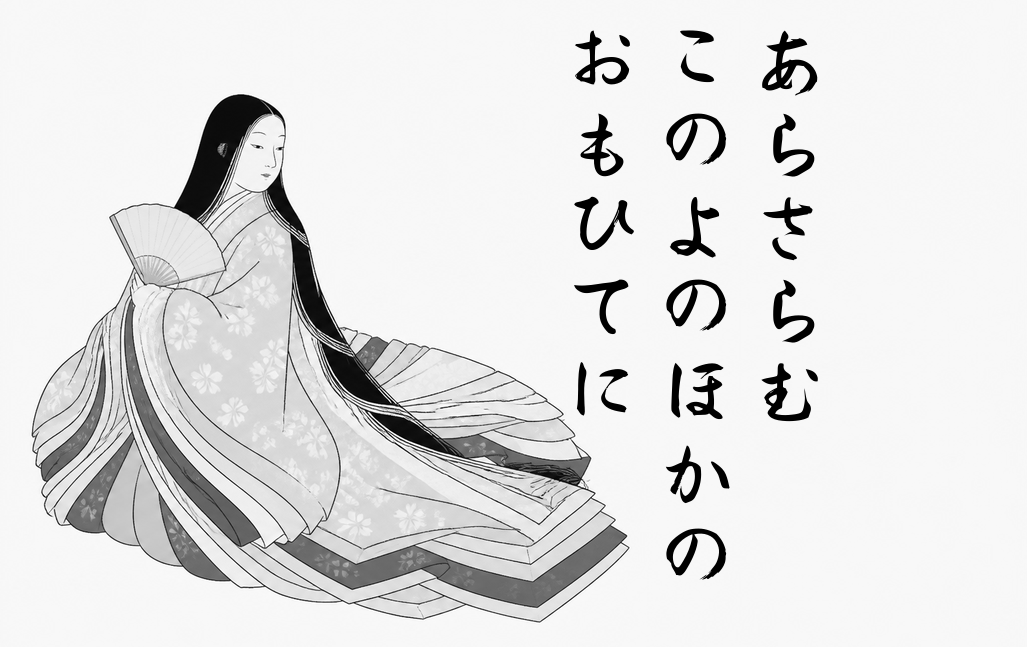
out/karuta/fuda_upper.png
