qurihara/ai-fue/out/karuta/fudaP_lower.png

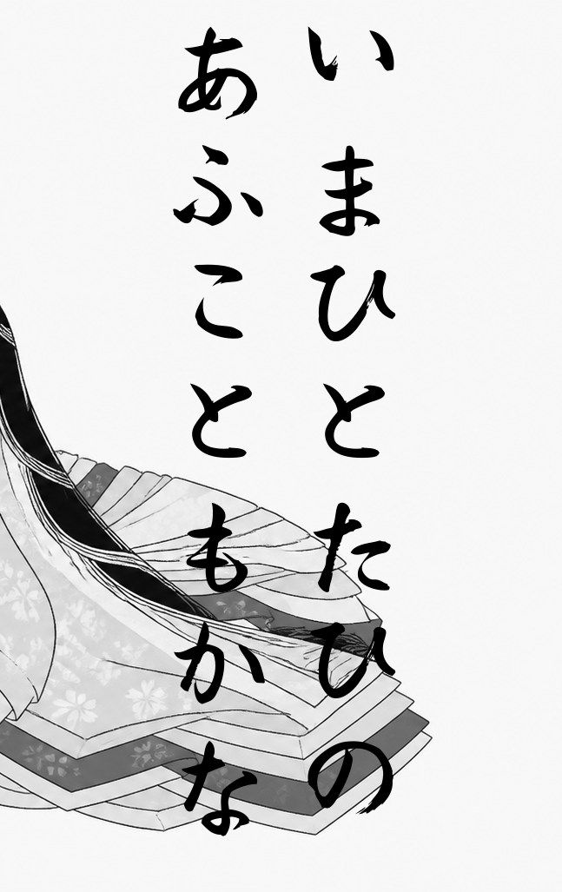
out/karuta/fudaP_lower.png
