qurihara/ai-fue/out/karuta/fudaP_upper.png

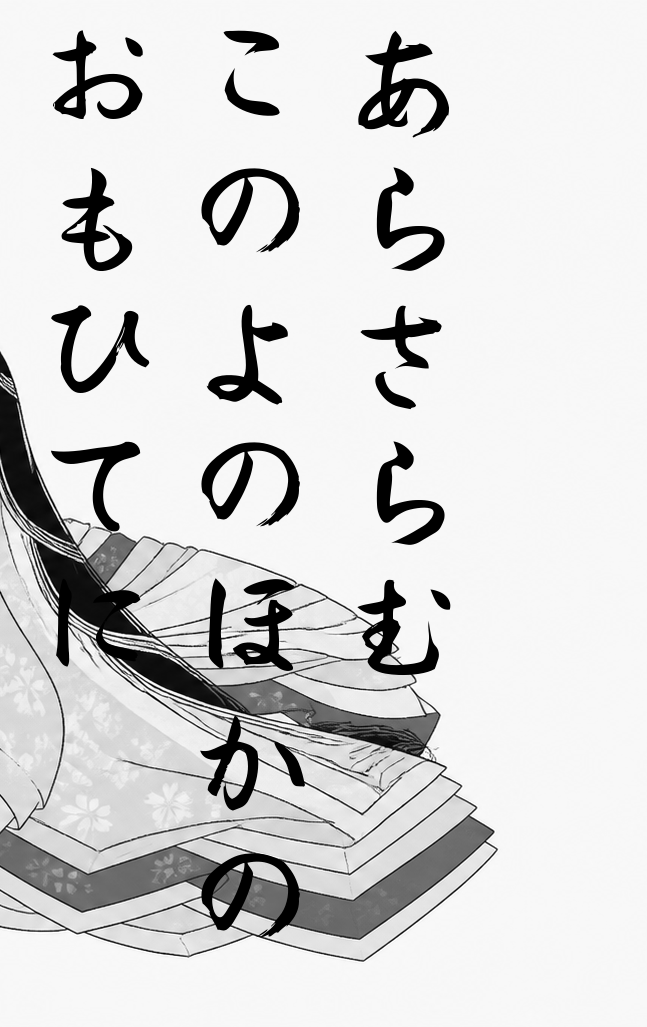
out/karuta/fudaP_upper.png
