qurihara/ai-fue/out/karuta/izumi2_a.png

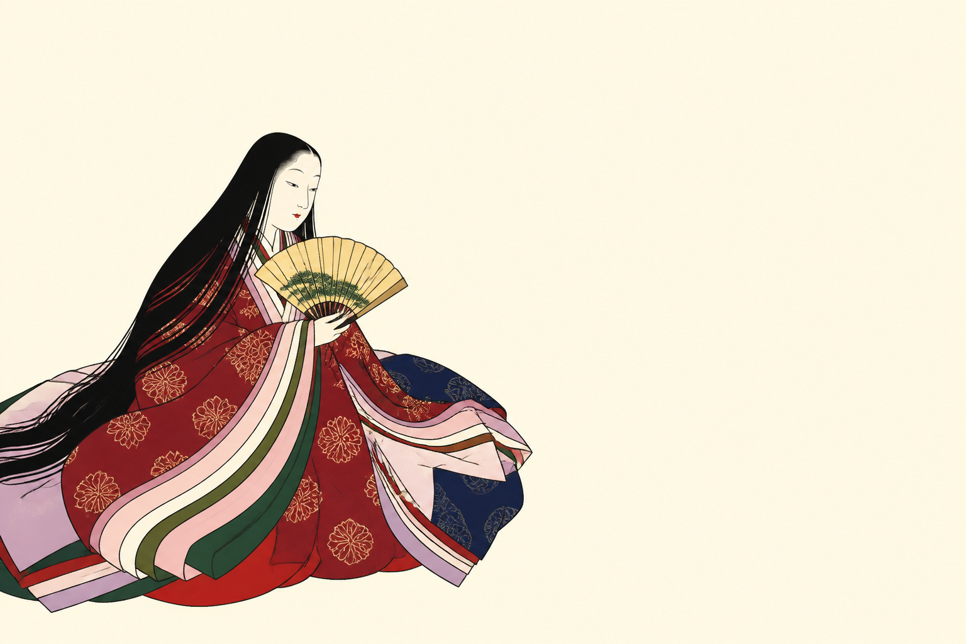
out/karuta/izumi2_a.png
