qurihara/ai-fue/out/karuta/izumi2_b.png

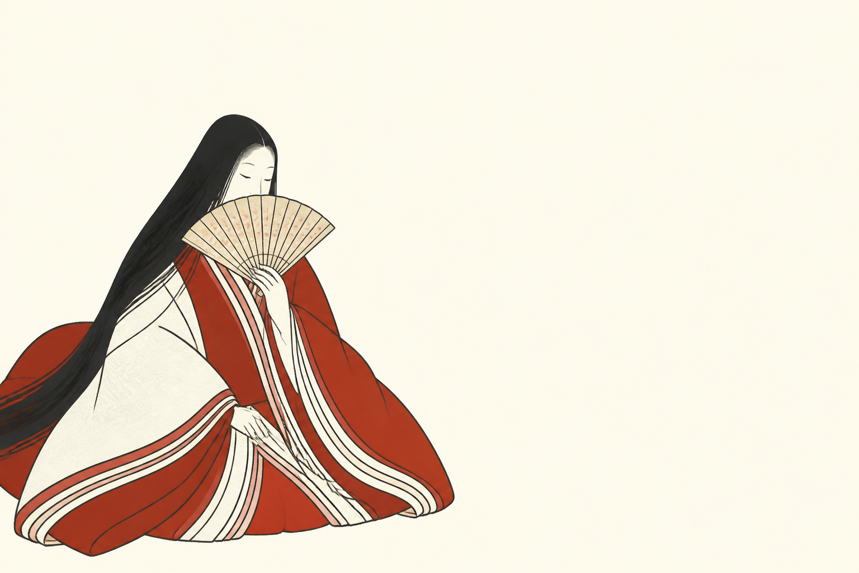
out/karuta/izumi2_b.png
