qurihara/ai-fue/out/karuta/izumi2_c.png

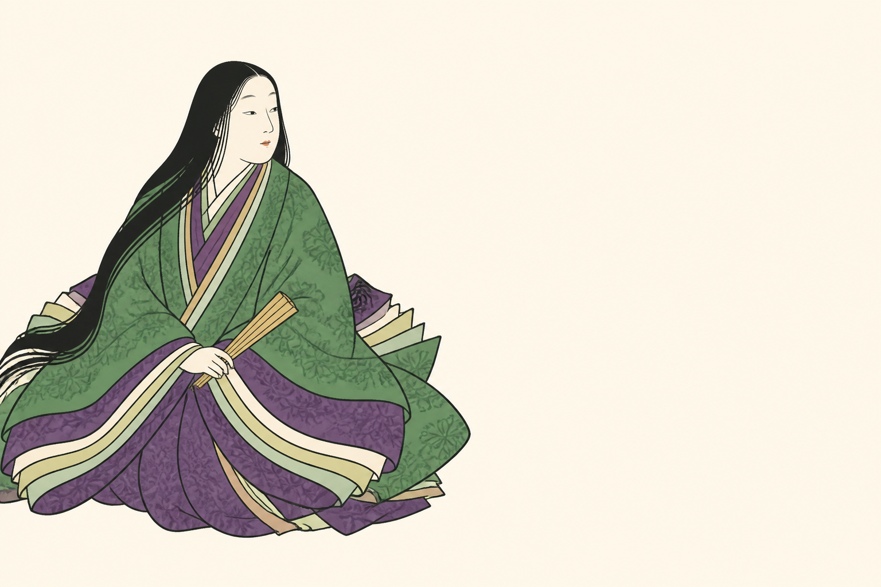
out/karuta/izumi2_c.png
