qurihara/ai-fue/out/karuta/izumi2_d.png

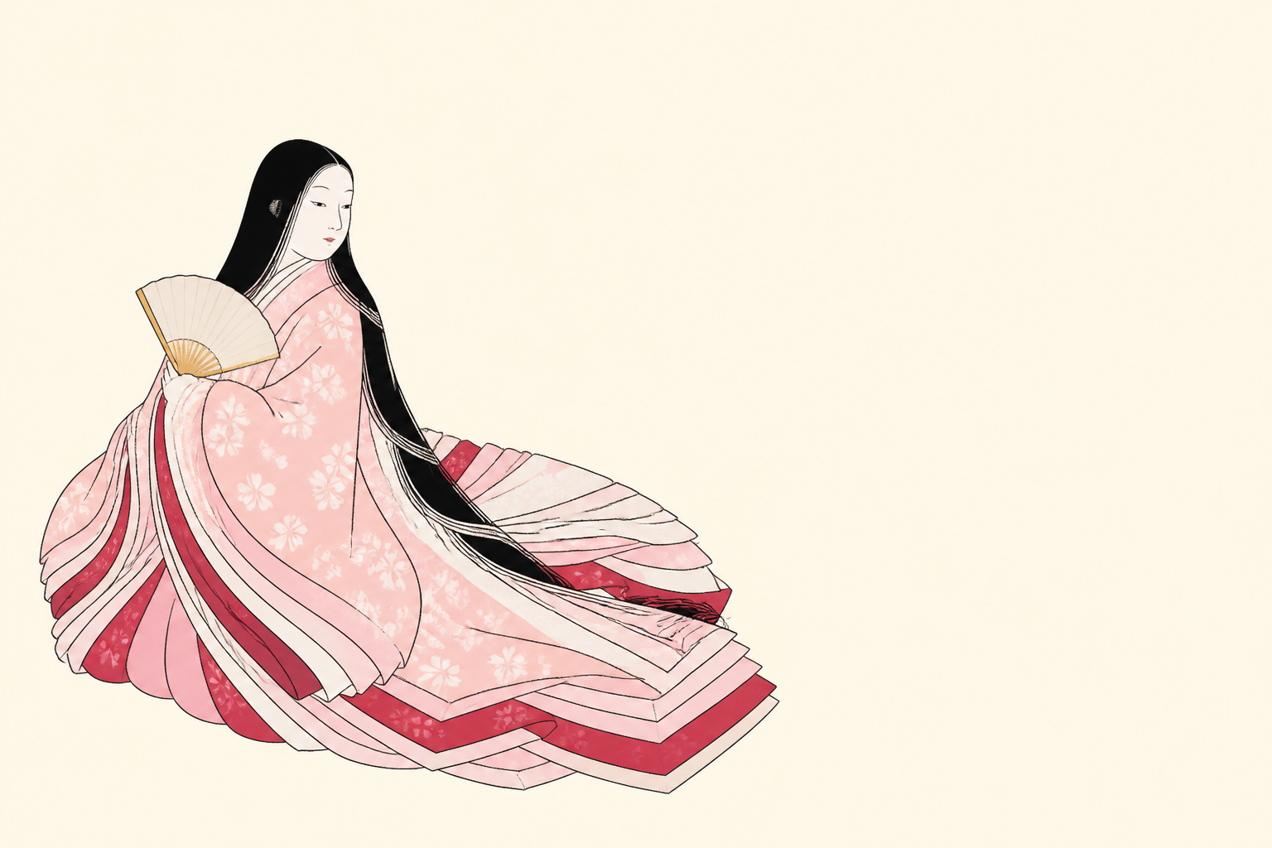
out/karuta/izumi2_d.png
