qurihara/ai-fue/out/karuta/izumi_2of2_lower_preview.png

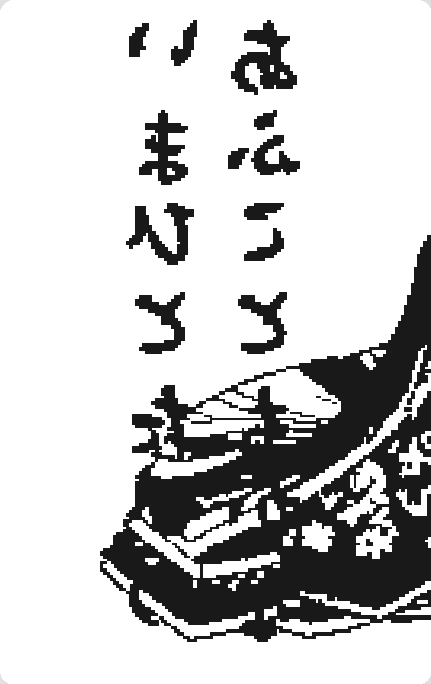
out/karuta/izumi_2of2_lower_preview.png
