qurihara/ai-fue/out/karuta/izumi_2of2_upper_preview.png

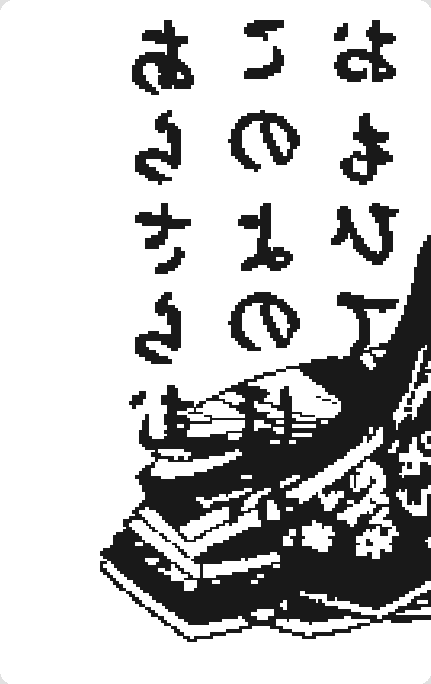
out/karuta/izumi_2of2_upper_preview.png
