qurihara/ai-fue/out/karuta/sutoku_upper_preview.png

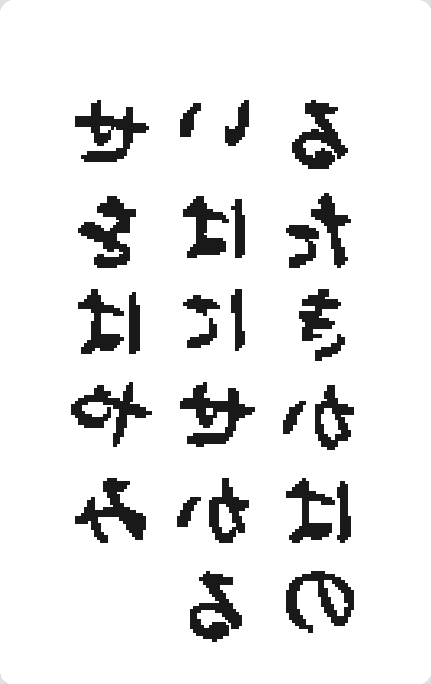
out/karuta/sutoku_upper_preview.png
