qurihara/ai-fue/out/karuta/プレビュー_印刷解像度.png

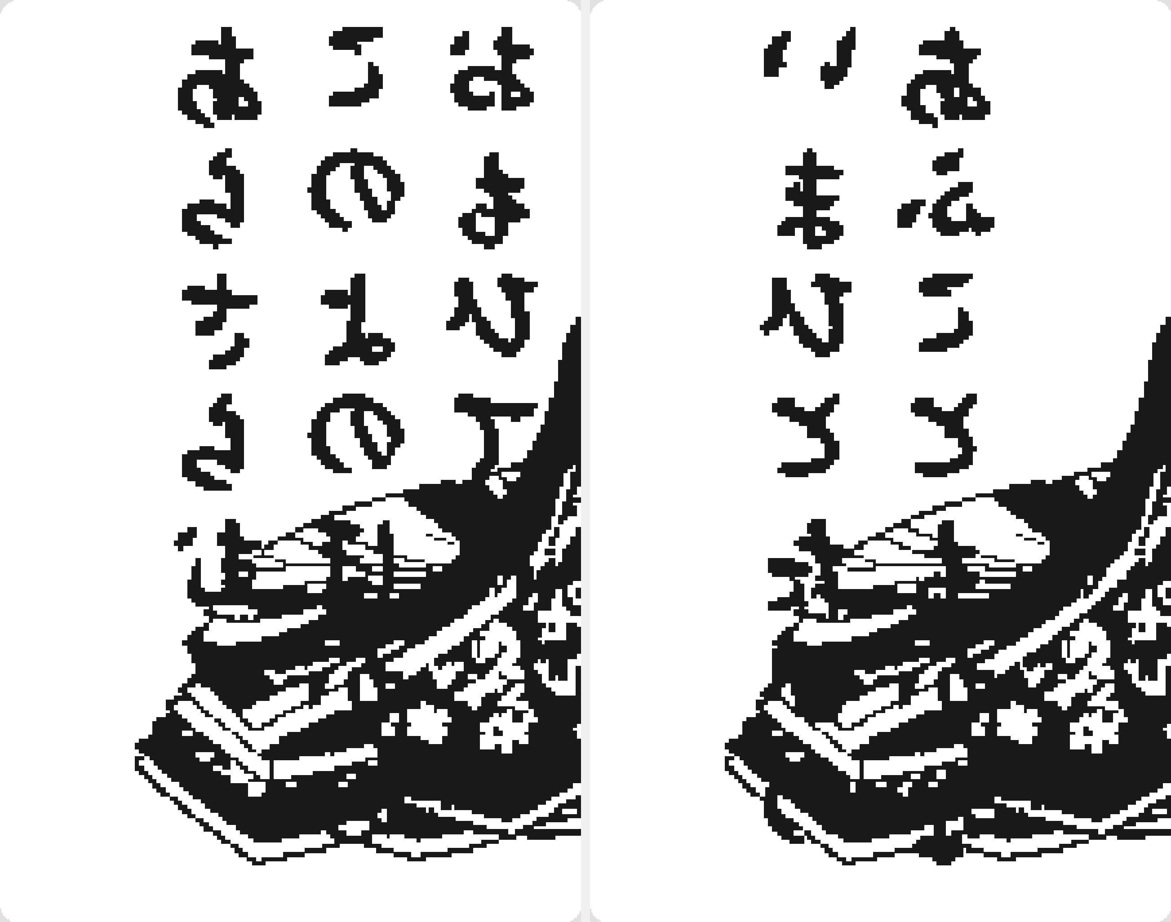
out/karuta/プレビュー_印刷解像度.png
