qurihara/ai-fue/out/karuta/プレビュー_崇徳院札.png

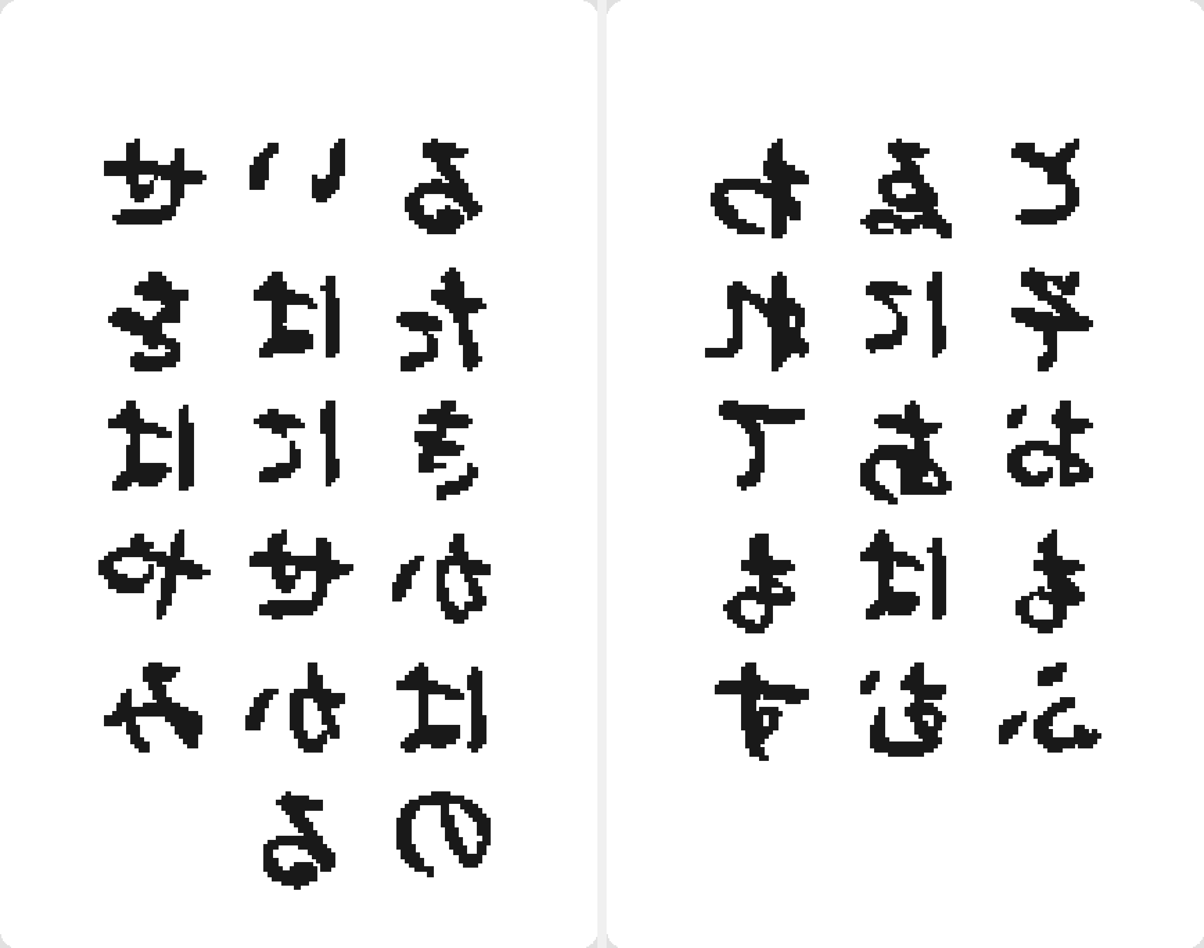
out/karuta/プレビュー_崇徳院札.png
