qurihara/ai-fue/out/karuta/検査_空洞.png

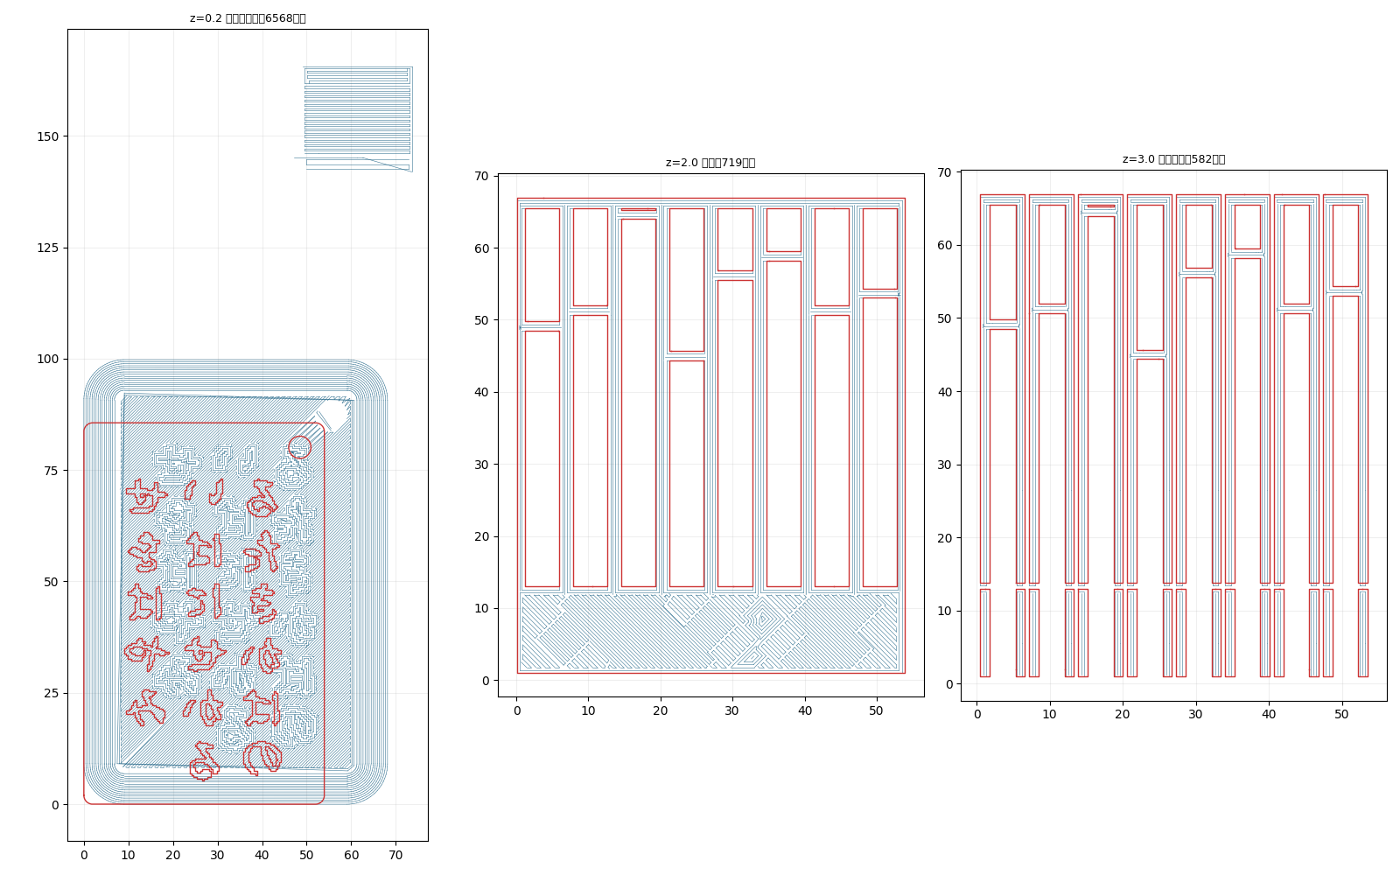
out/karuta/検査_空洞.png
