qurihara/ai-fue/out/karuta/比較_イラスト4枚.png

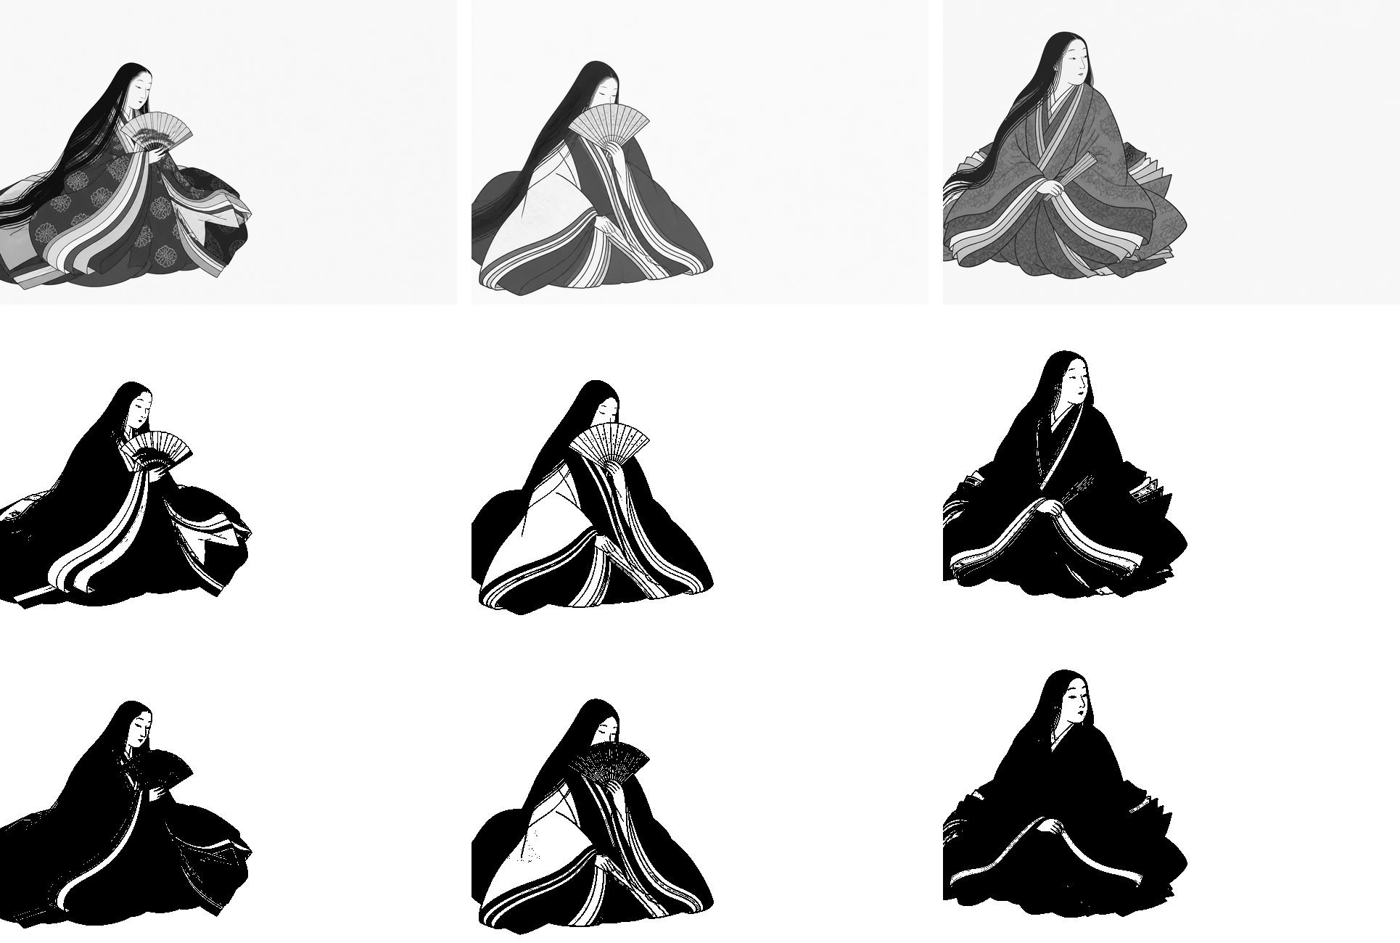
out/karuta/比較_イラスト4枚.png
