qurihara/ai-fue/out/karuta/比較_五七五七七.png

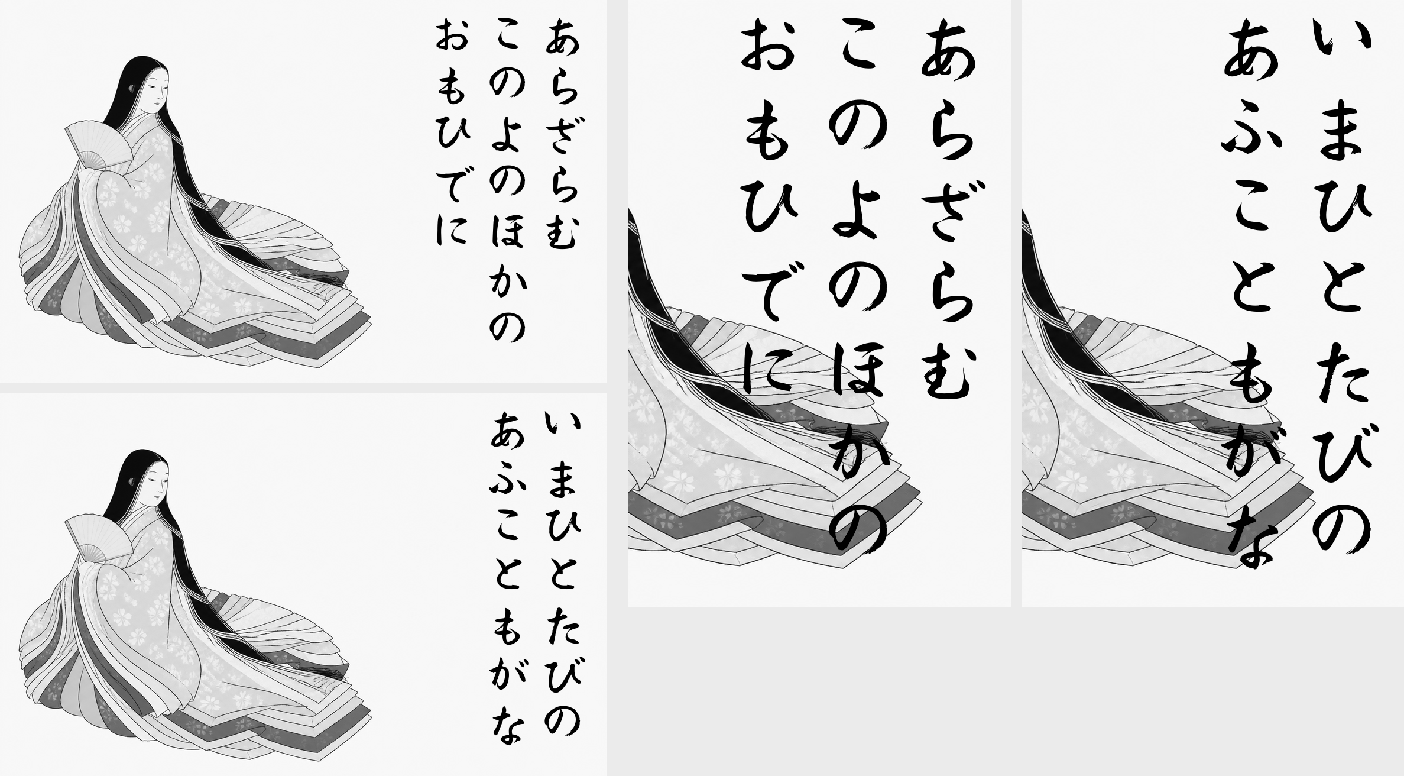
out/karuta/比較_五七五七七.png
