qurihara/ai-fue/out/karuta/比較_採用d.png

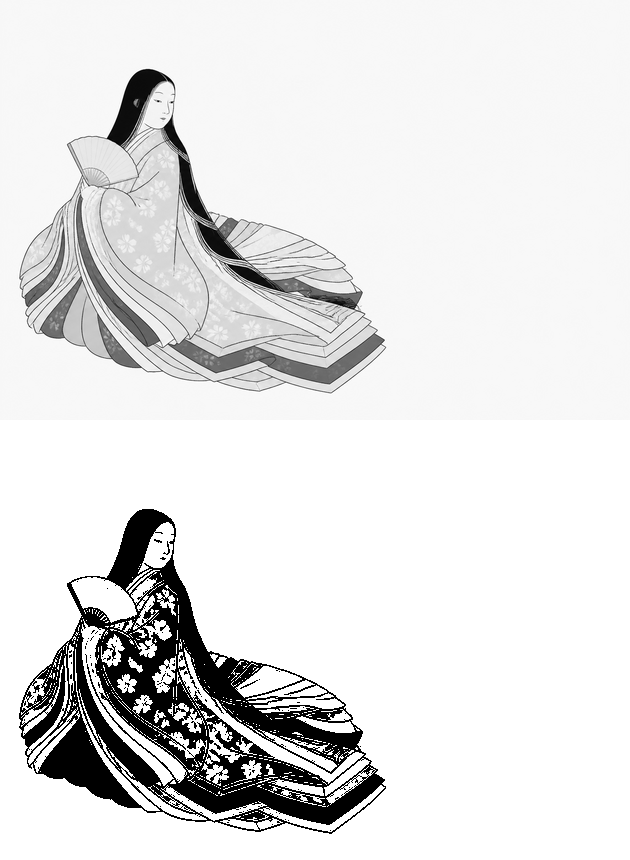
out/karuta/比較_採用d.png
