qurihara/ai-fue/out/karuta/比較_版下4枚.png

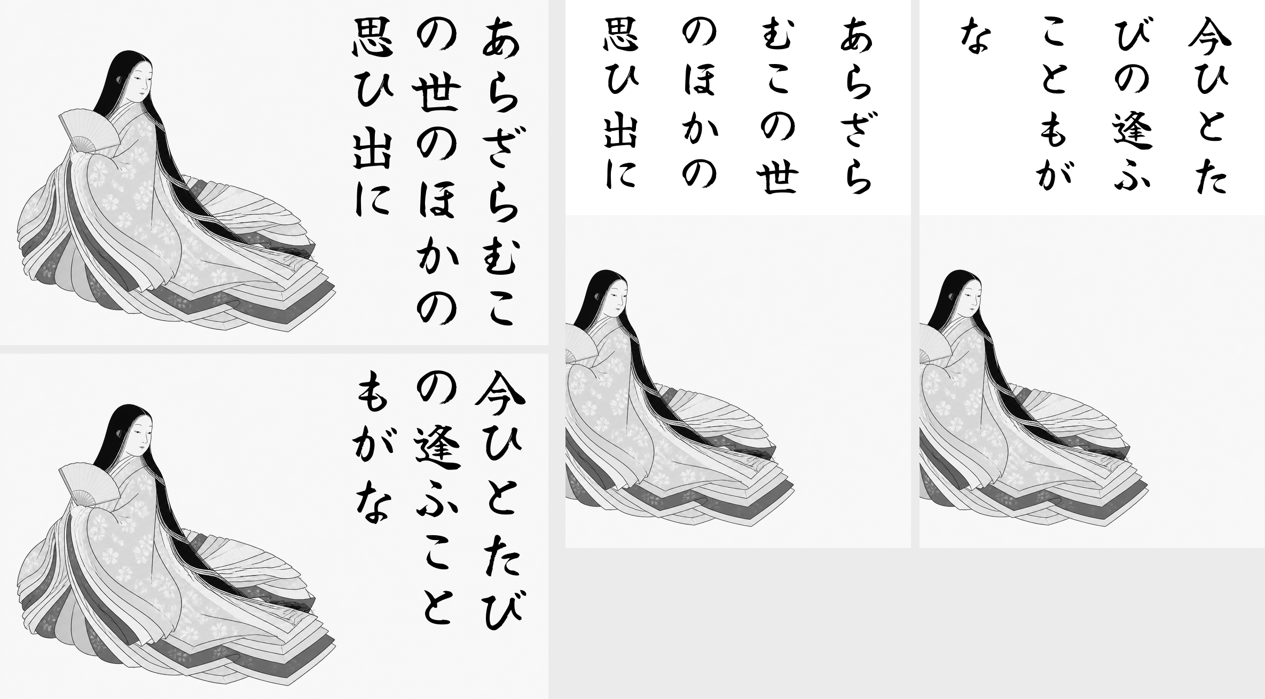
out/karuta/比較_版下4枚.png
