qurihara/ai-fue/out/karuta/比較_縦長版.png

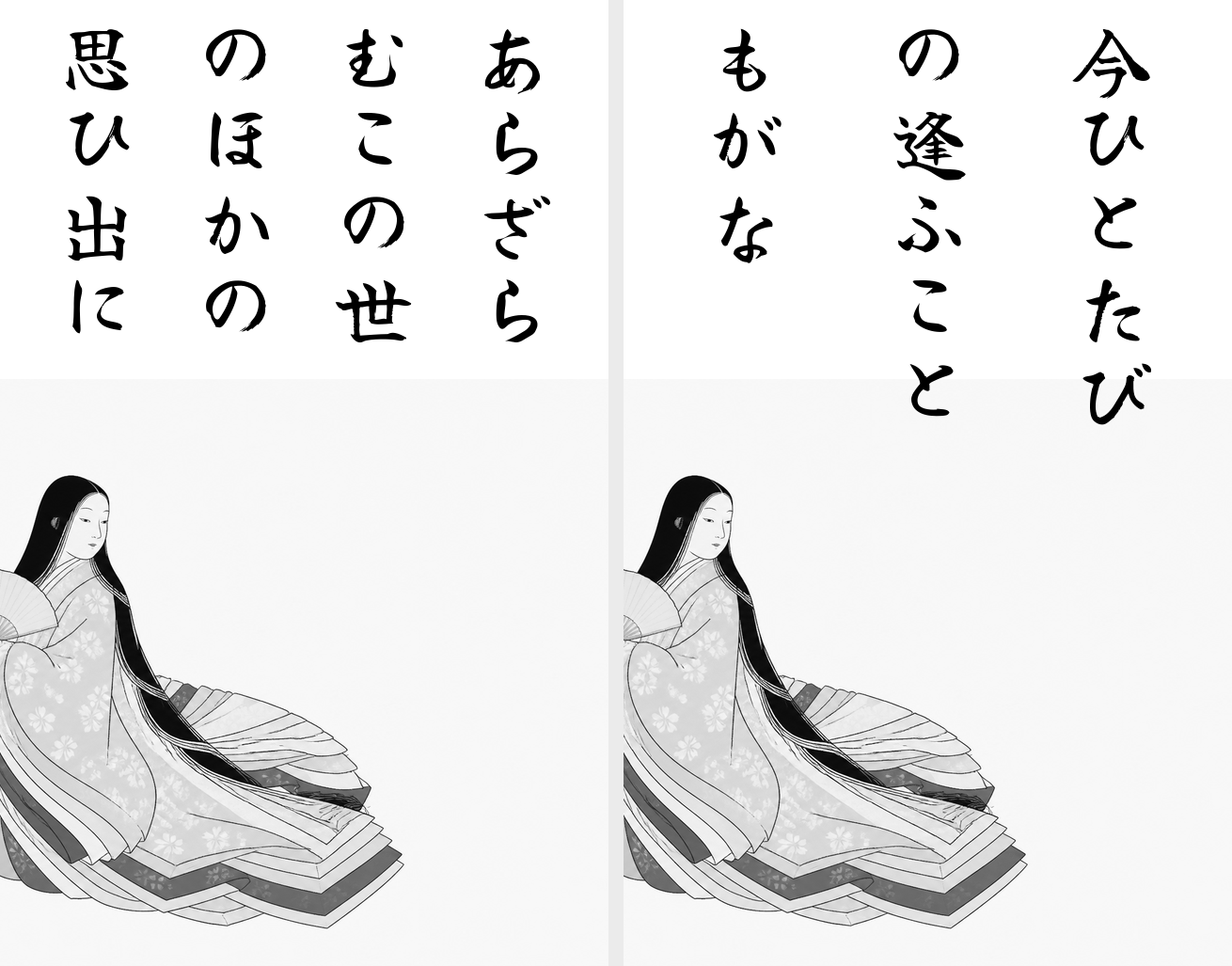
out/karuta/比較_縦長版.png
