qurihara/ai-fue/out/protopedia/img2_12keys.png

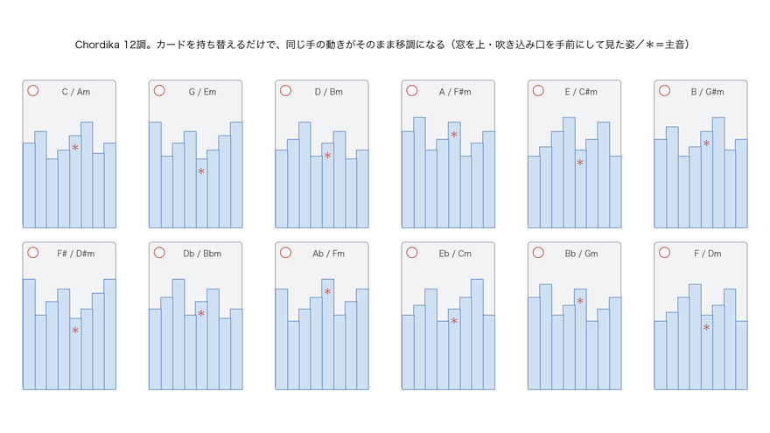
out/protopedia/img2_12keys.png
