qurihara/ai-fue/out/protopedia/img3_chordmap.png

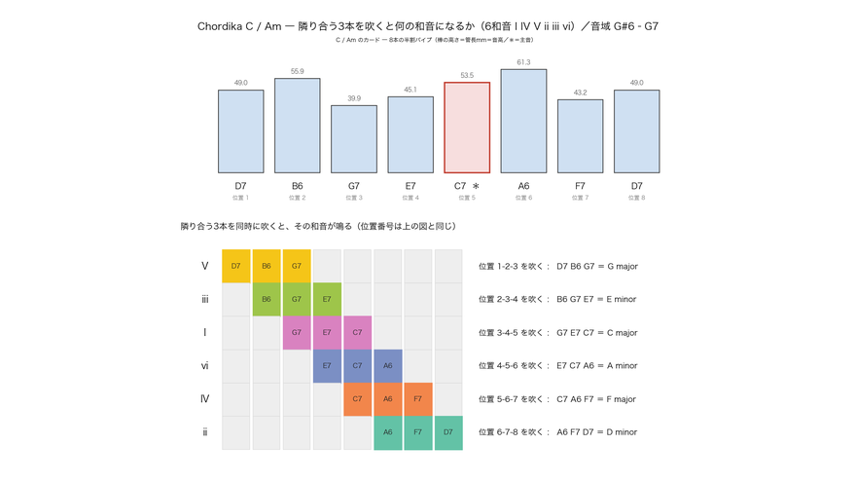
out/protopedia/img3_chordmap.png
