qurihara/ai-fue/out/tiles_frontframe/part_r0c0.png

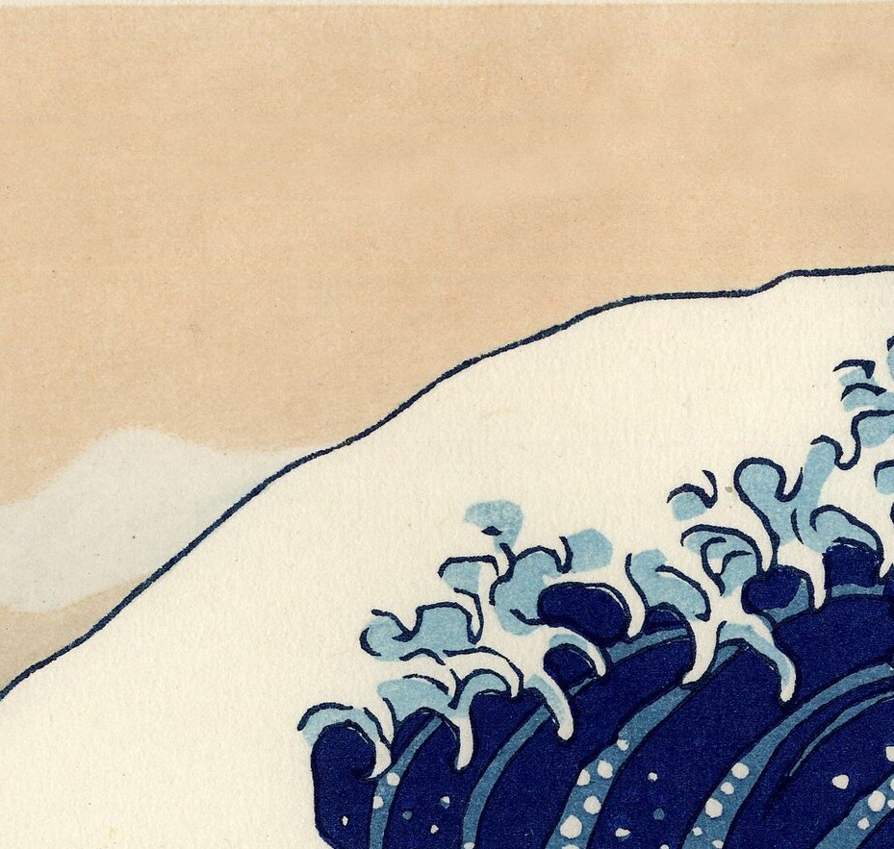
out/tiles_frontframe/part_r0c0.png
