qurihara/ai-fue/out/tiles_frontframe/part_r0c1.png

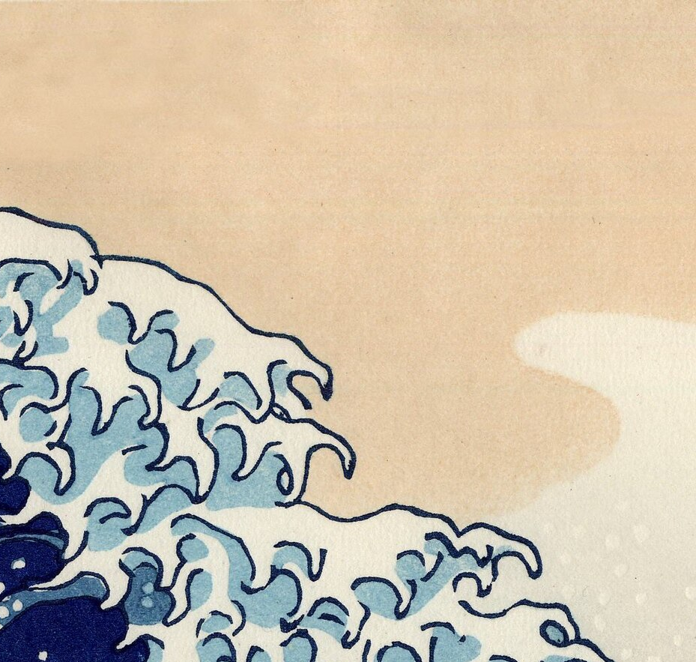
out/tiles_frontframe/part_r0c1.png
