qurihara/ai-fue/out/tiles_frontframe/part_r0c2.png

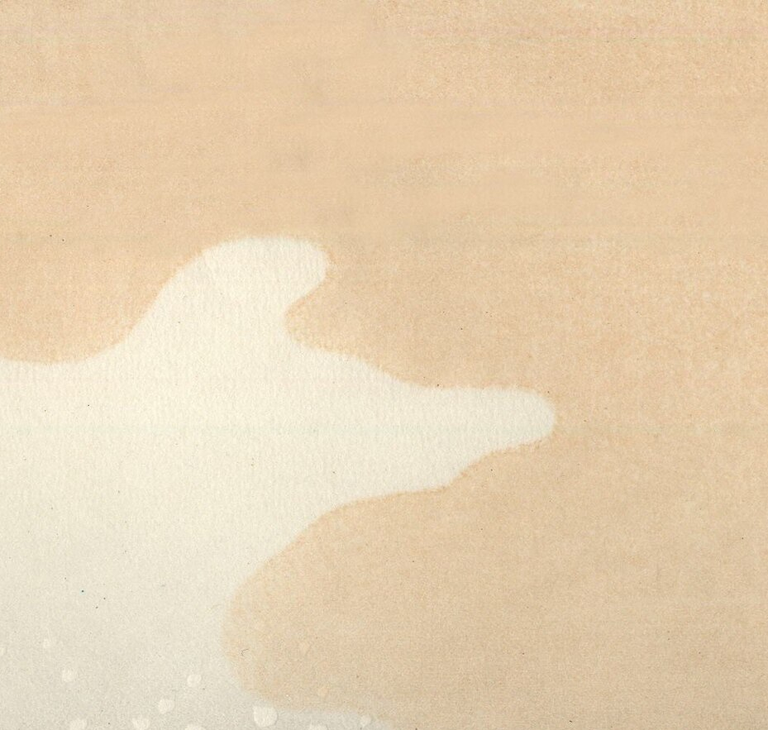
out/tiles_frontframe/part_r0c2.png
