qurihara/ai-fue/out/tiles_frontframe/part_r1c0.png

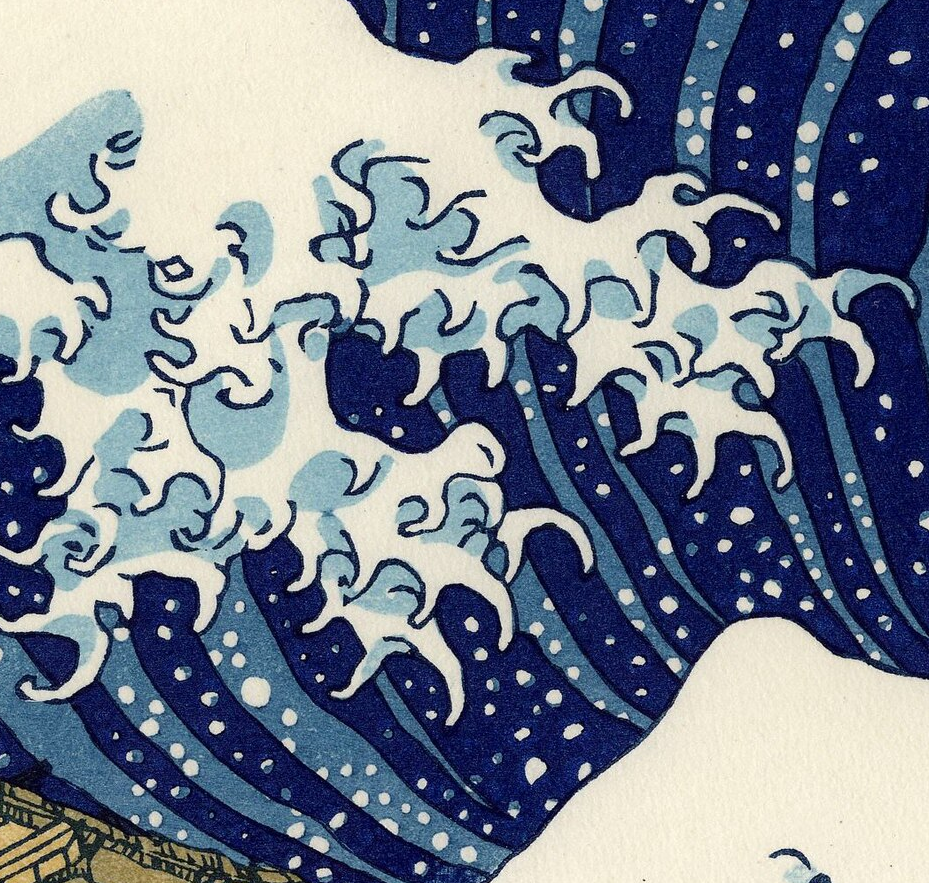
out/tiles_frontframe/part_r1c0.png
