qurihara/ai-fue/out/tiles_frontframe/part_r1c1.png

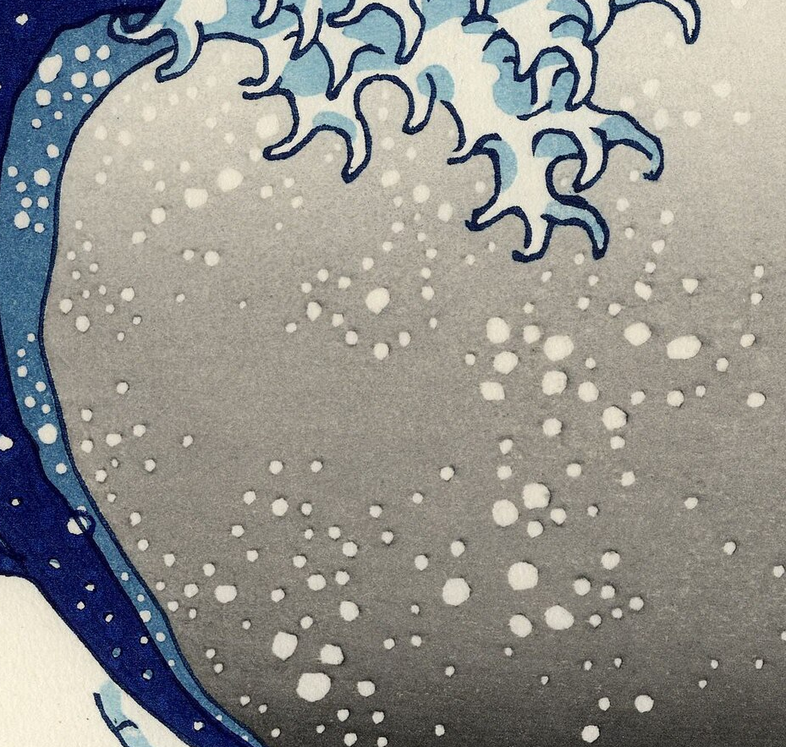
out/tiles_frontframe/part_r1c1.png
