qurihara/ai-fue/out/tiles_frontframe/part_r1c2.png

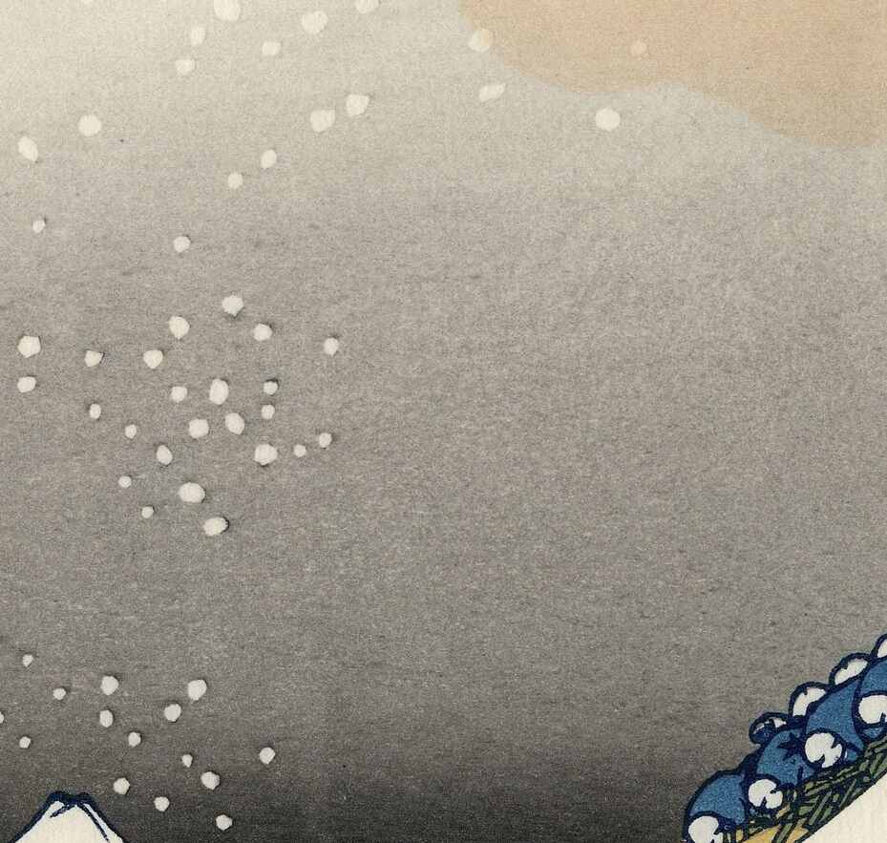
out/tiles_frontframe/part_r1c2.png
