qurihara/ai-fue/out/tiles_frontframe/part_r2c0.png

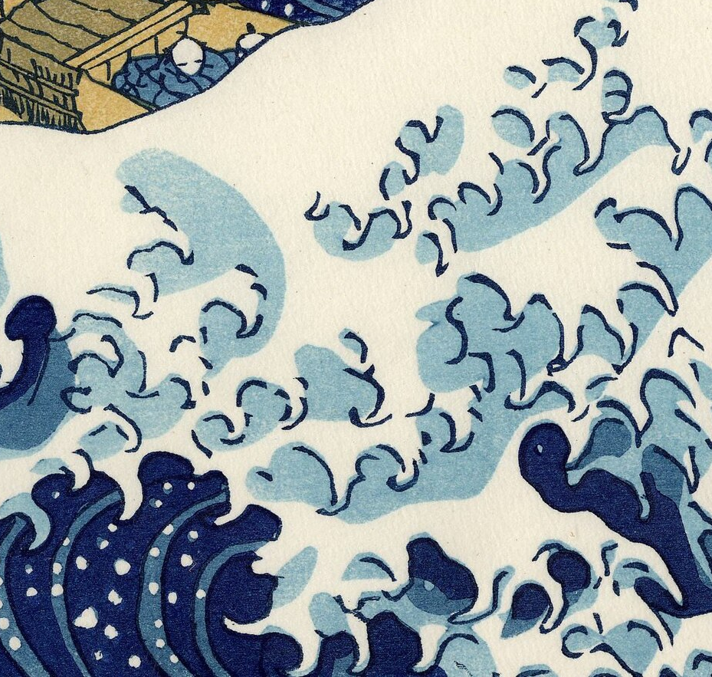
out/tiles_frontframe/part_r2c0.png
