qurihara/ai-fue/out/tiles_frontframe/part_r2c1.png

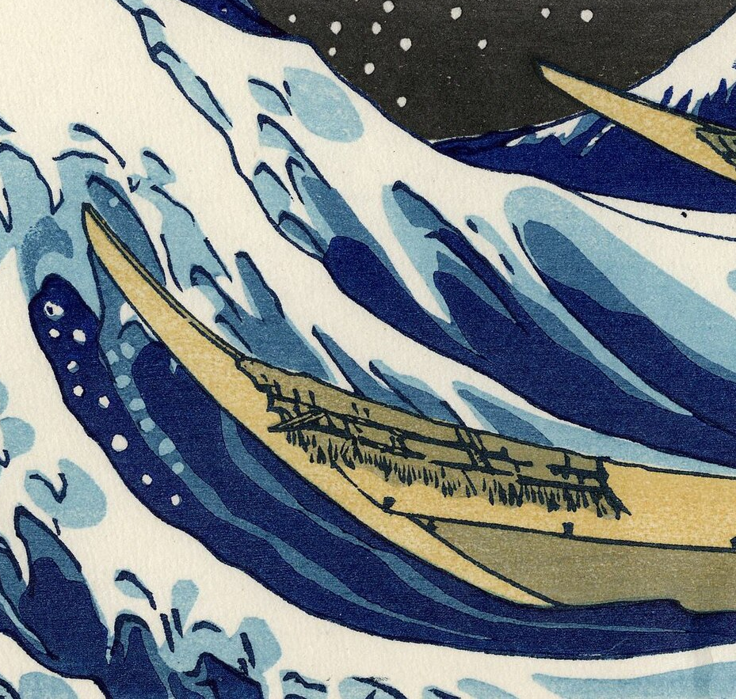
out/tiles_frontframe/part_r2c1.png
