qurihara/ai-fue/out/tiles_frontframe/part_r2c2.png

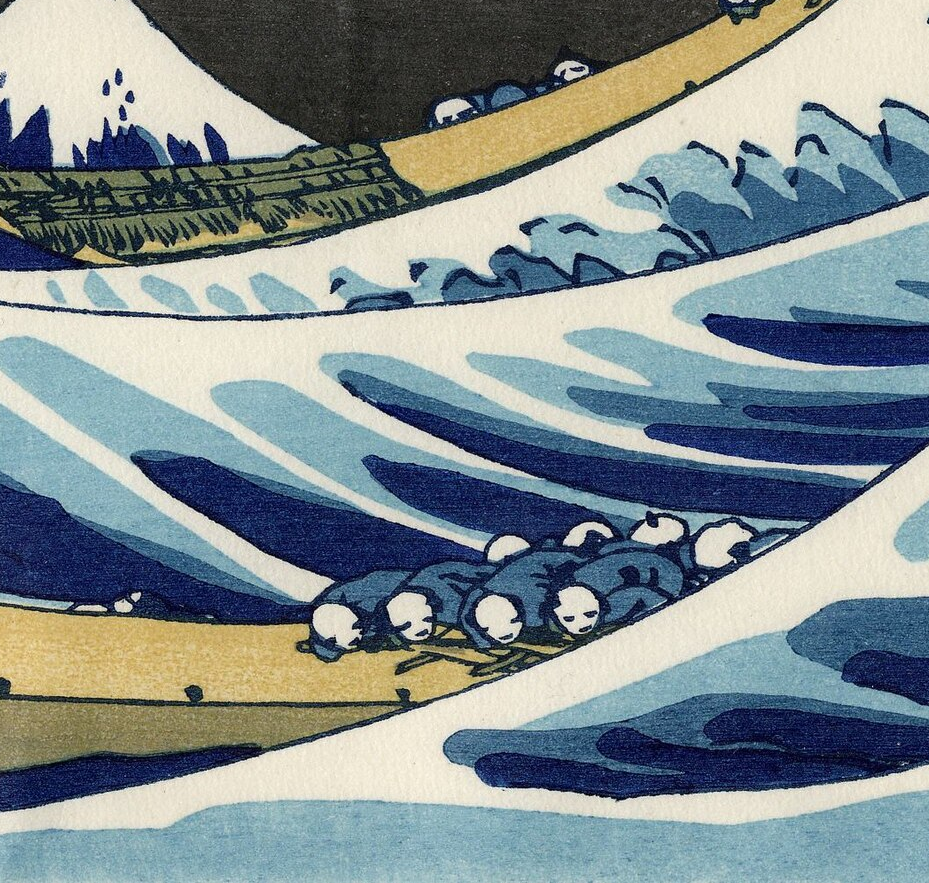
out/tiles_frontframe/part_r2c2.png
