qurihara/ai-fue/paper/cipherflute_representative_600x450.png

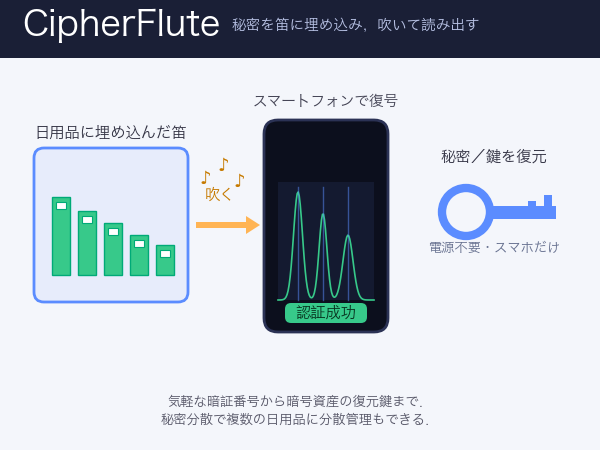
paper/cipherflute_representative_600x450.png
