qurihara/ai-fue/paper/figs/2of3_bookstand.jpg

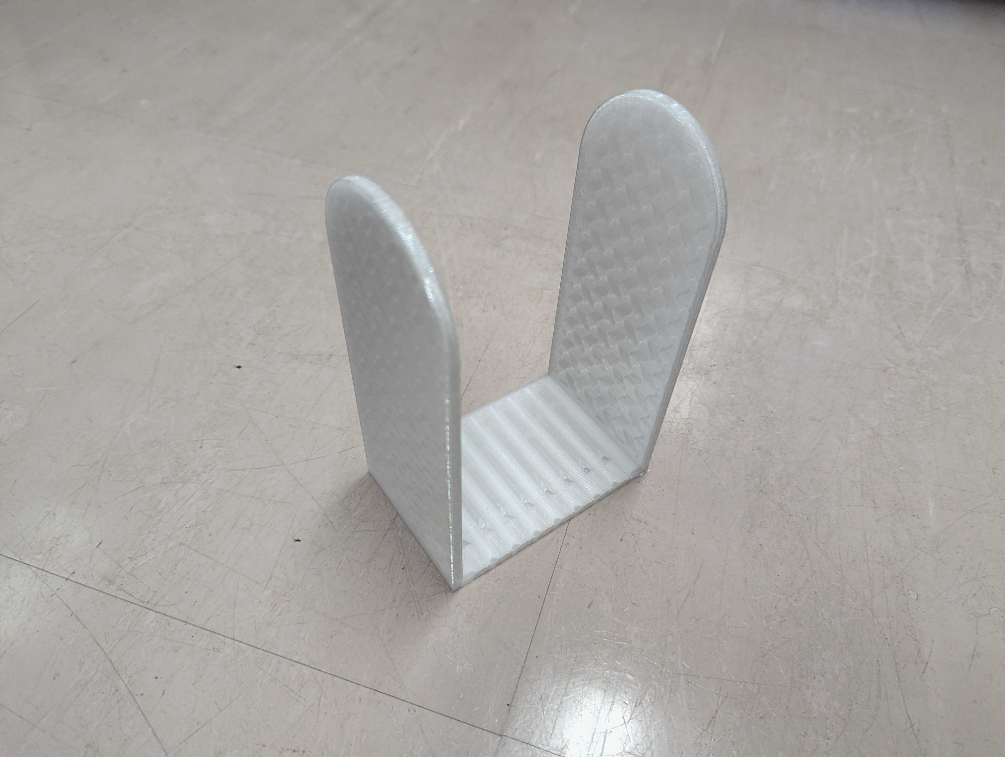
paper/figs/2of3_bookstand.jpg
