qurihara/ai-fue/paper/figs/2of3_box_2.jpg

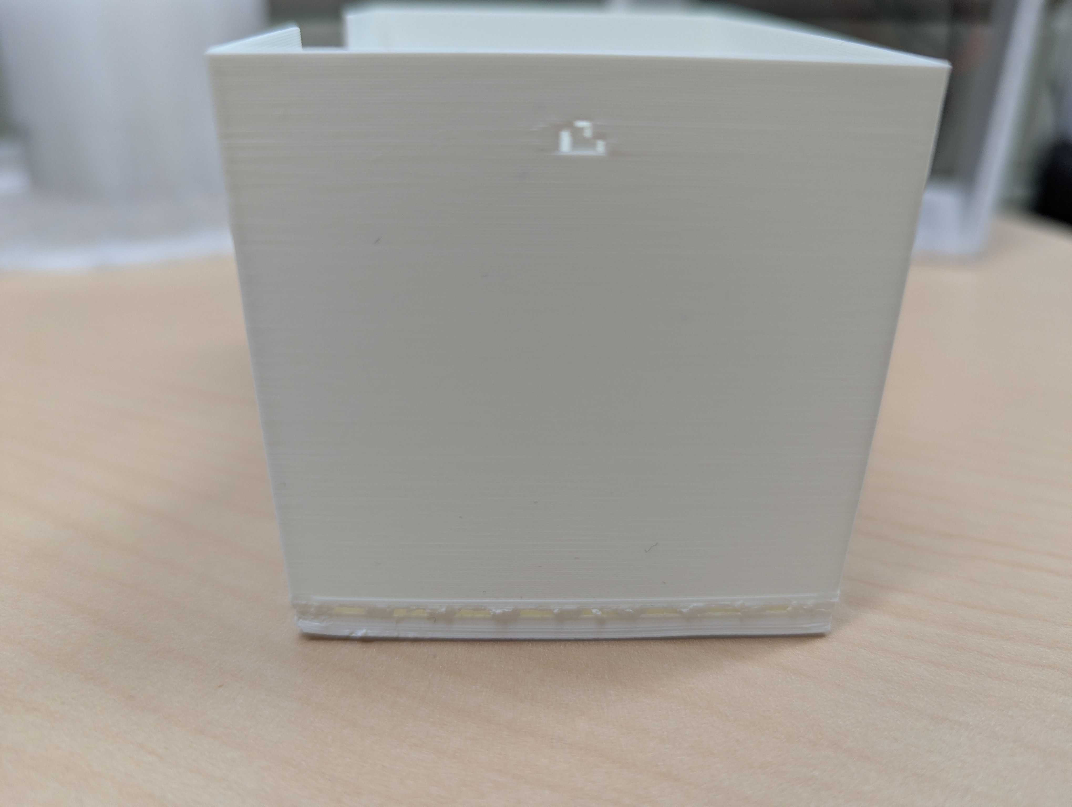
paper/figs/2of3_box_2.jpg
