qurihara/ai-fue/paper/figs/2of3_card.jpg

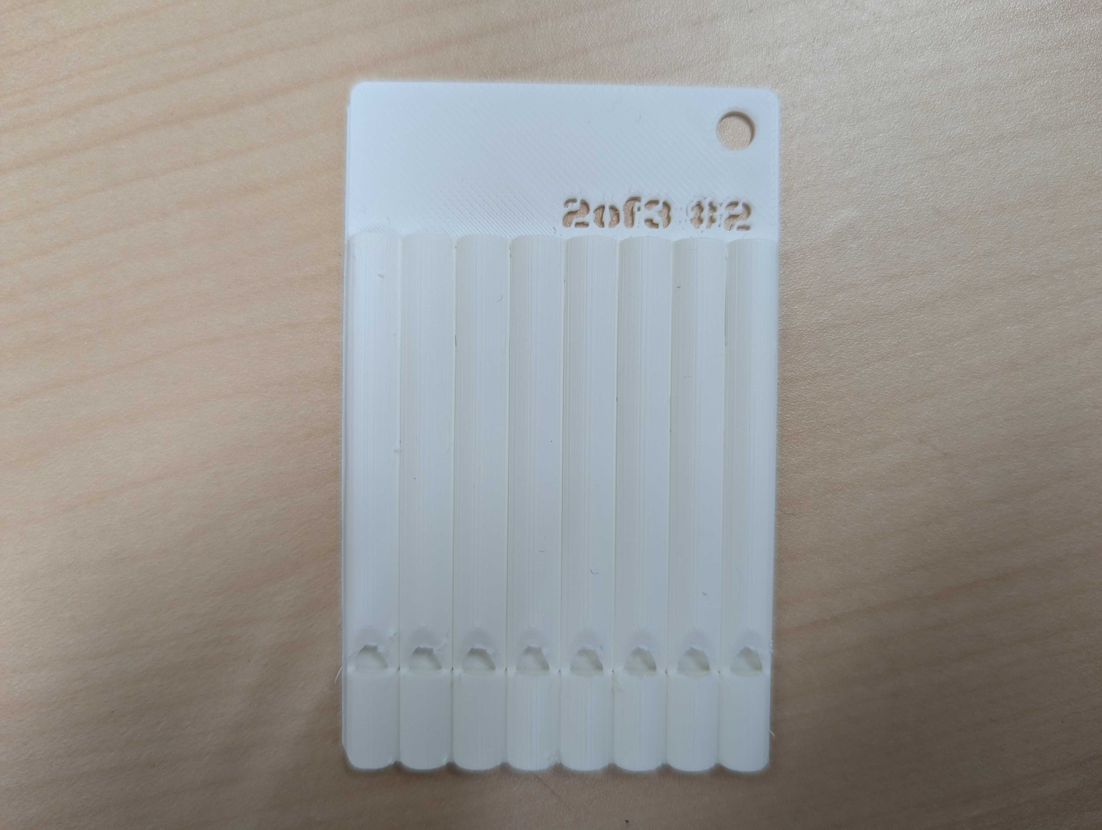
paper/figs/2of3_card.jpg
