qurihara/ai-fue/paper/figs/fig1_overview.png

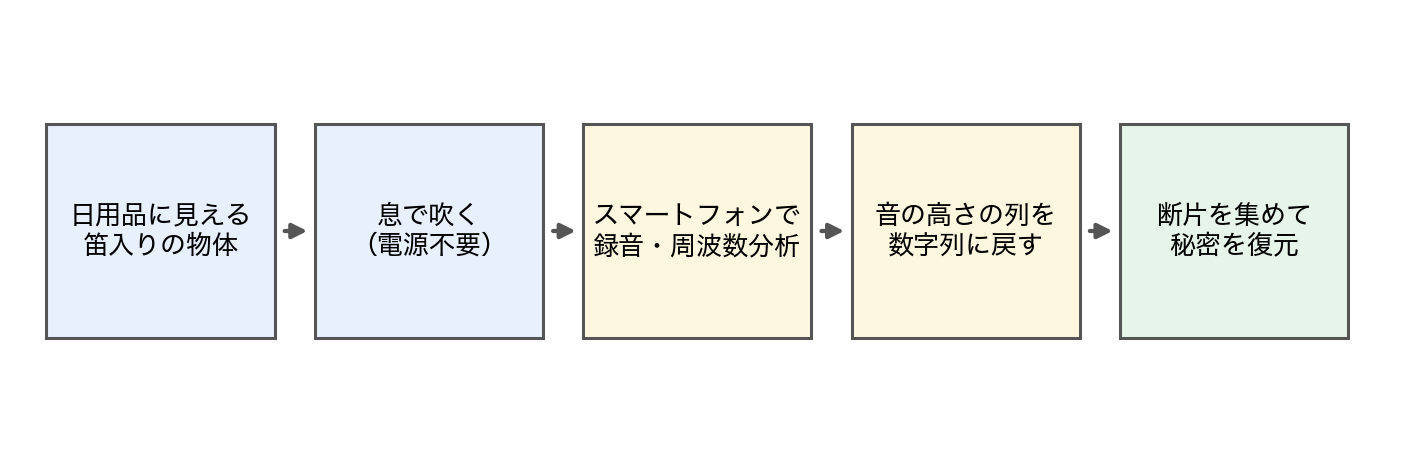
paper/figs/fig1_overview.png
