qurihara/ai-fue/paper/figs/fig2_plate.png

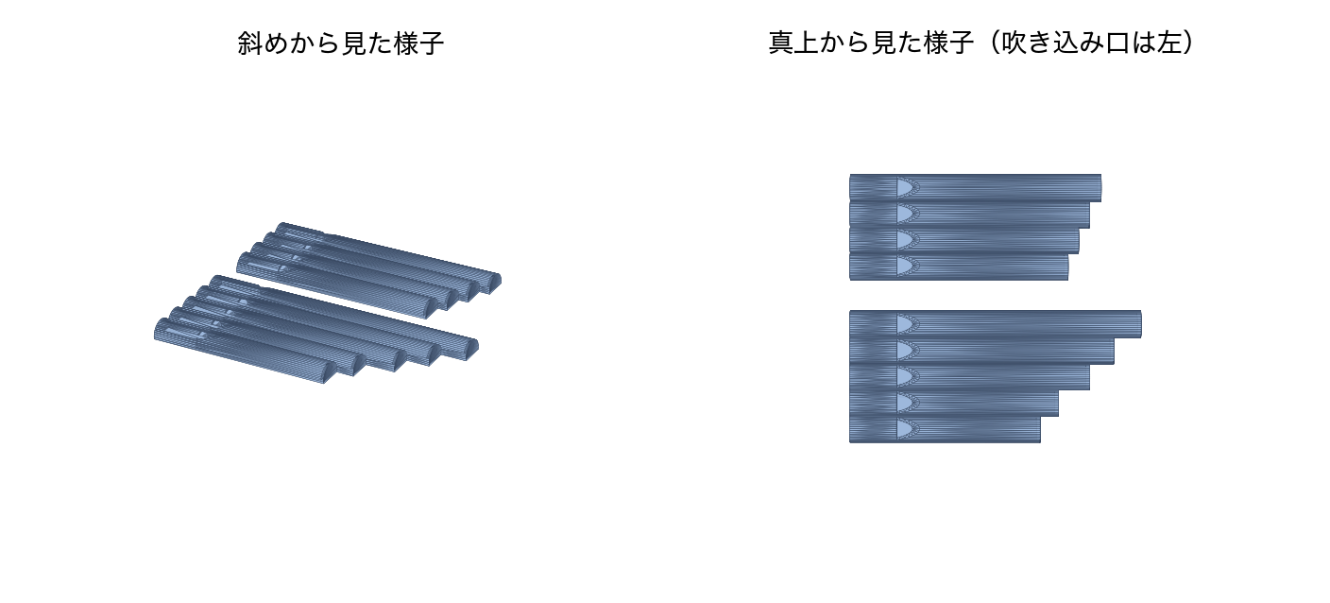
paper/figs/fig2_plate.png
