qurihara/ai-fue/paper/figs/fig3_slots.png

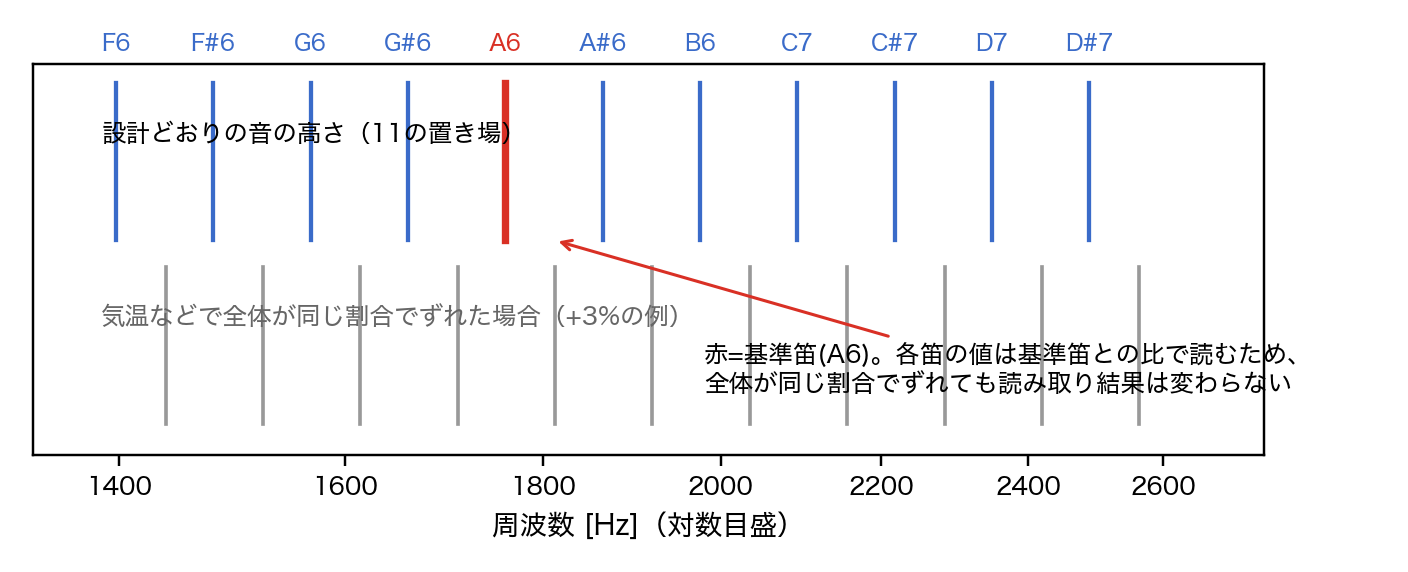
paper/figs/fig3_slots.png
