qurihara/ai-fue/paper/figs/fig4_prelim.png

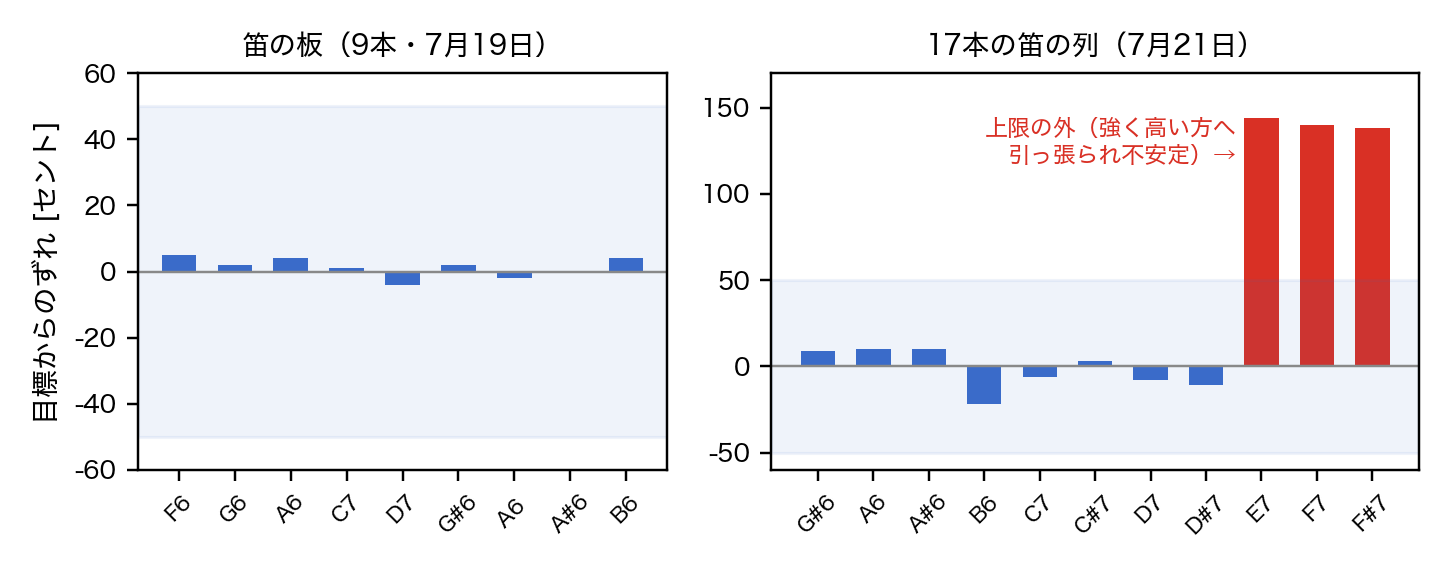
paper/figs/fig4_prelim.png
