qurihara/ai-fue/paper/figs/fig5_decoder.png

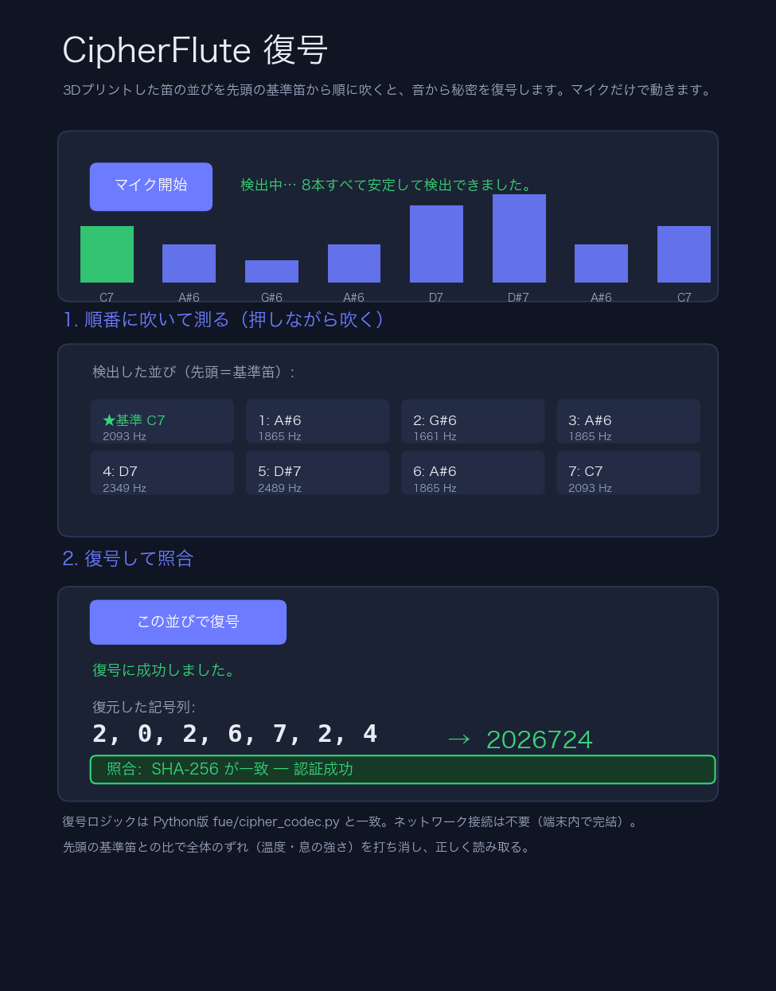
paper/figs/fig5_decoder.png
