qurihara/ai-fue/paper/figs/spool.jpg

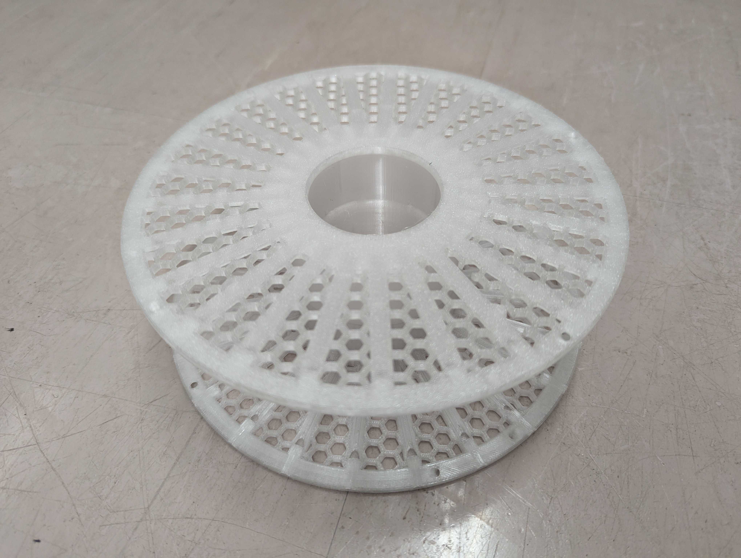
paper/figs/spool.jpg
