qurihara/ai-fue/harmonica_deck/cards_notch/card_Eb_Cm.stl

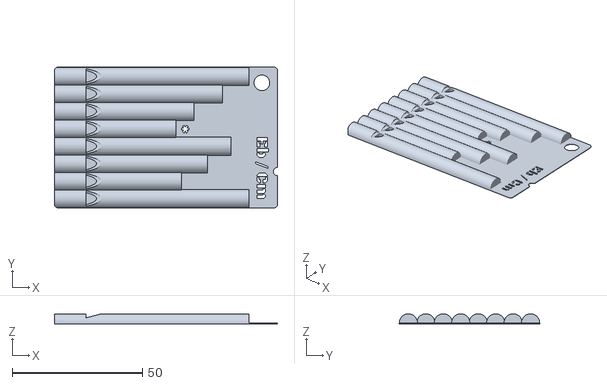
[picture p83: CAD file, 2026-07-24]
harmonica_deck/cards_notch/card_Eb_Cm.stl
85.6 x 54.0 x 4.00
