qurihara/ai-fue/harmonica_deck/cards_stencil/card_G_Em.stl

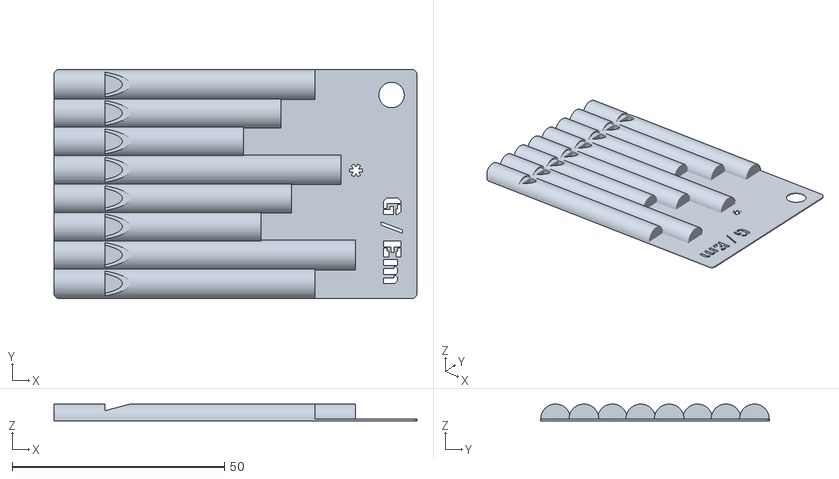
[picture p84: CAD file, 2026-07-18]
harmonica_deck/cards_stencil/card_G_Em.stl
85.6 x 54.0 x 4.00
