qurihara/ai-fue/mini-rect/recorder-mini-c-half-rect-v1.3mf

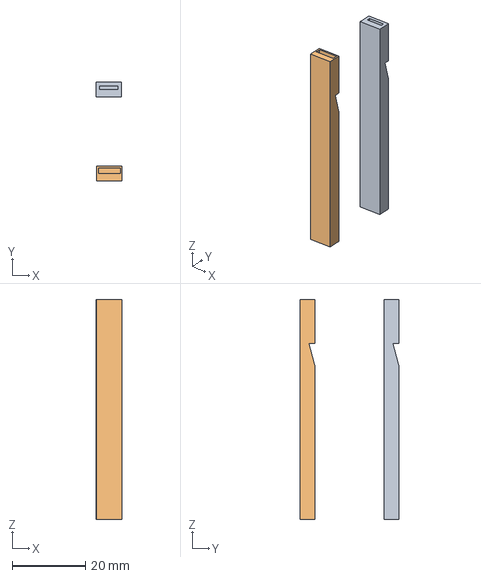
[picture p85: CAD file, 2026-07-24]
mini-rect/recorder-mini-c-half-rect-v1.3mf
7.21 x 26.9 x 60.0 mm
recorder-mini-c-v3-half-v3.stl
recorder-mini-c-v3-half-v3 (1).stl
