qurihara/ai-fue/mini10/recorder-mini-c-v3-half-2-v2.stl

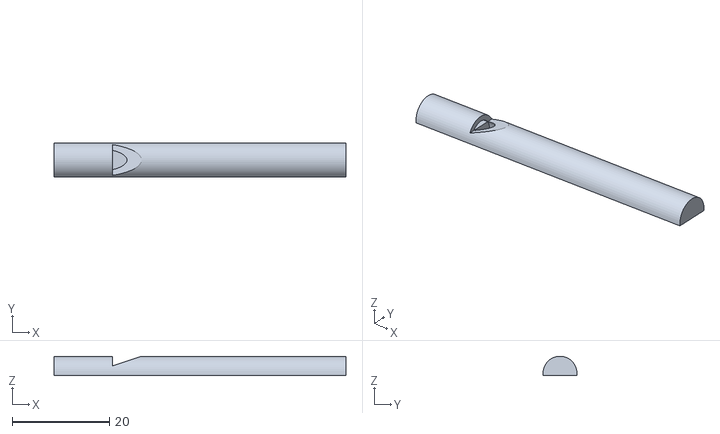
[picture p87: CAD file, 2026-07-24]
mini10/recorder-mini-c-v3-half-2-v2.stl
60.0 x 7.00 x 4.00
