qurihara/ai-fue/out/hokusai_tiles/tile_04_r1c0_base.stl

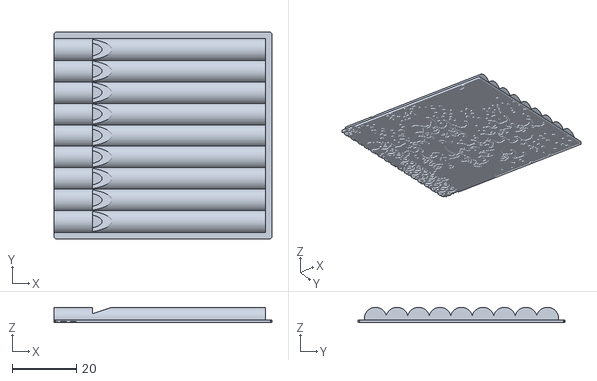
[picture p88: CAD file, 2026-08-05]
out/hokusai_tiles/tile_04_r1c0_base.stl
68.0 x 64.6 x 4.78
