qurihara/ai-fue/out/inverted/chordika_inv_Db_Bbm.stl

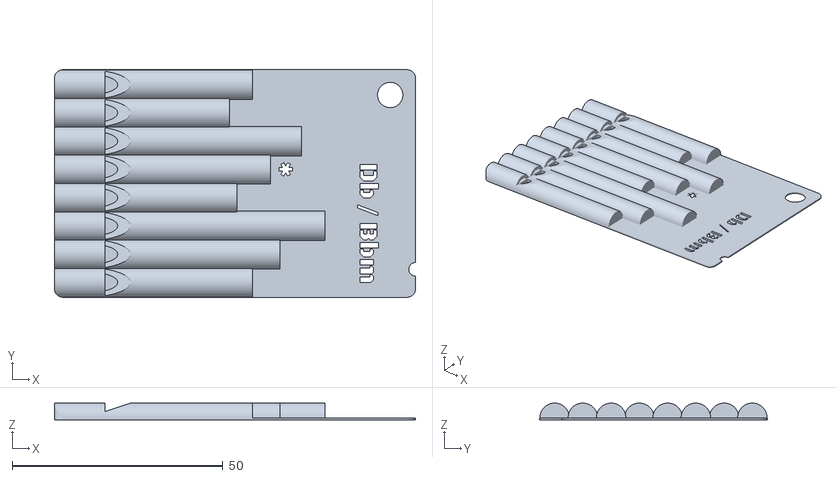
[picture p89: CAD file, 2026-08-08]
out/inverted/chordika_inv_Db_Bbm.stl
85.6 x 54.0 x 4.00
