qurihara/ai-fue/out/karuta/arazaramu_edge_upper_ink.stl

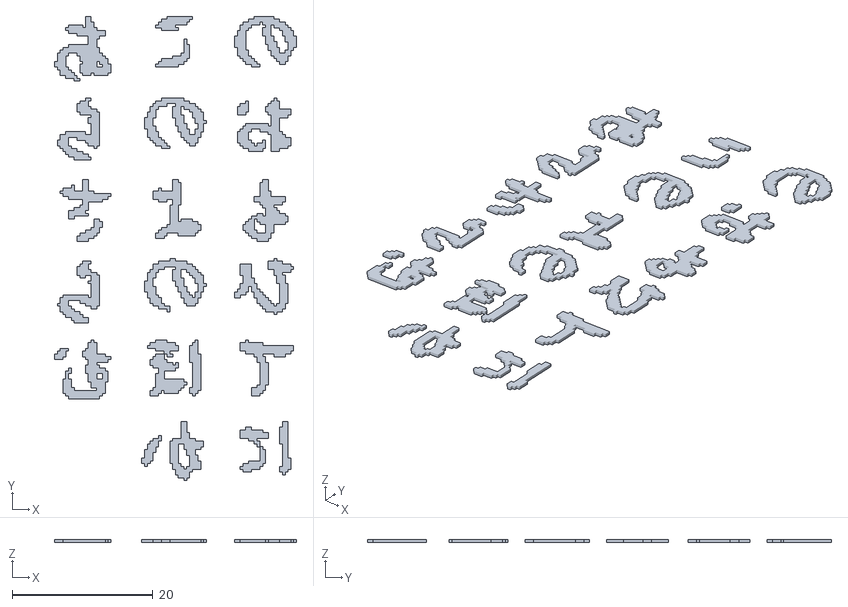
[picture p90: CAD file, 2026-08-14]
out/karuta/arazaramu_edge_upper_ink.stl
34.4 x 66.0 x 0.4
