qurihara/ai-fue/out/matching_flutes_v9b_pla_brim_h2d.gcode.3mf

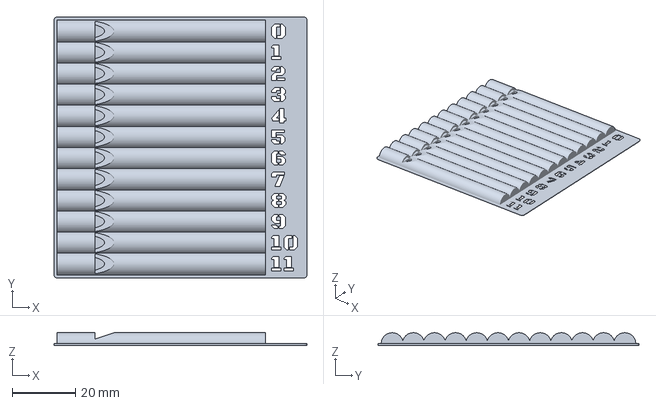
[picture p91: CAD file, 2026-08-12]
out/matching_flutes_v9b_pla_brim_h2d.gcode.3mf
80.2 x 82.7 x 4.00 mm
