qurihara/ai-fue/out/tiles_test/tile_01_r0c0_ink.stl

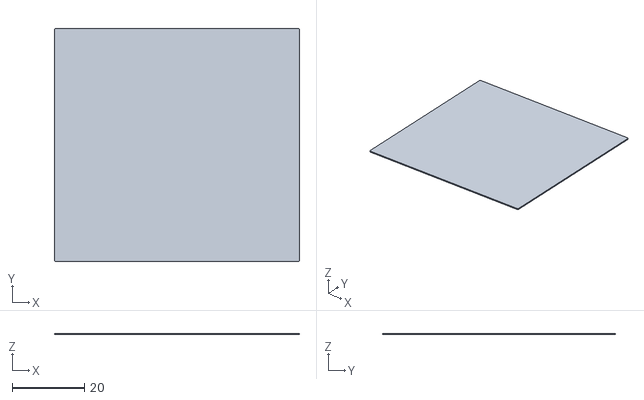
[picture p92: CAD file, 2026-08-09]
out/tiles_test/tile_01_r0c0_ink.stl
67.6 x 64.4 x 0.4
