qurihara/ai-fue/templates/a1mini_skeleton.3mf

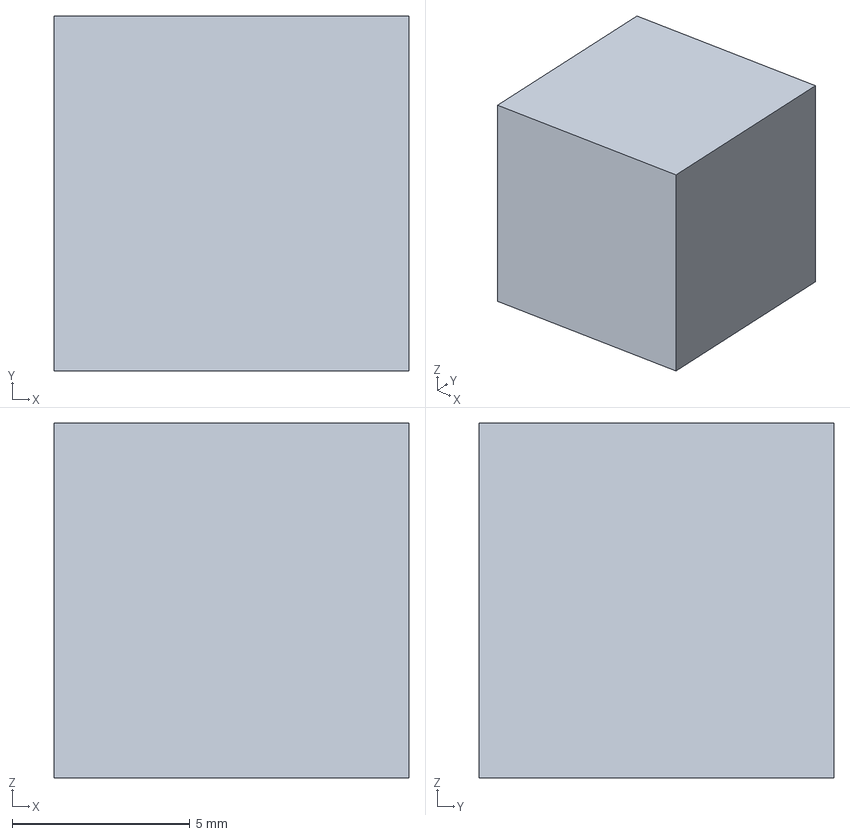
[picture p94: CAD file, 2026-07-01]
templates/a1mini_skeleton.3mf
10.0 x 10.0 x 10.0 mm
