qurihara/ai-fue/assets/geneva_ref_split/part4.stl

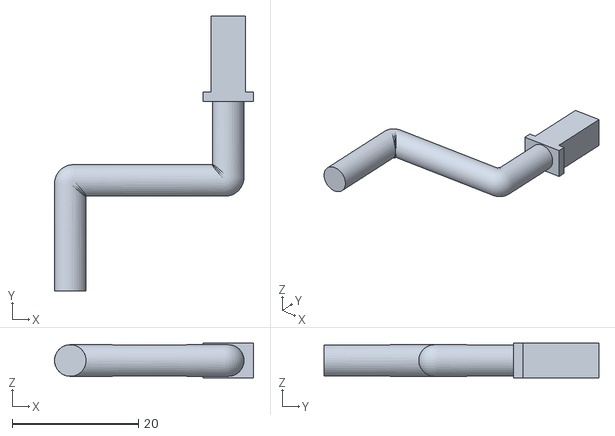
[picture p95: CAD file, 2026-07-03]
assets/geneva_ref_split/part4.stl
31.5 x 43.5 x 5.50
