qurihara/ai-fue/assets/rod_v6.stl

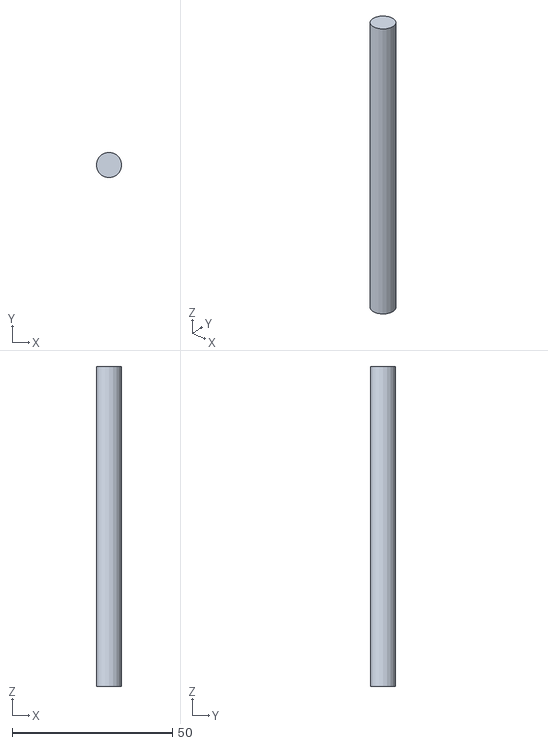
[picture p96: CAD file, 2026-07-01]
assets/rod_v6.stl
7.90 x 7.90 x 100.0
