qurihara/ai-fue/mini-rect/recorder-mini-c-half-rect-1-v1.stl

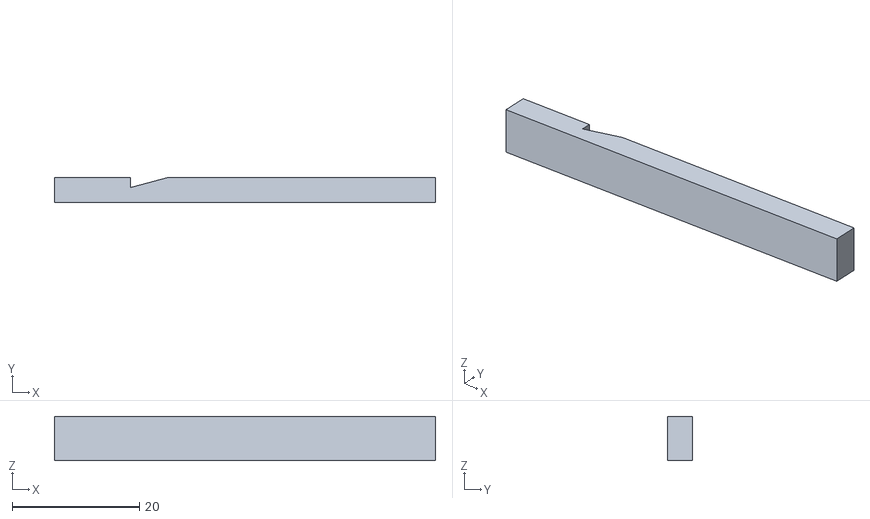
[picture p97: CAD file, 2026-07-24]
mini-rect/recorder-mini-c-half-rect-1-v1.stl
60.0 x 4.00 x 7.00
