qurihara/ai-fue/mini/recorder-mini-c-v3-half-v2-60.stl

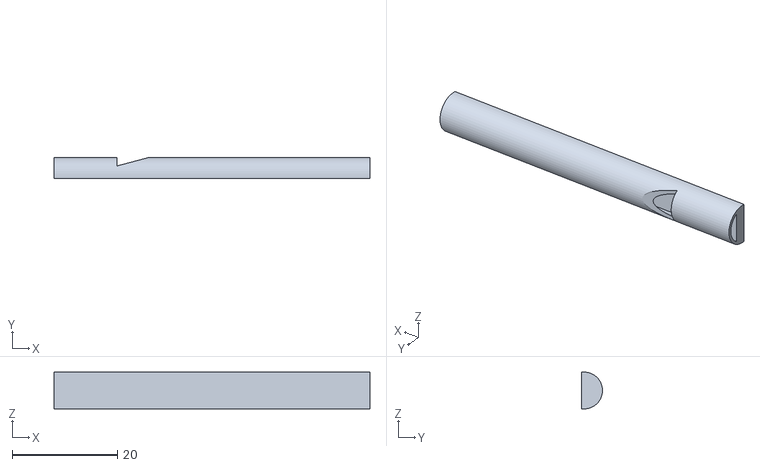
[picture p98: CAD file, 2026-07-17]
mini/recorder-mini-c-v3-half-v2-60.stl
60.0 x 4.00 x 7.00
