qurihara/ai-fue/out/hokusai_tiles/tile_06_r1c2_base.stl

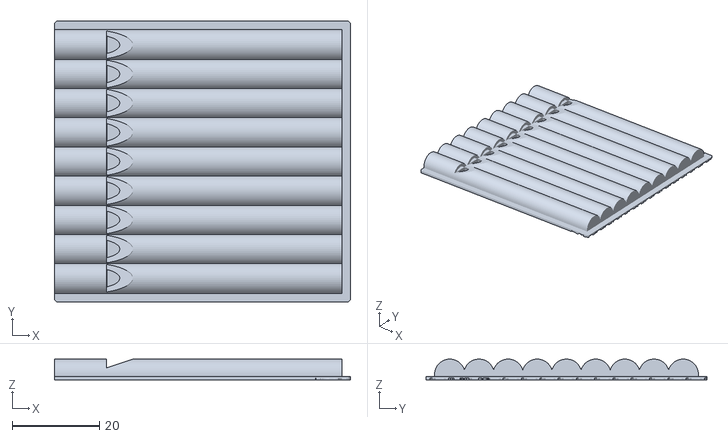
[picture p99: CAD file, 2026-08-05]
out/hokusai_tiles/tile_06_r1c2_base.stl
68.0 x 64.6 x 4.78
