qurihara/ai-fue/out/tiles_test/tile_01_r0c0_base.stl

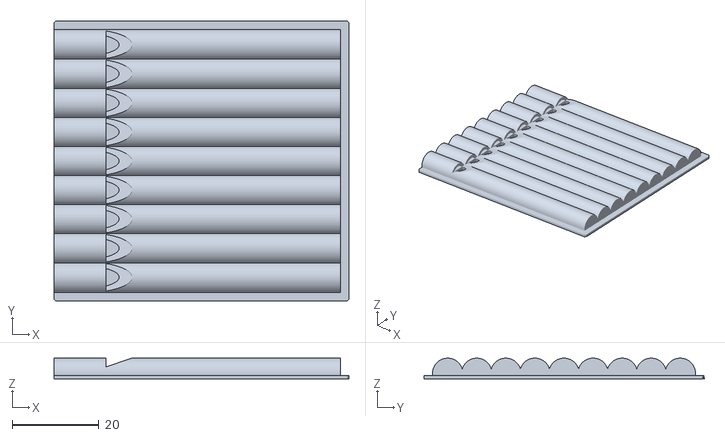
[picture p101: CAD file, 2026-08-09]
out/tiles_test/tile_01_r0c0_base.stl
68.0 x 64.6 x 4.78
