qurihara/ai-fue/out/tiles_test2/tile_02_r0c1_ink.stl

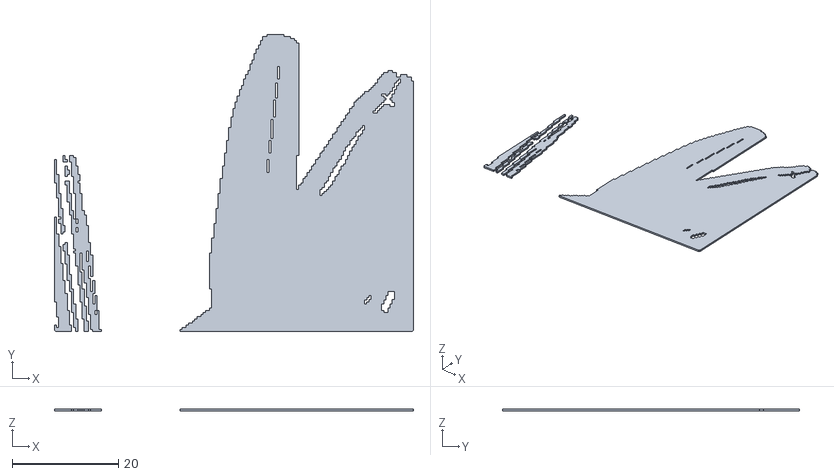
[picture p102: CAD file, 2026-08-09]
out/tiles_test2/tile_02_r0c1_ink.stl
67.6 x 56.0 x 0.4
