qurihara/ai-fue/swap_output/eject_only.swap.3mf

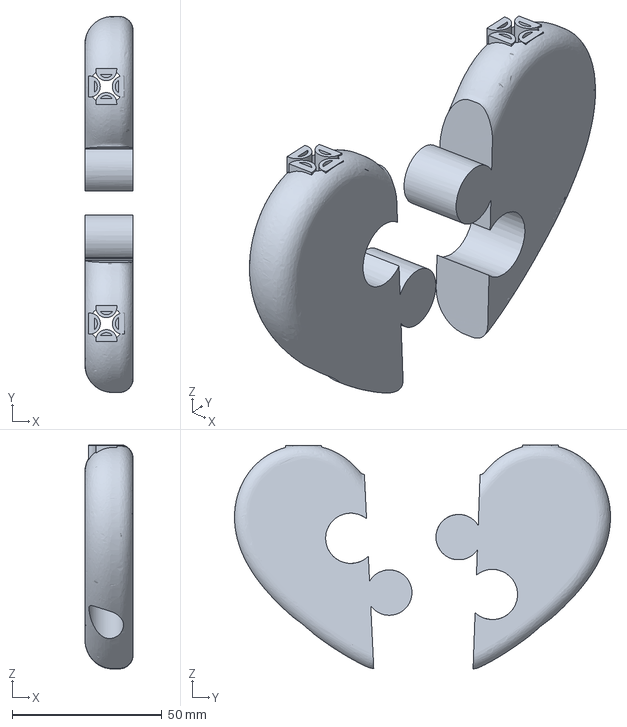
[picture p103: CAD file, 2026-07-24]
swap_output/eject_only.swap.3mf
16.1 x 125.5 x 74.7 mm
