qurihara/ai-fue/assets/body_v6.stl

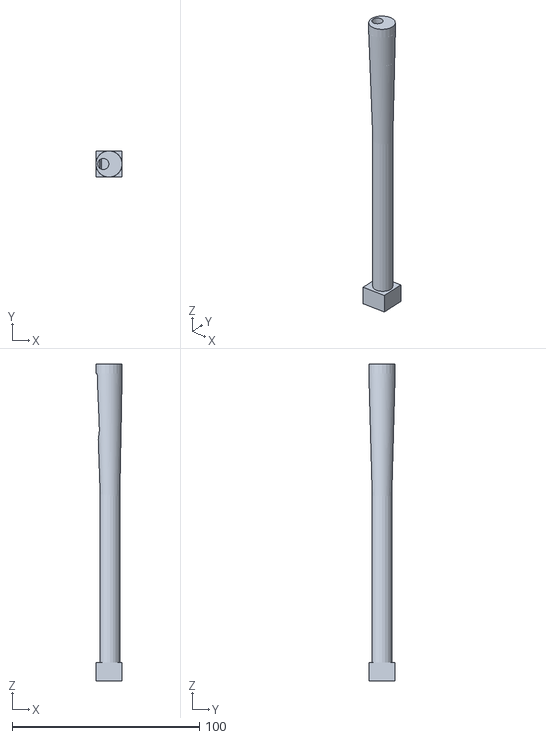
[picture p104: CAD file, 2026-07-01]
assets/body_v6.stl
14.1 x 14.1 x 169.5
