qurihara/ai-fue/assets/geneva_ref/ref_wheel.stl

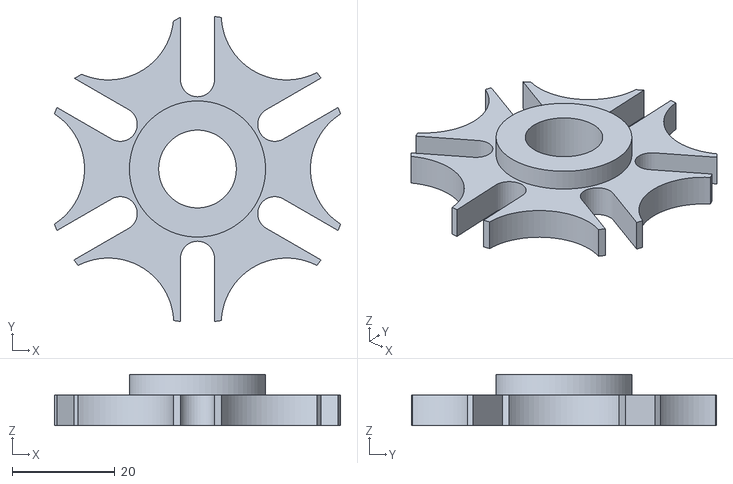
[picture p105: CAD file, 2026-07-03]
assets/geneva_ref/ref_wheel.stl
55.6 x 59.2 x 10.0
