qurihara/ai-fue/mini/recorder-mini-c-v3-half-v2.3mf

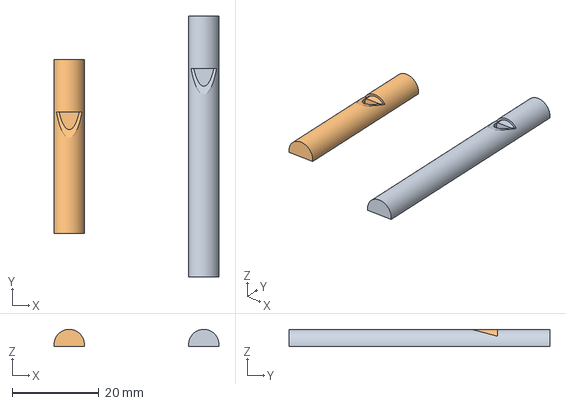
[picture p106: CAD file, 2026-07-17]
mini/recorder-mini-c-v3-half-v2.3mf
38.0 x 60.0 x 4.00 mm
recorder-mini-c-v3-half-v2-60.stl
recorder-mini-c-v3-half-v2-40.stl
