qurihara/ai-fue/mini10/recorder-mini-c-v3-half-1.6-v2.3mf

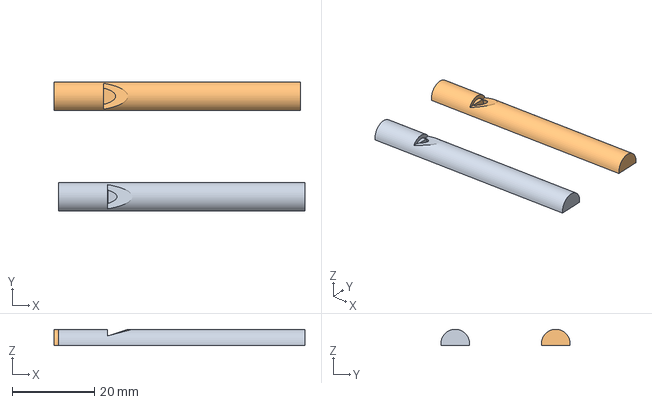
[picture p107: CAD file, 2026-07-24]
mini10/recorder-mini-c-v3-half-1.6-v2.3mf
61.1 x 31.5 x 4.00 mm
recorder-mini-c-v3-half-1.6-v2.stl
recorder-mini-c-v3-half-2-v2.stl
