qurihara/ai-fue/out/karuta/arazaramu_edge_h2d.3mf

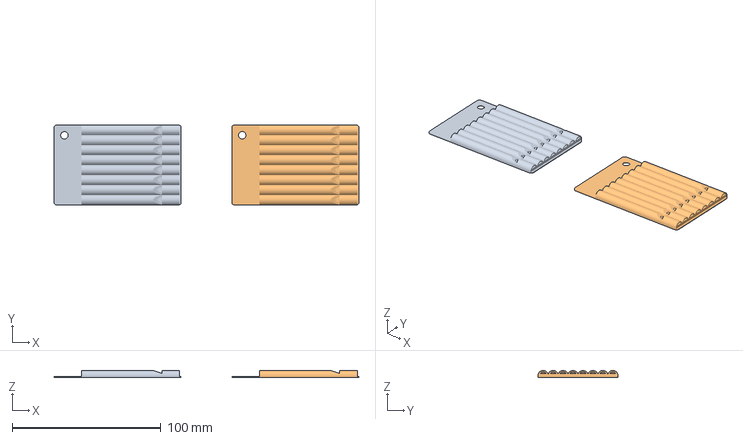
[picture p108: CAD file, 2026-08-14]
out/karuta/arazaramu_edge_h2d.3mf
205.2 x 54.0 x 4.75 mm
arazaramu_edge_upper
arazaramu_edge_lower
