qurihara/ai-fue/out/tiles_test2/tile_01_r0c0_ink.stl

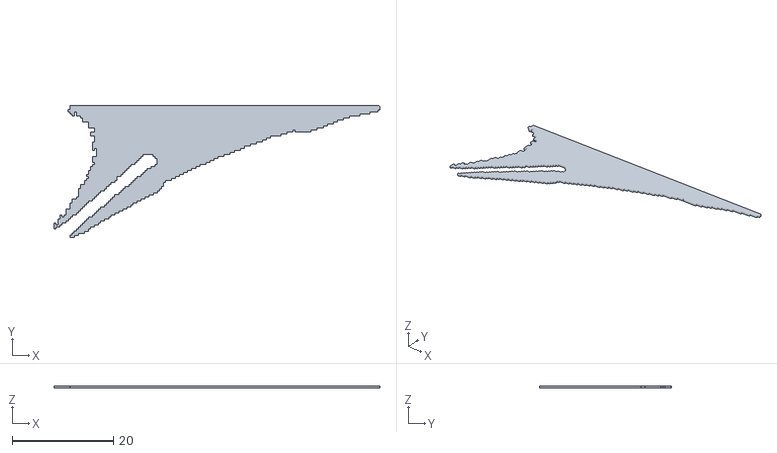
[picture p109: CAD file, 2026-08-09]
out/tiles_test2/tile_01_r0c0_ink.stl
64.4 x 26.0 x 0.4
