qurihara/ai-fue/assets/geneva_ref_split/part3.stl

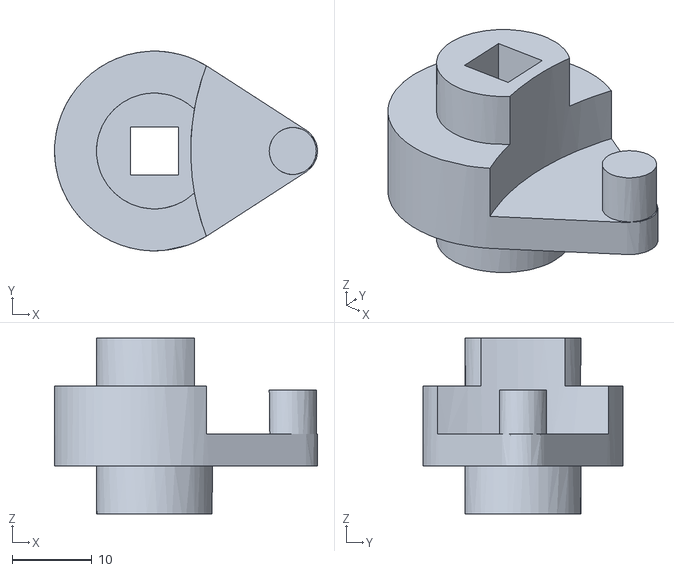
[picture p110: CAD file, 2026-07-03]
assets/geneva_ref_split/part3.stl
32.9 x 25.0 x 22.0
