qurihara/ai-fue/assets/slide-recorder-head-v6.stl

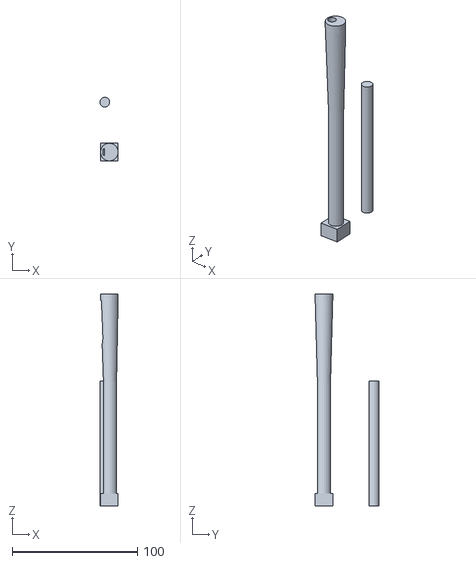
[picture p111: CAD file, 2026-07-01]
assets/slide-recorder-head-v6.stl
14.6 x 50.9 x 169.5
