qurihara/ai-fue/mini/recorder-mini-c-v3-half-v2-40.stl

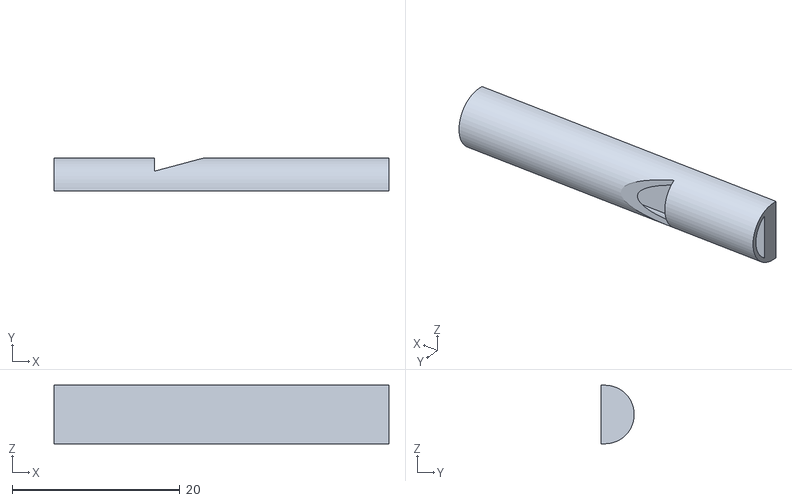
[picture p113: CAD file, 2026-07-17]
mini/recorder-mini-c-v3-half-v2-40.stl
40.0 x 4.00 x 7.00
