qurihara/ai-fue/out/hokusai_tiles/tile_05_r1c1_ink.stl

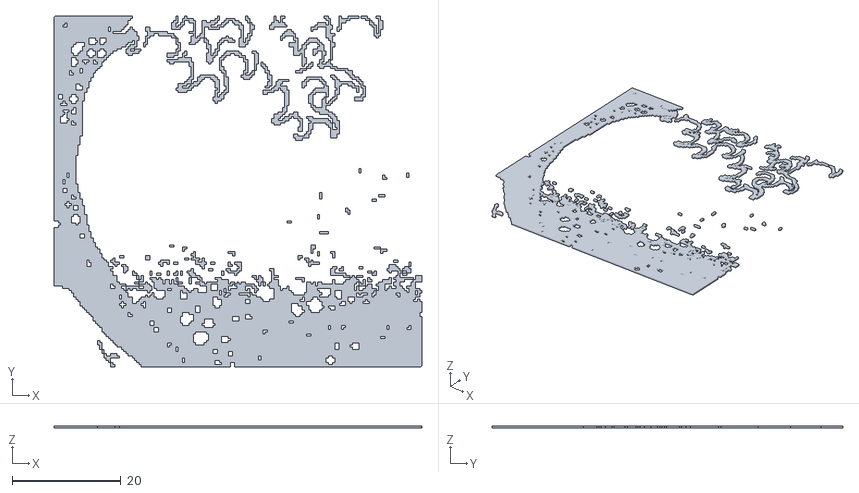
[picture p114: CAD file, 2026-08-05]
out/hokusai_tiles/tile_05_r1c1_ink.stl
67.6 x 64.4 x 0.4
