qurihara/ai-fue/out/karuta/arazaramu_edge_upper_base.stl

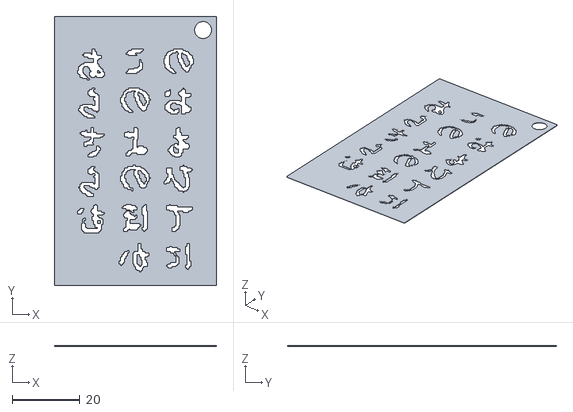
[picture p115: CAD file, 2026-08-14]
out/karuta/arazaramu_edge_upper_base.stl
48.0 x 79.6 x 0.4
