qurihara/ai-fue/assets/slide-recorder-head-v5x8.stl

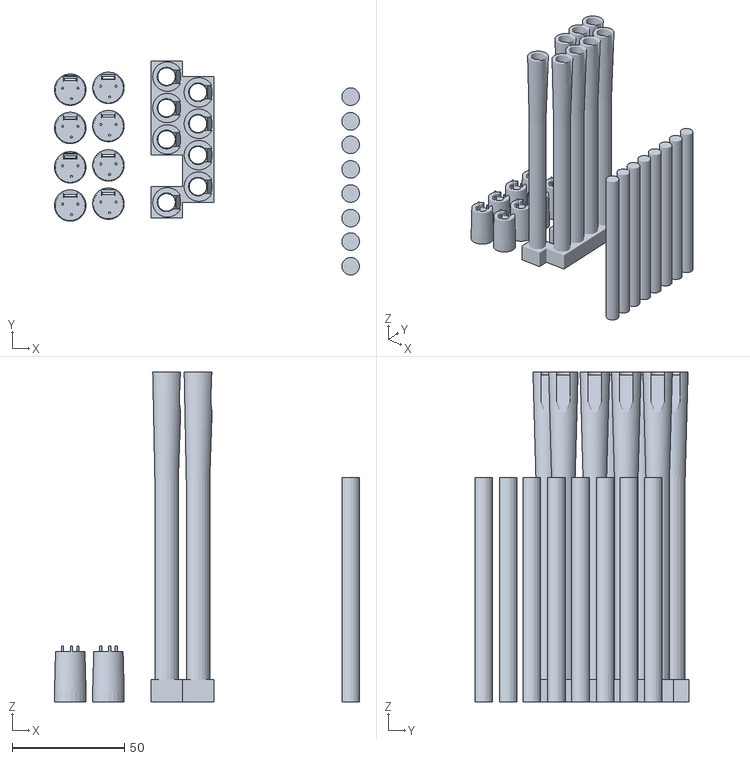
[picture p116: CAD file, 2026-07-01]
assets/slide-recorder-head-v5x8.stl
135.9 x 95.4 x 147.0
