qurihara/ai-fue/out/hokusai_tiles/tile_02_r0c1_ink.stl

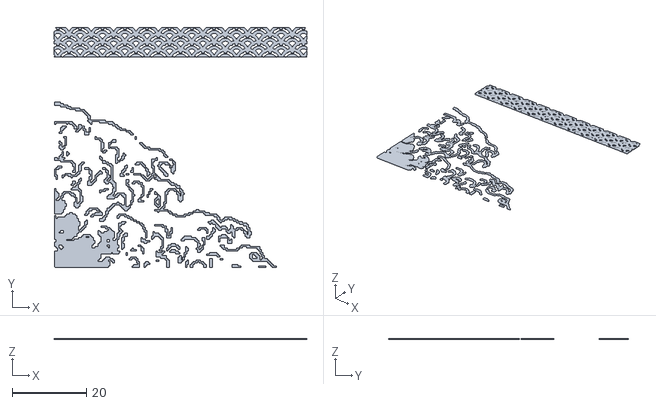
[picture p117: CAD file, 2026-08-05]
out/hokusai_tiles/tile_02_r0c1_ink.stl
68.0 x 64.5 x 0.4
