qurihara/ai-fue/mini/recorder-mini-c-v3.stl

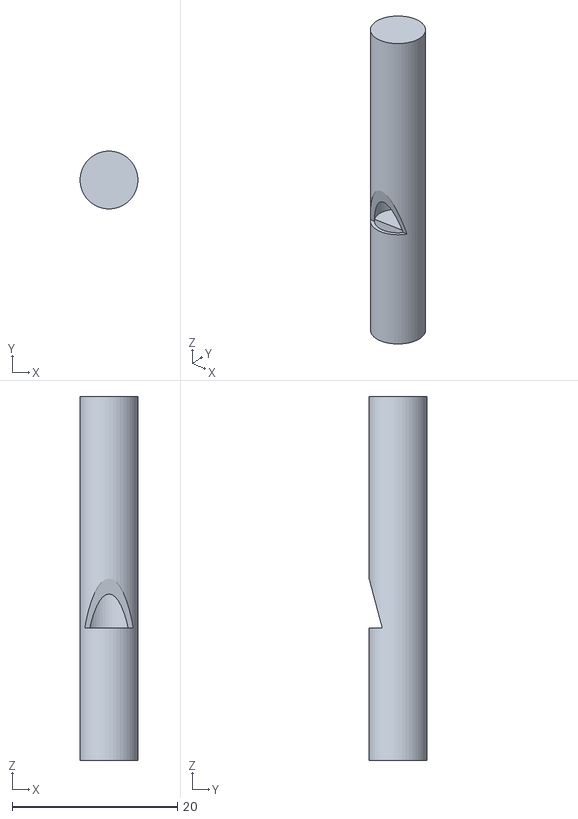
[picture p118: CAD file, 2026-07-14]
mini/recorder-mini-c-v3.stl
7.00 x 7.00 x 44.0
