qurihara/ai-fue/out/karuta/arazaramu_edge_lower_edge.stl

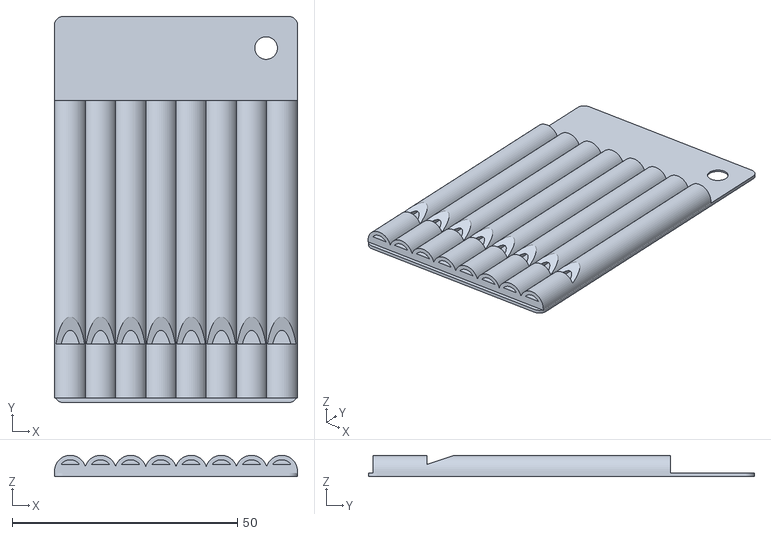
[picture p119: CAD file, 2026-08-14]
out/karuta/arazaramu_edge_lower_edge.stl
54.0 x 85.6 x 4.75
