qurihara/ai-fue/out/hokusai_tiles/tile_08_r2c1_ink.stl

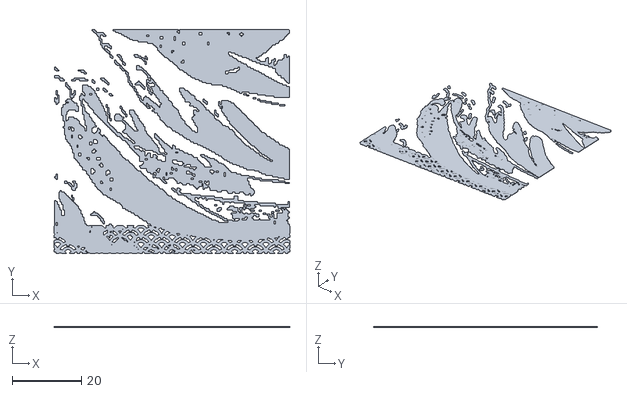
[picture p120: CAD file, 2026-08-05]
out/hokusai_tiles/tile_08_r2c1_ink.stl
68.0 x 64.5 x 0.4
