qurihara/ai-fue/out/karuta/arazaramu_edge_lower_ink.stl

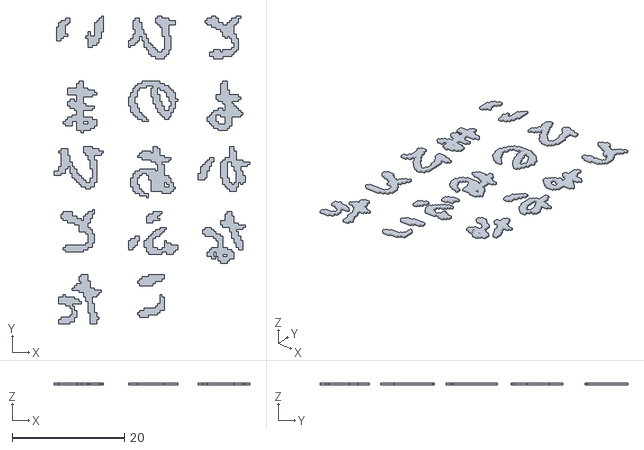
[picture p121: CAD file, 2026-08-14]
out/karuta/arazaramu_edge_lower_ink.stl
34.8 x 54.8 x 0.4
