qurihara/ai-fue/out/hokusai_tiles/tile_06_r1c2_ink.stl

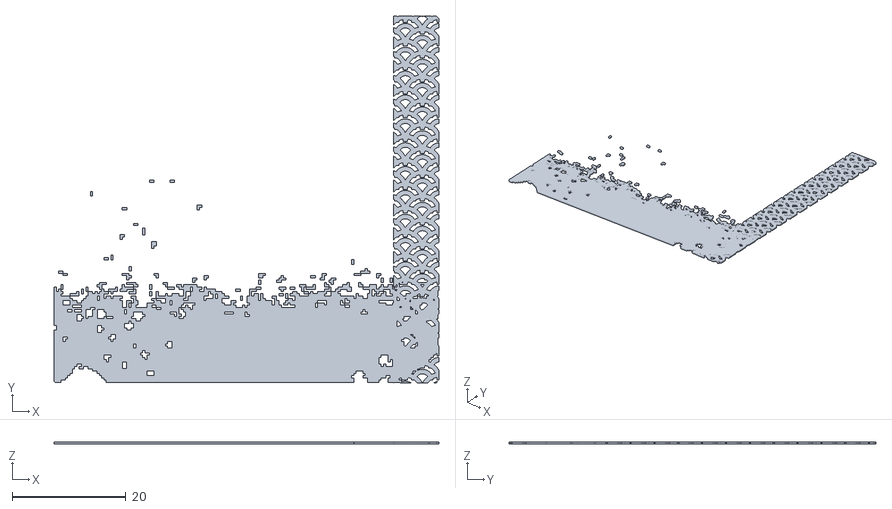
[picture p122: CAD file, 2026-08-05]
out/hokusai_tiles/tile_06_r1c2_ink.stl
67.8 x 64.6 x 0.4
