qurihara/ai-fue/out/hokusai_tiles/tile_07_r2c0_ink.stl

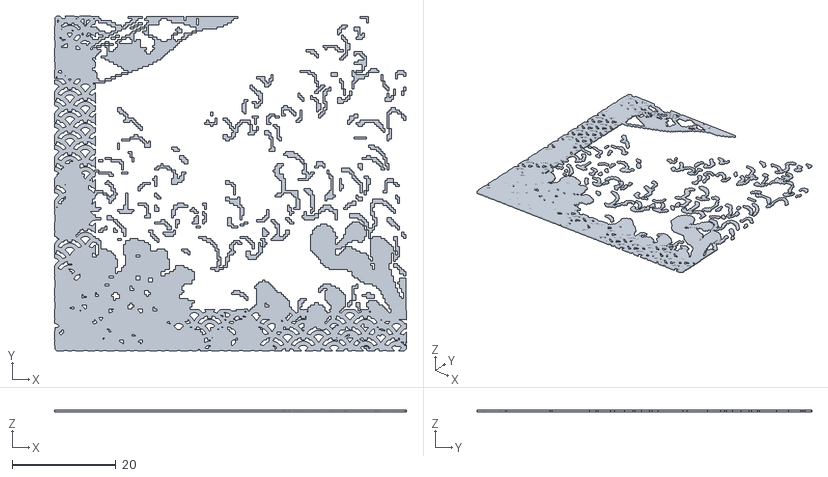
[picture p123: CAD file, 2026-08-05]
out/hokusai_tiles/tile_07_r2c0_ink.stl
68.0 x 64.6 x 0.4
