qurihara/ai-fue/out/hokusai_tiles/tile_04_r1c0_ink.stl

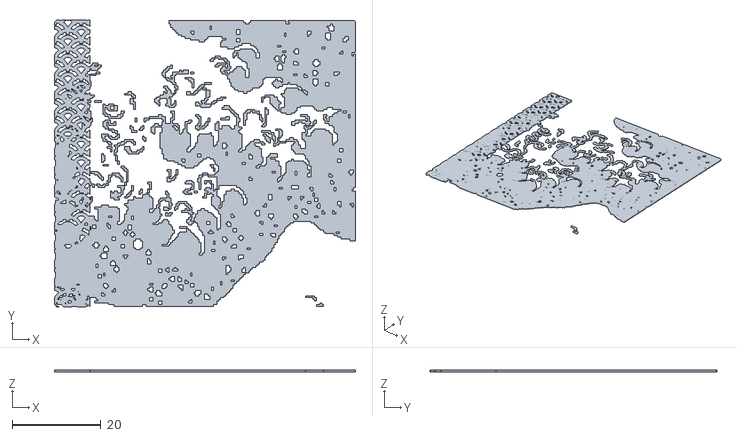
[picture p124: CAD file, 2026-08-05]
out/hokusai_tiles/tile_04_r1c0_ink.stl
67.8 x 64.6 x 0.4
