qurihara/ai-fue/out/inverted/chordika_inv_Fs_Dsm.stl

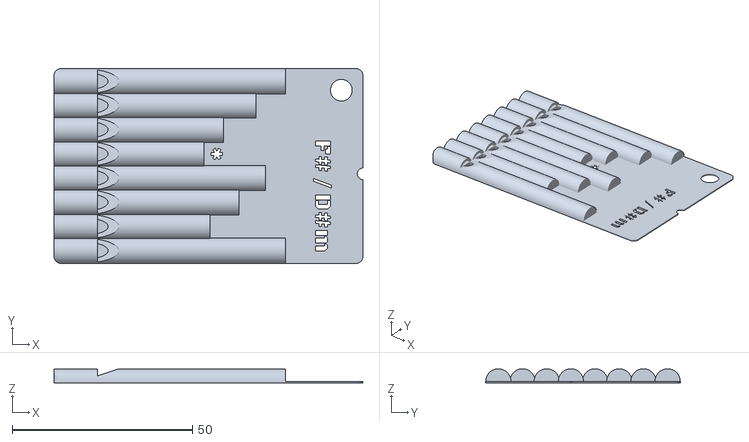
[picture p125: CAD file, 2026-08-08]
out/inverted/chordika_inv_Fs_Dsm.stl
85.6 x 54.0 x 4.00
