qurihara/ai-fue/out/recorika_G_A_plate_h2d.stl

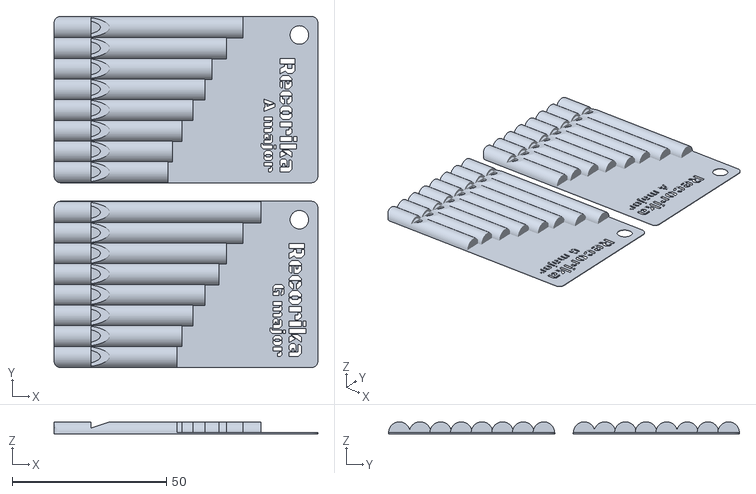
[picture p126: CAD file, 2026-08-08]
out/recorika_G_A_plate_h2d.stl
85.6 x 114.0 x 4.00
