qurihara/ai-fue/out/karuta/sutoku_edge_thin_lower_base.stl

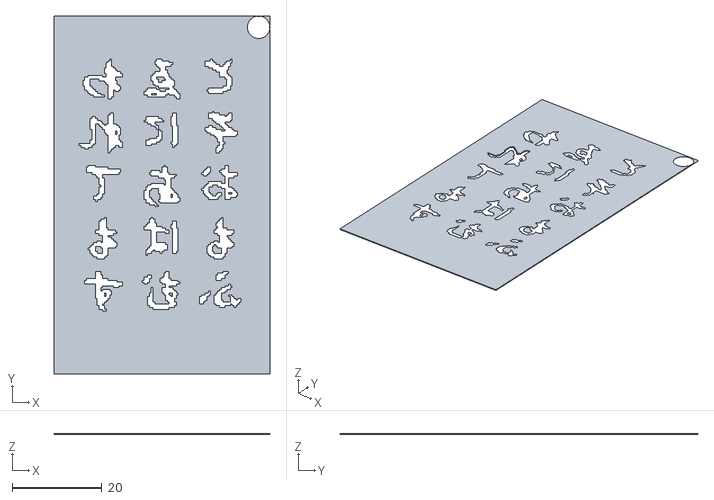
[picture p127: CAD file, 2026-08-13]
out/karuta/sutoku_edge_thin_lower_base.stl
48.0 x 79.6 x 0.2
