qurihara/ai-fue/out/hokusai_frame_box_a1mini_A.swap.3mf

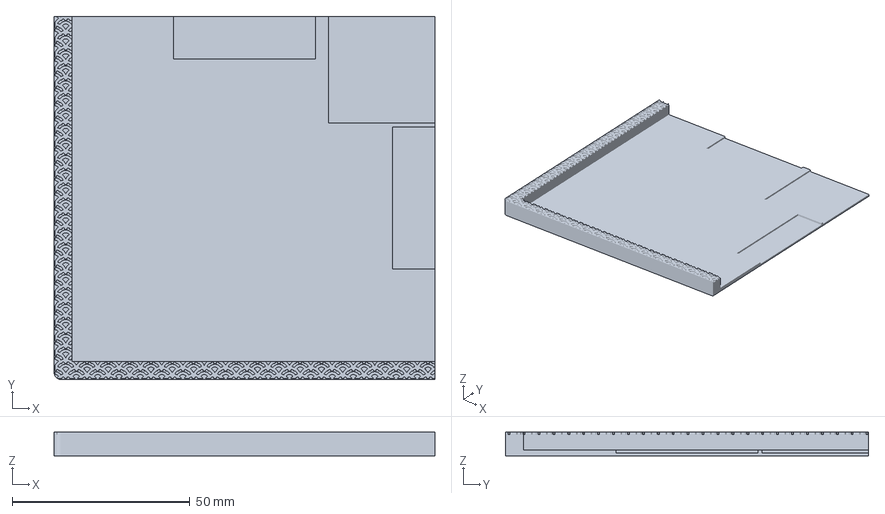
[picture p128: CAD file, 2026-08-07]
out/hokusai_frame_box_a1mini_A.swap.3mf
107.3 x 102.2 x 6.68 mm
