qurihara/ai-fue/out/karuta/sutoku_edge_lower_ink.stl

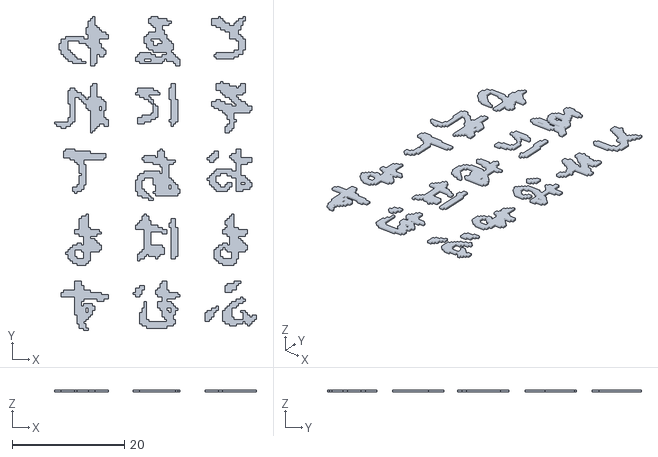
[picture p129: CAD file, 2026-08-13]
out/karuta/sutoku_edge_lower_ink.stl
36.0 x 56.0 x 0.4
