qurihara/ai-fue/out/hokusai_tile7_nobrim_h2d.3mf

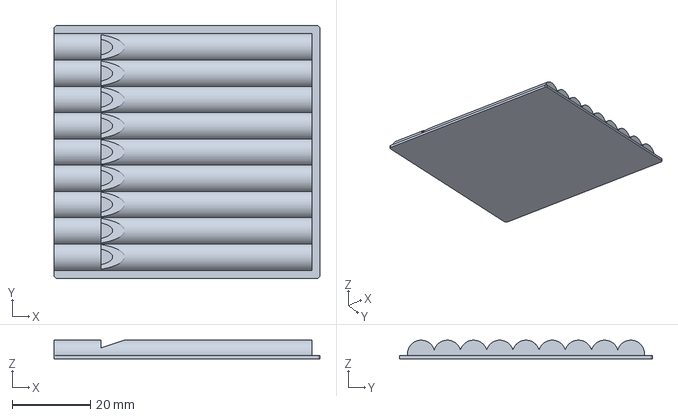
[picture p130: CAD file, 2026-08-07]
out/hokusai_tile7_nobrim_h2d.3mf
68.0 x 64.6 x 4.78 mm
