qurihara/ai-fue/out/karuta/sutoku_edge_thin_upper_ink.stl

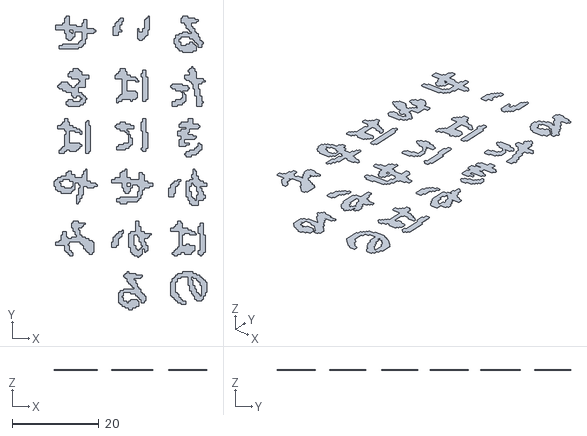
[picture p131: CAD file, 2026-08-13]
out/karuta/sutoku_edge_thin_upper_ink.stl
35.2 x 67.6 x 0.2
