qurihara/ai-fue/out/hokusai_frame_box_plain_stand.stl

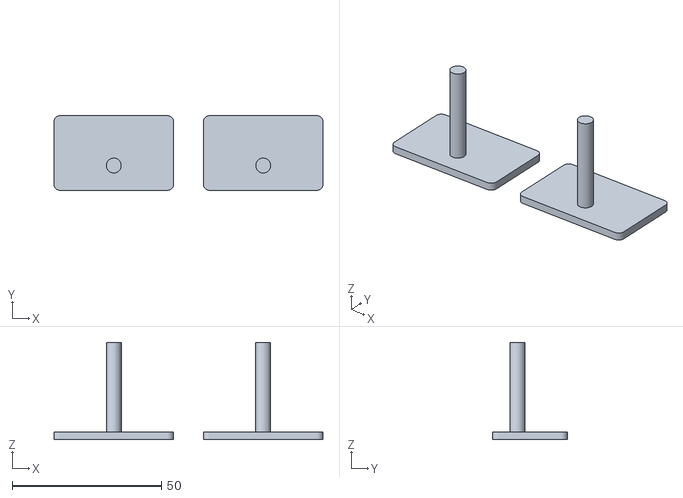
[picture p132: CAD file, 2026-08-07]
out/hokusai_frame_box_plain_stand.stl
90.0 x 25.0 x 32.5
