qurihara/ai-fue/out/karuta/sutoku_edge_upper_ink.stl

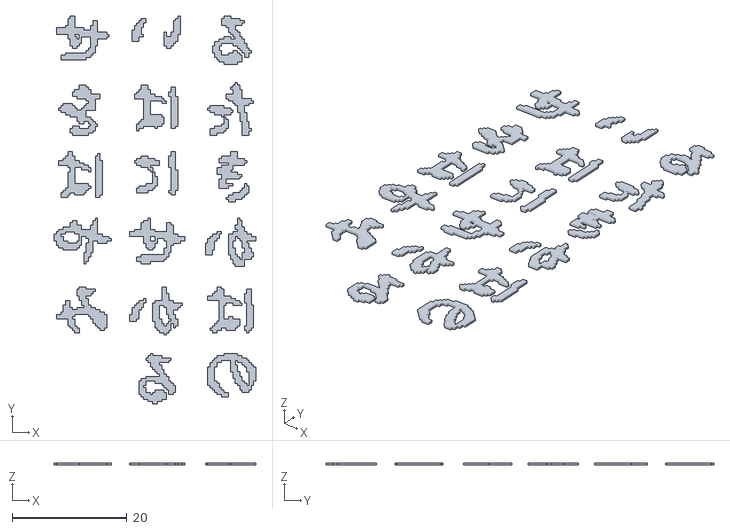
[picture p133: CAD file, 2026-08-13]
out/karuta/sutoku_edge_upper_ink.stl
35.2 x 67.6 x 0.4
