qurihara/ai-fue/out/hokusai_frame_box_a1mini_straps.stl

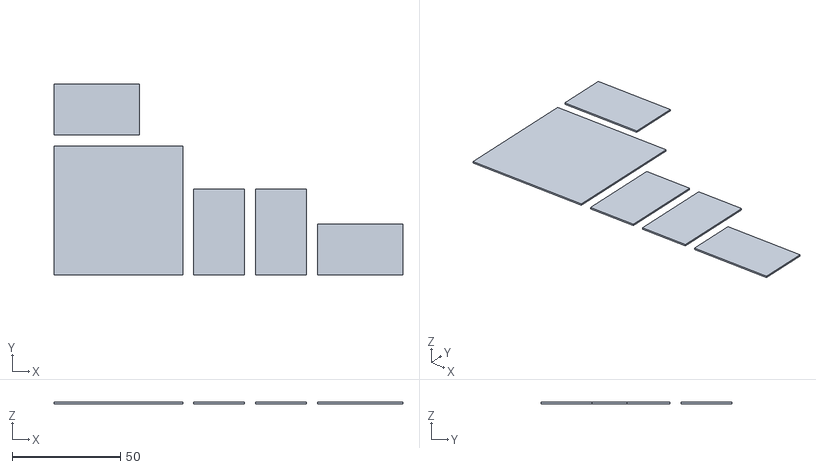
[picture p134: CAD file, 2026-08-07]
out/hokusai_frame_box_a1mini_straps.stl
161.4 x 88.2 x 0.7
