qurihara/ai-fue/out/hokusai_frame_box_plain_stand_h2d.gcode.3mf

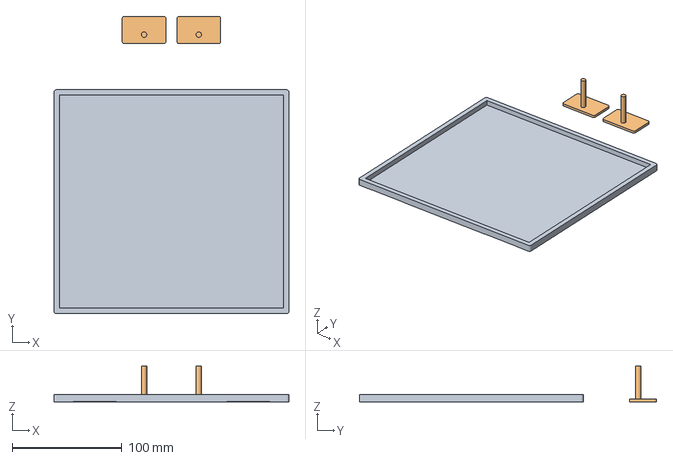
[picture p135: CAD file, 2026-08-07]
out/hokusai_frame_box_plain_stand_h2d.gcode.3mf
214.5 x 271.4 x 32.5 mm
place_frame.stl
place_stand.stl
