qurihara/ai-fue/out/karuta/sutoku_lower_base.stl

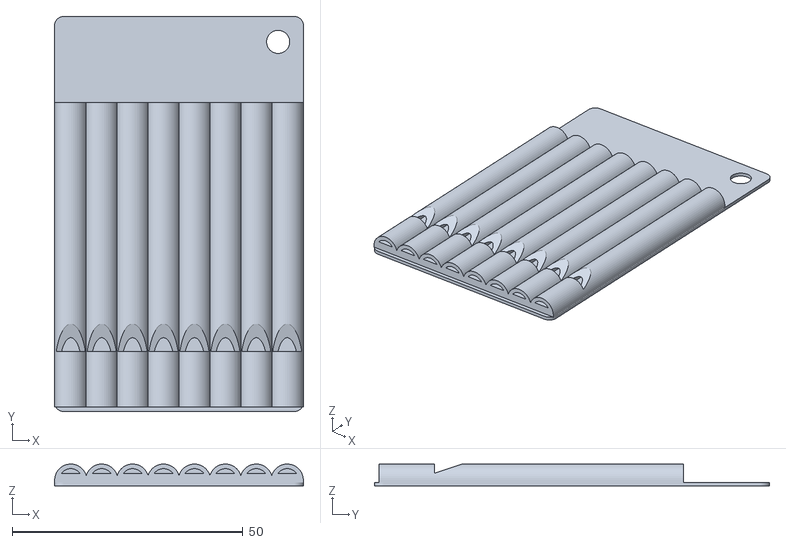
[picture p137: CAD file, 2026-08-12]
out/karuta/sutoku_lower_base.stl
54.0 x 85.6 x 4.75
