qurihara/ai-fue/out/hokusai_frame_box_plain_h2d.gcode.3mf

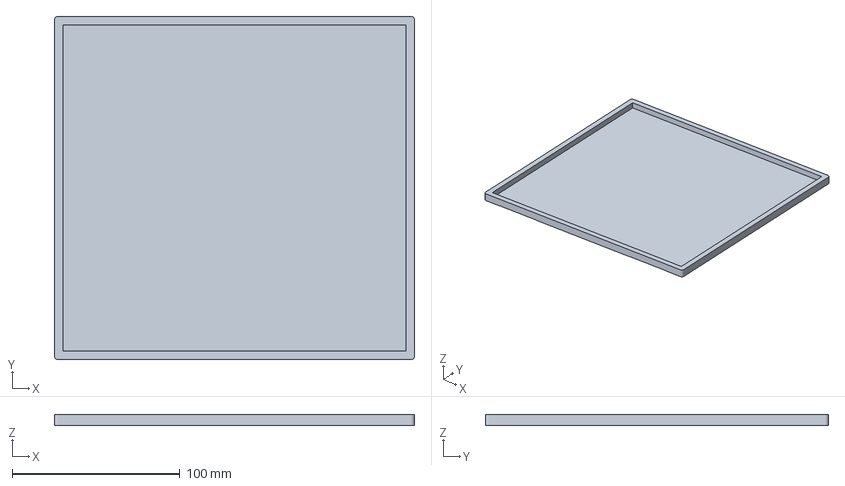
[picture p138: CAD file, 2026-08-07]
out/hokusai_frame_box_plain_h2d.gcode.3mf
214.5 x 204.4 x 6.68 mm
