qurihara/ai-fue/out/karuta/sutoku_lower_ink.stl

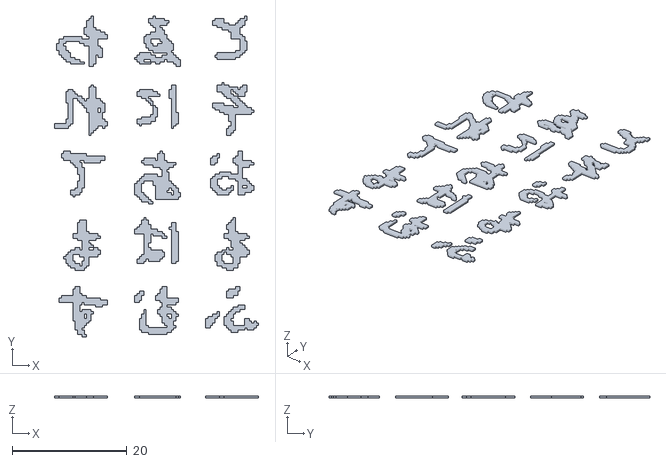
[picture p139: CAD file, 2026-08-12]
out/karuta/sutoku_lower_ink.stl
35.6 x 56.0 x 0.4
