qurihara/ai-fue/out/karuta/izumi_2of2_lower_base.stl

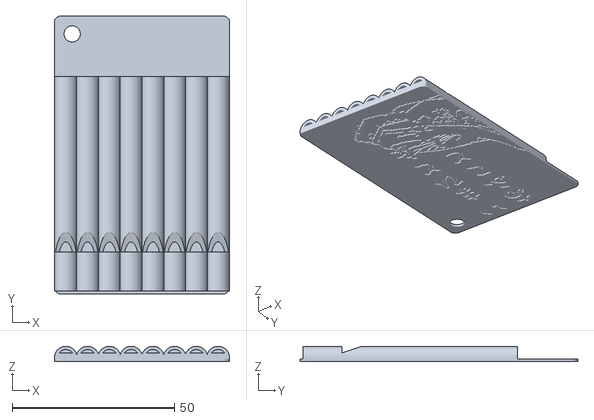
[picture p140: CAD file, 2026-08-12]
out/karuta/izumi_2of2_lower_base.stl
54.0 x 85.6 x 4.75
