qurihara/ai-fue/out/hokusai_tiles2_h2d.gcode.3mf

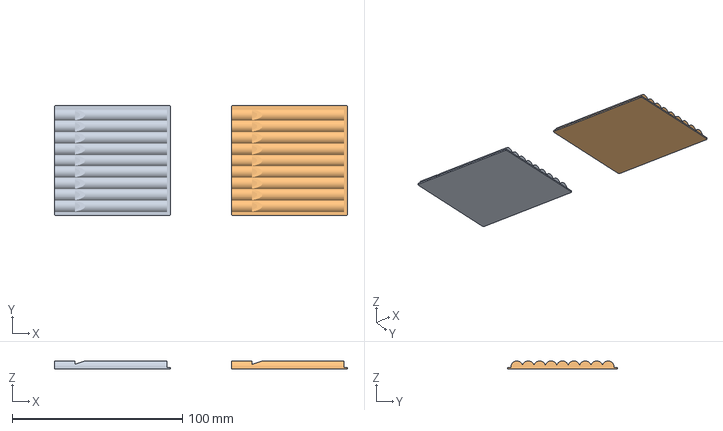
[picture p141: CAD file, 2026-08-06]
out/hokusai_tiles2_h2d.gcode.3mf
172.0 x 64.6 x 4.78 mm
tile_08_r2c1
tile_09_r2c2
