qurihara/ai-fue/out/karuta/sutoku_upper_h2d.3mf

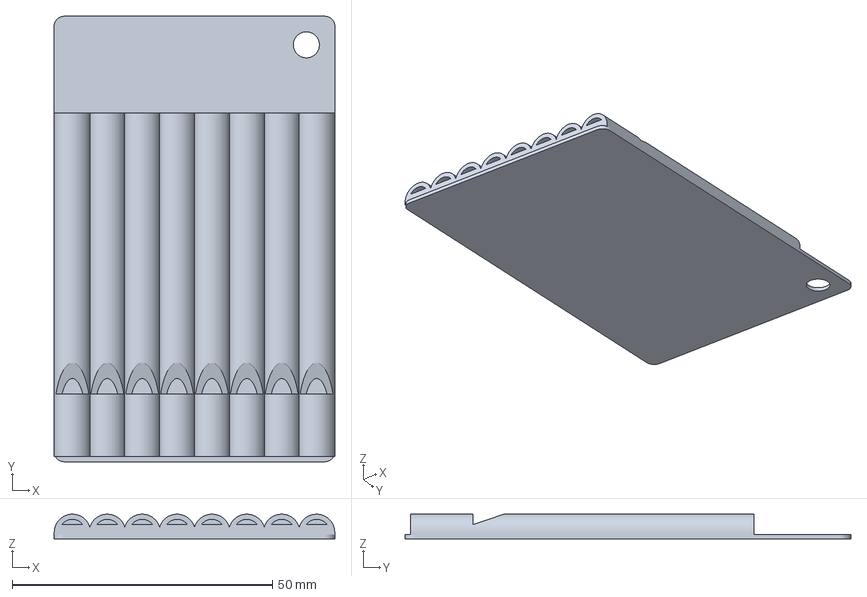
[picture p142: CAD file, 2026-08-12]
out/karuta/sutoku_upper_h2d.3mf
54.0 x 85.6 x 4.75 mm
