qurihara/ai-fue/out/karuta/izumi_2of2_lower_ink.stl

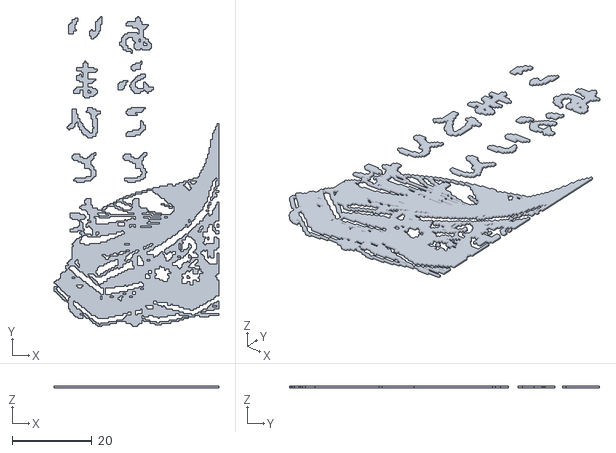
[picture p143: CAD file, 2026-08-12]
out/karuta/izumi_2of2_lower_ink.stl
41.2 x 77.6 x 0.4
