qurihara/ai-fue/out/bookstand_v6_share3.3mf

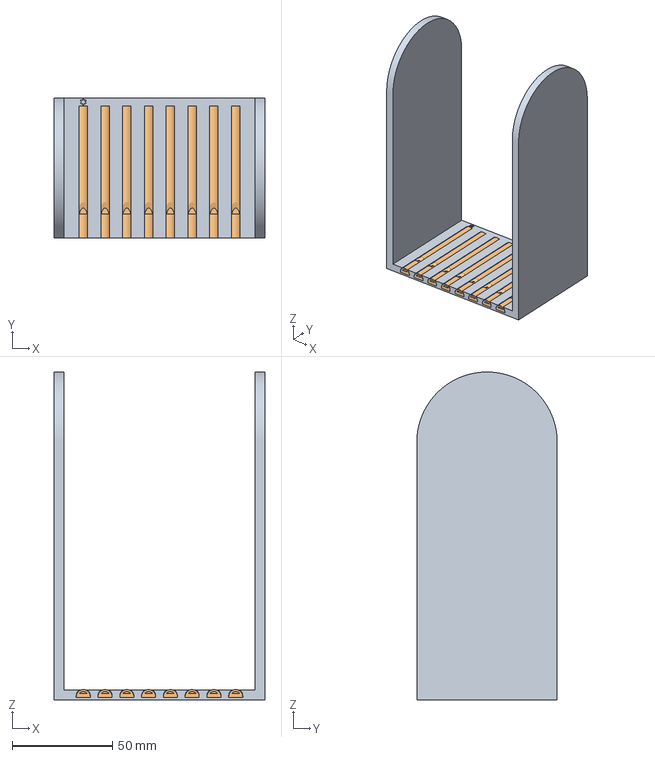
[picture p144: CAD file, 2026-08-05]
out/bookstand_v6_share3.3mf
105.0 x 70.0 x 163.5 mm
bookstand_0.28fast
flutes_0.08careful
