qurihara/ai-fue/out/karuta/sutoku_both_h2d.gcode.3mf

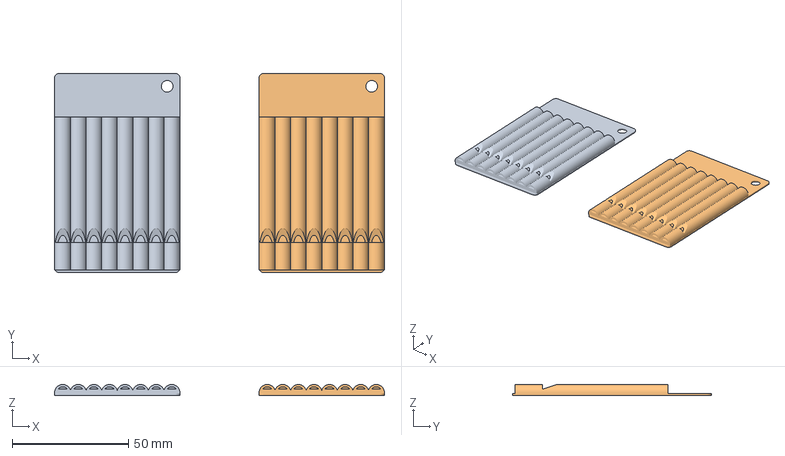
[picture p146: CAD file, 2026-08-12]
out/karuta/sutoku_both_h2d.gcode.3mf
142.0 x 85.6 x 4.75 mm
sutoku_upper
sutoku_lower
