qurihara/ai-fue/out/petg_print_check1.jpg

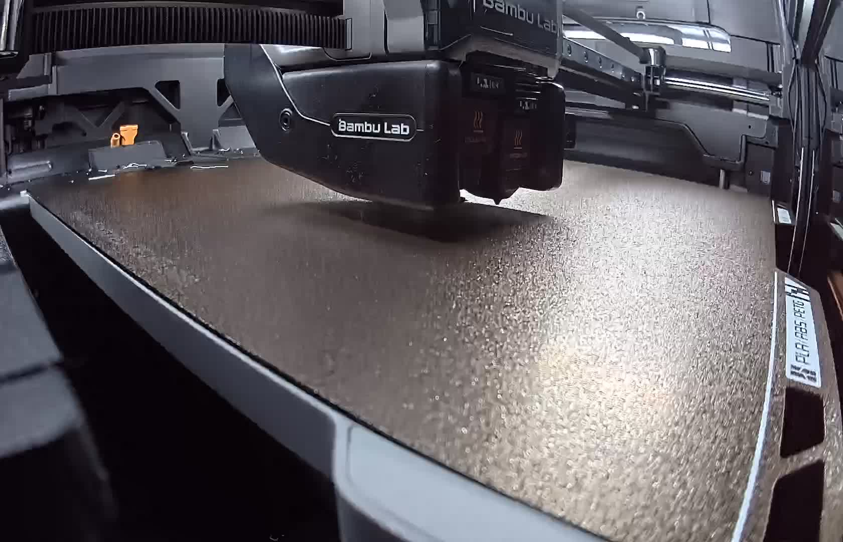
out/petg_print_check1.jpg
