qurihara/ai-fue/out/petg_print_check2.jpg

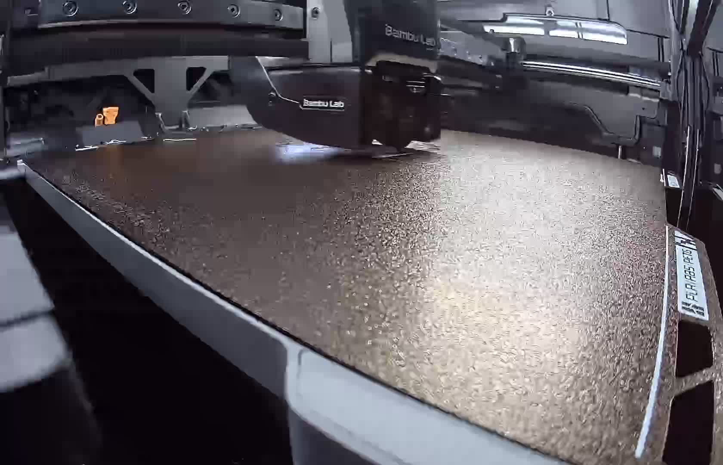
out/petg_print_check2.jpg
