qurihara/ai-fue/out/petg_print_done.jpg

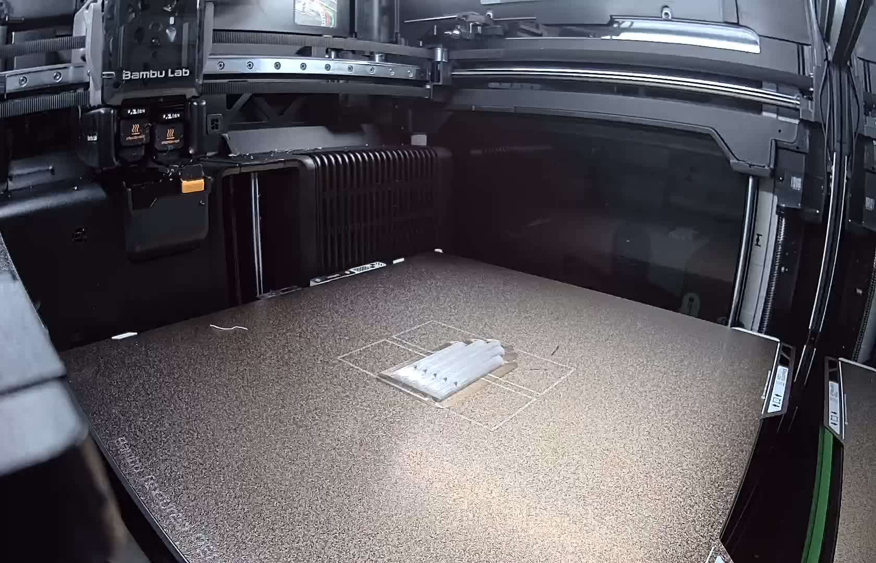
out/petg_print_done.jpg
