qurihara/ai-fue/paper/measurements_2026-07-20.txt

# 暗号笛 実験コーム(cipher_test_plate) 手順3・手順5の実測 2026-07-20

測定者: 栗原さん。測定アプリ: qurihara.github.io/ai-fue (複数ピーク検出)。
印刷物: j012 = cipher_test_plate (A1 mini・黒PLA Basic・積層0.08mm・外壁線幅0.5のcareful)。
広いコーム5本 = F6(1396.9) G6(1568.0) A6(1760.0) C7(2093.0) D7(2349.3)。
詰めたコーム4本 = G#6(1661.2) A6(1760.0) A#6(1864.7) B6(1975.5)。

## 手順3(塞ぎ試験) 生データ

指の太さに比べて笛が細いので、両端の笛の窓は塞げるが、中央の3本は塞げない(栗原さんの報告)。

5本笛 全部鳴らす:
  12:55:33頃 基音: 1559, 2309 (G6-10c, D7-30c)
  基音: 1559, 2320 (G6-10c, D7-22c)
5本笛 最低音F6だけ塞ぐ:
  基音: 1752, 2080 (A6-8c, C7-11c)
  基音: 1746, 2074 (A6-14c, C7-16c)
5本笛 最高音D7だけ塞ぐ:
  基音: 1734, 2092 (A6-26c, C7-1c)
  基音: 1758, 2098 (A6-2c, C7+4c)

4本笛(詰め) 全部鳴らす:
  基音: 1975, 3475 (B6±0c と 3475Hz=おそらくA6系の2倍音をアプリが基音と誤認・帯域外)
  基音: 1770 (A6+10c)
4本笛 最低音G#6だけ塞ぐ: 1764, 1758 (A6のみ)
4本笛 最高音B6だけ塞ぐ: 1764, 1764 (A6のみ)

## 手順5(吹圧スイープ) 生データと解析

広いコーム5本を1本ずつ、弱・中・最強で各2回。数値は基音Hz。

笛1 F6: 弱 1406,1406 / 中 1418,1424 / 最強 1424,1424
笛2 G6: 弱 1564,1564 / 中 1582,1588 / 最強 1594,1588
笛3 A6: 弱 1775,1775 / 中 1793,1793 / 最強 1840,1816
笛4 C7: 弱 2104,2104 / 中 2127,2115 / 最強 2145,2127
笛5 D7: 弱 2355,2355 / 中 2379,2379 / 最強 2408,2432

平均律との差(セント・2回平均):
  笛1 F6: 弱+11 中+30 最強+33  全幅22c
  笛2 G6: 弱-4  中+19 最強+25  全幅30c
  笛3 A6: 弱+15 中+32 最強+66  全幅51c
  笛4 C7: 弱+9  中+23 最強+35  全幅26c
  笛5 D7: 弱+4  中+22 最強+51  全幅47c

同一強さでの2回の再現性: ほぼ0〜7c。最強のみ A6で23c、D7で17c に広がる。

## 結論

1. モードジャンプなし。最強でも基音はオクターブ/12度へ飛ばず連続上昇のみ。単一発振状態。
2. 吹圧の全幅ベンドは22〜51c。共通成分の平均約35c、笛ごとの偏り±16c。
   基準笛との周波数比で読めば残差±16c程度=半音スロット(判定半径50c)に余裕で収まる。
   1オクターブ12スロット(1本3.58bit)で容量計算を更新する。61bitなら18本、誤り訂正込みで20本規模。
3. 倍音は最低の2倍音(F6笛2794Hz)でも帯域上端E7(2637Hz)より上=帯域フィルタで構造排除できる。
   3475Hzの基音誤認例があり、復号器の帯域フィルタは必須。
4. 手順3: 同時吹きの独立性は不成立。1本塞ぐと空気が再分配され他の鳴る組まで変わる
   (全吹きでG6+D7、F6塞ぎでA6+C7、D7塞ぎでもA6+C7)。同時に鳴る組は日によっても変わる
   (昨日はF6+A6+C7)。原因は注入同期より手前の、口の覆いと流量配分の空気力学的結合が濃厚。
5. 設計帰結: 順番読み(1本ずつ)が本線として確定。和音読みは担いなしの追加の技へ降格。
   詰めたコーム中央A6のテープ塞ぎ診断(引き込みか音量マスクかの切り分け)が残タスク。

## 較正に関する注意

昨日の単独確認(±5c)は弱めの息、今日の「中」は+20〜30cに乗る。較正をどの息の強さに
合わせるかという問題は、基準笛との比で読む設計でそのまま解消する。
