qurihara/ai-fue/out/tiles_test2/part_r0c0.png

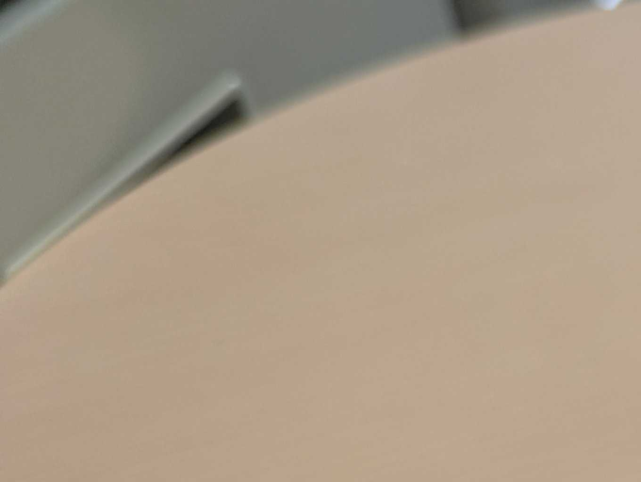
out/tiles_test2/part_r0c0.png
