qurihara/ai-fue/out/tiles_test2/part_r0c1.png

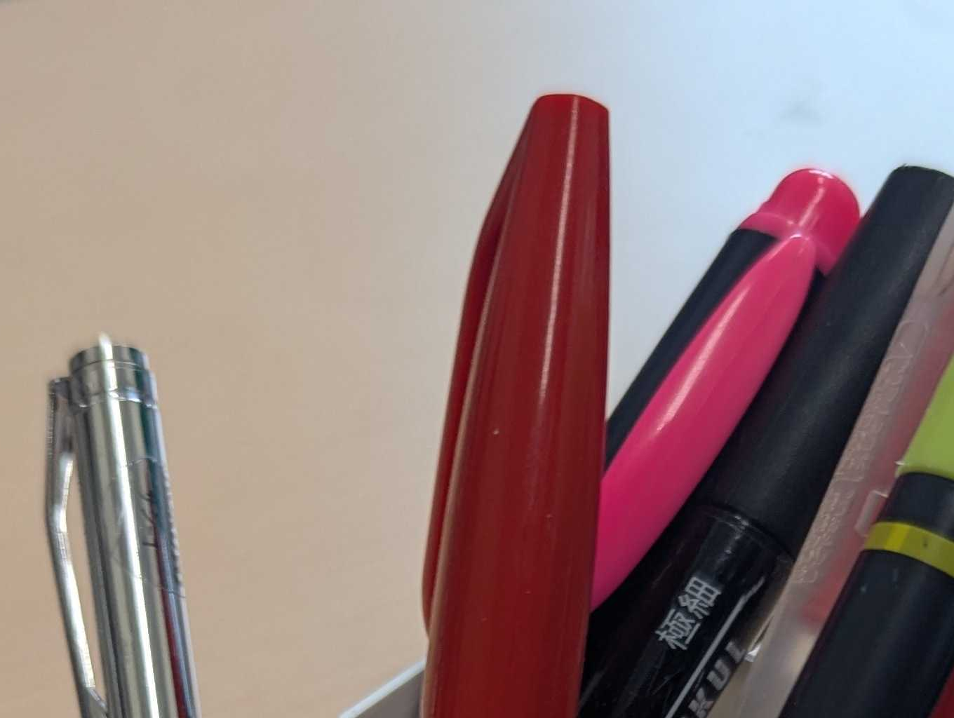
out/tiles_test2/part_r0c1.png
