qurihara/ai-fue/out/tiles_test2/part_r0c2.png

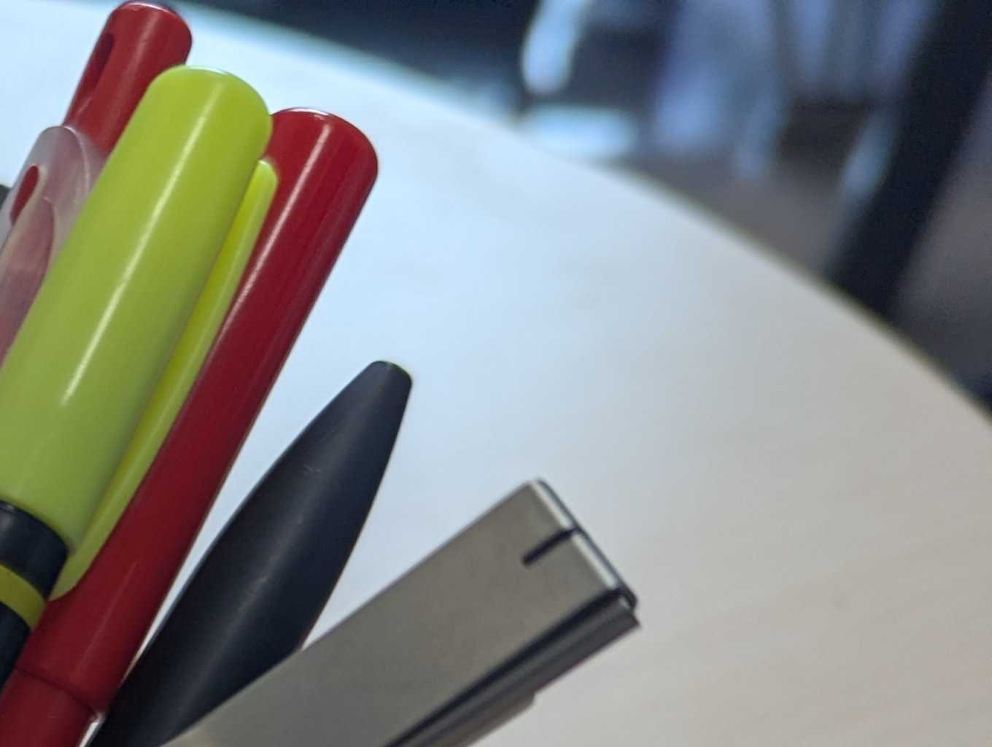
out/tiles_test2/part_r0c2.png
