qurihara/ai-fue/out/tiles_test2/part_r2c1.png

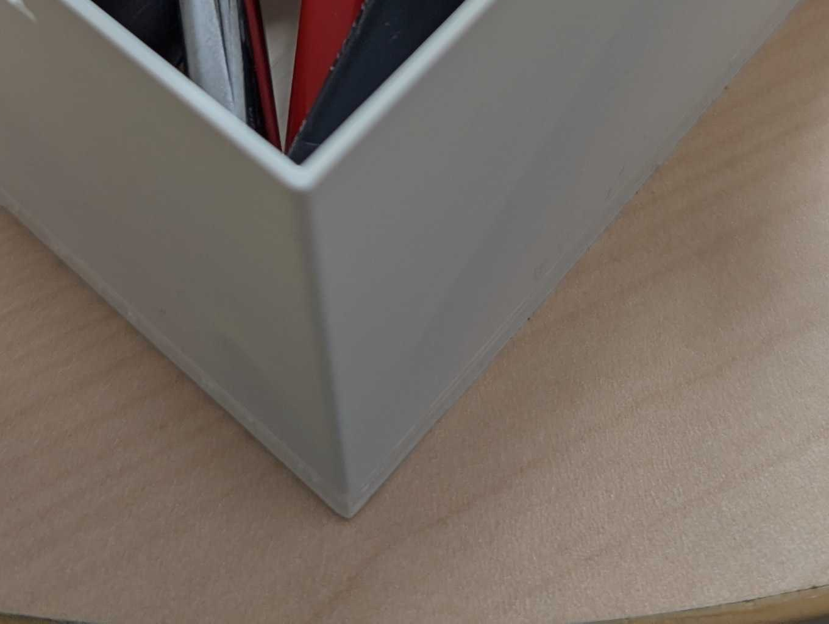
out/tiles_test2/part_r2c1.png
