qurihara/ai-fue/out/tiles_test2/tile_01_r0c0_preview.png

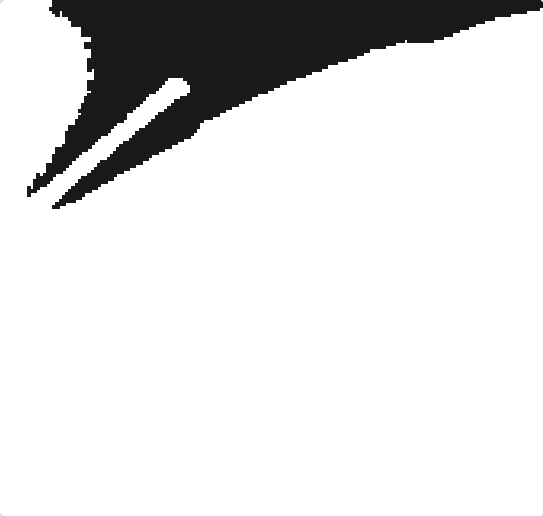
out/tiles_test2/tile_01_r0c0_preview.png
