qurihara/ai-fue/out/tiles_test2/tile_02_r0c1_preview.png

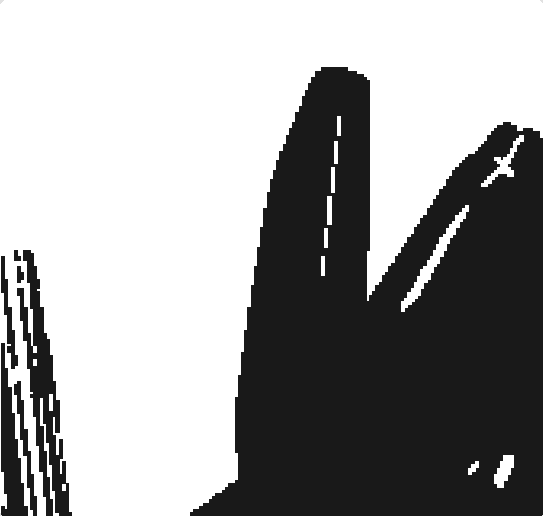
out/tiles_test2/tile_02_r0c1_preview.png
